intechstudio/grid/Preview/Electrical/FP-BU16-3D_blender_top.png

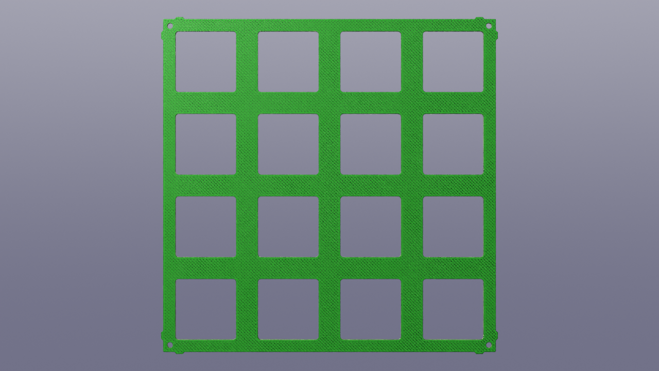
Preview/Electrical/FP-BU16-3D_blender_top.png
