intechstudio/grid/Preview/Electrical/FP-BU16-MIDIGRADE-3D_bottom.png

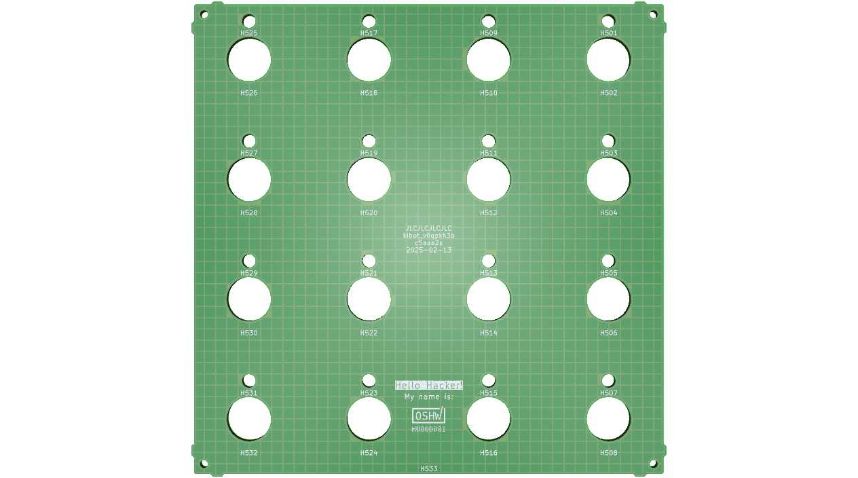
Preview/Electrical/FP-BU16-MIDIGRADE-3D_bottom.png
