intechstudio/grid/Preview/Electrical/FP-BU16-MIDIGRADE-3D_top.png

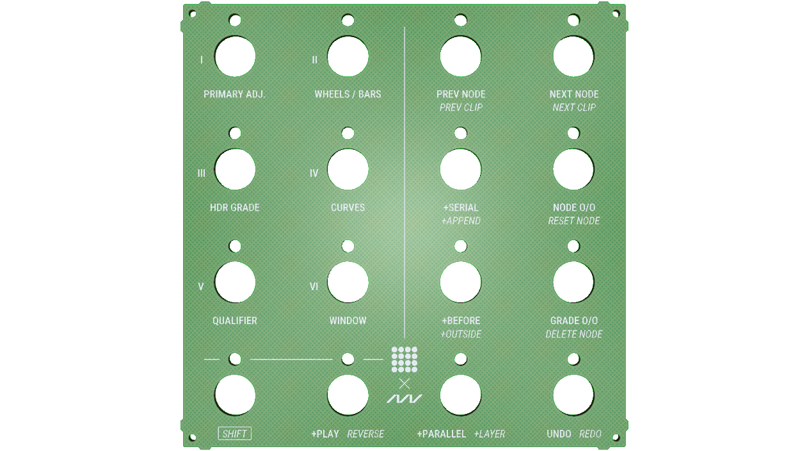
Preview/Electrical/FP-BU16-MIDIGRADE-3D_top.png
