intechstudio/grid/Preview/Electrical/FP-EN16-MIDIGRADE-3D_blender_top.png

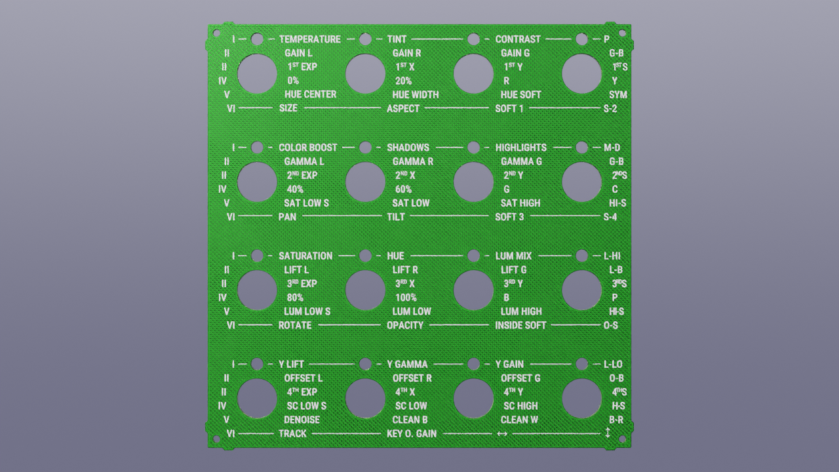
Preview/Electrical/FP-EN16-MIDIGRADE-3D_blender_top.png
