intechstudio/grid/Preview/Electrical/FP-TEK2-3D_bottom.png

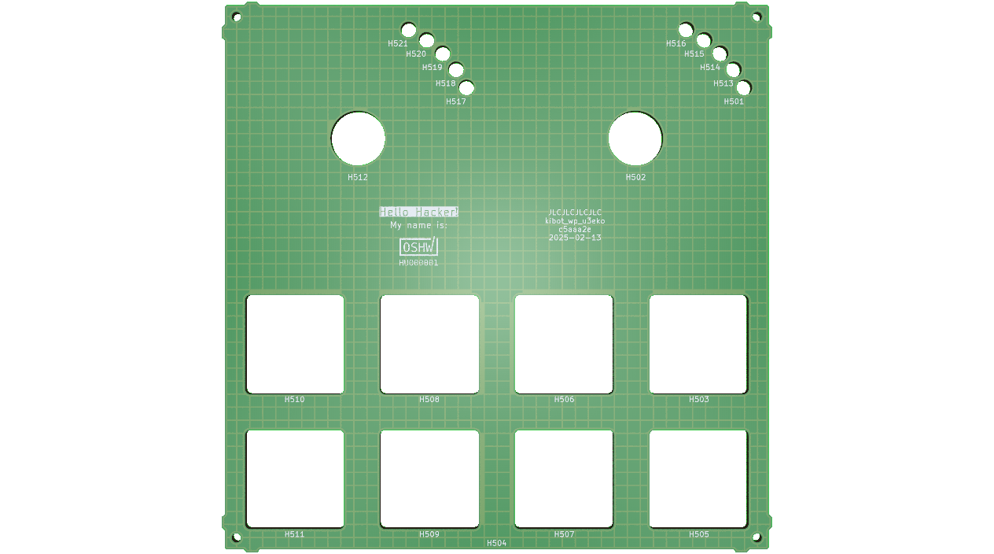
Preview/Electrical/FP-TEK2-3D_bottom.png
