intechstudio/grid/Preview/Electrical/FP-VSN1-3D_bottom.png

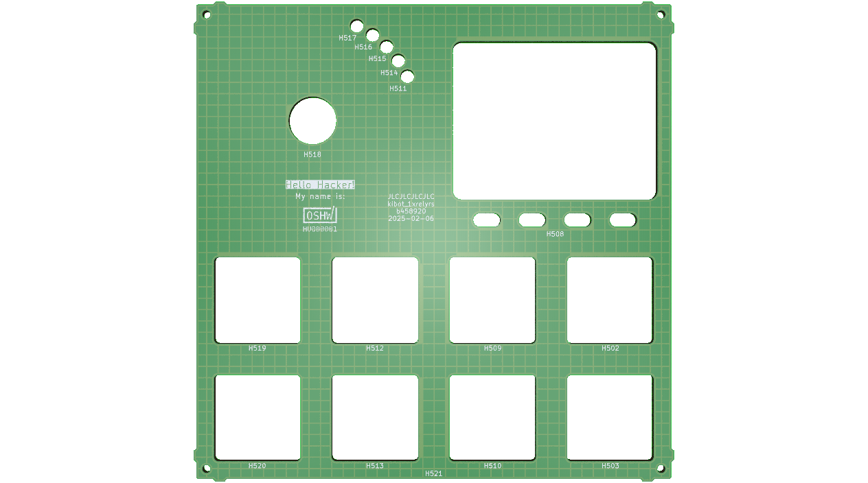
Preview/Electrical/FP-VSN1-3D_bottom.png
