intechstudio/grid/Preview/Electrical/FP-VSN1-3D_top.png

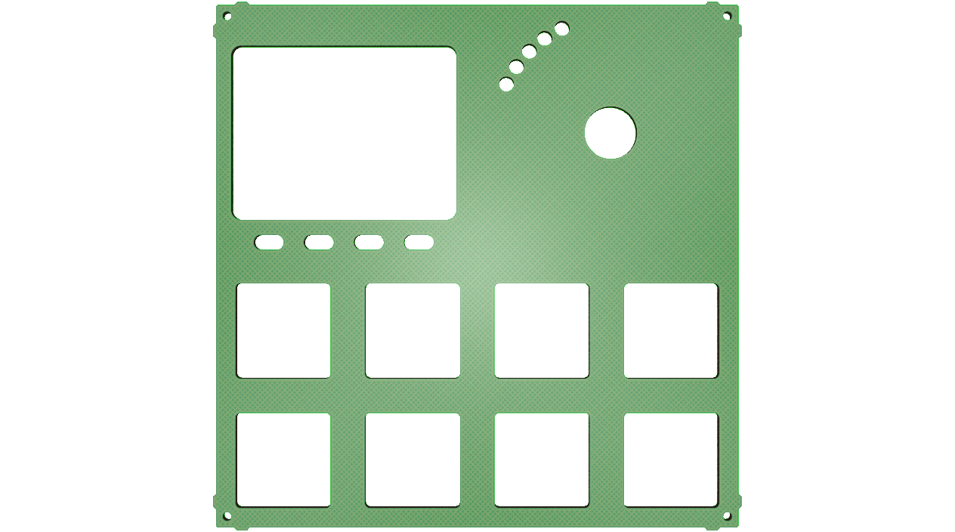
Preview/Electrical/FP-VSN1-3D_top.png
