intechstudio/grid/Preview/Electrical/FP-VSN1-R-3D_blender_top.png

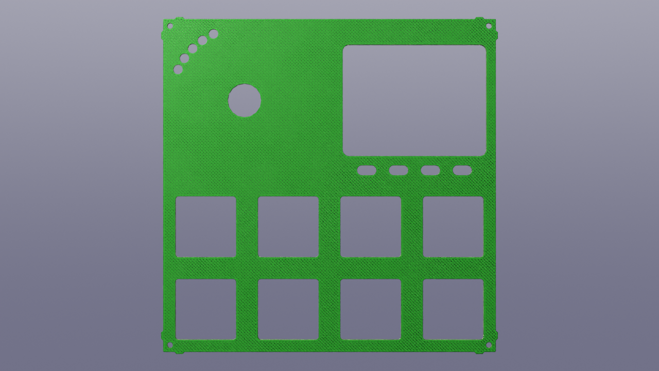
Preview/Electrical/FP-VSN1-R-3D_blender_top.png
