intechstudio/grid/Preview/Electrical/FP-VSN2-3D_bottom.png

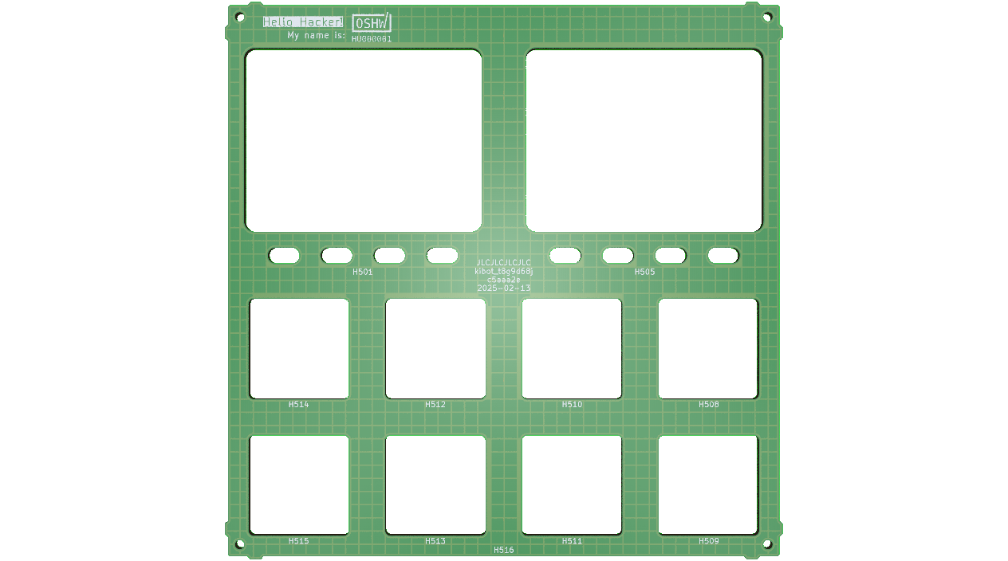
Preview/Electrical/FP-VSN2-3D_bottom.png
