intechstudio/grid/Preview/Electrical/PCBA-BU16-PLATE-3D_blender_top.png

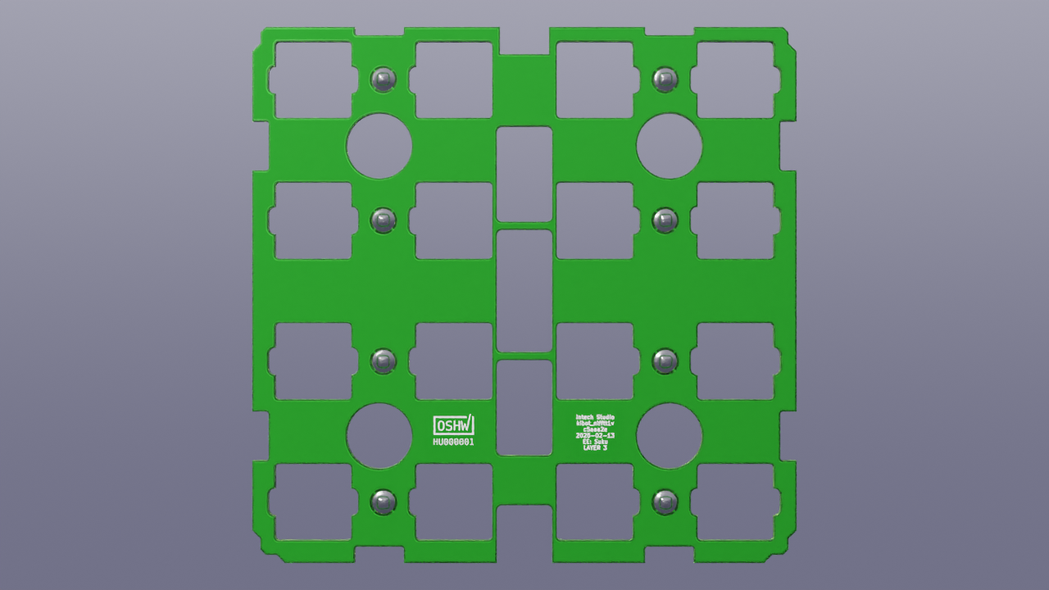
Preview/Electrical/PCBA-BU16-PLATE-3D_blender_top.png
