intechstudio/grid/Preview/Electrical/PCBA-BU16-PLATE-3D_bottom.png

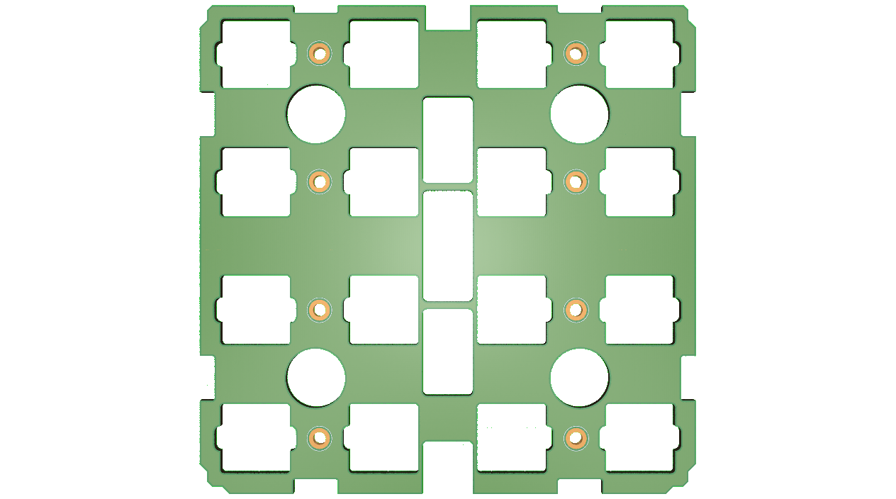
Preview/Electrical/PCBA-BU16-PLATE-3D_bottom.png
