intechstudio/grid/Preview/Electrical/PCBA-BU16-SPACER-3D_blender_top.png

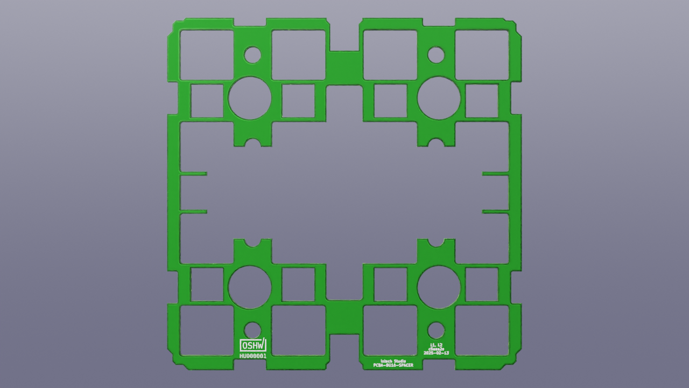
Preview/Electrical/PCBA-BU16-SPACER-3D_blender_top.png
