intechstudio/grid/Preview/Electrical/PCBA-EF44-3D_blender_top.png

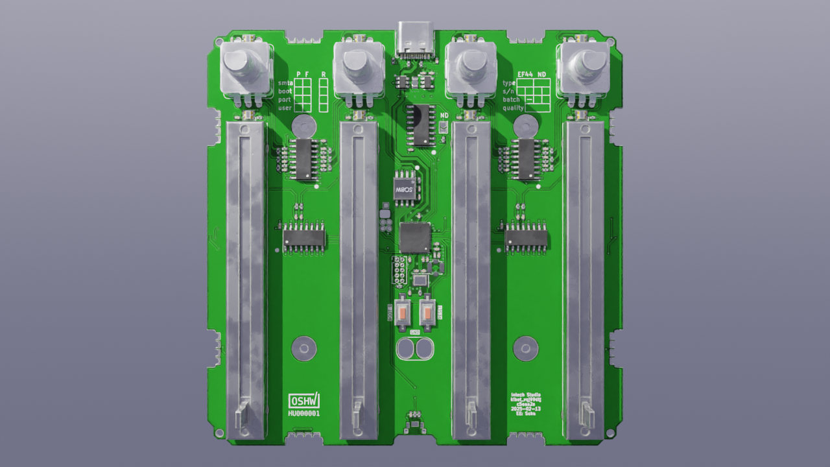
Preview/Electrical/PCBA-EF44-3D_blender_top.png
