intechstudio/grid/Preview/Electrical/PCBA-EF44-FRONTPANEL-3D_bottom.png

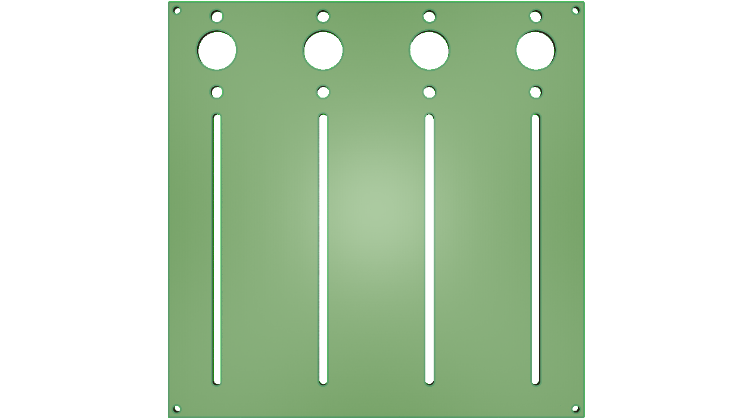
Preview/Electrical/PCBA-EF44-FRONTPANEL-3D_bottom.png
