intechstudio/grid/Preview/Electrical/PCBA-EN16-3D_blender_top.png

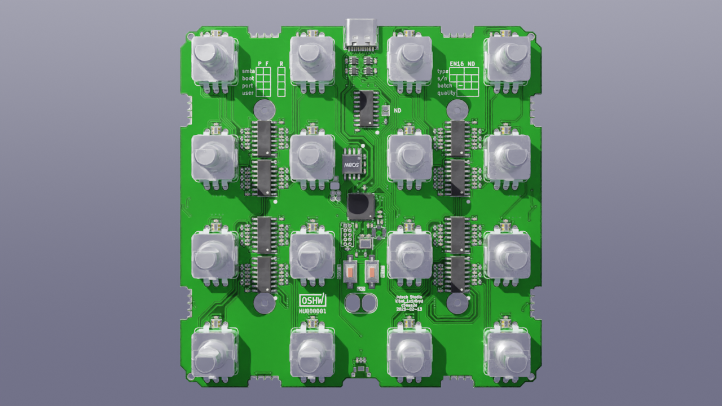
Preview/Electrical/PCBA-EN16-3D_blender_top.png
