intechstudio/grid/Preview/Electrical/PCBA-INTERFACE-3D_blender_top.png

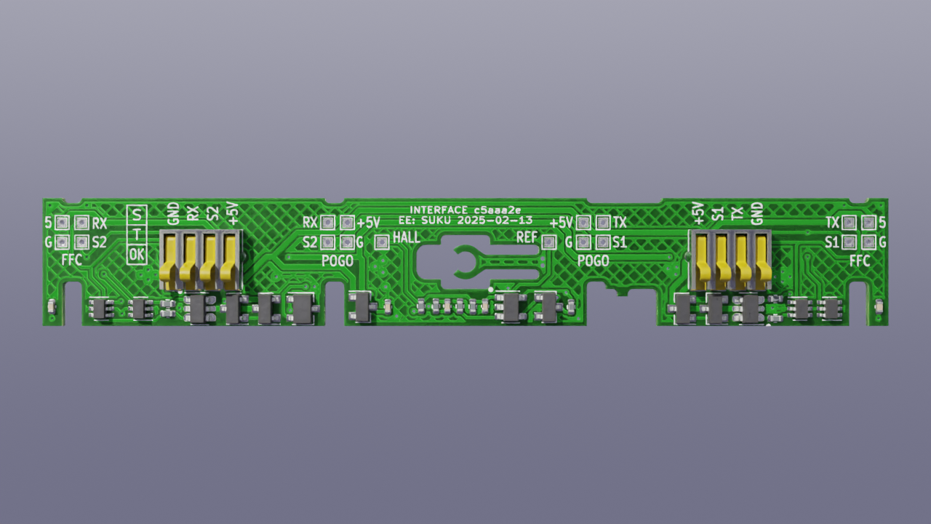
Preview/Electrical/PCBA-INTERFACE-3D_blender_top.png
