intechstudio/grid/Preview/Electrical/PCBA-PBF4-FRONTPANEL-3D_bottom.png

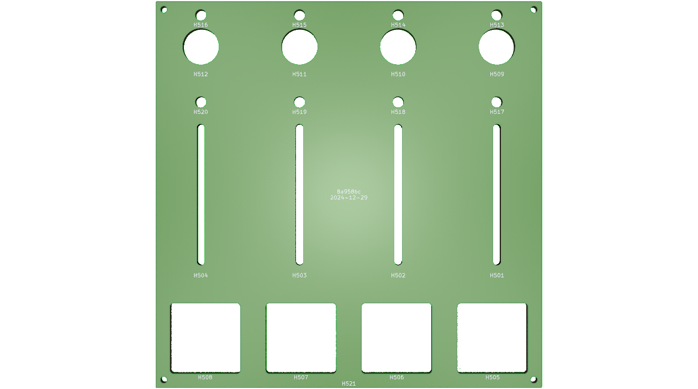
Preview/Electrical/PCBA-PBF4-FRONTPANEL-3D_bottom.png
