intechstudio/grid/Preview/Electrical/PCBA-PBF4-PLATE-3D_blender_top.png

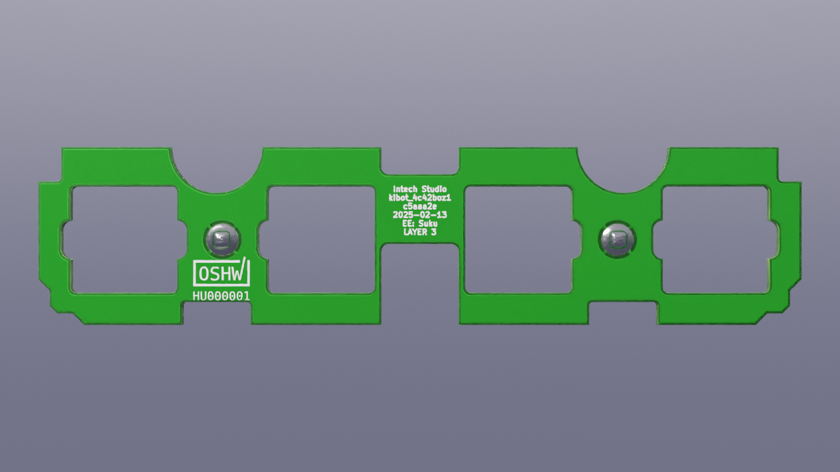
Preview/Electrical/PCBA-PBF4-PLATE-3D_blender_top.png
