intechstudio/grid/Preview/Electrical/PCBA-PBF4-PLATE-3D_bottom.png

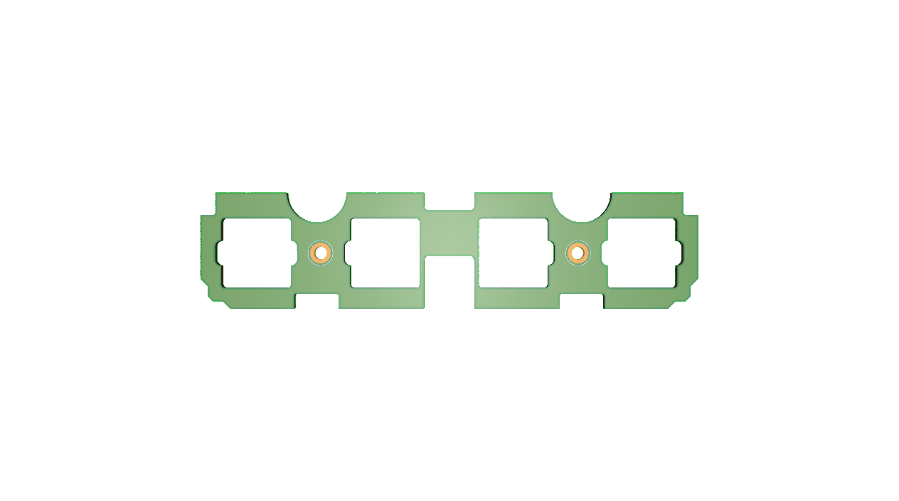
Preview/Electrical/PCBA-PBF4-PLATE-3D_bottom.png
