intechstudio/grid/Preview/Electrical/PCBA-PBF4-SPACER-3D_blender_top.png

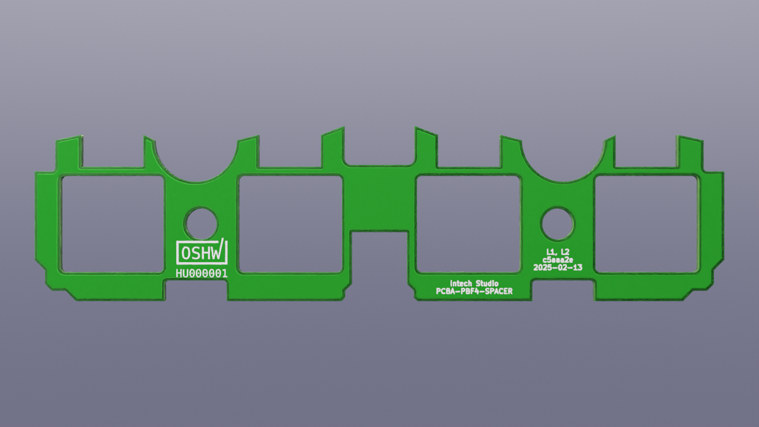
Preview/Electrical/PCBA-PBF4-SPACER-3D_blender_top.png
