intechstudio/grid/Preview/Electrical/PCBA-PBF4-SPACER-3D_bottom.png

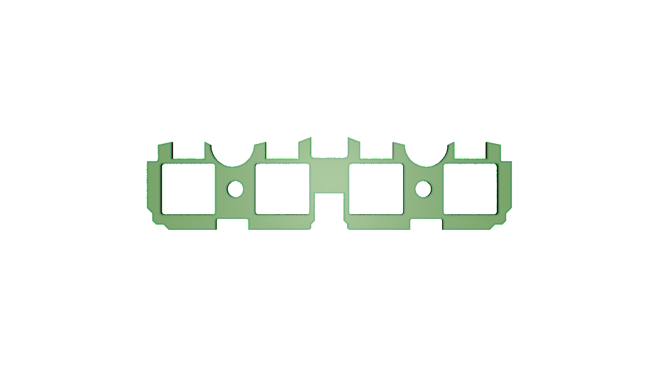
Preview/Electrical/PCBA-PBF4-SPACER-3D_bottom.png
