intechstudio/grid/Preview/Electrical/PCBA-PO16-3D_blender_top.png

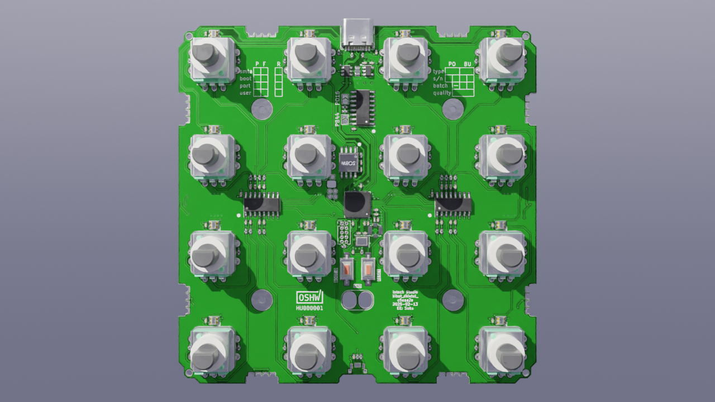
Preview/Electrical/PCBA-PO16-3D_blender_top.png
