intechstudio/grid/Preview/Electrical/PCBA-TEK2-3D_blender_top.png

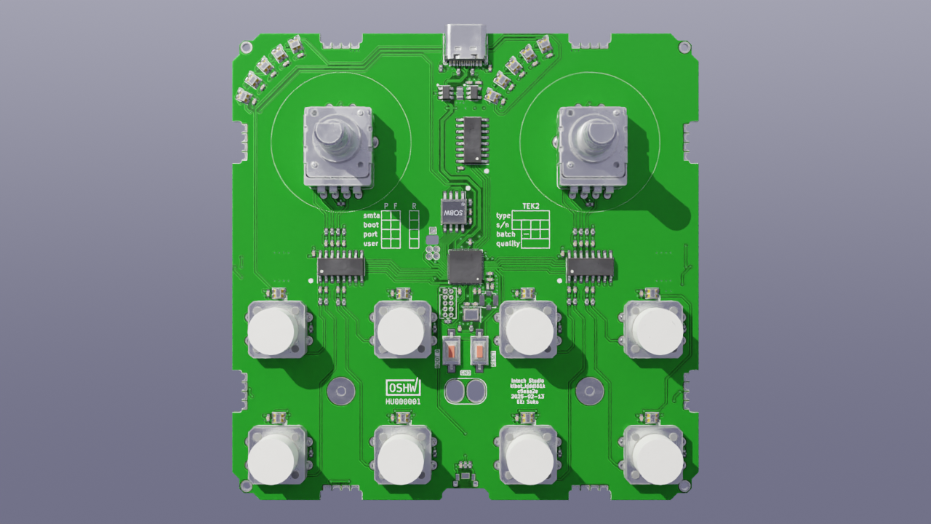
Preview/Electrical/PCBA-TEK2-3D_blender_top.png
