intechstudio/grid/Preview/Electrical/PCBA-VSN2-FRONTPANEL-3D_blender_top.png

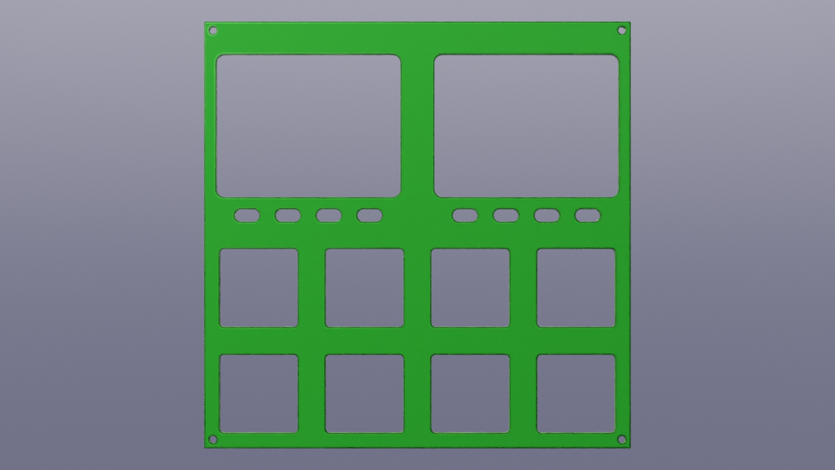
Preview/Electrical/PCBA-VSN2-FRONTPANEL-3D_blender_top.png
