intechstudio/grid/Preview/Electrical/PCBA-VSNX-3D_bottom.png

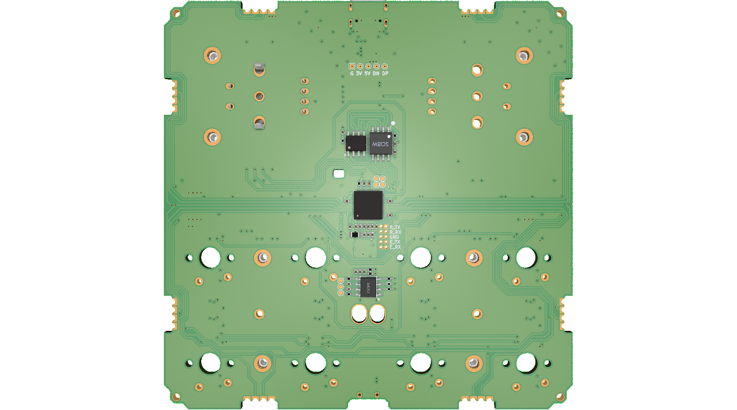
Preview/Electrical/PCBA-VSNX-3D_bottom.png
