intechstudio/grid/Preview/Electrical/PCBA-VSNX-BTNGROUP-3D_blender_top.png

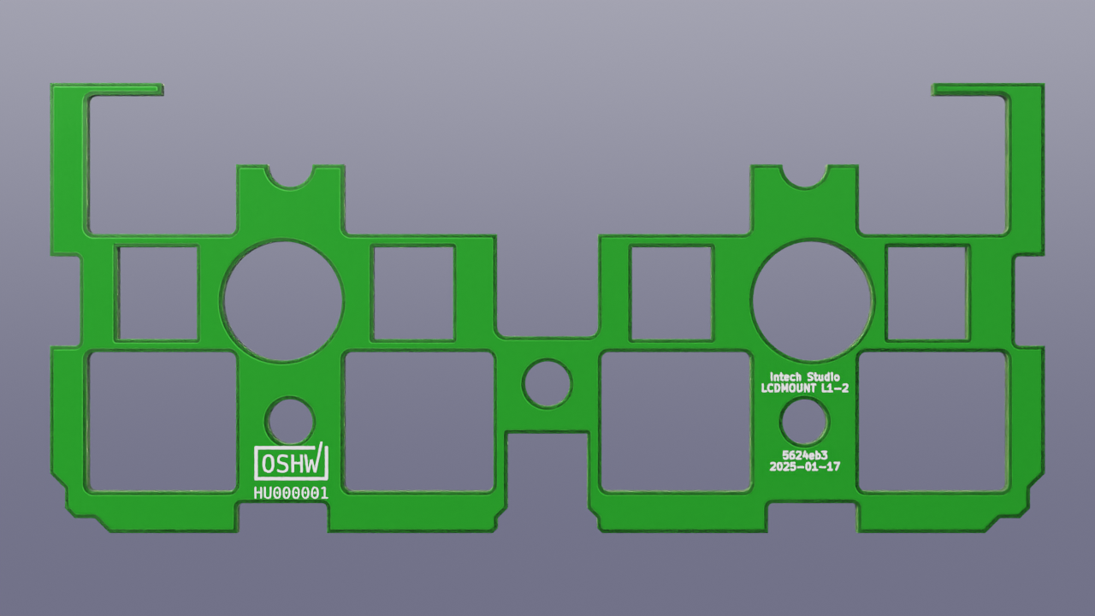
Preview/Electrical/PCBA-VSNX-BTNGROUP-3D_blender_top.png
