intechstudio/grid/Preview/Electrical/PCBA-VSNX-BTNGROUP-3D_bottom.png

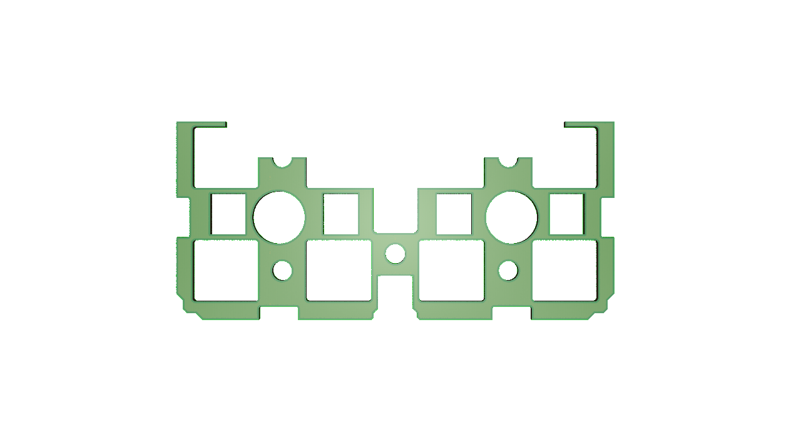
Preview/Electrical/PCBA-VSNX-BTNGROUP-3D_bottom.png
