intechstudio/grid/Preview/Electrical/PCBA-VSNX-LCDMOUNT-3D_blender_top.png

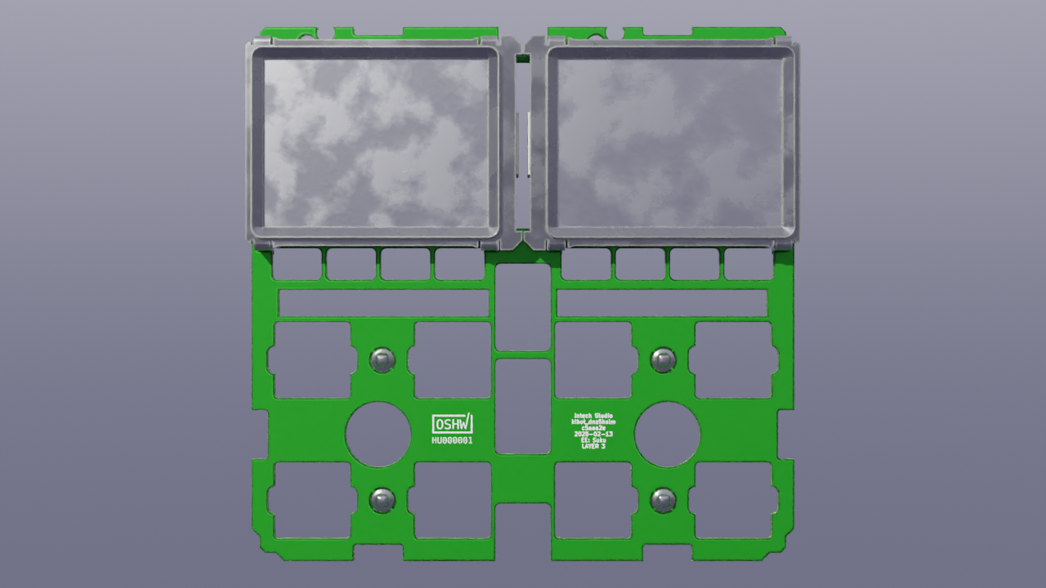
Preview/Electrical/PCBA-VSNX-LCDMOUNT-3D_blender_top.png
