intechstudio/grid/Preview/Electrical/PCBA-VSNX-LCDMOUNT-3D_bottom.png

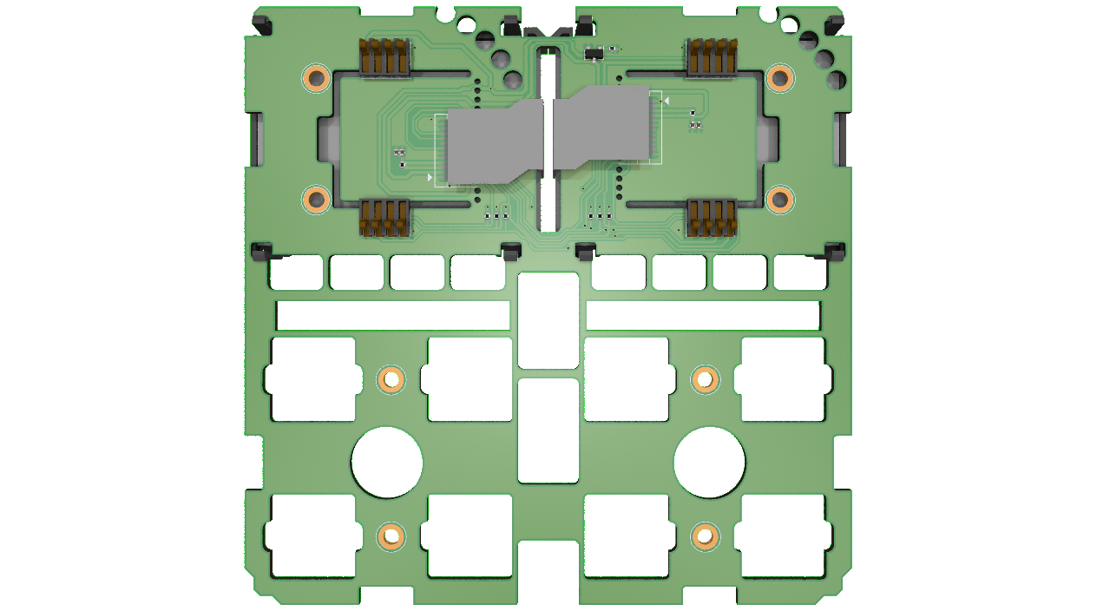
Preview/Electrical/PCBA-VSNX-LCDMOUNT-3D_bottom.png
