intechstudio/grid/Preview/Electrical/PCBA-VSNX-LCDMOUNT-3D_top.png

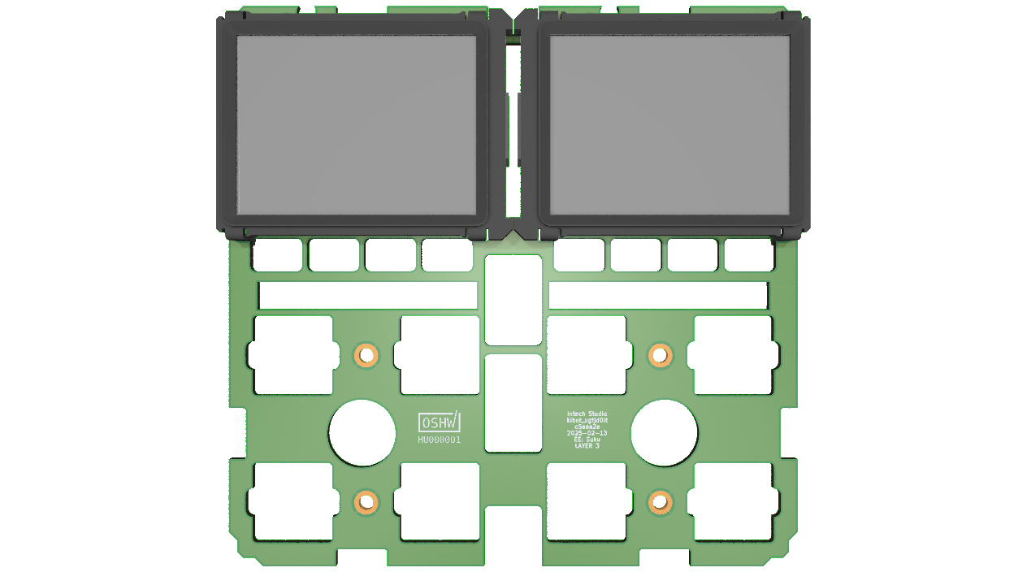
Preview/Electrical/PCBA-VSNX-LCDMOUNT-3D_top.png
