intechstudio/grid/Preview/Electrical/PCBA-VSNX-SPACER-3D_blender_top.png

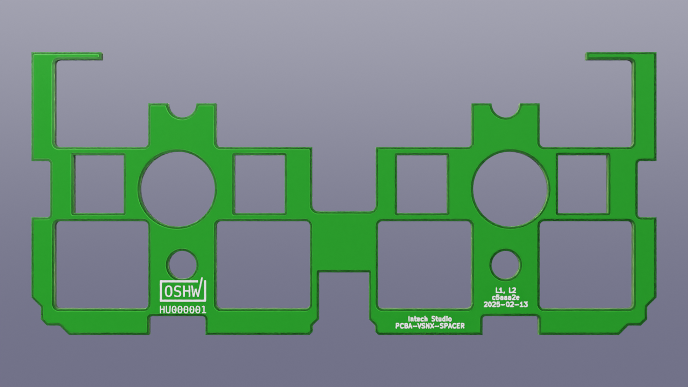
Preview/Electrical/PCBA-VSNX-SPACER-3D_blender_top.png
