intechstudio/grid/Preview/Electrical/PCBA-XX16-FRONTPANEL-3D_top.png

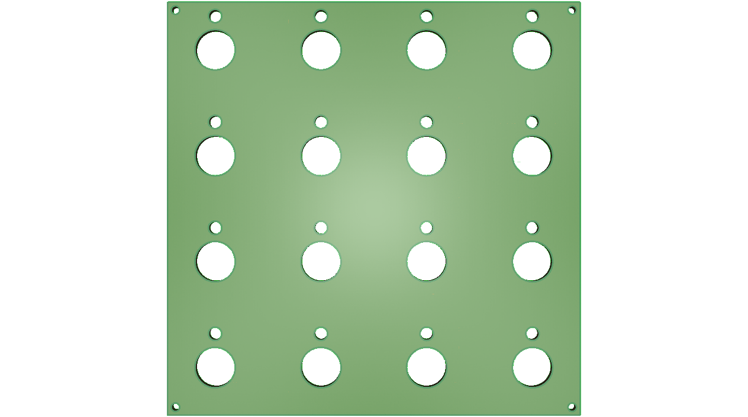
Preview/Electrical/PCBA-XX16-FRONTPANEL-3D_top.png
