intechstudio/grid/Preview/Mechanical/INSERT_TEK2.png

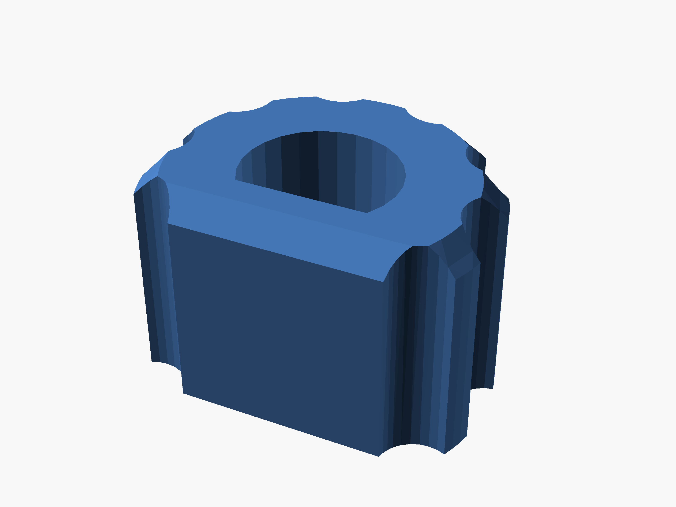
Preview/Mechanical/INSERT_TEK2.png
