intechstudio/grid/Preview/Mechanical/Part.png

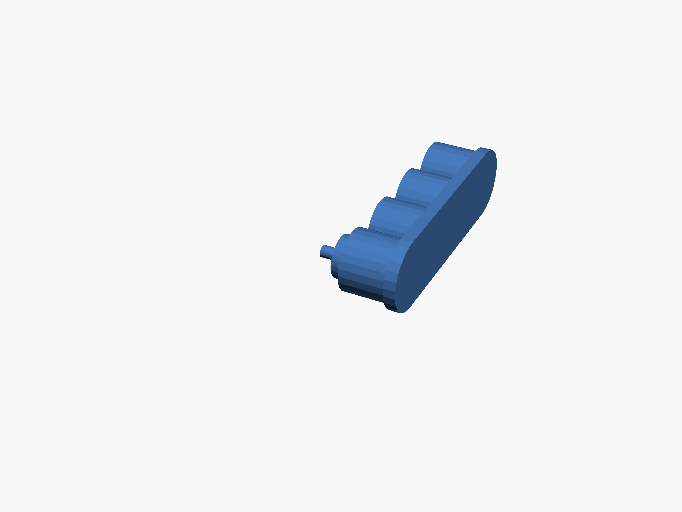
Preview/Mechanical/Part.png
