intechstudio/grid/Preview/Mechanical/Part_reverse.png

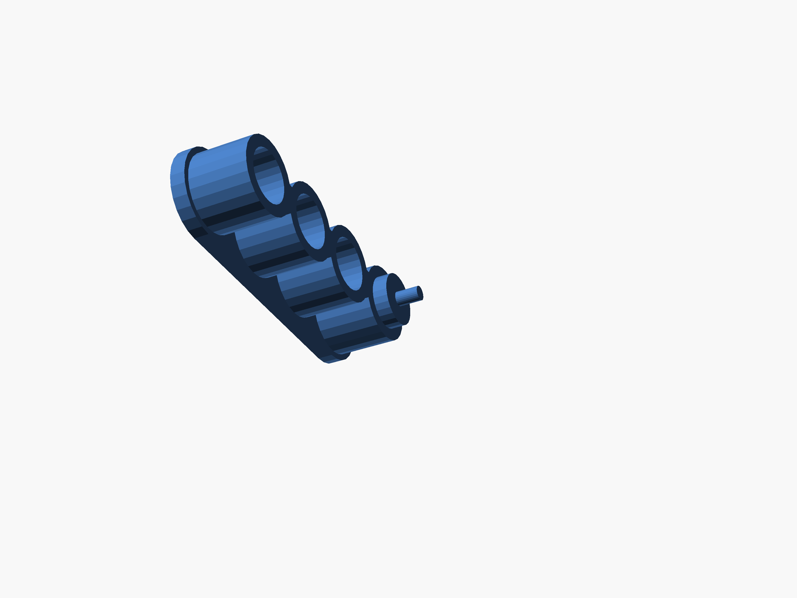
Preview/Mechanical/Part_reverse.png
