intechstudio/grid/Preview/Mechanical/PCBA-CONN-POGO.png

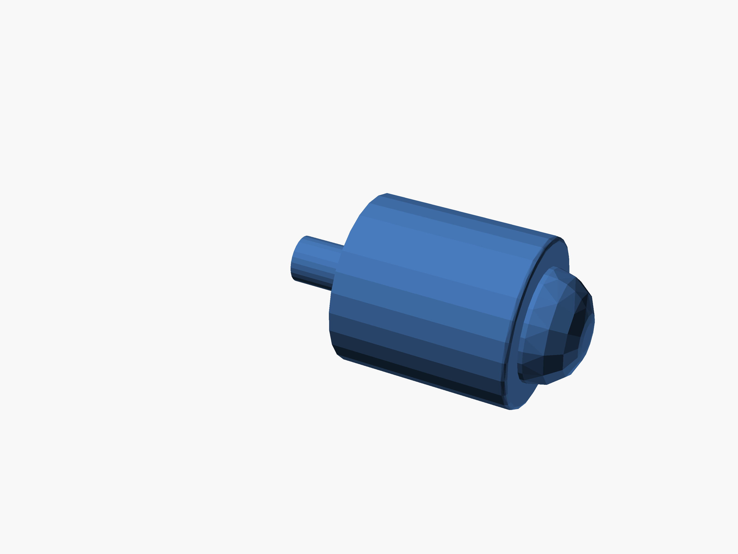
Preview/Mechanical/PCBA-CONN-POGO.png
