intechstudio/grid/Preview/Mechanical/PCBA-POT_reverse.png

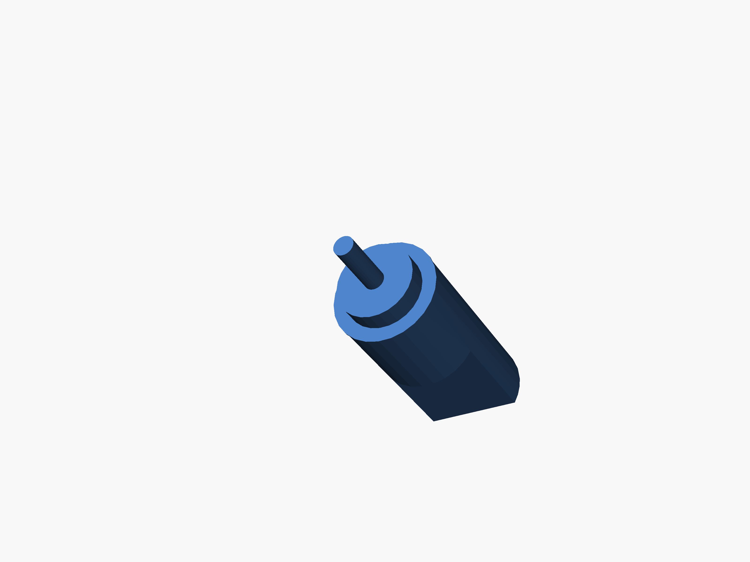
Preview/Mechanical/PCBA-POT_reverse.png
