intechstudio/grid/Preview/Mechanical/PLASTIC-MAGNET-CLIP.png

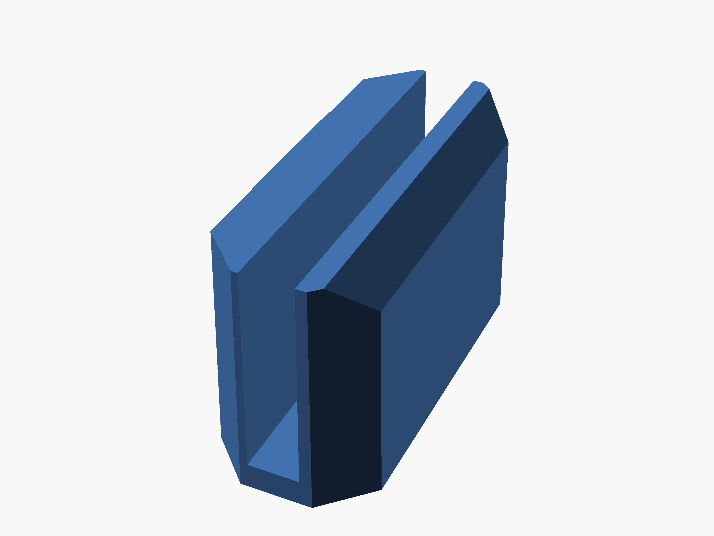
Preview/Mechanical/PLASTIC-MAGNET-CLIP.png
