intechstudio/grid/Preview/Mechanical/PLASTIC-MAGNET-COVER_reverse.png

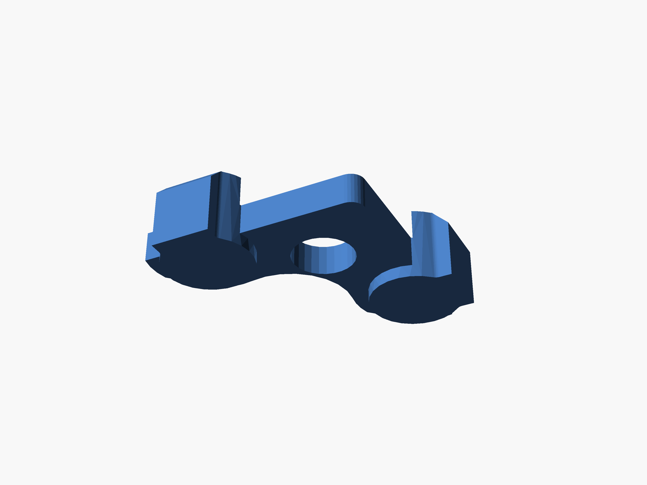
Preview/Mechanical/PLASTIC-MAGNET-COVER_reverse.png
