intechstudio/grid/Preview/Mechanical/PLASTIC-MAPMODE_reverse.png

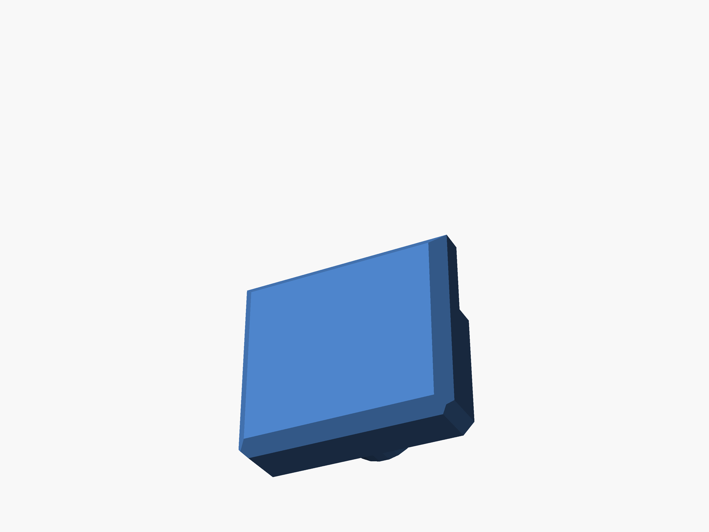
Preview/Mechanical/PLASTIC-MAPMODE_reverse.png
