intechstudio/grid/Preview/Mechanical/SPACER_reverse.png

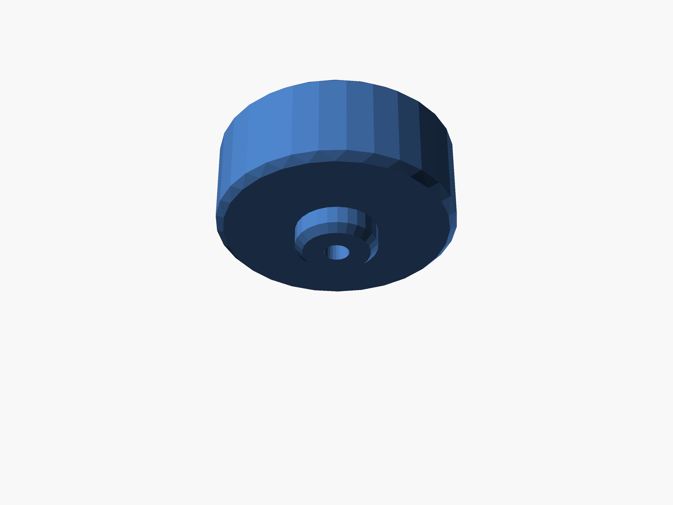
Preview/Mechanical/SPACER_reverse.png
