intechstudio/grid/Preview/Mechanical/¶}Ķ.png

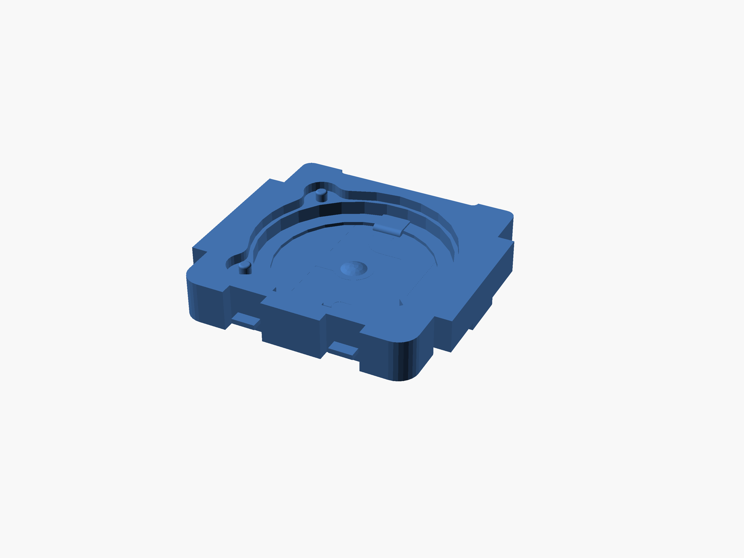
Preview/Mechanical/¶}Ķ.png
