intechstudio/grid/Preview/Mechanical/Body001.step

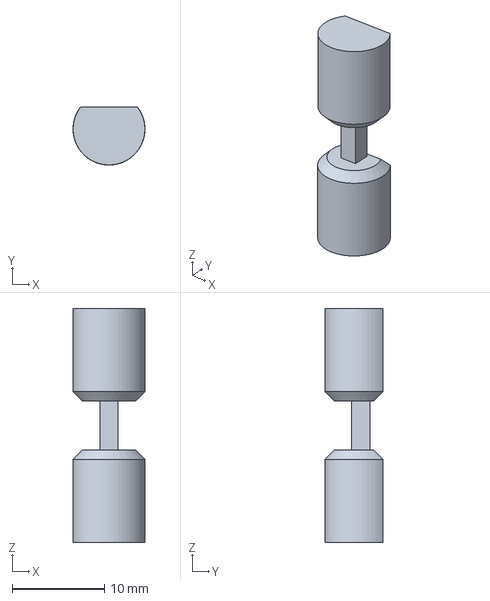
[picture p143: CAD file, 2025-02-10]
Preview/Mechanical/Body001.step
7.79 x 6.30 x 25.3 mm
