intechstudio/grid/Preview/Electrical/PCBA-INTERFACE-3D.step

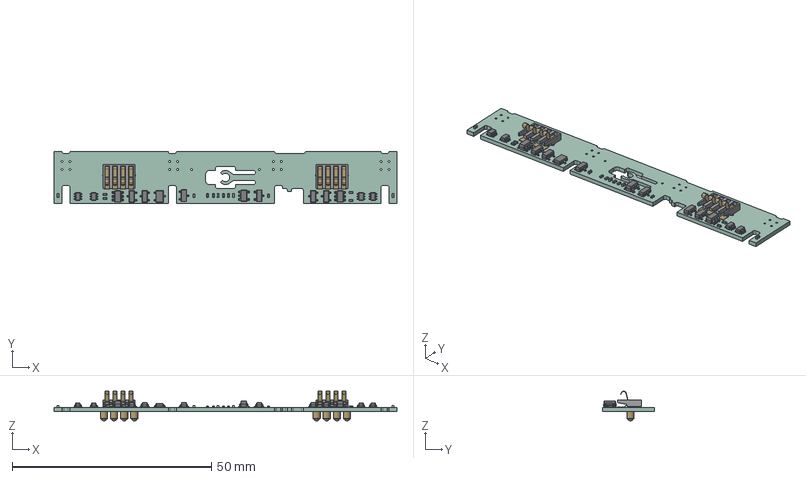
[picture p144: CAD file, 2025-02-13]
Preview/Electrical/PCBA-INTERFACE-3D.step
86.0 x 13.0 x 7.45 mm
C_0402_1005Metric x 5
R_0402_1005Metric x 9
SOT_23_6 x 2
SOT_363_SC_70_6 x 6
SOT_23 x 6
battery_spring x 2
SOT_23W
SOT_23_5
kibot_fe52ff96_PCB
