intechstudio/grid/Preview/Mechanical/Spring2.step

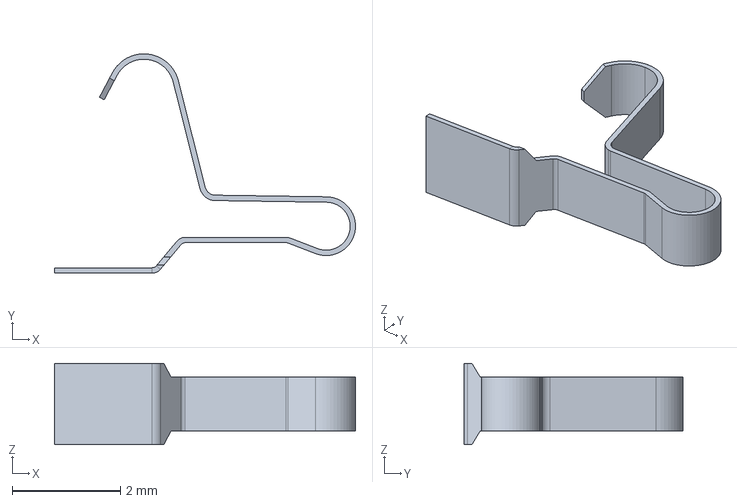
[picture p145: CAD file, 2025-02-10]
Preview/Mechanical/Spring2.step
5.56 x 4.05 x 1.50 mm
