intechstudio/grid/Preview/Electrical/PCBA-BU16-3D.step

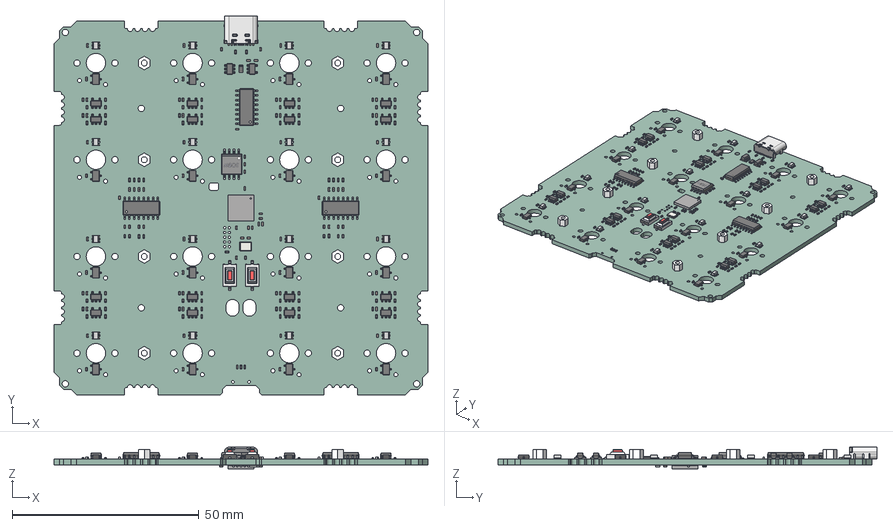
[picture p146: CAD file, 2025-02-13]
Preview/Electrical/PCBA-BU16-3D.step
100.0 x 101.4 x 5.81 mm
LEG003 x 16
LEG002 x 16
LEG x 16
LEG001 x 16
C_0402_1005Metric x 98
R_0402_1005Metric x 89
SOIC_16_39x99mm_P127mm x 3
User Library-SOIC8_Wide_5mmx5mm
ConPins
PcbPins
Mold
Frame
SOT_23_6
SOT_23W x 16
R_0805_2012Metric x 2
SOT_23_5 x 17
SW_SPST_CK_RS282G05A3 x 2
Crystal_SMD_Abracon_ABM8G-4Pin_3.2x2.5mm
QFN_56_1EP_7x7mm_P04mm_EP32x32mm x 2
L_0402_1005Metric
kibot_mzhbgm36_PCB
