intechstudio/grid/Preview/Mechanical/PCBA-FADER.step

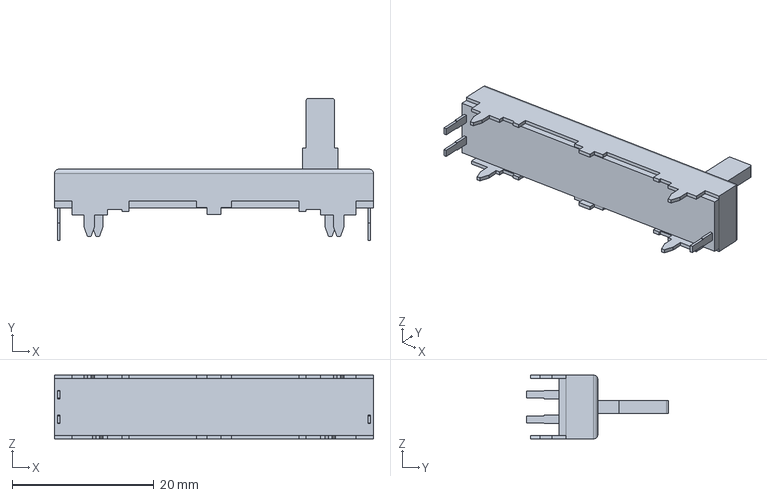
[picture p147: CAD file, 2025-02-10]
Preview/Mechanical/PCBA-FADER.step
45.0 x 20.1 x 9.00 mm
