intechstudio/grid/Preview/Mechanical/PLASTIC-SPACER_Printed.step

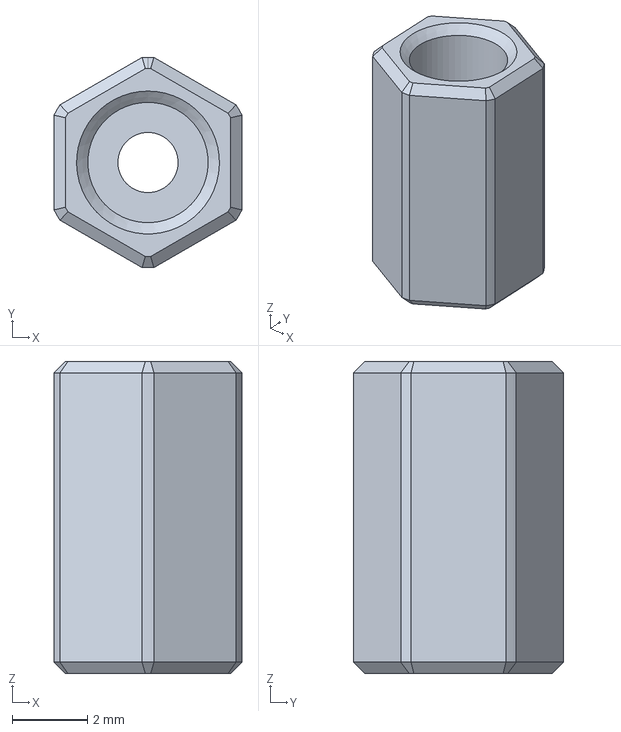
[picture p148: CAD file, 2025-02-10]
Preview/Mechanical/PLASTIC-SPACER_Printed.step
5.00 x 5.60 x 8.30 mm
