intechstudio/grid/Preview/Electrical/PCBA-VSNX-SPACER-3D.step

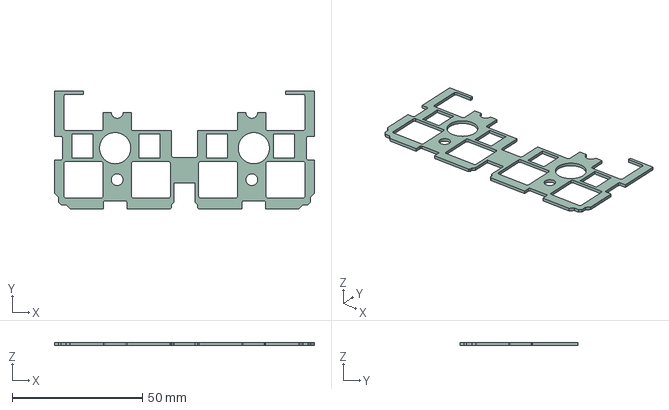
[picture p149: CAD file, 2025-02-13]
Preview/Electrical/PCBA-VSNX-SPACER-3D.step
100.0 x 45.2 x 1.20 mm
