intechstudio/grid/Preview/Mechanical/PCBA-CONN-BATTERY.step

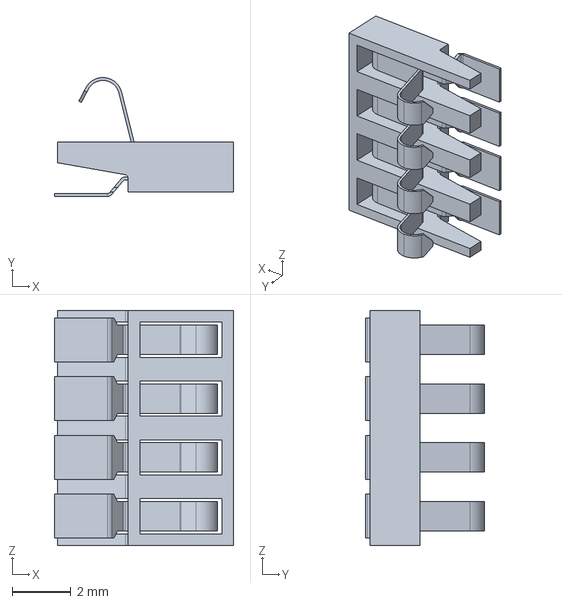
[picture p150: CAD file, 2025-02-10]
Preview/Mechanical/PCBA-CONN-BATTERY.step
6.10 x 4.05 x 8.00 mm
