intechstudio/grid/Preview/Electrical/FP-VSN1-R-3D.step

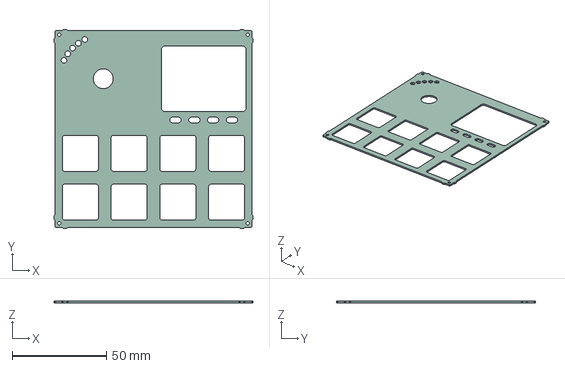
[picture p151: CAD file, 2025-02-13]
Preview/Electrical/FP-VSN1-R-3D.step
105.6 x 105.6 x 1.00 mm
