intechstudio/grid/Preview/Mechanical/feature_sticker.step

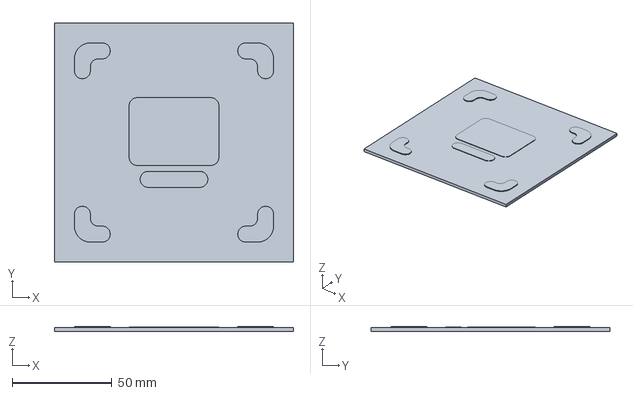
[picture p152: CAD file, 2025-02-10]
Preview/Mechanical/feature_sticker.step
120.0 x 120.0 x 2.50 mm
