intechstudio/grid/Preview/Mechanical/PLASTIC-KNOB-ENC.step

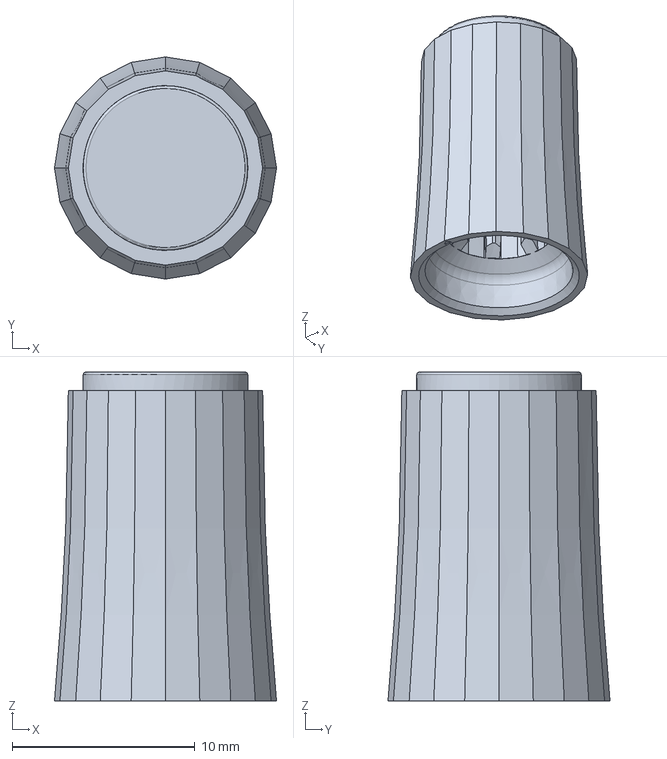
[picture p153: CAD file, 2025-02-10]
Preview/Mechanical/PLASTIC-KNOB-ENC.step
12.1 x 12.1 x 18.0 mm
