intechstudio/grid/Preview/Electrical/FP-PBF4-3D.step

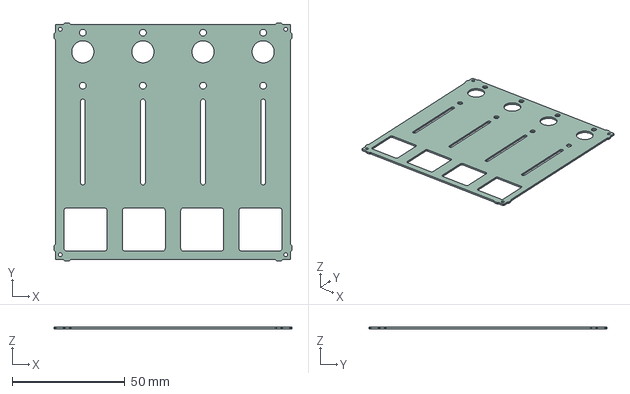
[picture p154: CAD file, 2025-02-13]
Preview/Electrical/FP-PBF4-3D.step
105.6 x 105.6 x 1.00 mm
