intechstudio/grid/Preview/Electrical/PCBA-PBF4-SPACER-3D.step

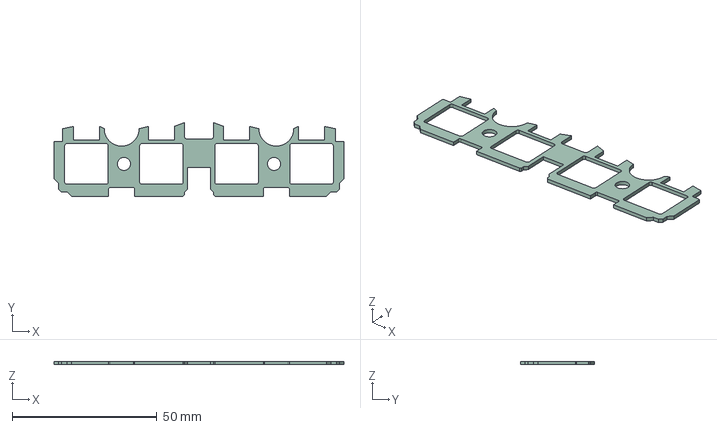
[picture p155: CAD file, 2025-02-13]
Preview/Electrical/PCBA-PBF4-SPACER-3D.step
100.0 x 25.4 x 1.20 mm
