intechstudio/grid/Preview/Mechanical/MAGNET-D3x13.step

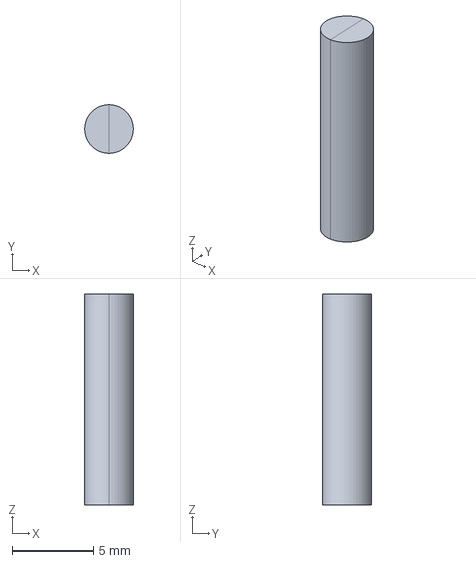
[picture p156: CAD file, 2025-02-10]
Preview/Mechanical/MAGNET-D3x13.step
3.00 x 3.00 x 13.0 mm
