intechstudio/grid/Preview/Mechanical/PLASTIC-TEK2-KNOB-INTERFACE.step

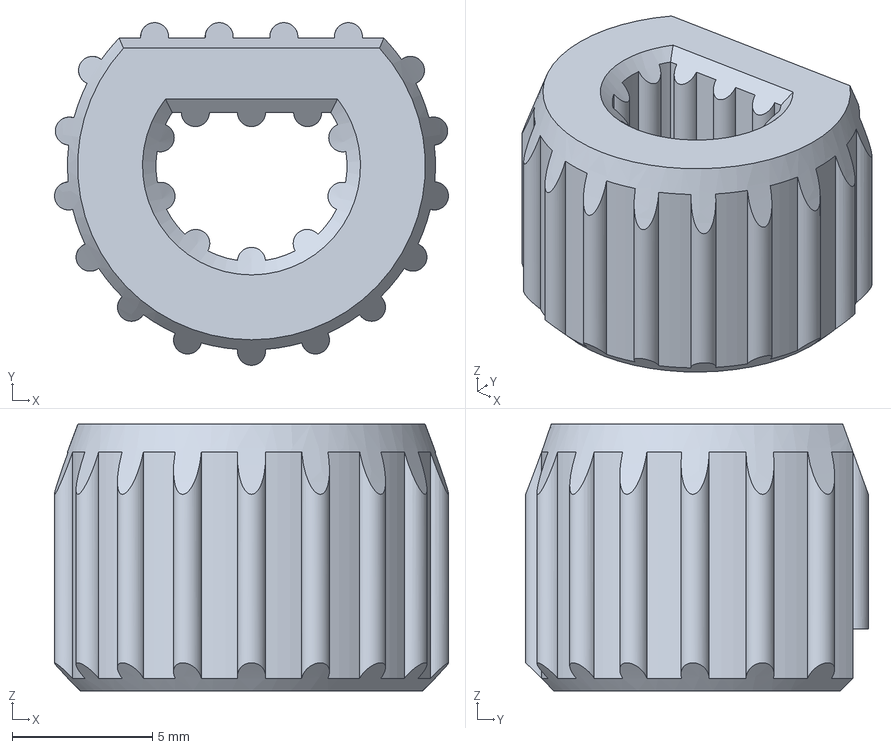
[picture p157: CAD file, 2025-02-10]
Preview/Mechanical/PLASTIC-TEK2-KNOB-INTERFACE.step
14.0 x 12.2 x 9.50 mm
