intechstudio/grid/Preview/Electrical/PCBA-BU16-SPACER-3D.step

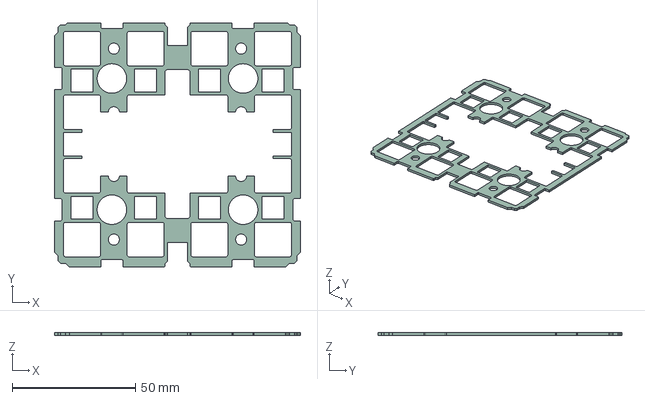
[picture p158: CAD file, 2025-02-13]
Preview/Electrical/PCBA-BU16-SPACER-3D.step
100.0 x 99.2 x 1.20 mm
