intechstudio/grid/Preview/Electrical/PCBA-PBF4-PLATE-3D.step

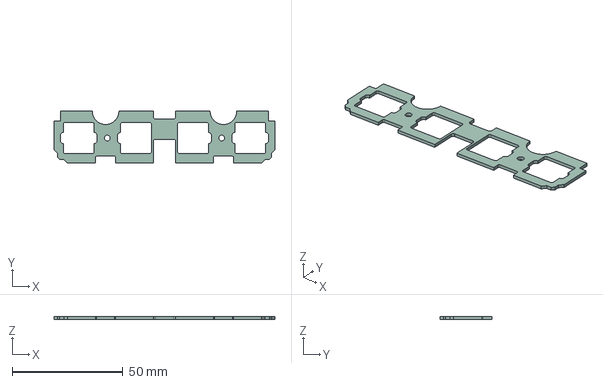
[picture p159: CAD file, 2025-02-13]
Preview/Electrical/PCBA-PBF4-PLATE-3D.step
100.0 x 23.3 x 1.20 mm
