intechstudio/grid/Preview/Mechanical/¶}Ķ.step

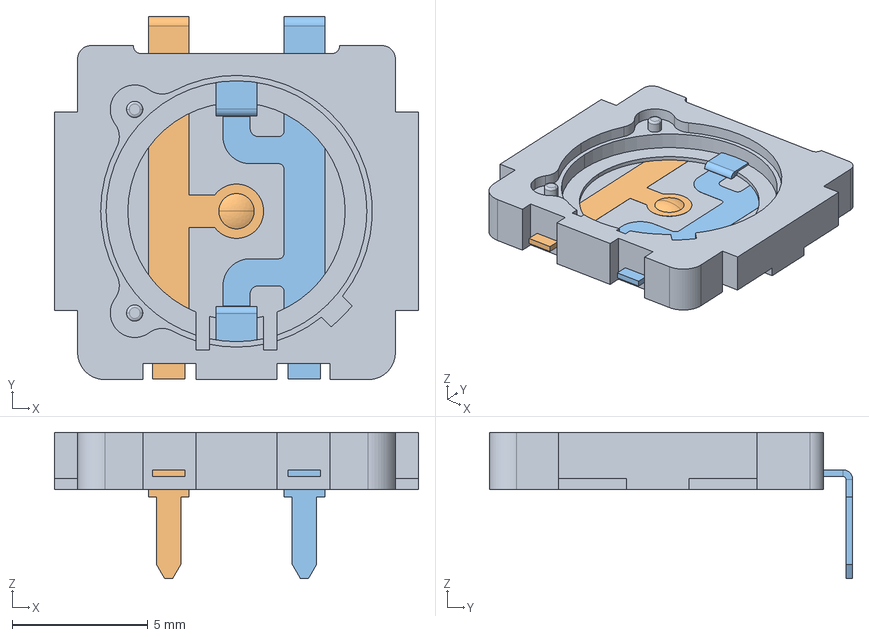
[picture p160: CAD file, 2025-02-10]
Preview/Mechanical/¶}Ķ.step
13.4 x 13.4 x 5.38 mm
