intechstudio/grid/Preview/Electrical/PCBA-EF44-3D.step

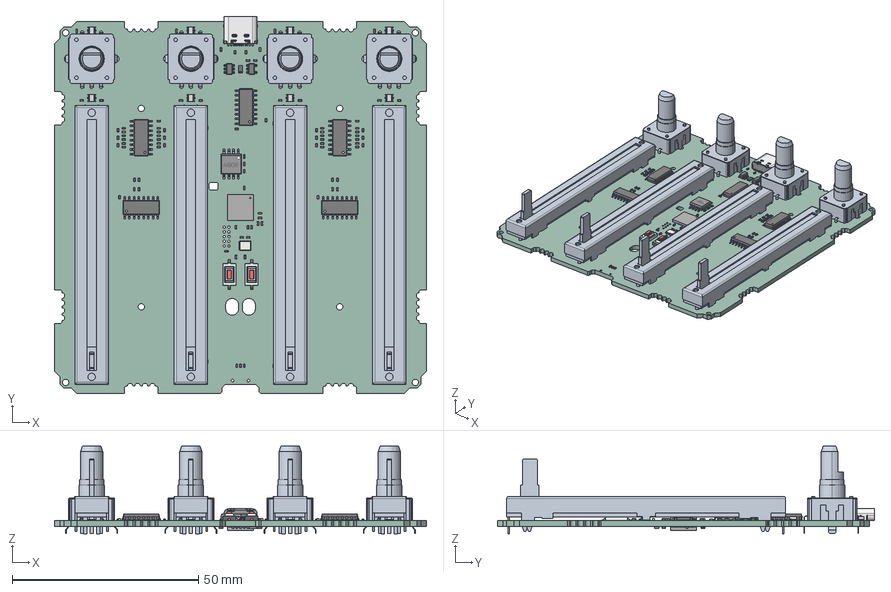
[picture p161: CAD file, 2025-02-11]
Preview/Electrical/PCBA-EF44-3D.step
100.0 x 101.4 x 23.6 mm
LEG003 x 8
LEG002 x 8
LEG x 8
LEG001 x 8
C_0402_1005Metric x 60
R_0402_1005Metric x 42
SOIC_16_39x99mm_P127mm x 5
ConPins
PcbPins
Mold
Frame
SOT_23_6
EN12-HS22AF20_ASM x 4
R_0805_2012Metric x 2
SW_SPST_CK_RS282G05A3 x 2
PS60-10MC1_ASM x 4
L_0402_1005Metric
User Library-SOIC8_Wide_5mmx5mm
Crystal_SMD_Abracon_ABM8G-4Pin_3.2x2.5mm
SOT_23_5
QFN_56_1EP_7x7mm_P04mm_EP32x32mm x 2
kibot_elxfesyo_PCB
