intechstudio/grid/Preview/Mechanical/PLASTIC-SPACER.step

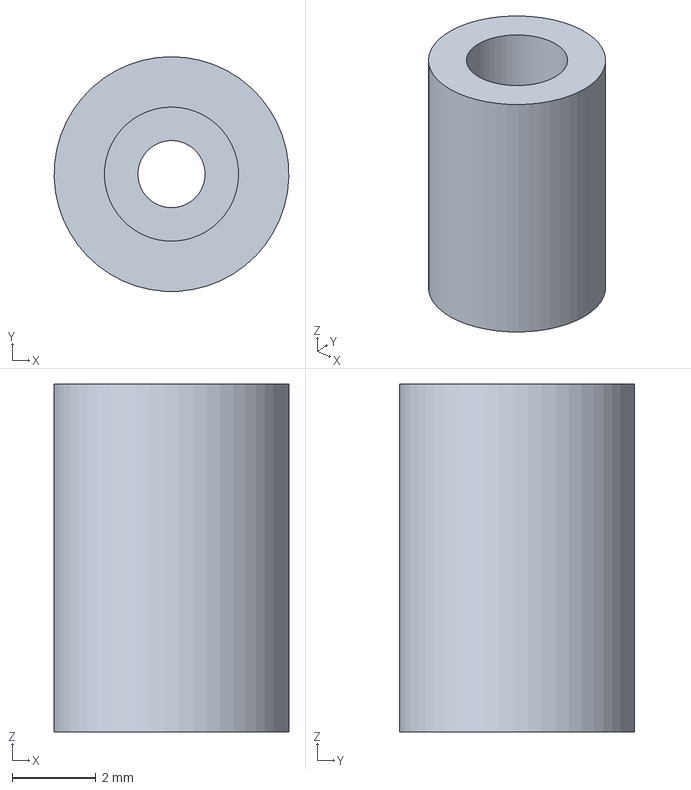
[picture p162: CAD file, 2025-02-10]
Preview/Mechanical/PLASTIC-SPACER.step
5.60 x 5.59 x 8.30 mm
