intechstudio/grid/Preview/Electrical/PCBA-EN16-3D.step

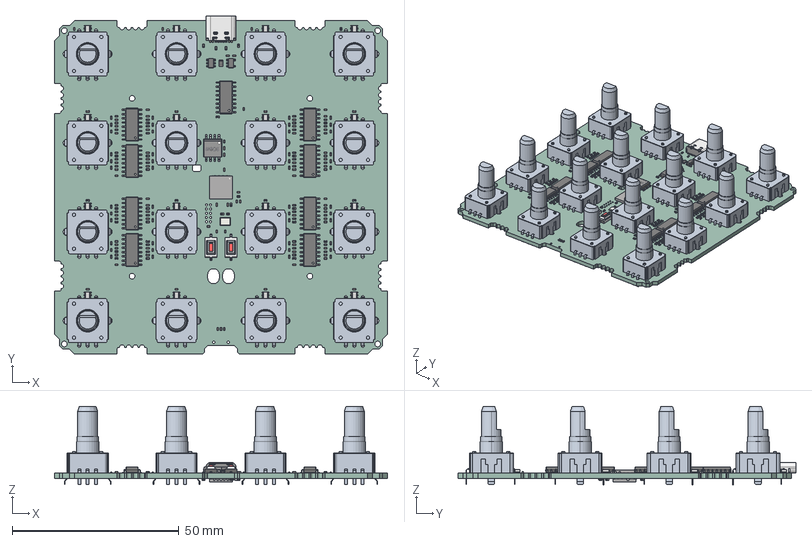
[picture p163: CAD file, 2025-02-11]
Preview/Electrical/PCBA-EN16-3D.step
100.0 x 101.4 x 23.5 mm
LEG003 x 16
LEG002 x 16
LEG x 16
LEG001 x 16
C_0402_1005Metric x 104
R_0402_1005Metric x 106
SOIC_16_39x99mm_P127mm x 9
ConPins
PcbPins
Mold
Frame
SOT_23_6
EN12-HS22AF20_ASM x 16
R_0805_2012Metric x 2
SW_SPST_CK_RS282G05A3 x 2
L_0402_1005Metric
SOT_23_5
User Library-SOIC8_Wide_5mmx5mm
Crystal_SMD_Abracon_ABM8G-4Pin_3.2x2.5mm
QFN_56_1EP_7x7mm_P04mm_EP32x32mm x 2
kibot_cd4q7zzx_PCB
