intechstudio/grid/Preview/Mechanical/Part.step

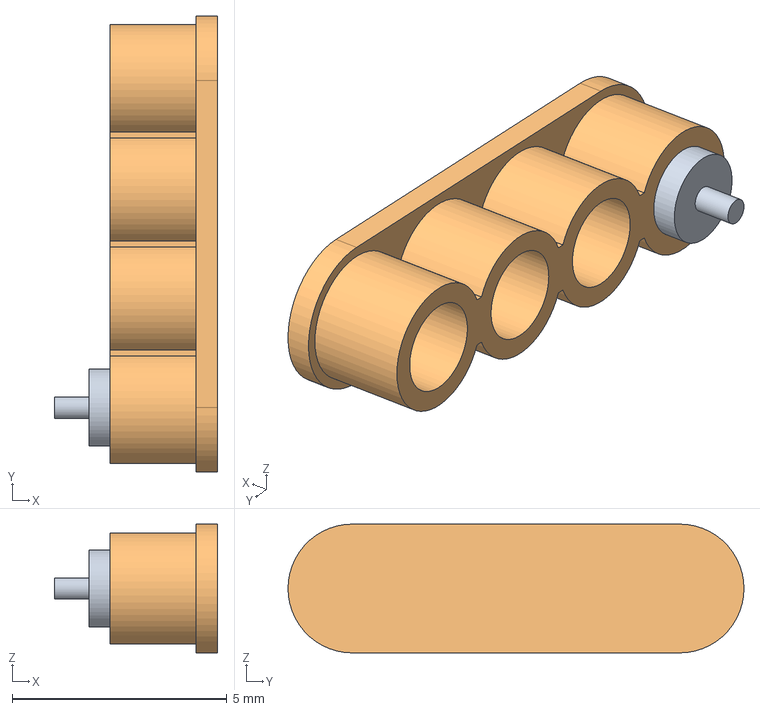
[picture p164: CAD file, 2025-02-10]
Preview/Mechanical/Part.step
3.80 x 10.6 x 3.00 mm
