intechstudio/grid/Preview/Mechanical/PLASTIC-BUSHING-POT_Injection molded.step

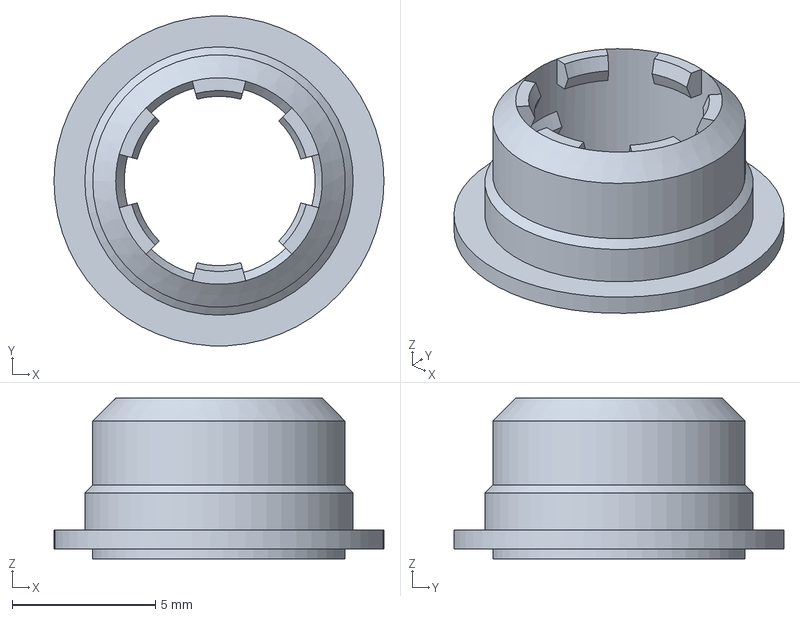
[picture p165: CAD file, 2025-02-10]
Preview/Mechanical/PLASTIC-BUSHING-POT_Injection molded.step
11.5 x 11.5 x 5.60 mm
