intechstudio/grid/Preview/Mechanical/PLASTIC-MAGNET-COVER.step

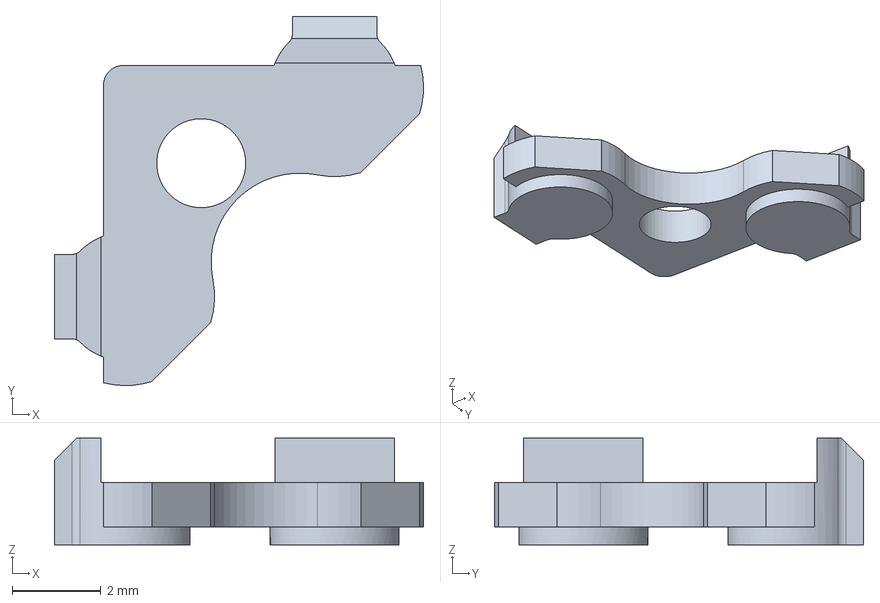
[picture p166: CAD file, 2025-02-10]
Preview/Mechanical/PLASTIC-MAGNET-COVER.step
8.30 x 8.30 x 2.40 mm
