intechstudio/grid/Preview/Electrical/PCBA-VSN1-FRONTPANEL-3D.step

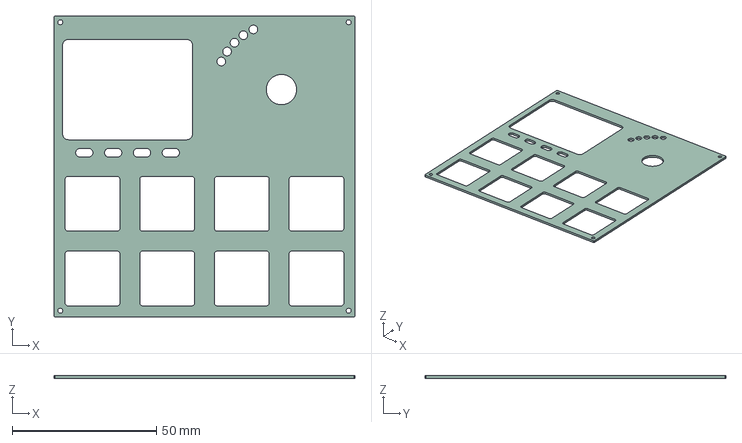
[picture p168: CAD file, 2024-12-29]
Preview/Electrical/PCBA-VSN1-FRONTPANEL-3D.step
104.3 x 104.3 x 1.00 mm
