intechstudio/grid/Preview/Electrical/PCBA-PBF4-FRONTPANEL-3D.step

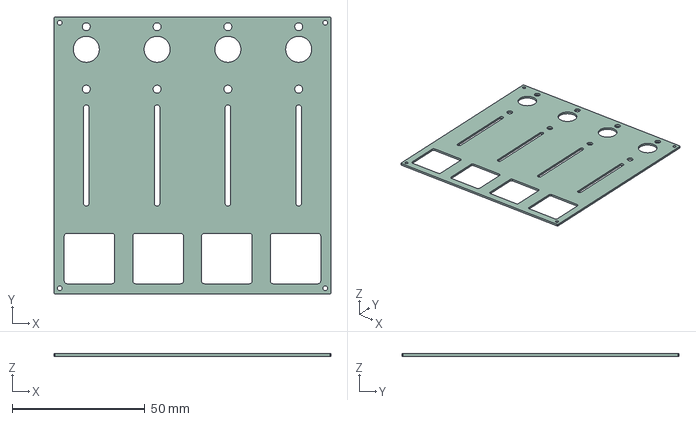
[picture p169: CAD file, 2024-12-29]
Preview/Electrical/PCBA-PBF4-FRONTPANEL-3D.step
104.3 x 104.3 x 1.00 mm
