intechstudio/grid/Preview/Mechanical/feature_subtract_cavity.step

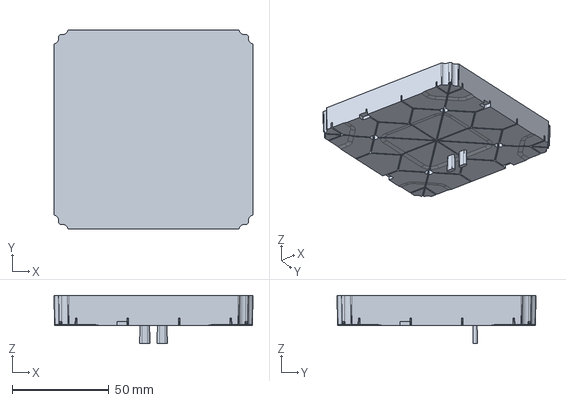
[picture p170: CAD file, 2025-02-10]
Preview/Mechanical/feature_subtract_cavity.step
102.8 x 102.8 x 25.0 mm
