intechstudio/grid/Preview/Electrical/PCBA-BU16-FRONTPANEL-3D.step

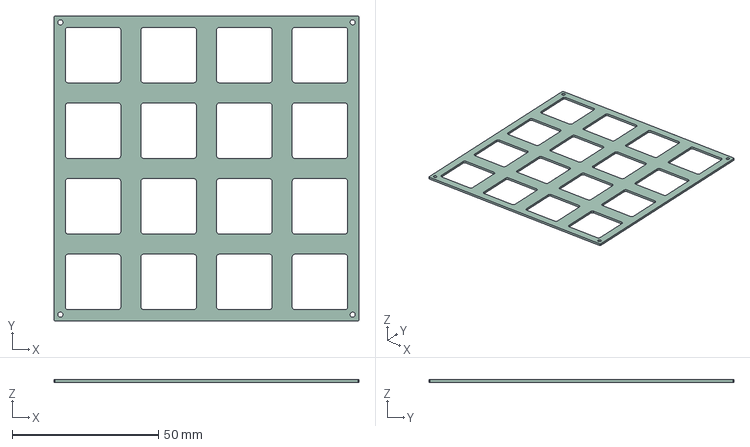
[picture p171: CAD file, 2024-12-29]
Preview/Electrical/PCBA-BU16-FRONTPANEL-3D.step
104.3 x 104.3 x 1.00 mm
