intechstudio/grid/Preview/Mechanical/MAGNET-SQ3.step

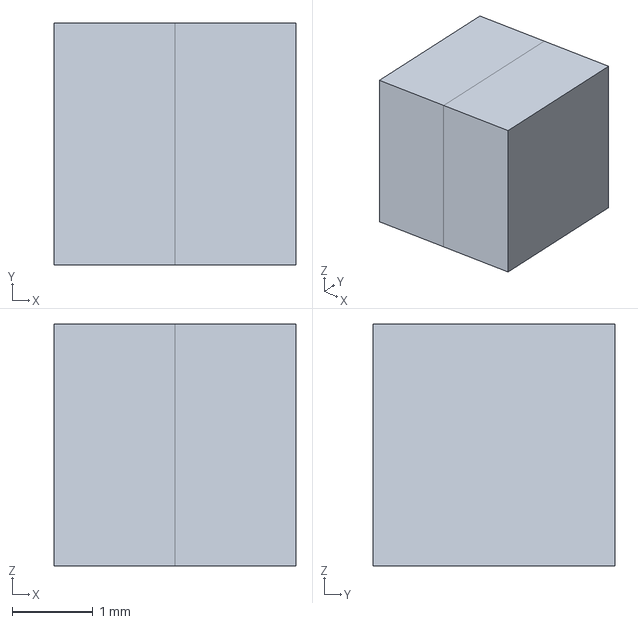
[picture p173: CAD file, 2025-02-10]
Preview/Mechanical/MAGNET-SQ3.step
3.00 x 3.00 x 3.00 mm
