intechstudio/grid/Preview/Electrical/PCBA-VSN2-FRONTPANEL-3D.step

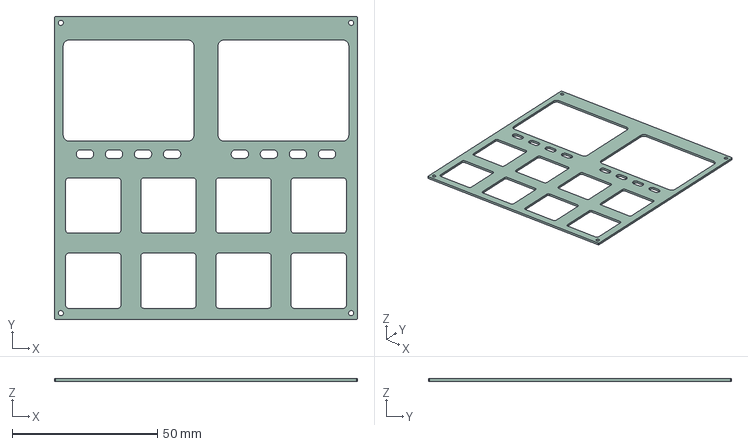
[picture p174: CAD file, 2024-12-29]
Preview/Electrical/PCBA-VSN2-FRONTPANEL-3D.step
104.3 x 104.3 x 1.00 mm
