intechstudio/grid/Preview/Mechanical/PLASTIC-LIGHTPIPE-ISOLATOR.step

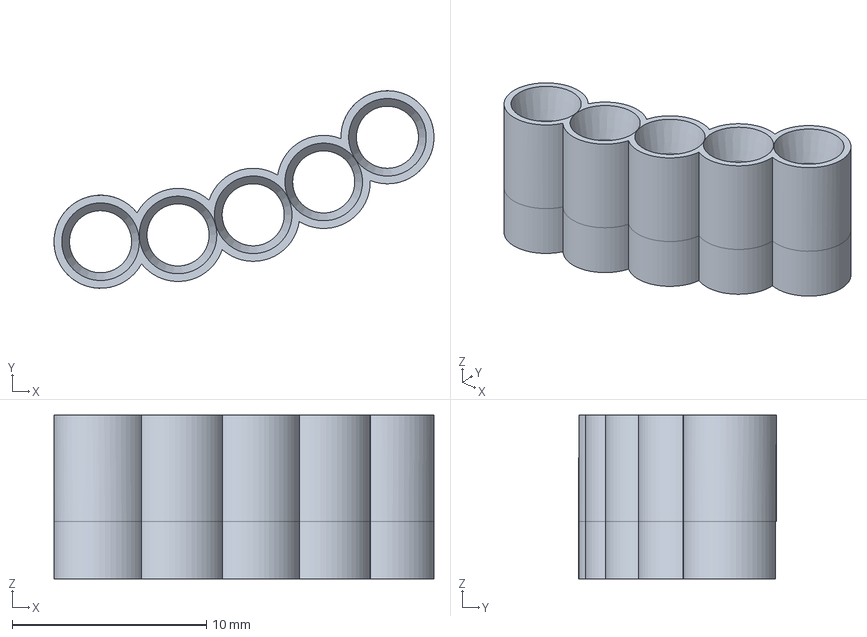
[picture p175: CAD file, 2025-02-10]
Preview/Mechanical/PLASTIC-LIGHTPIPE-ISOLATOR.step
19.6 x 10.2 x 8.45 mm
