intechstudio/grid/Preview/Mechanical/INSERT-M1.6x2.5x4.step

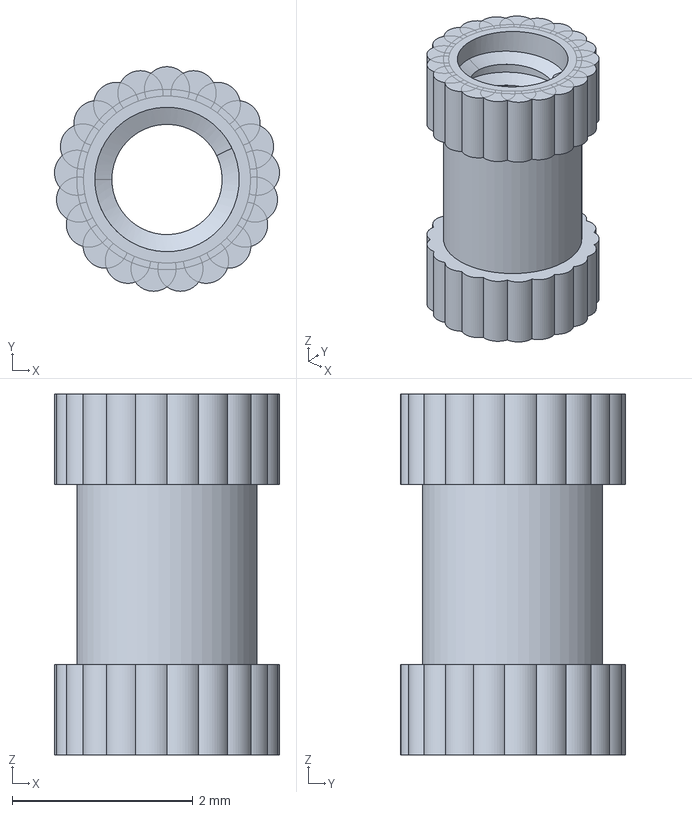
[picture p176: CAD file, 2025-02-10]
Preview/Mechanical/INSERT-M1.6x2.5x4.step
2.49 x 2.49 x 4.00 mm
