intechstudio/grid/Preview/Electrical/PCBA-TEK1-BTNGROUP-3D.step

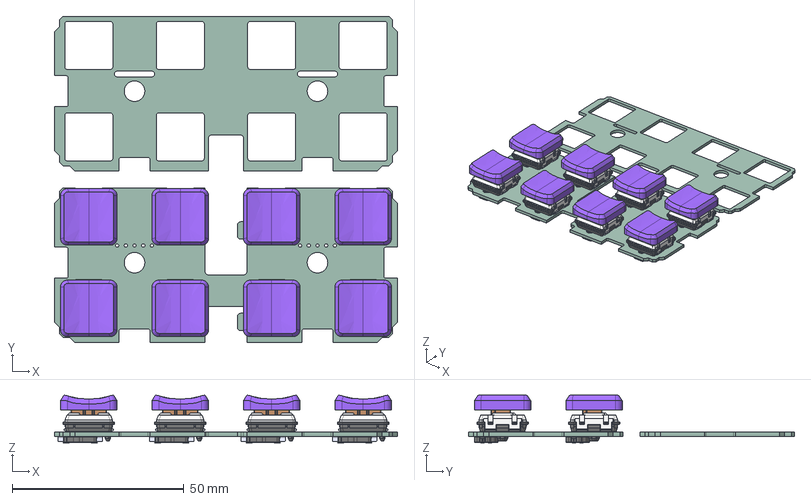
[picture p178: CAD file, 2024-07-29]
Preview/Electrical/PCBA-TEK1-BTNGROUP-3D.step
100.0 x 95.2 x 13.9 mm
Document009 x 8
PG1350 x 8
kibot_rvdpdqki_PCB_1
kibot_rvdpdqki_PCB_2
