intechstudio/grid/Preview/Mechanical/INSERT-FADER.step

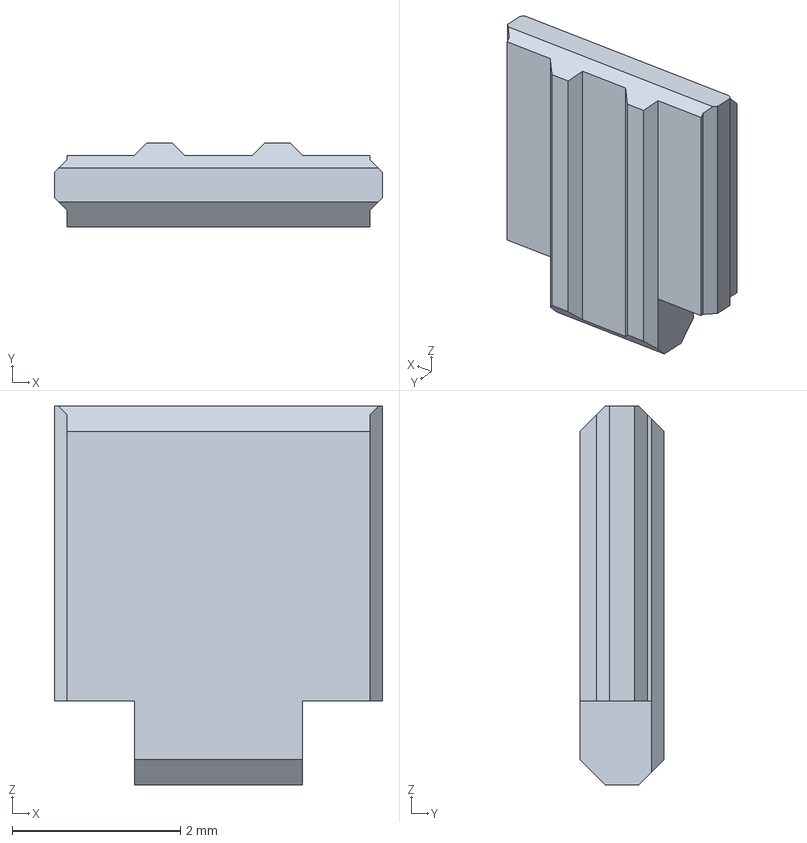
[picture p179: CAD file, 2025-02-10]
Preview/Mechanical/INSERT-FADER.step
3.90 x 1.00 x 4.50 mm
