intechstudio/grid/Preview/Mechanical/PCBA-ENDLESSPOT.step

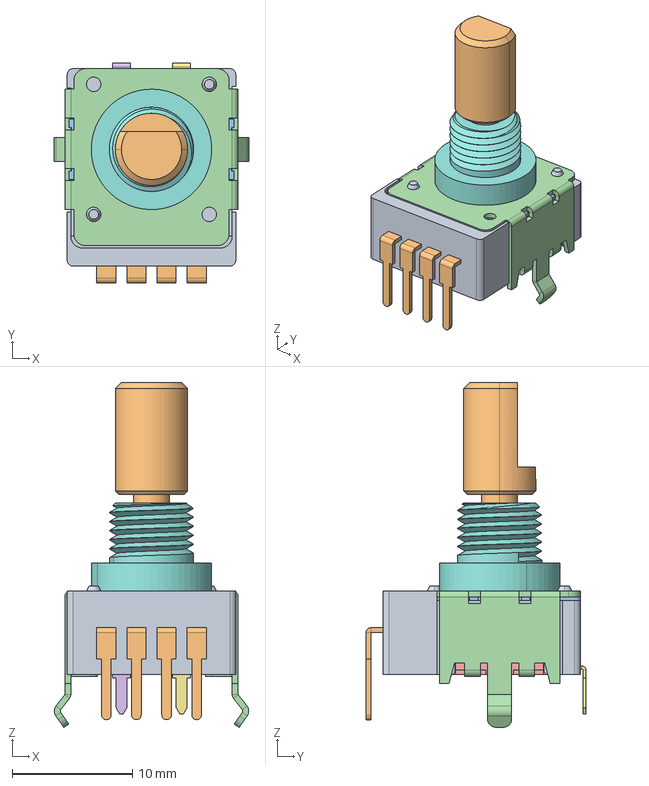
[picture p180: CAD file, 2025-02-10]
Preview/Mechanical/PCBA-ENDLESSPOT.step
16.1 x 18.3 x 28.6 mm
