intechstudio/grid/Preview/Mechanical/Base.step

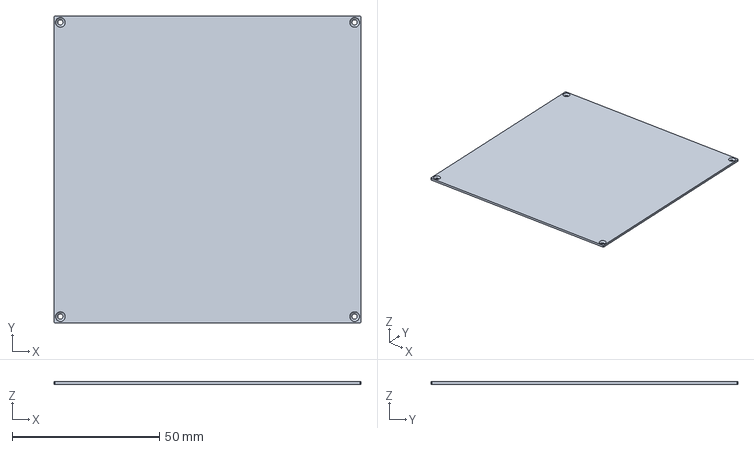
[picture p181: CAD file, 2025-02-10]
Preview/Mechanical/Base.step
104.3 x 104.3 x 1.00 mm
