intechstudio/grid/Preview/Mechanical/PLASTIC-LOW-PROFILE-KEYCAP.step

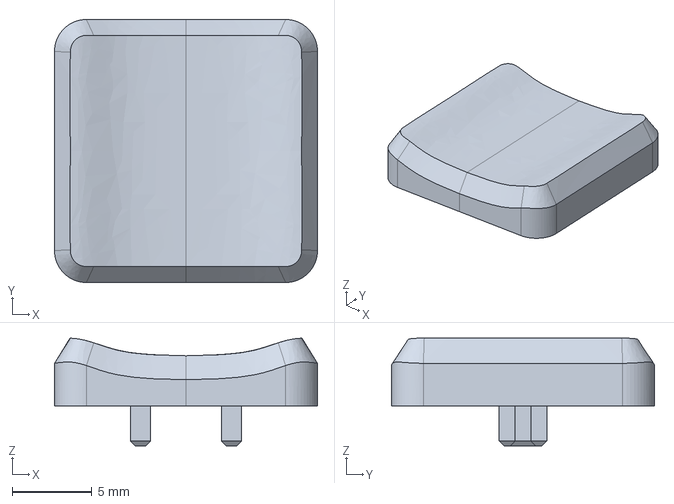
[picture p182: CAD file, 2025-02-10]
Preview/Mechanical/PLASTIC-LOW-PROFILE-KEYCAP.step
16.5 x 16.5 x 6.76 mm
