intechstudio/grid/Preview/Mechanical/feature_usb_hole.step

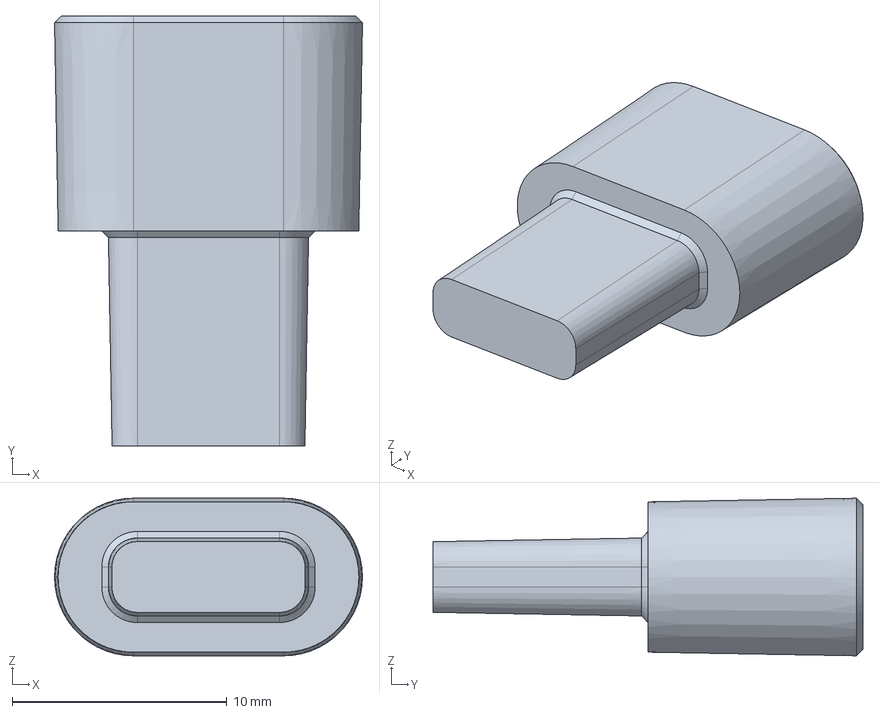
[picture p183: CAD file, 2025-02-10]
Preview/Mechanical/feature_usb_hole.step
14.3 x 20.0 x 7.34 mm
