intechstudio/grid/Preview/Mechanical/SMT_CAP_V2.step

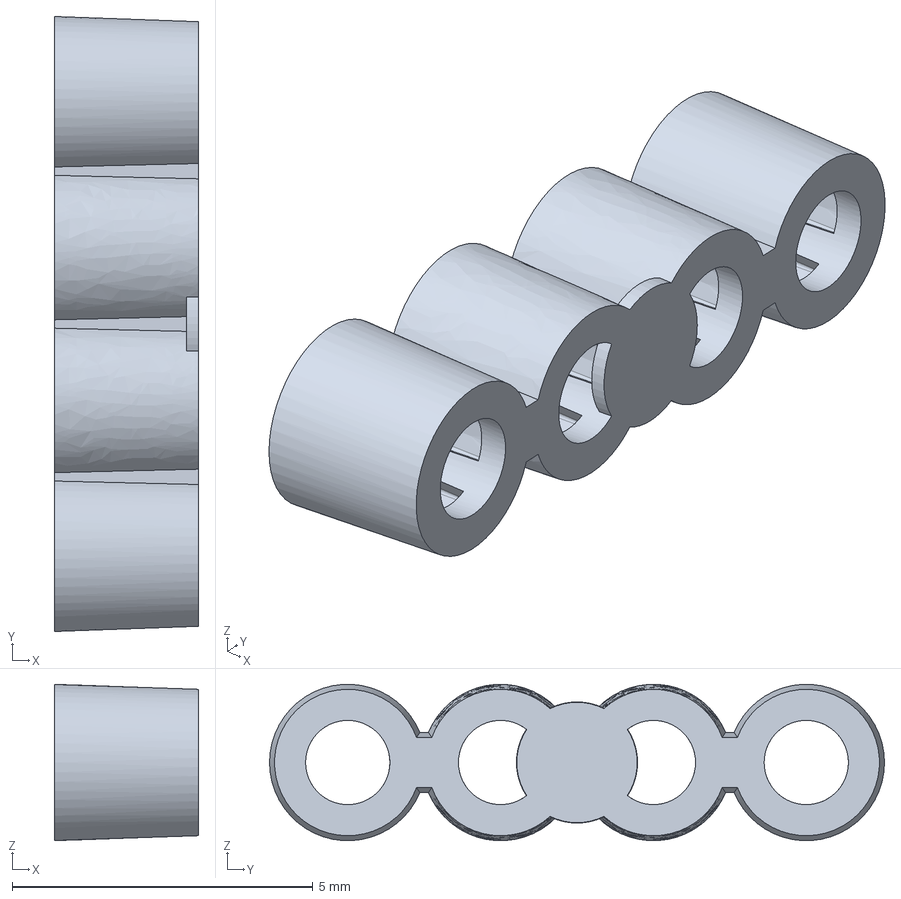
[picture p184: CAD file, 2025-02-10]
Preview/Mechanical/SMT_CAP_V2.step
2.40 x 10.2 x 2.60 mm
