intechstudio/grid/Preview/Mechanical/PLASTIC-VSN1-BUTTON.step

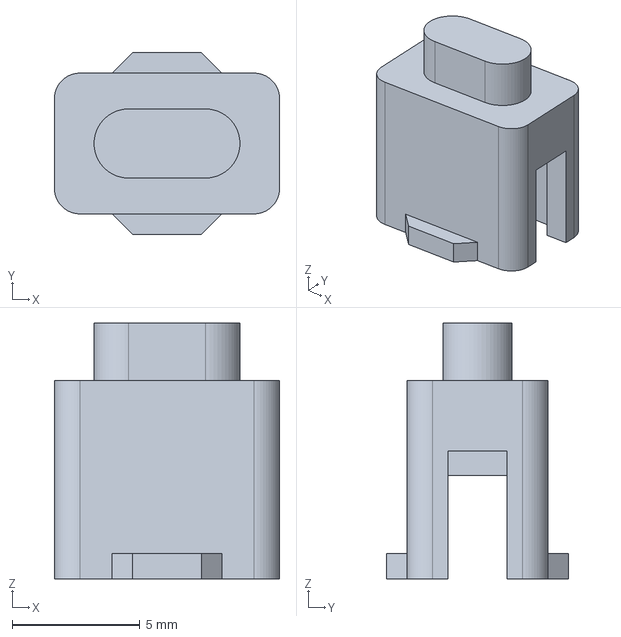
[picture p185: CAD file, 2025-02-10]
Preview/Mechanical/PLASTIC-VSN1-BUTTON.step
8.80 x 7.10 x 10.0 mm
