intechstudio/grid/Preview/Mechanical/feature_pogo_hole_injection.step

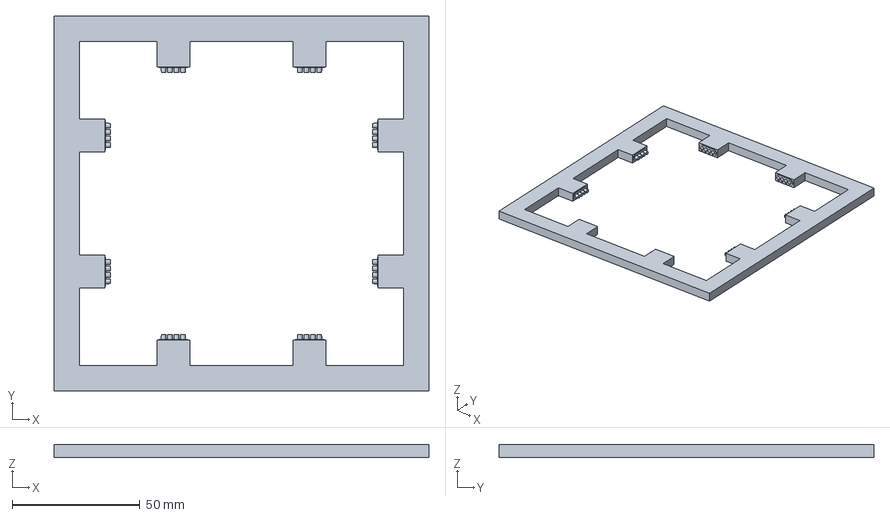
[picture p186: CAD file, 2025-02-10]
Preview/Mechanical/feature_pogo_hole_injection.step
146.8 x 146.8 x 5.00 mm
