intechstudio/grid/Preview/Mechanical/Body002.step

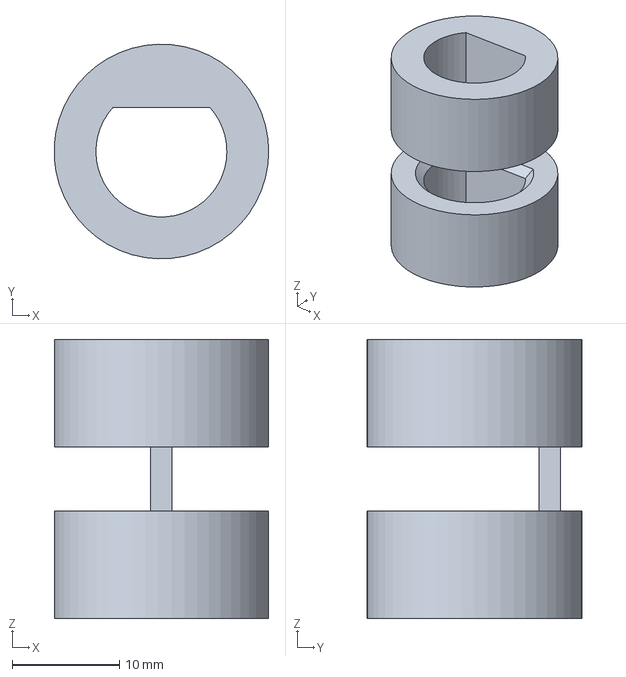
[picture p187: CAD file, 2025-02-10]
Preview/Mechanical/Body002.step
20.0 x 20.0 x 26.0 mm
