intechstudio/grid/Preview/Mechanical/PLASTIC-CAP-BUTTON.step

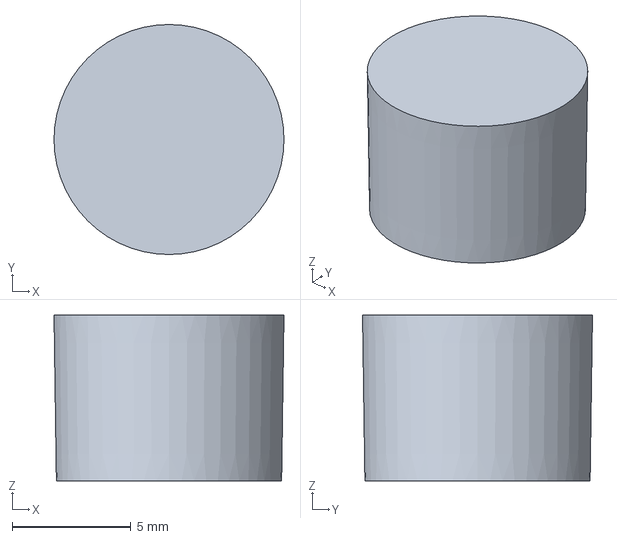
[picture p188: CAD file, 2025-02-10]
Preview/Mechanical/PLASTIC-CAP-BUTTON.step
9.70 x 9.70 x 7.00 mm
