intechstudio/grid/Preview/Mechanical/PCBA-VSN1-DISPLAY.step

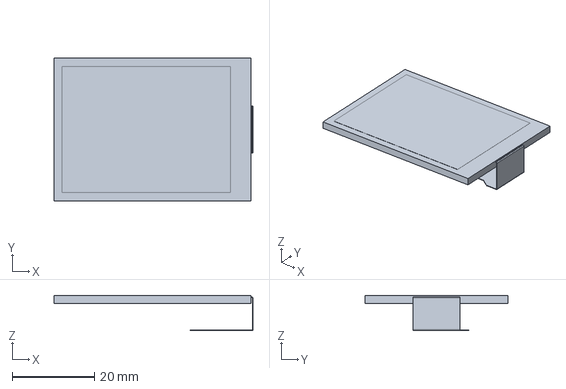
[picture p189: CAD file, 2025-02-10]
Preview/Mechanical/PCBA-VSN1-DISPLAY.step
48.3 x 34.6 x 8.55 mm
