intechstudio/grid/Preview/Mechanical/PLASTIC-CAP-FADER.step

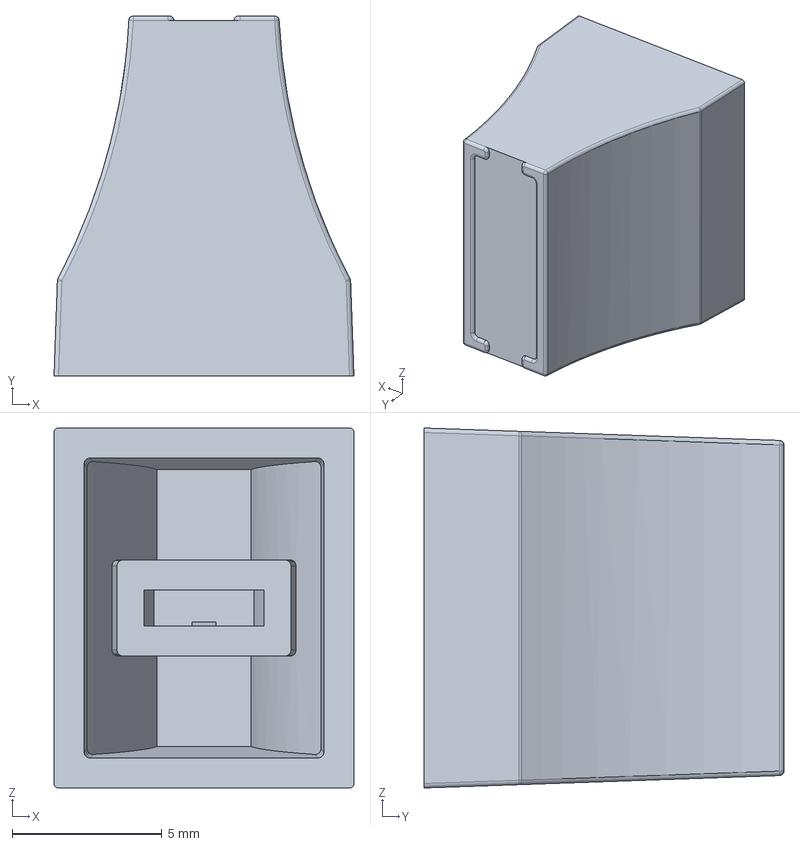
[picture p190: CAD file, 2025-02-10]
Preview/Mechanical/PLASTIC-CAP-FADER.step
10.0 x 12.0 x 12.0 mm
