intechstudio/grid/Preview/Mechanical/FRONTPANEL-SHEET-VSN0.step

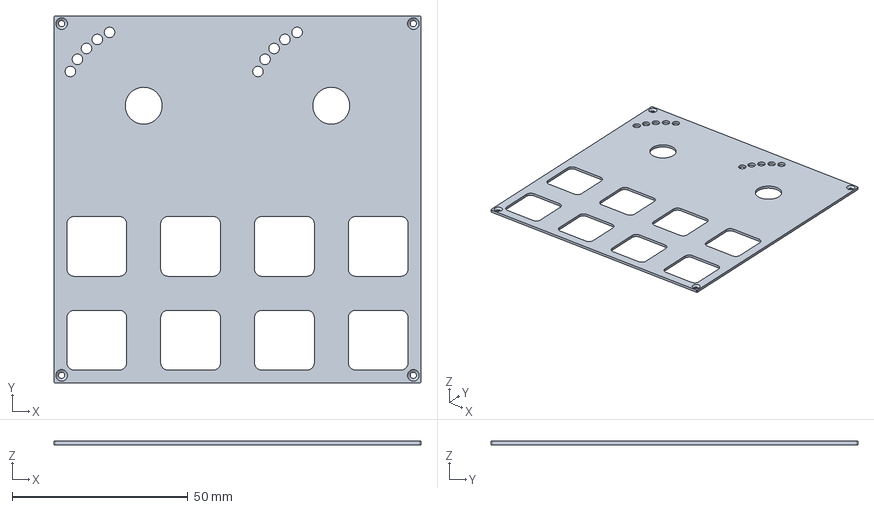
[picture p191: CAD file, 2025-02-10]
Preview/Mechanical/FRONTPANEL-SHEET-VSN0.step
104.3 x 104.3 x 1.00 mm
