intechstudio/grid/Preview/Mechanical/SPACER.step

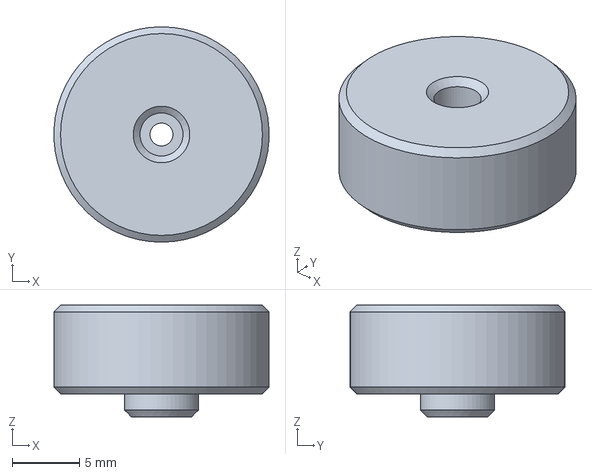
[picture p192: CAD file, 2025-02-10]
Preview/Mechanical/SPACER.step
16.0 x 16.0 x 8.30 mm
