intechstudio/grid/Preview/Mechanical/PCBA-CONN-POGO.step

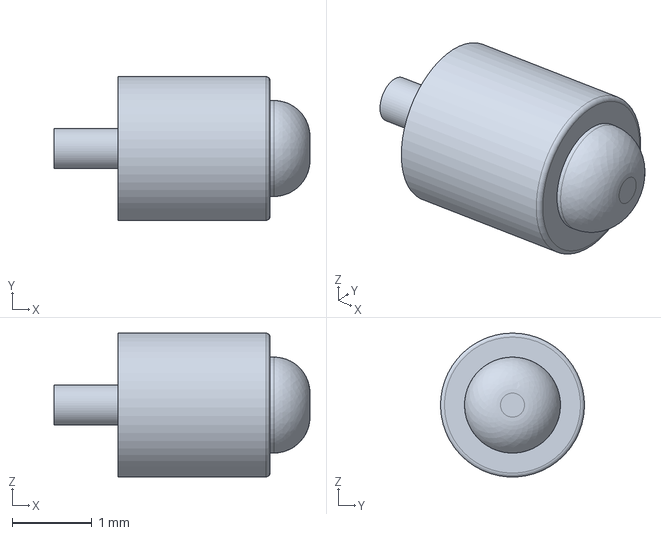
[picture p193: CAD file, 2025-02-10]
Preview/Mechanical/PCBA-CONN-POGO.step
3.20 x 1.80 x 1.80 mm
