intechstudio/grid/Preview/Mechanical/feature_alignment_bevel_B.step

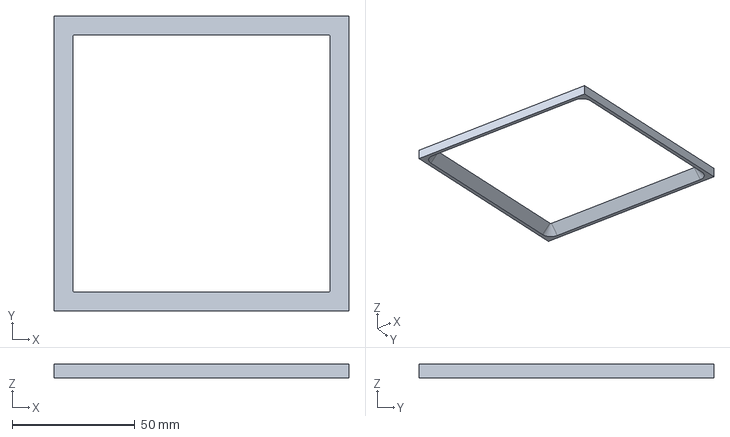
[picture p194: CAD file, 2025-02-10]
Preview/Mechanical/feature_alignment_bevel_B.step
120.0 x 120.0 x 5.50 mm
