intechstudio/grid/Preview/Mechanical/feature_map_hole.step

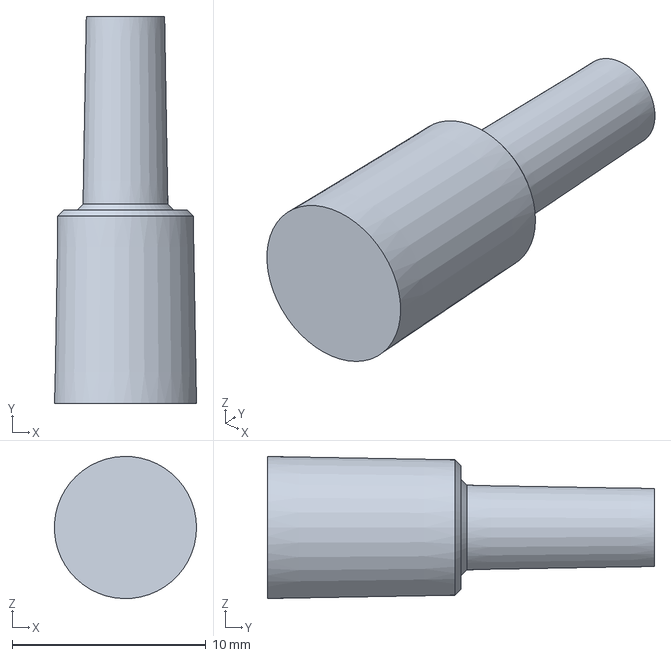
[picture p195: CAD file, 2025-02-10]
Preview/Mechanical/feature_map_hole.step
7.34 x 20.0 x 7.35 mm
