intechstudio/grid/Preview/Mechanical/PLASTIC-VSN1-DISPLAY-INTERFACE.step

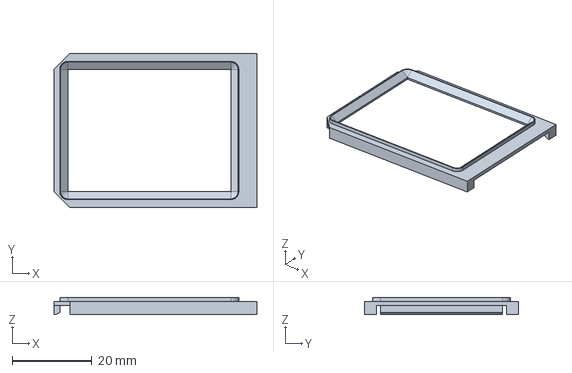
[picture p196: CAD file, 2025-02-10]
Preview/Mechanical/PLASTIC-VSN1-DISPLAY-INTERFACE.step
50.8 x 38.6 x 4.30 mm
