intechstudio/grid/Preview/Mechanical/feature_alignment_lip_B.step

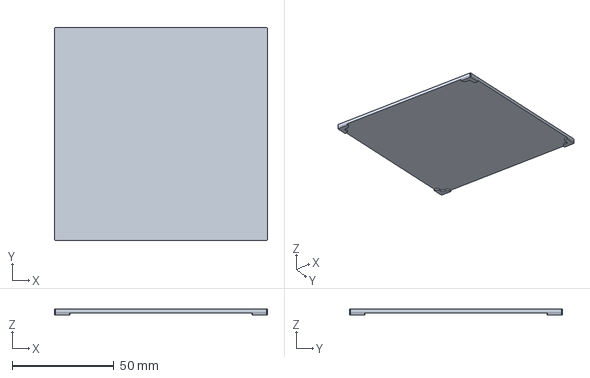
[picture p197: CAD file, 2025-02-10]
Preview/Mechanical/feature_alignment_lip_B.step
104.6 x 104.6 x 3.00 mm
