intechstudio/grid/Preview/Mechanical/PCBA-ENC.step

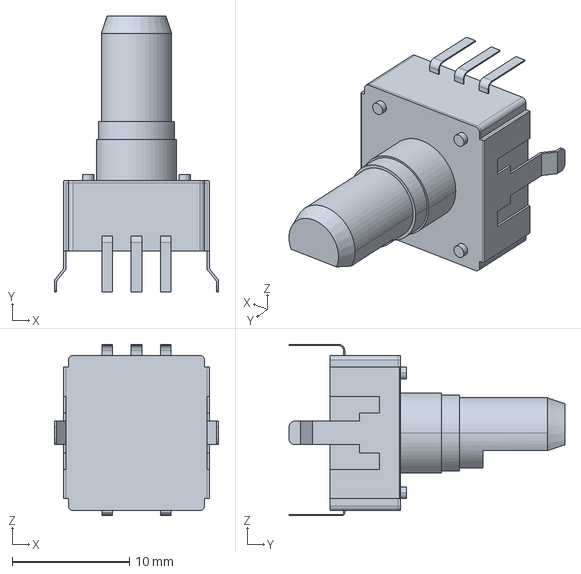
[picture p198: CAD file, 2025-02-10]
Preview/Mechanical/PCBA-ENC.step
14.0 x 23.5 x 14.6 mm
