intechstudio/grid/Preview/Mechanical/KNOB-TEK2.step

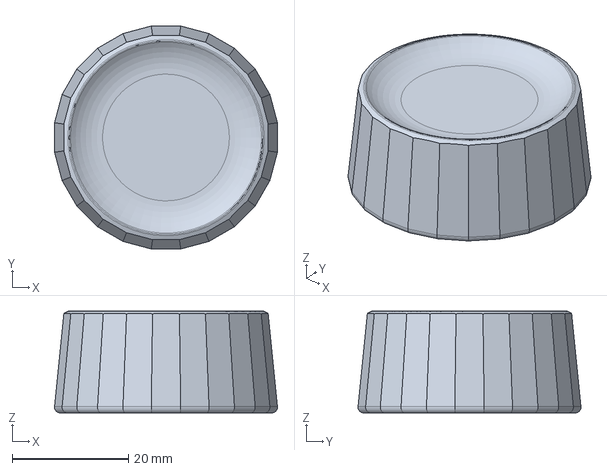
[picture p199: CAD file, 2025-02-10]
Preview/Mechanical/KNOB-TEK2.step
38.3 x 38.3 x 17.5 mm
