intechstudio/grid/Preview/Mechanical/PLASTIC-LIGHTPIPE.step

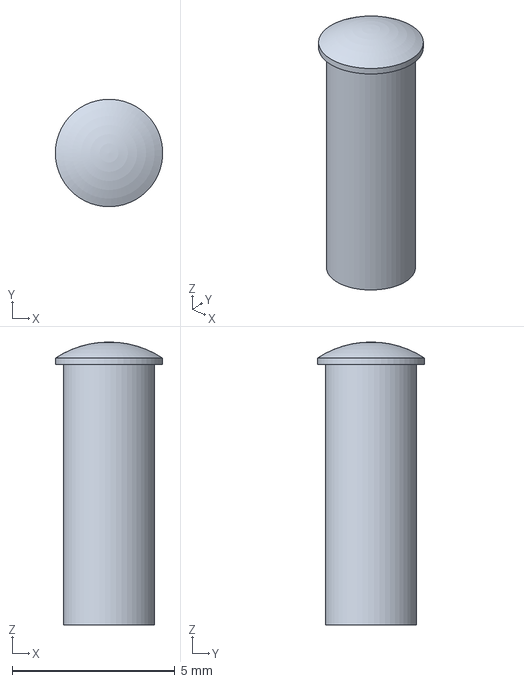
[picture p200: CAD file, 2025-02-10]
Preview/Mechanical/PLASTIC-LIGHTPIPE.step
3.30 x 3.30 x 8.69 mm
