intechstudio/grid/Preview/Mechanical/INSERT-M1.6x2.5x3.step

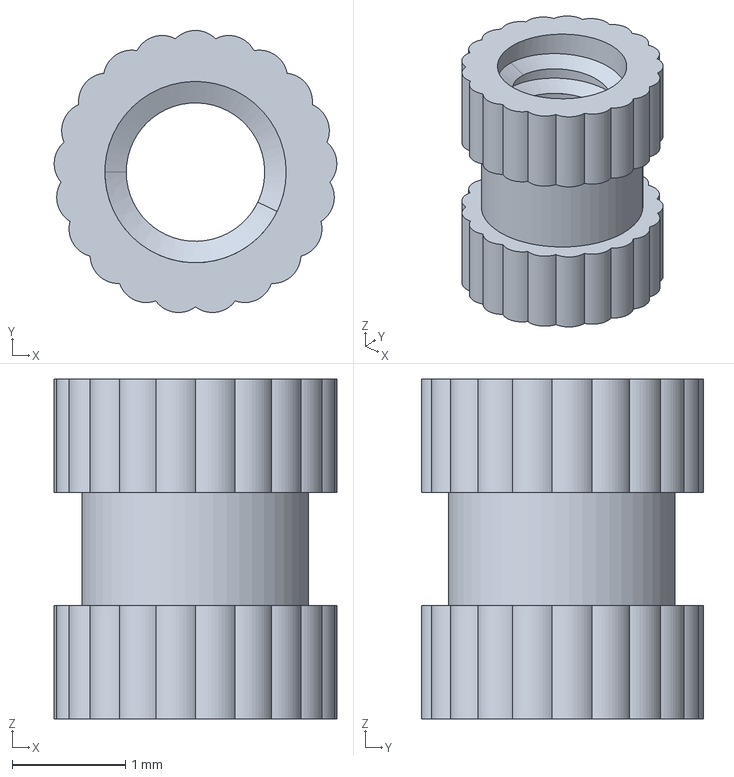
[picture p201: CAD file, 2025-02-10]
Preview/Mechanical/INSERT-M1.6x2.5x3.step
2.49 x 2.49 x 3.00 mm
