intechstudio/grid/Preview/Mechanical/PCBA-LONGFADER.step

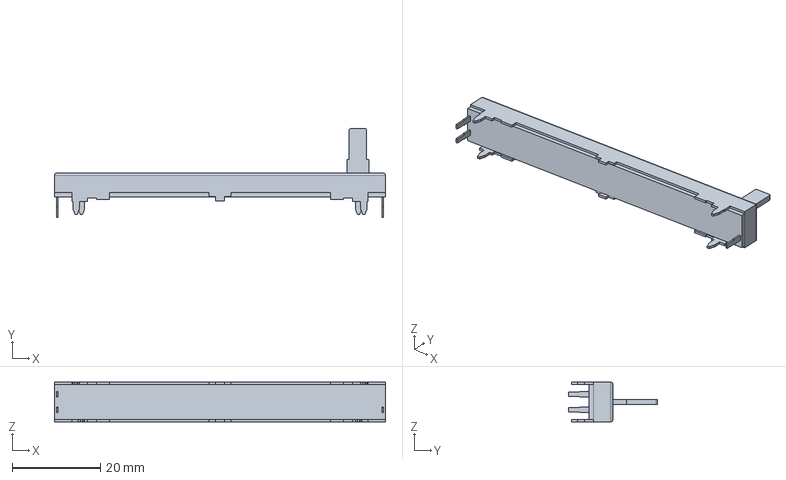
[picture p202: CAD file, 2025-02-10]
Preview/Mechanical/PCBA-LONGFADER.step
75.0 x 20.1 x 9.00 mm
