intechstudio/grid/Preview/Mechanical/PLASTIC-BUSHING-POT-TEK2.step

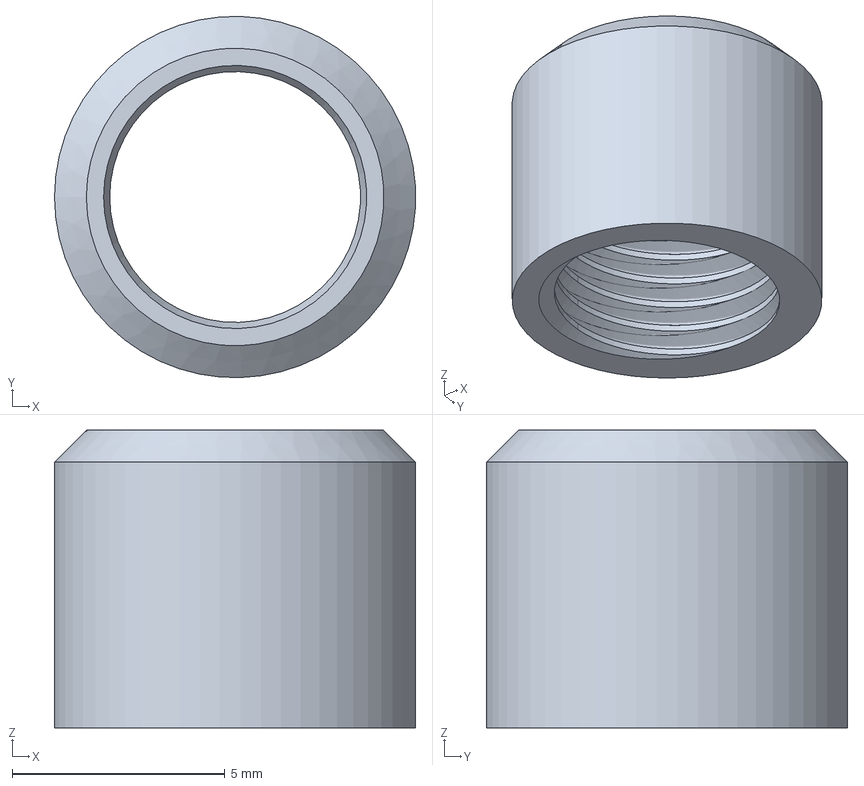
[picture p203: CAD file, 2025-02-10]
Preview/Mechanical/PLASTIC-BUSHING-POT-TEK2.step
8.49 x 8.50 x 7.00 mm
