intechstudio/grid/Preview/Mechanical/feature_drill_pattern_inject.step

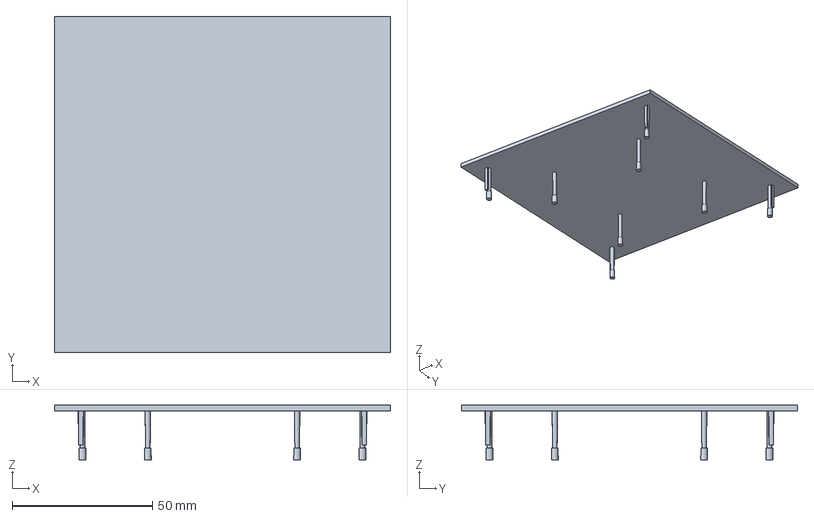
[picture p204: CAD file, 2025-02-10]
Preview/Mechanical/feature_drill_pattern_inject.step
120.0 x 120.0 x 19.5 mm
