intechstudio/grid/Preview/Mechanical/feature_edge_compensation_nominal_drafted.step

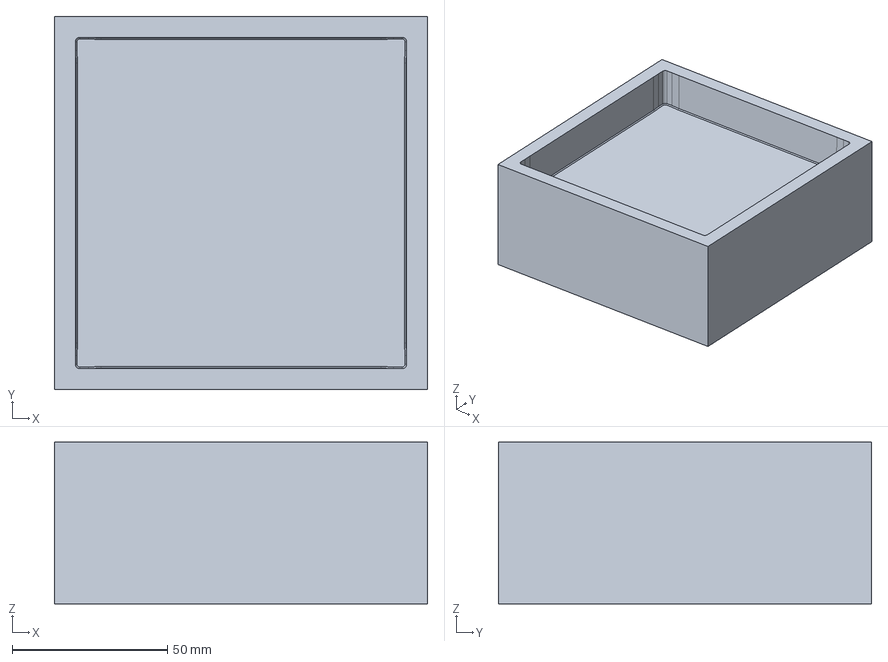
[picture p205: CAD file, 2025-02-10]
Preview/Mechanical/feature_edge_compensation_nominal_drafted.step
120.0 x 120.0 x 52.0 mm
