intechstudio/grid/Preview/Mechanical/feature_magent_hole_injection.step

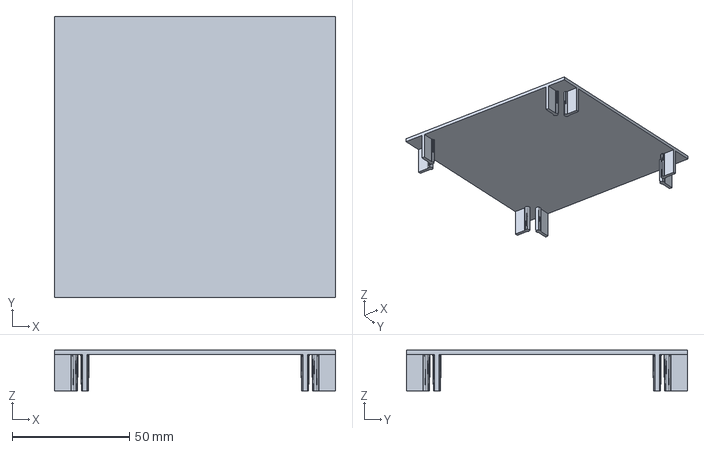
[picture p206: CAD file, 2025-02-10]
Preview/Mechanical/feature_magent_hole_injection.step
120.0 x 120.0 x 17.5 mm
