intechstudio/grid/Preview/Mechanical/PCBA-CONN-POGO_Cap.step

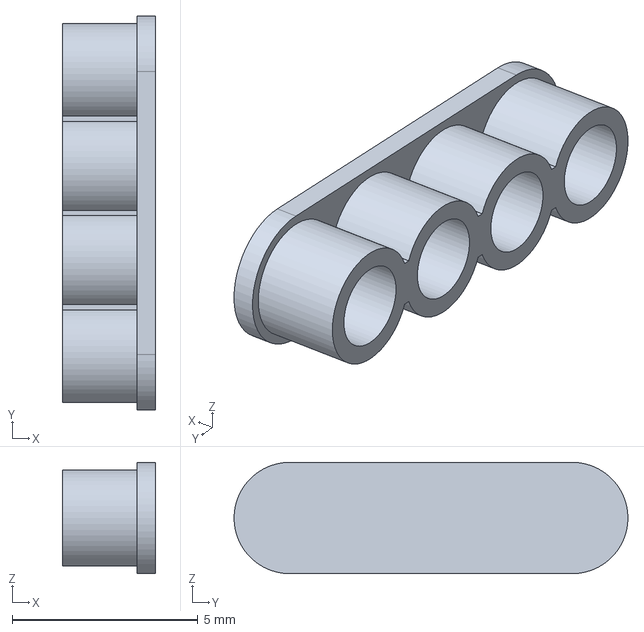
[picture p207: CAD file, 2025-02-10]
Preview/Mechanical/PCBA-CONN-POGO_Cap.step
2.50 x 10.6 x 3.00 mm
