intechstudio/grid/Preview/Mechanical/PCBA-POT.step

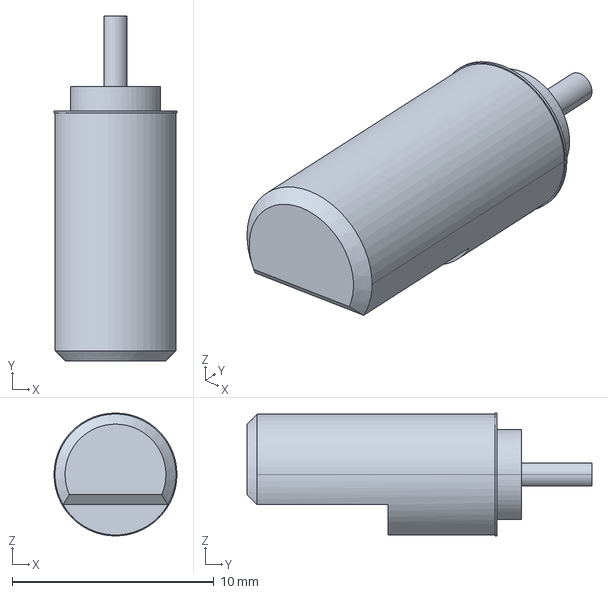
[picture p208: CAD file, 2025-02-10]
Preview/Mechanical/PCBA-POT.step
6.10 x 17.1 x 6.10 mm
