intechstudio/grid/Preview/Mechanical/Body.step

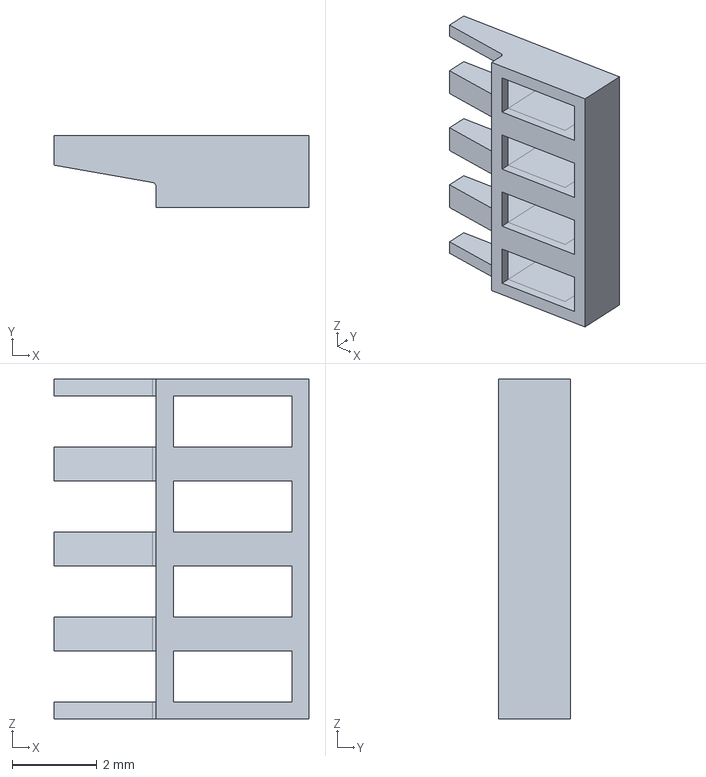
[picture p209: CAD file, 2024-07-18]
Preview/Mechanical/Body.step
6.00 x 1.70 x 8.00 mm
