intechstudio/grid/Preview/Mechanical/PLASTIC-TEK1-DISPLAY-INTERFACE.step

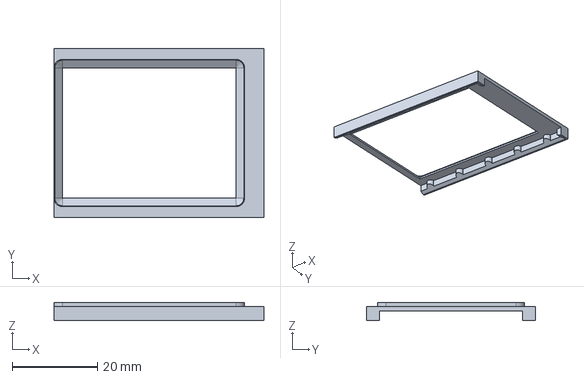
[picture p210: CAD file, 2024-07-09]
Preview/Mechanical/PLASTIC-TEK1-DISPLAY-INTERFACE.step
49.3 x 39.6 x 4.30 mm
