intechstudio/grid/Preview/Mechanical/PLASTIC-TEK1-BUTTON.step

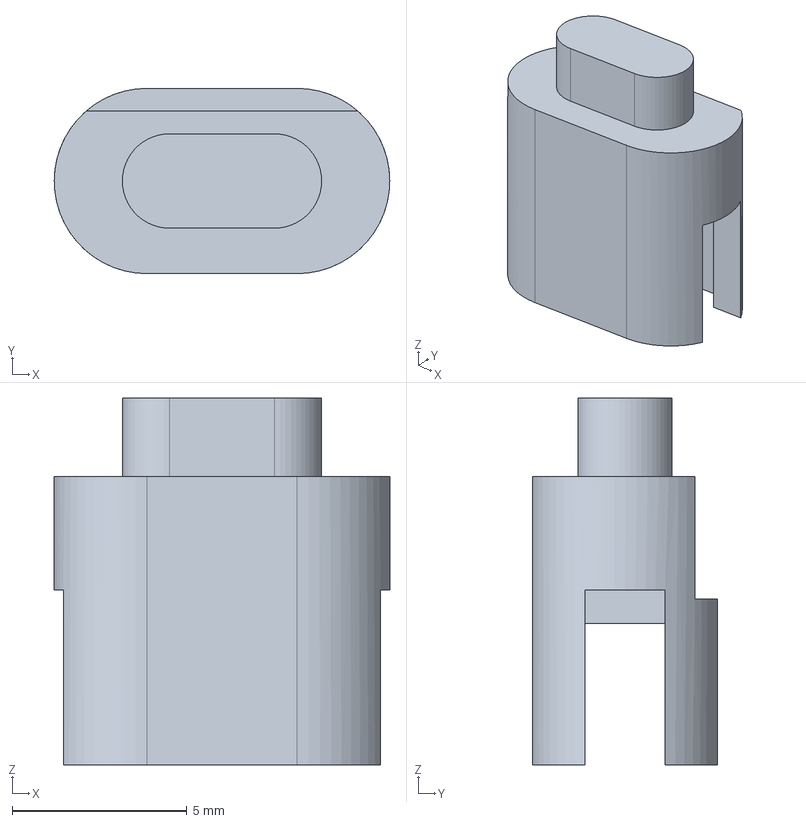
[picture p211: CAD file, 2024-07-09]
Preview/Mechanical/PLASTIC-TEK1-BUTTON.step
9.60 x 5.30 x 10.5 mm
