intechstudio/grid/Preview/Mechanical/INSERT_TEK2.step

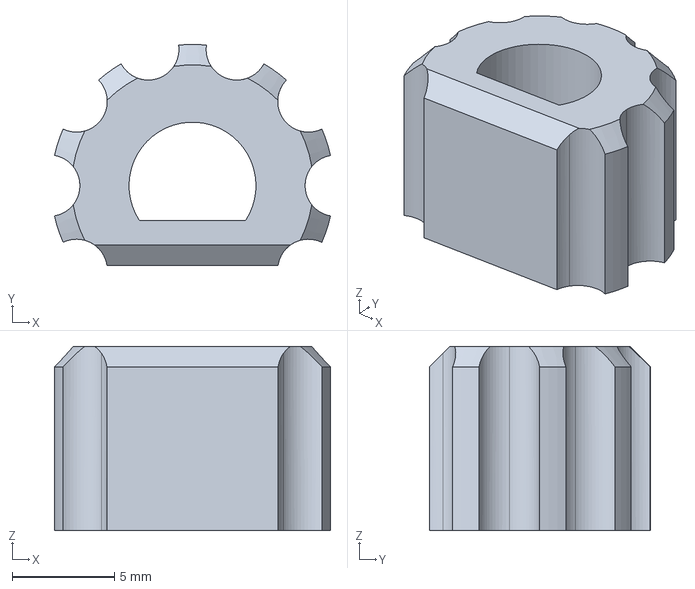
[picture p212: CAD file, 2024-01-31]
Preview/Mechanical/INSERT_TEK2.step
13.5 x 10.8 x 9.00 mm
