intechstudio/grid/Preview/Mechanical/PLASTIC-MAGNET-CLIP.step

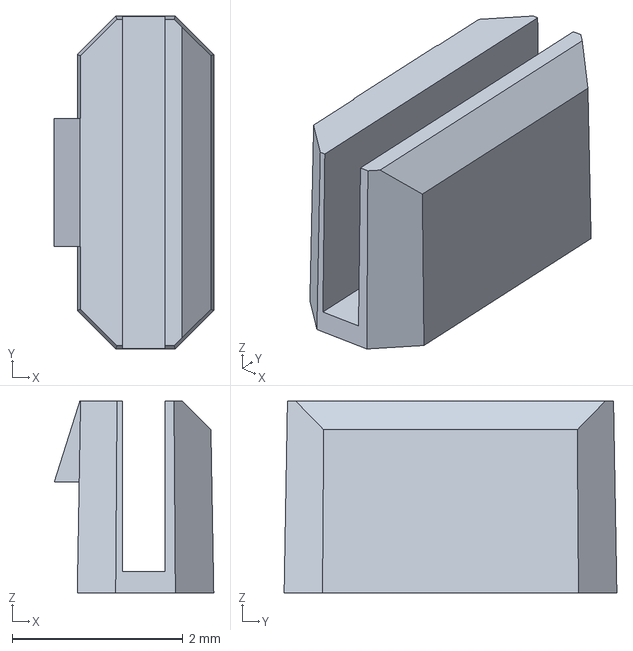
[picture p213: CAD file, 2024-01-02]
Preview/Mechanical/PLASTIC-MAGNET-CLIP.step
1.87 x 3.90 x 2.25 mm
