intechstudio/grid/Preview/Mechanical/LIGHTPIPE.step

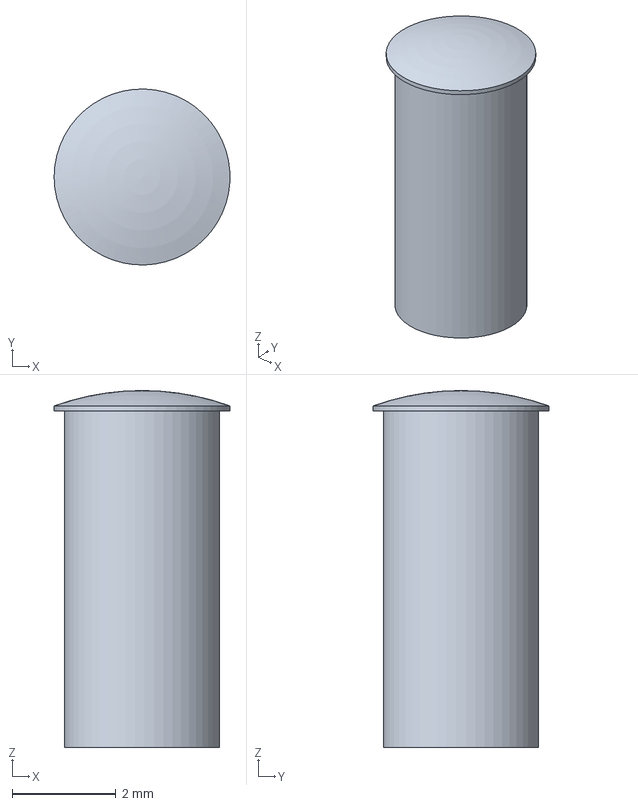
[picture p214: CAD file, 2023-12-19]
Preview/Mechanical/LIGHTPIPE.step
3.40 x 3.40 x 6.90 mm
