intechstudio/grid/Preview/Electrical/PCBA-EN16_Schematic.pdf

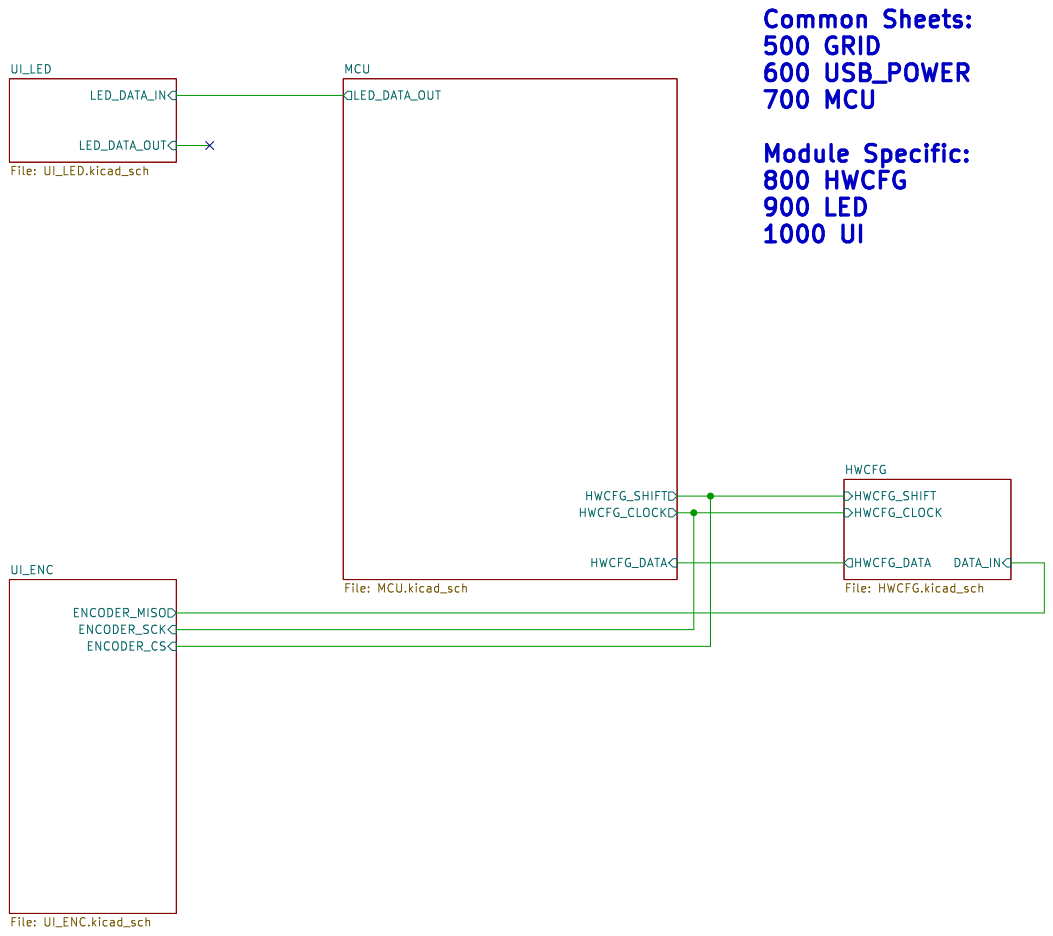
[picture p253: page 1]

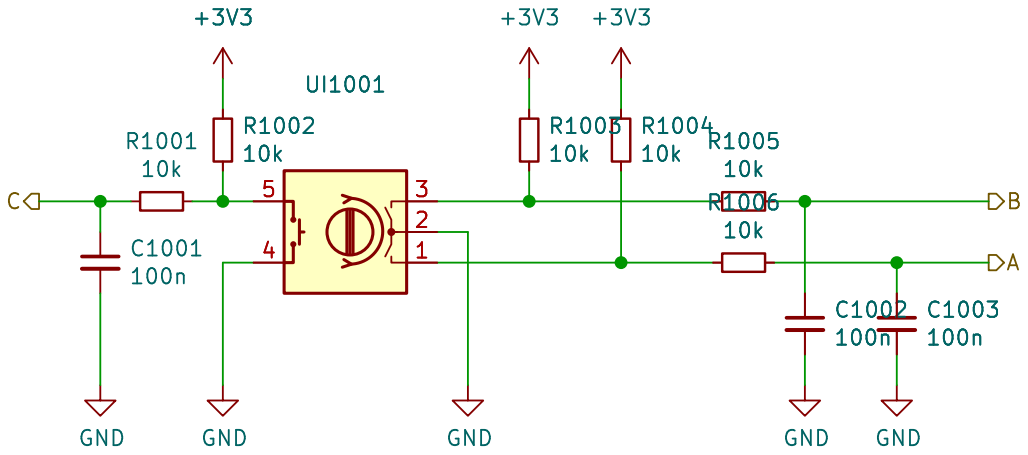
[picture p254: page 2]

Id: 2/23 Title: File: UI_ENC_FILTER.kicad_sch Sheet: /UI_ENC/ENCODER_8/

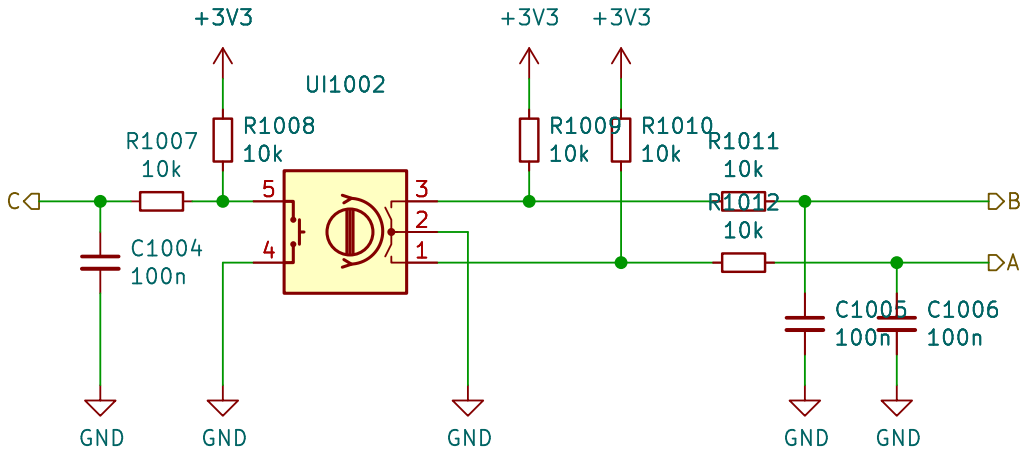
[picture p255: page 3]

Id: 3/23 Title: File: UI_ENC_FILTER.kicad_sch Sheet: /UI_ENC/ENCODER_11/

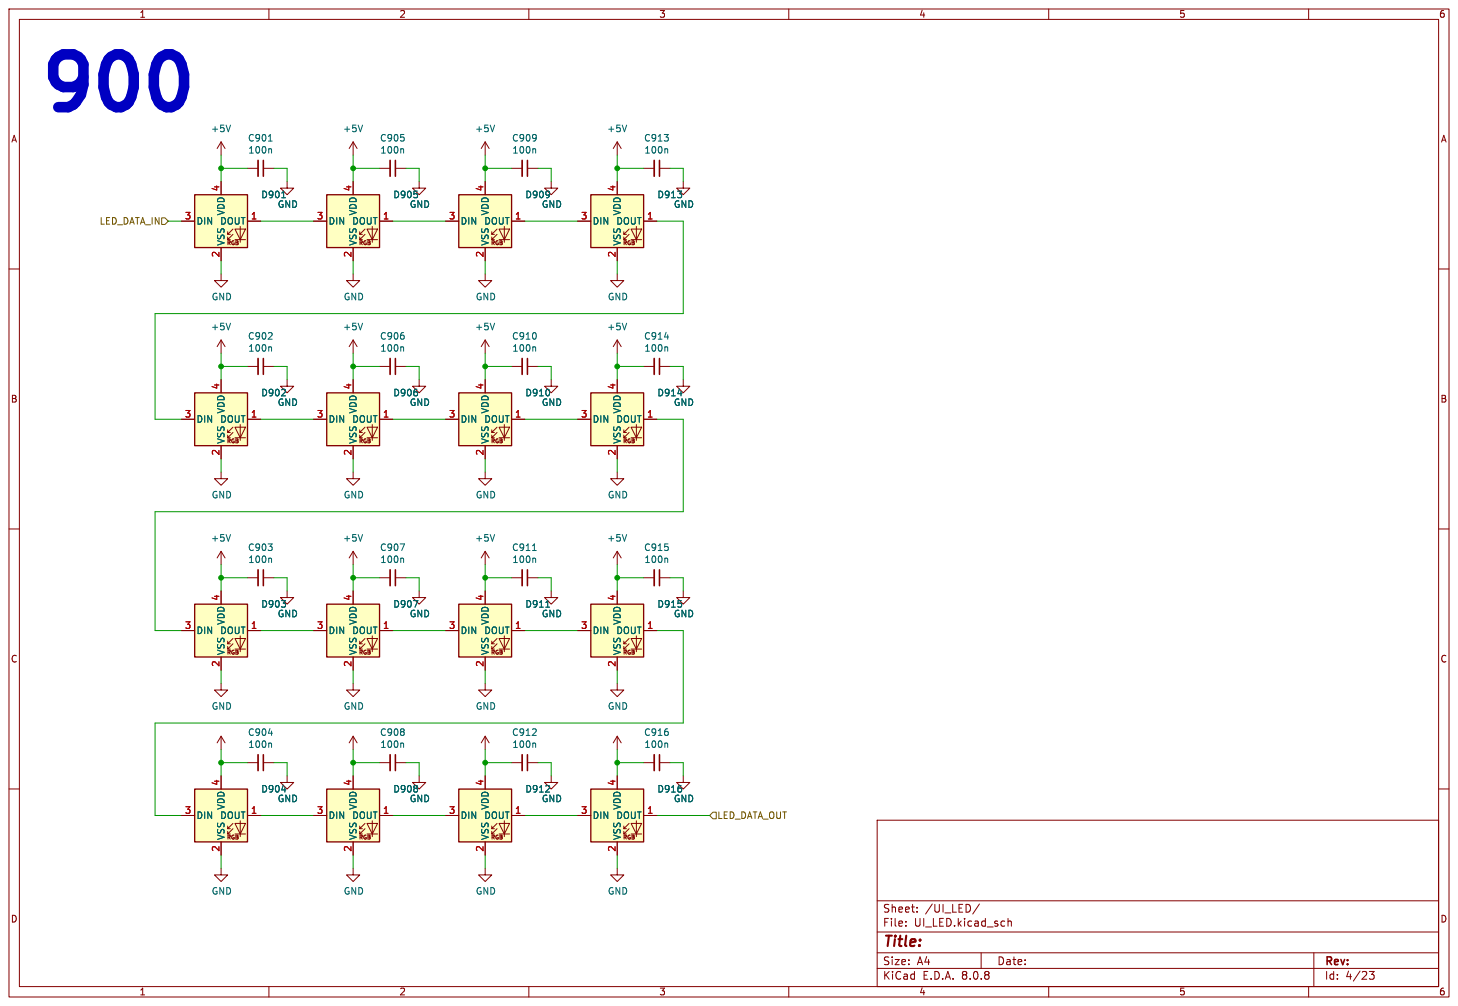
[picture p256: page 4]

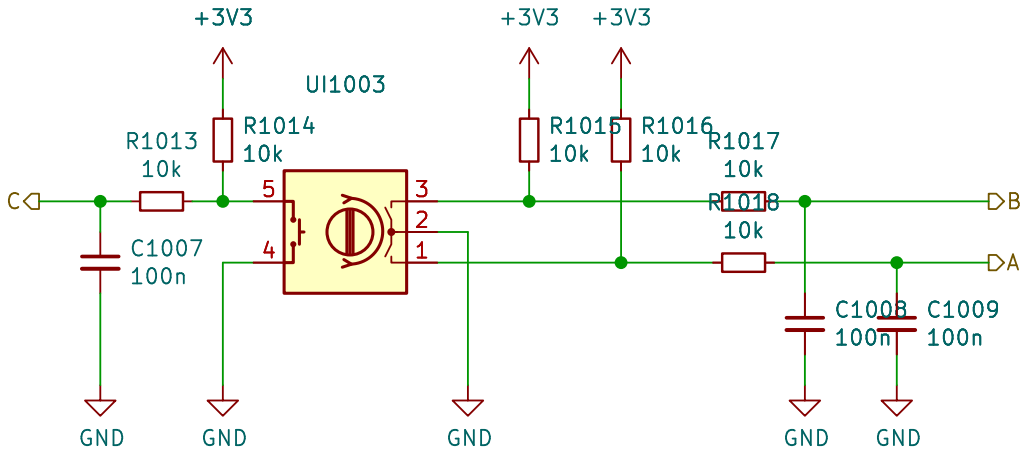
[picture p257: page 5]

Id: 5/23 Title: File: UI_ENC_FILTER.kicad_sch Sheet: /UI_ENC/ENCODER_5/

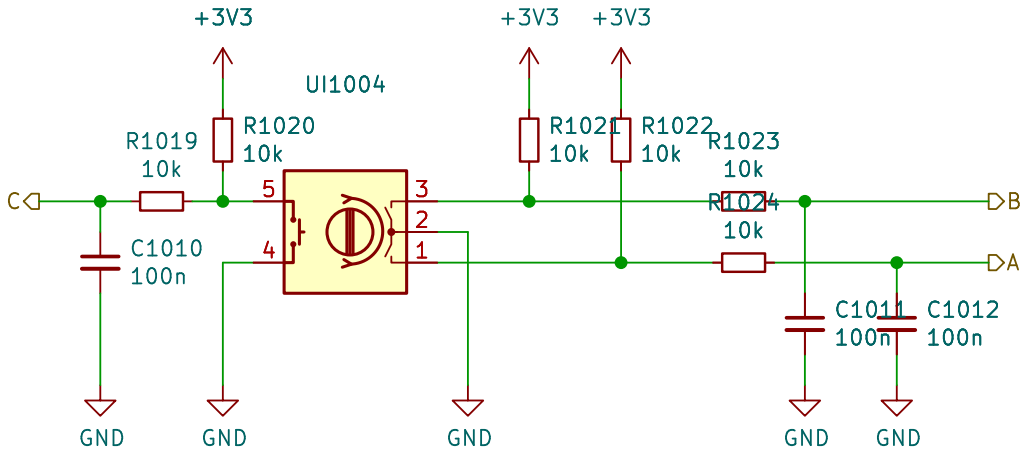
[picture p258: page 6]

Id: 6/23 Title: File: UI_ENC_FILTER.kicad_sch Sheet: /UI_ENC/ENCODER_12/

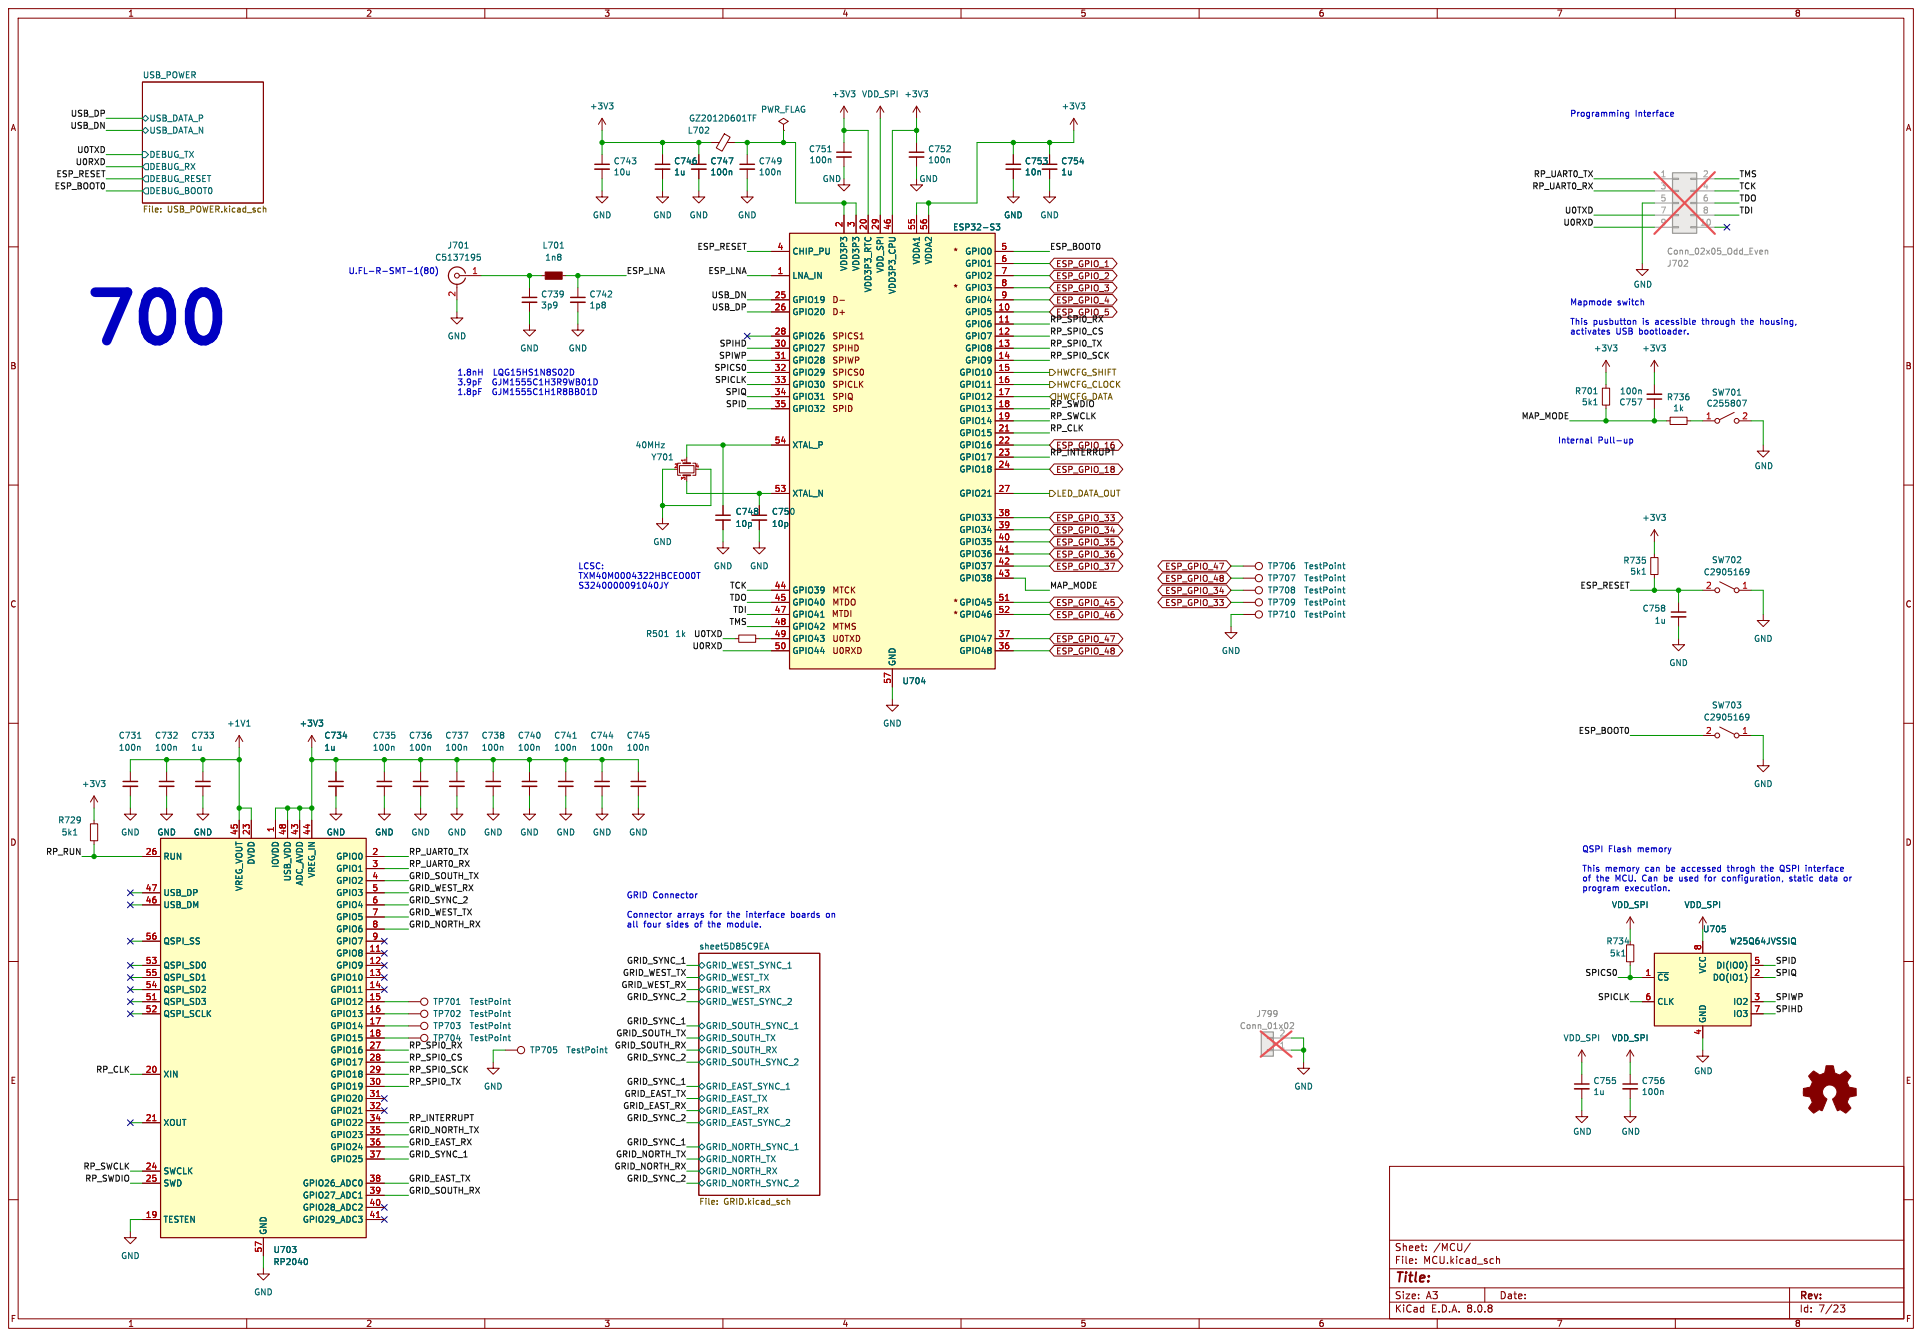
[picture p259: page 7]

100n GND GND
* D+D- MTCK MTDI MTDO MTMS

TP710 TestPoint TP708 TestPoint TP707 TestPoint TP706 TestPoint TP709 TestPoint GND

1 GPIO8 11 GPIO9 12 GPIO10 13 GPIO11 14 GPIO12 15 GPIO13 16 GPIO14 17 GPIO15 18 TESTEN 19 GPIO0 2 XIN 20 XOUT 21 DVDD 23 SWCLK 24 SWD 25 RUN 26 GPIO16 27 GPIO17 28 GPIO18 29 GPIO1 3 GPIO19 30 GPIO20 31 GPIO21 32 GPIO22 34 GPIO23 35 GPIO24 36 GPIO25 37 GPIO26_ADC0 38 GPIO27_ADC1 39 GPIO2 4 GPIO28_ADC2 40 GPIO29_ADC3 41 ADC_AVDD 43 VREG_IN 44 VREG_VOUT 45 USB_DM 46 USB_DP 47 USB_VDD 48 GPIO3 5 QSPI_SD3 51 QSPI_SCLK 52 QSPI_SD0 53 QSPI_SD2 54 QSPI_SD1 55 QSPI_SS 56 GND 57 GPIO4 6 GPIO5 7 GPIO6 8 GPIO7 9 U703 RP2040

1 GPIO8 11 GPIO9 12 GPIO10 13 GPIO11 14 GPIO12 15 GPIO13 16 GPIO14 17 GPIO15 18 TESTEN 19 GPIO0 2 XIN 20 XOUT 21 DVDD 23 SWCLK 24 SWD 25 RUN 26 GPIO16 27 GPIO17 28 GPIO18 29 GPIO1 3 GPIO19 30 GPIO20 31 GPIO21 32 GPIO22 34 GPIO23 35 GPIO24 36 GPIO25 37 GPIO26_ADC0 38 GPIO27_ADC1 39 GPIO2 4 GPIO28_ADC2 40 GPIO29_ADC3 41 ADC_AVDD 43 VREG_IN 44 VREG_VOUT 45 USB_DM 46 USB_DP 47 USB_VDD 48 GPIO3 5 QSPI_SD3 51 QSPI_SCLK 52 QSPI_SD0 53 QSPI_SD2 54 QSPI_SD1 55 QSPI_SS 56 GND 57 GPIO4 6 GPIO5 7 GPIO6 8 GPIO7 9 GND GND GND GND

QSPI Flash memory This memory can be accessed throgh the QSPI interface

all four sides of the module.

TP705 TestPoint TP701 TestPoint TP703 TestPoint TP704 TestPoint TP702 TestPoint

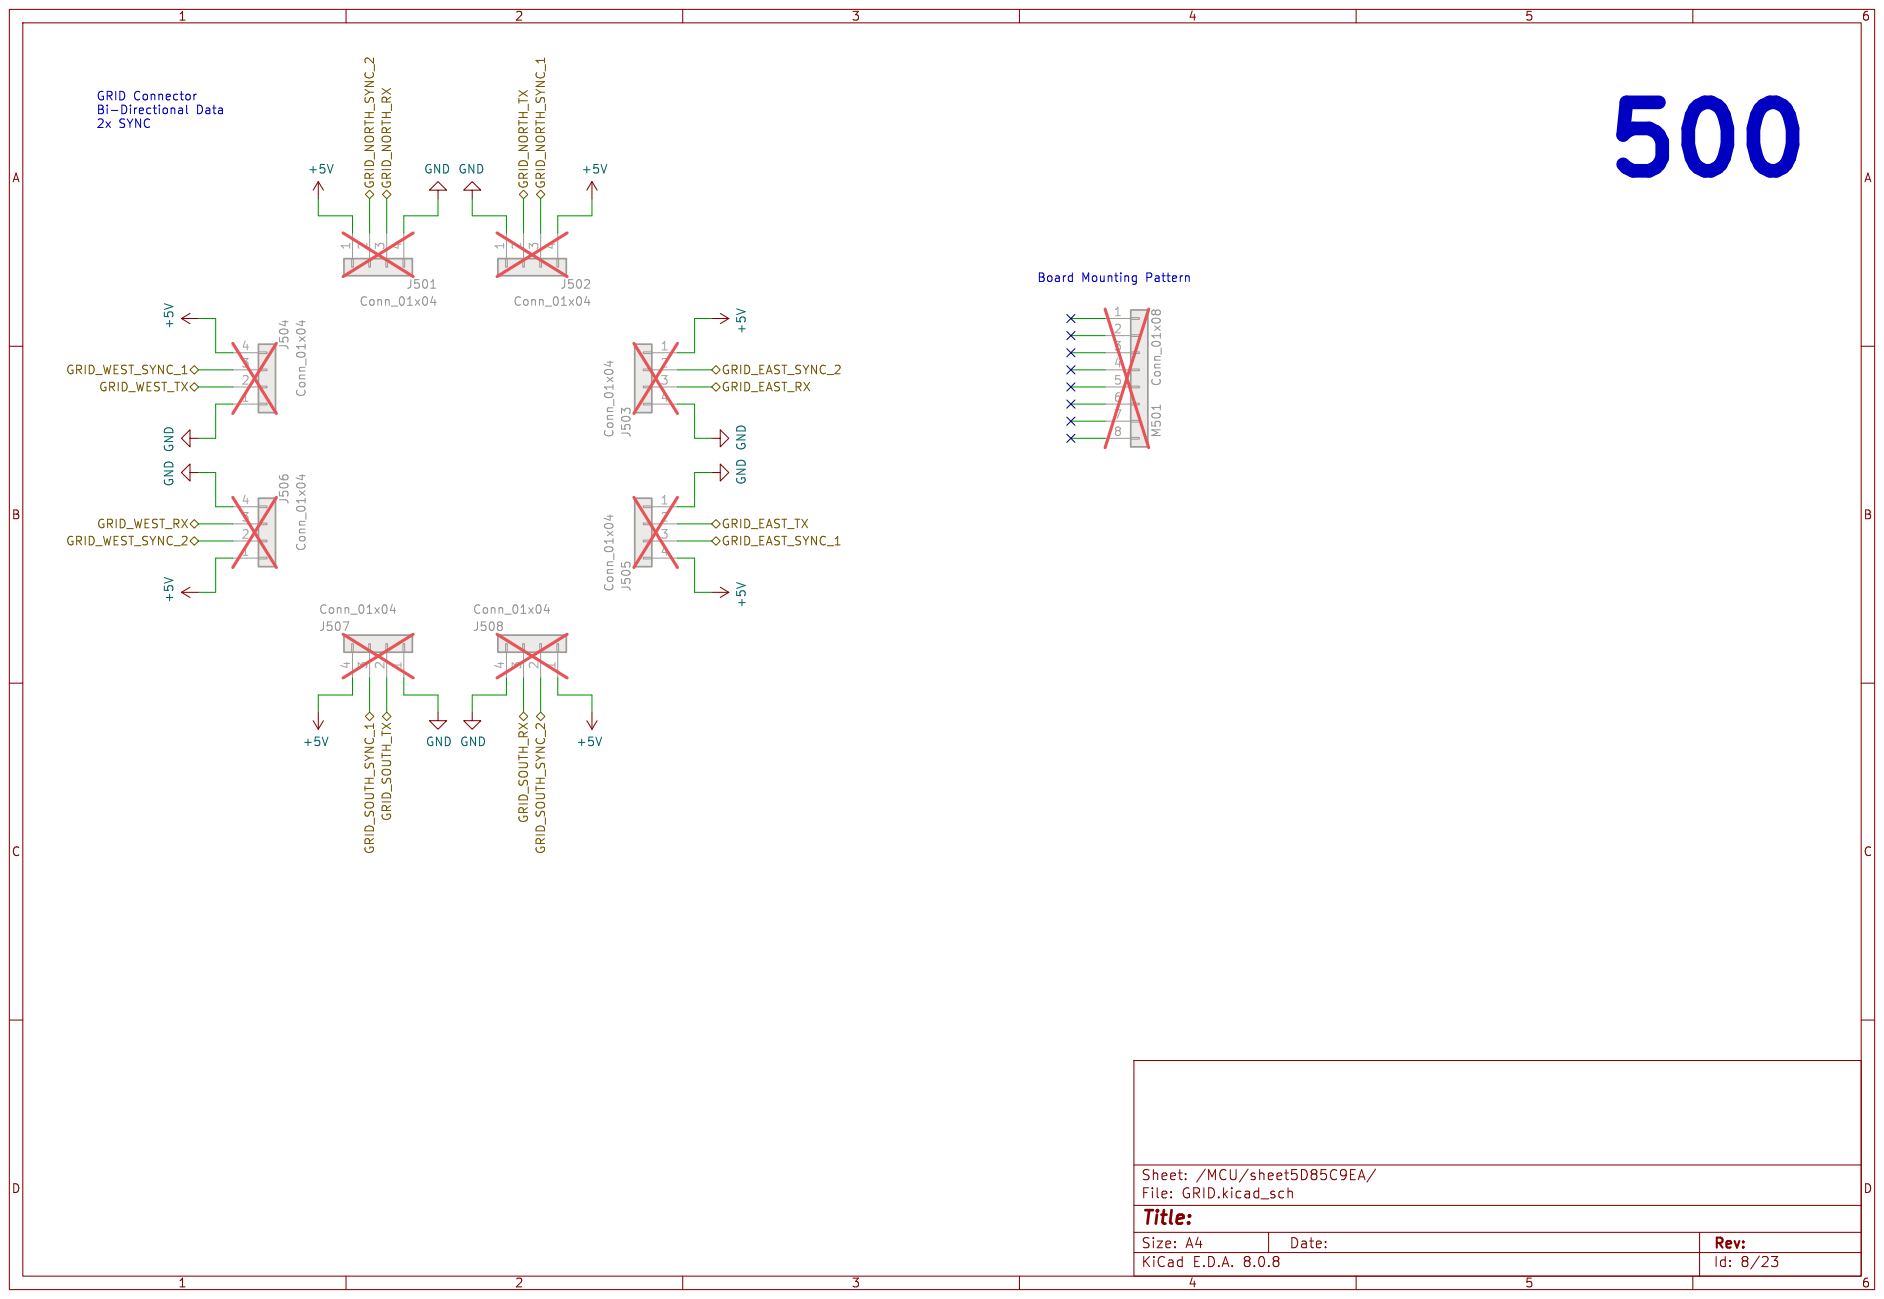
[picture p260: page 8]

4 J501 Conn_01x04 GRID_WEST_TX GRID_EAST_SYNC_1 GRID_EAST_SYNC_2 GRID_EAST_RX GRID_EAST_TX GRID_SOUTH_SYNC_1 GRID_SOUTH_SYNC_2 GRID_SOUTH_TX GRID_SOUTH_RX GRID_WEST_SYNC_1 GRID_WEST_RX GRID_WEST_SYNC_2 GRID_NORTH_SYNC_2 GRID_NORTH_RX GRID_NORTH_TX GRID_NORTH_SYNC_1 Board Mounting Pattern GRID Connector Bi-Directional Data

Id: 8/23 Title: File: GRID.kicad_sch Sheet: /MCU/sheet5D85C9EA/

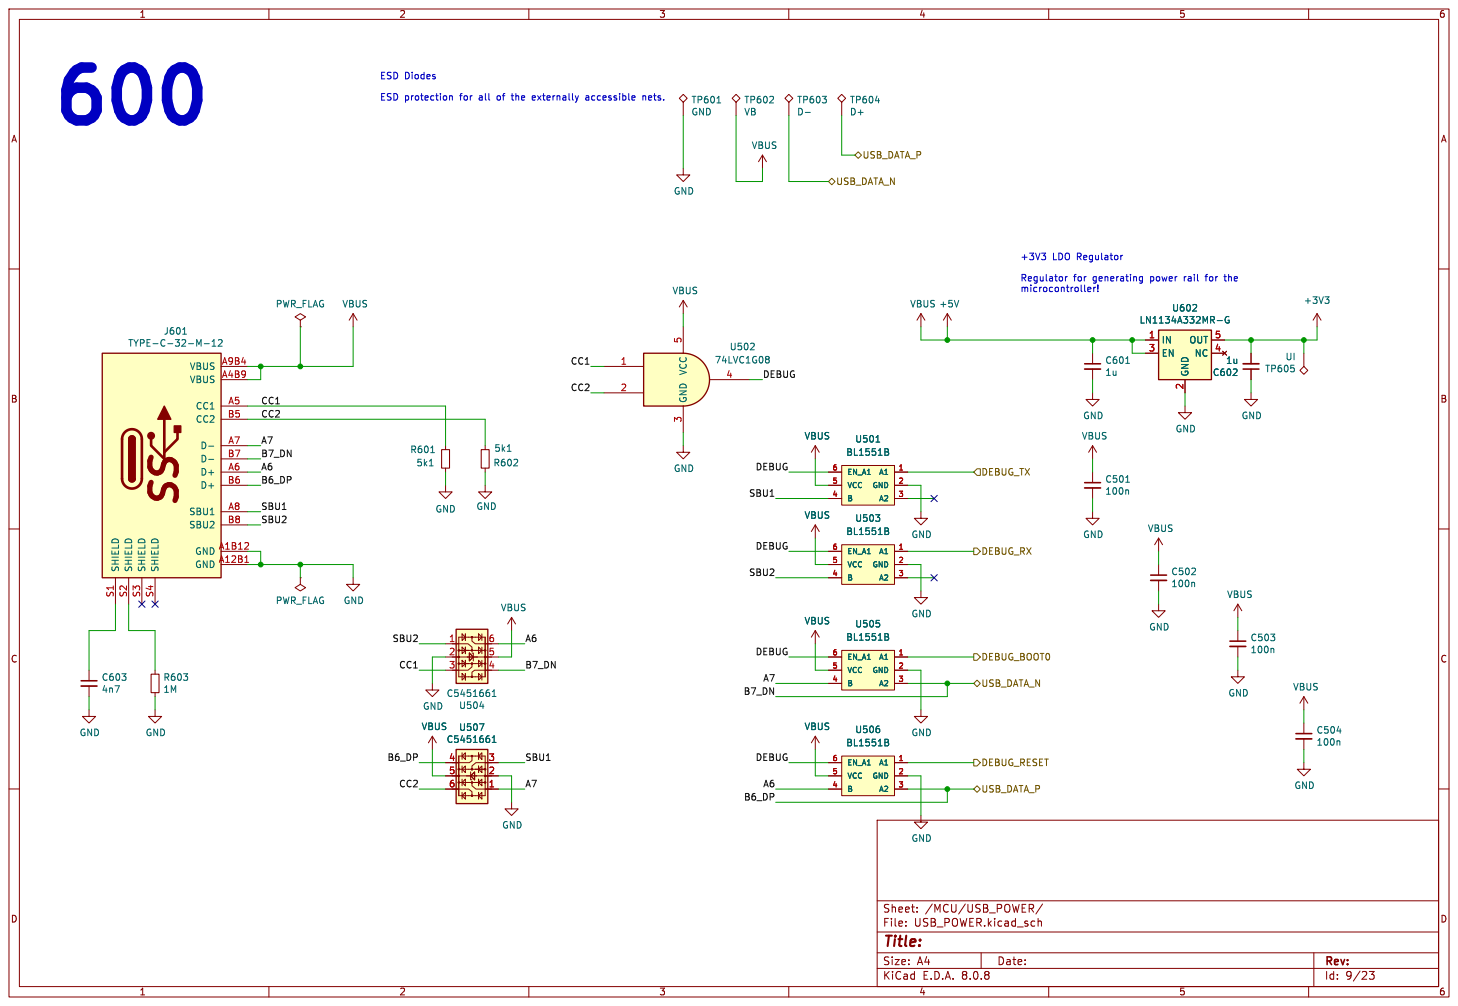
[picture p261: page 9]

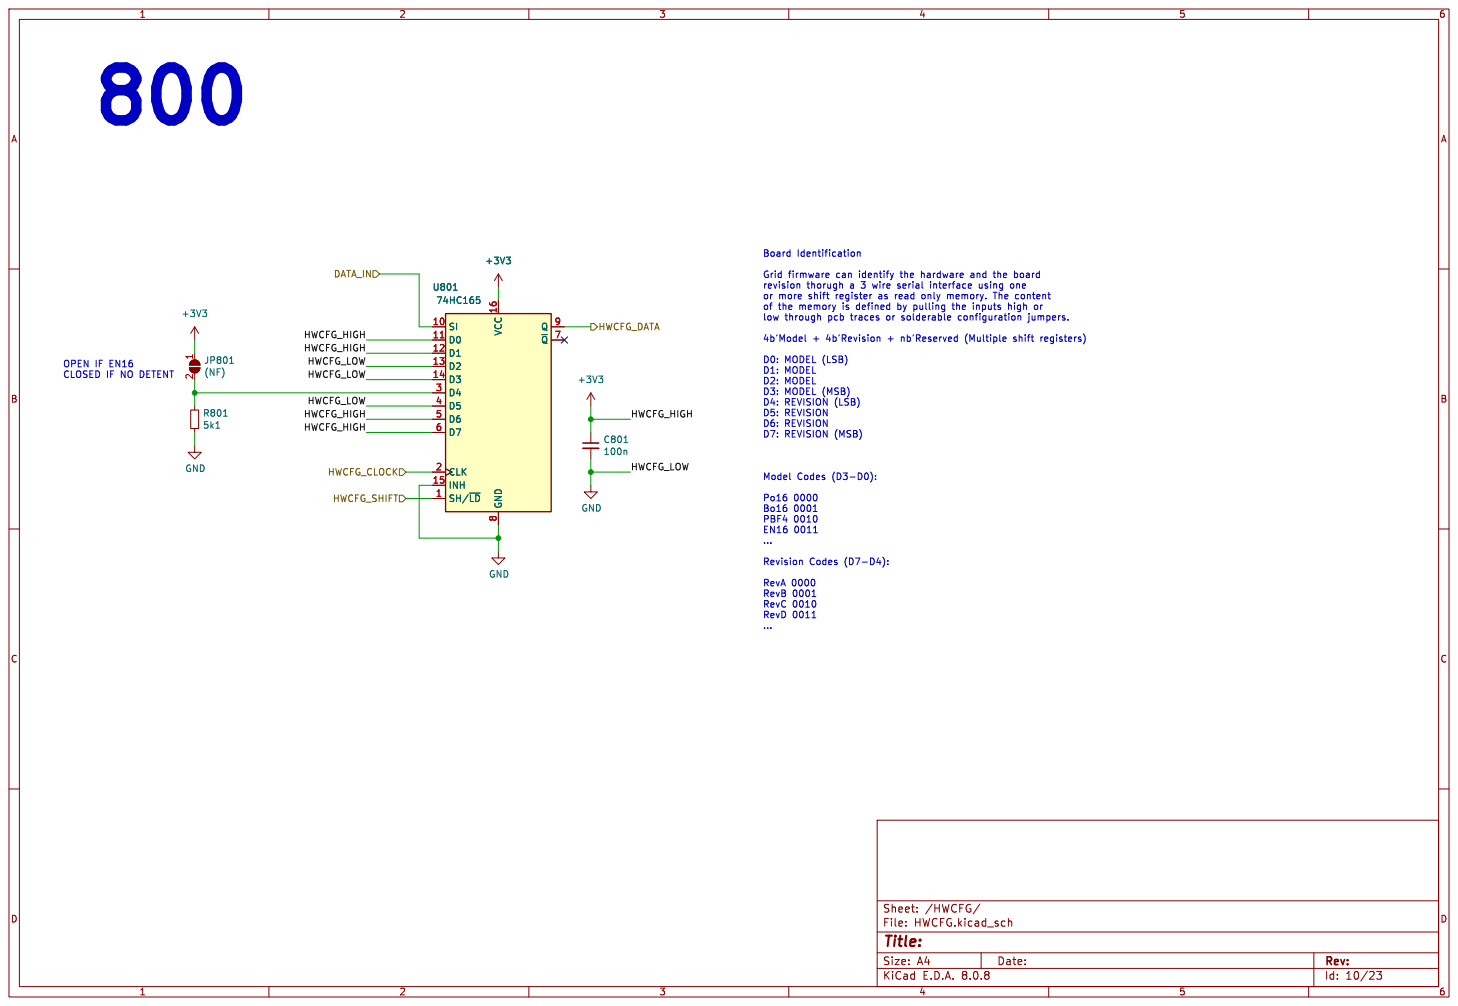
[picture p262: page 10]

... OPEN IF EN16 CLOSED IF NO DETENT 800

D6: REVISION
D7: REVISION (MSB) Model Codes (D3-D0): Po16 0000 Bo16 0001 PBF4 0010 EN16 0011

Id: 10/23 Title: File: HWCFG.kicad_sch Sheet: /HWCFG/ GND

... Revision Codes (D7-D4): RevA 0000 RevB 0001 RevC 0010 RevD 0011


Id: 11/23 Title: File: UI_ENC_FILTER.kicad_sch Sheet: /UI_ENC/ENCODER_0/

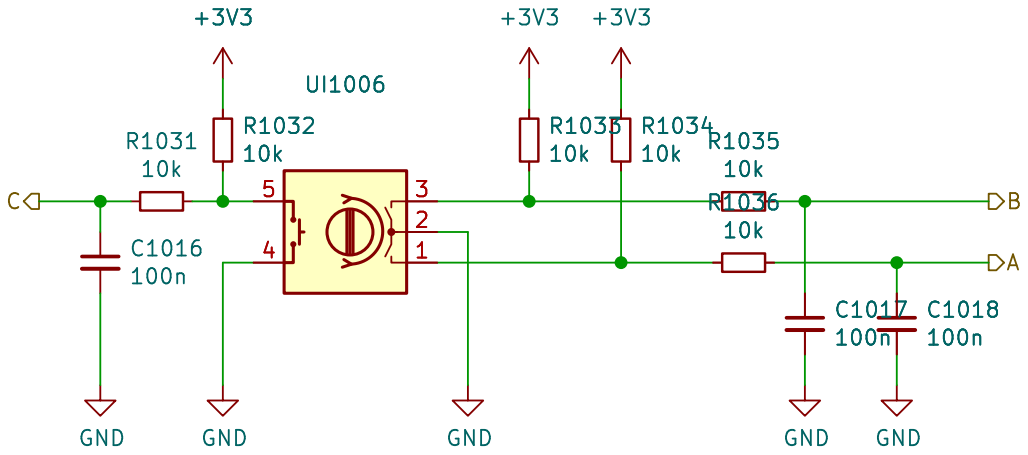
[picture p263: page 12]

Id: 12/23 Title: File: UI_ENC_FILTER.kicad_sch Sheet: /UI_ENC/ENCODER_6/

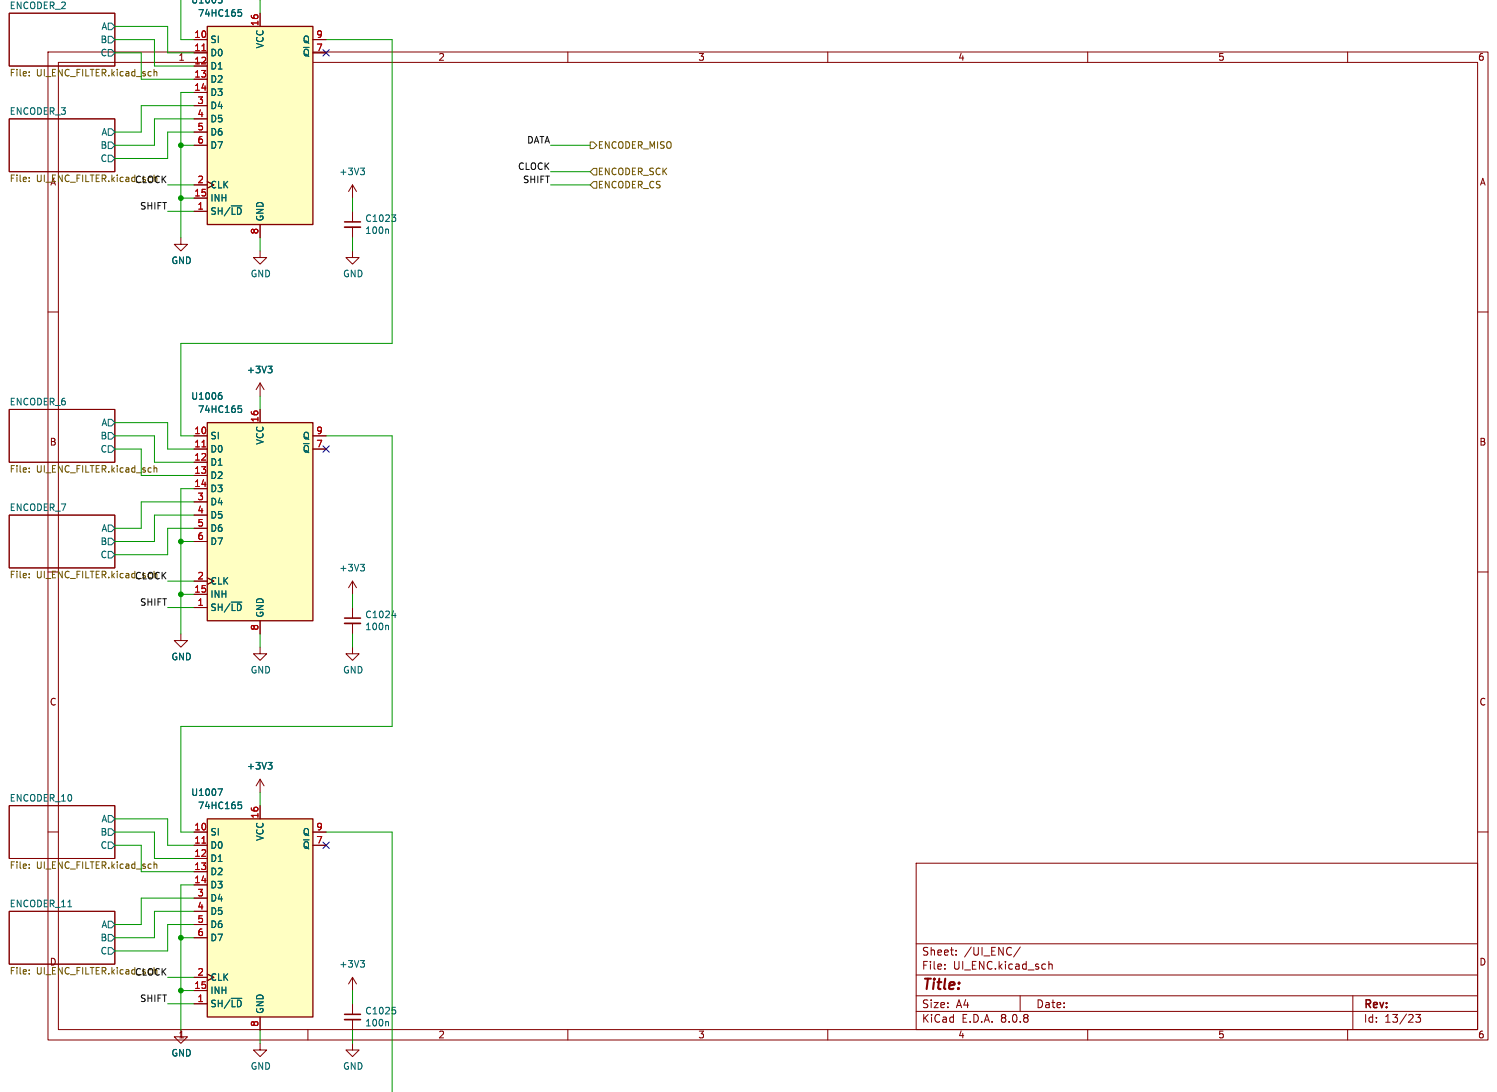
[picture p264: page 13]

Id: 13/23 Title: File: UI_ENC.kicad_sch Sheet: /UI_ENC/ CAB


Id: 14/23 Title: File: UI_ENC_FILTER.kicad_sch Sheet: /UI_ENC/ENCODER_3/


Id: 15/23 Title: File: UI_ENC_FILTER.kicad_sch Sheet: /UI_ENC/ENCODER_1/

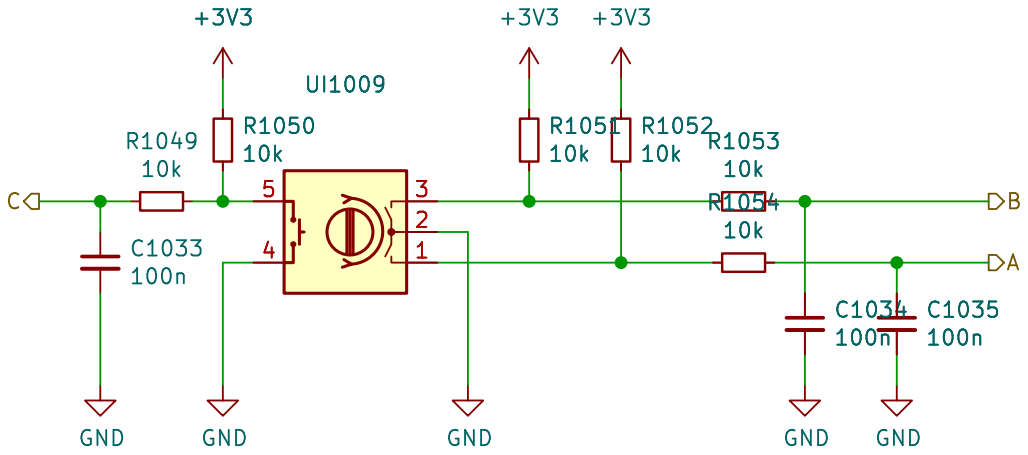
[picture p265: page 16]

Id: 16/23 Title: File: UI_ENC_FILTER.kicad_sch Sheet: /UI_ENC/ENCODER_7/

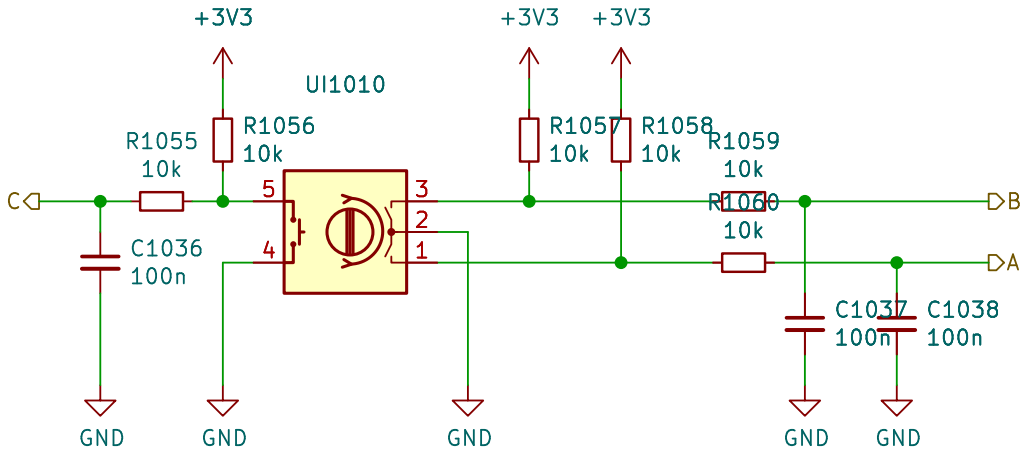
[picture p266: page 17]

Id: 17/23 Title: File: UI_ENC_FILTER.kicad_sch Sheet: /UI_ENC/ENCODER_14/

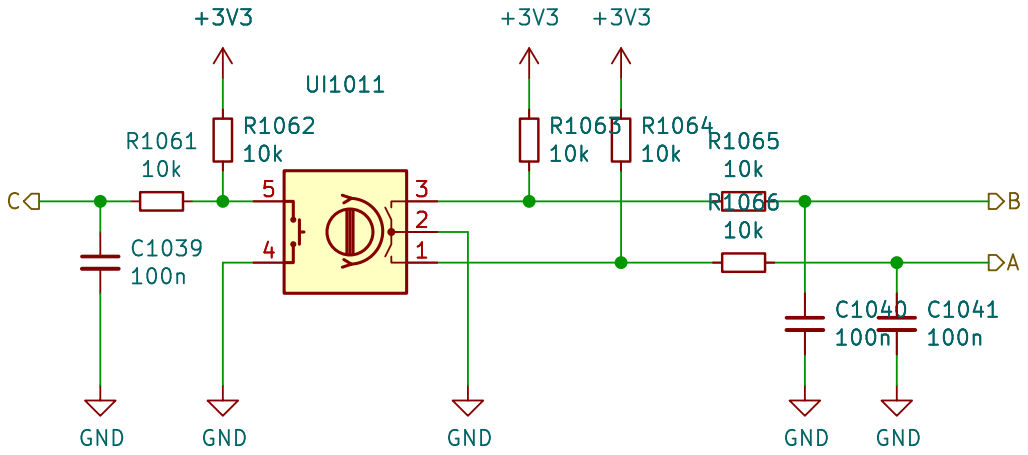
[picture p267: page 18]

Id: 18/23 Title: File: UI_ENC_FILTER.kicad_sch Sheet: /UI_ENC/ENCODER_13/

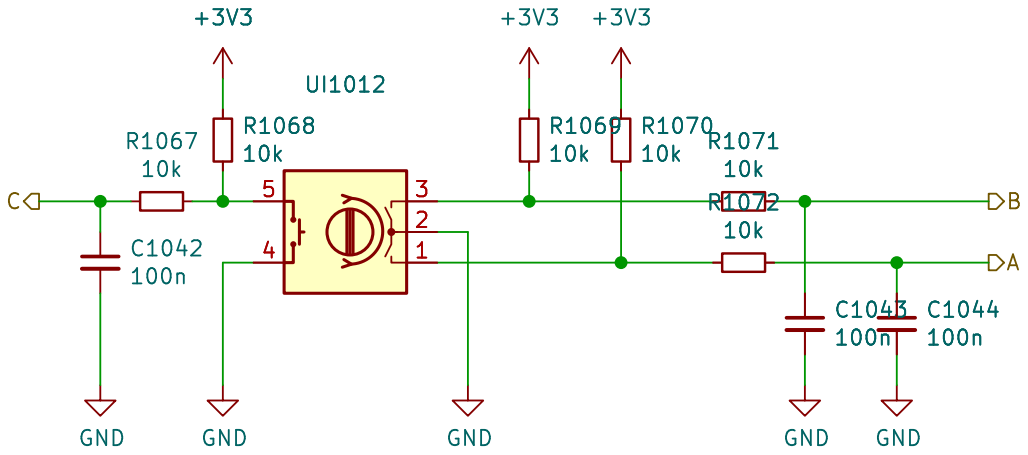
[picture p268: page 19]

Id: 19/23 Title: File: UI_ENC_FILTER.kicad_sch Sheet: /UI_ENC/ENCODER_10/

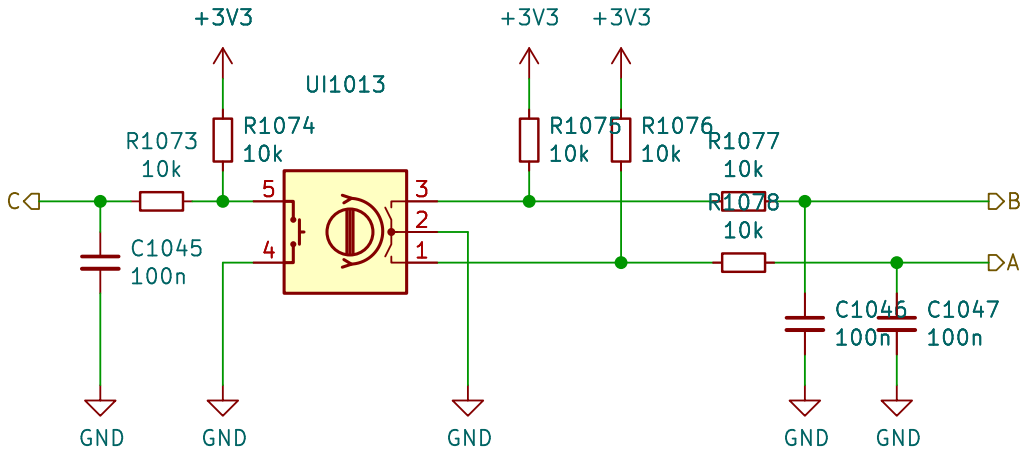
[picture p269: page 20]

Id: 20/23 Title: File: UI_ENC_FILTER.kicad_sch Sheet: /UI_ENC/ENCODER_15/


Id: 21/23 Title: File: UI_ENC_FILTER.kicad_sch Sheet: /UI_ENC/ENCODER_2/

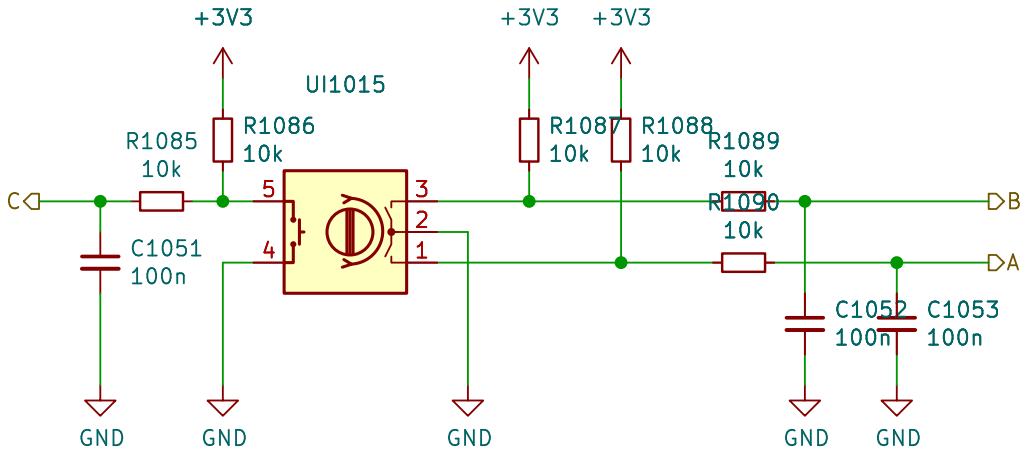
[picture p270: page 22]

Id: 22/23 Title: File: UI_ENC_FILTER.kicad_sch Sheet: /UI_ENC/ENCODER_4/

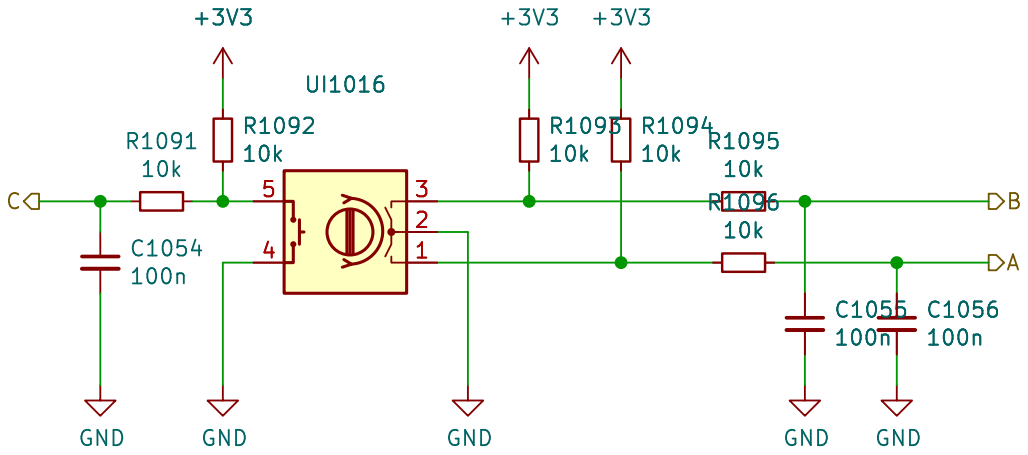
[picture p271: page 23]

Id: 23/23 Title: File: UI_ENC_FILTER.kicad_sch Sheet: /UI_ENC/ENCODER_9/
