intechstudio/grid/Preview/Electrical/PCBA-PBF4_Schematic.pdf

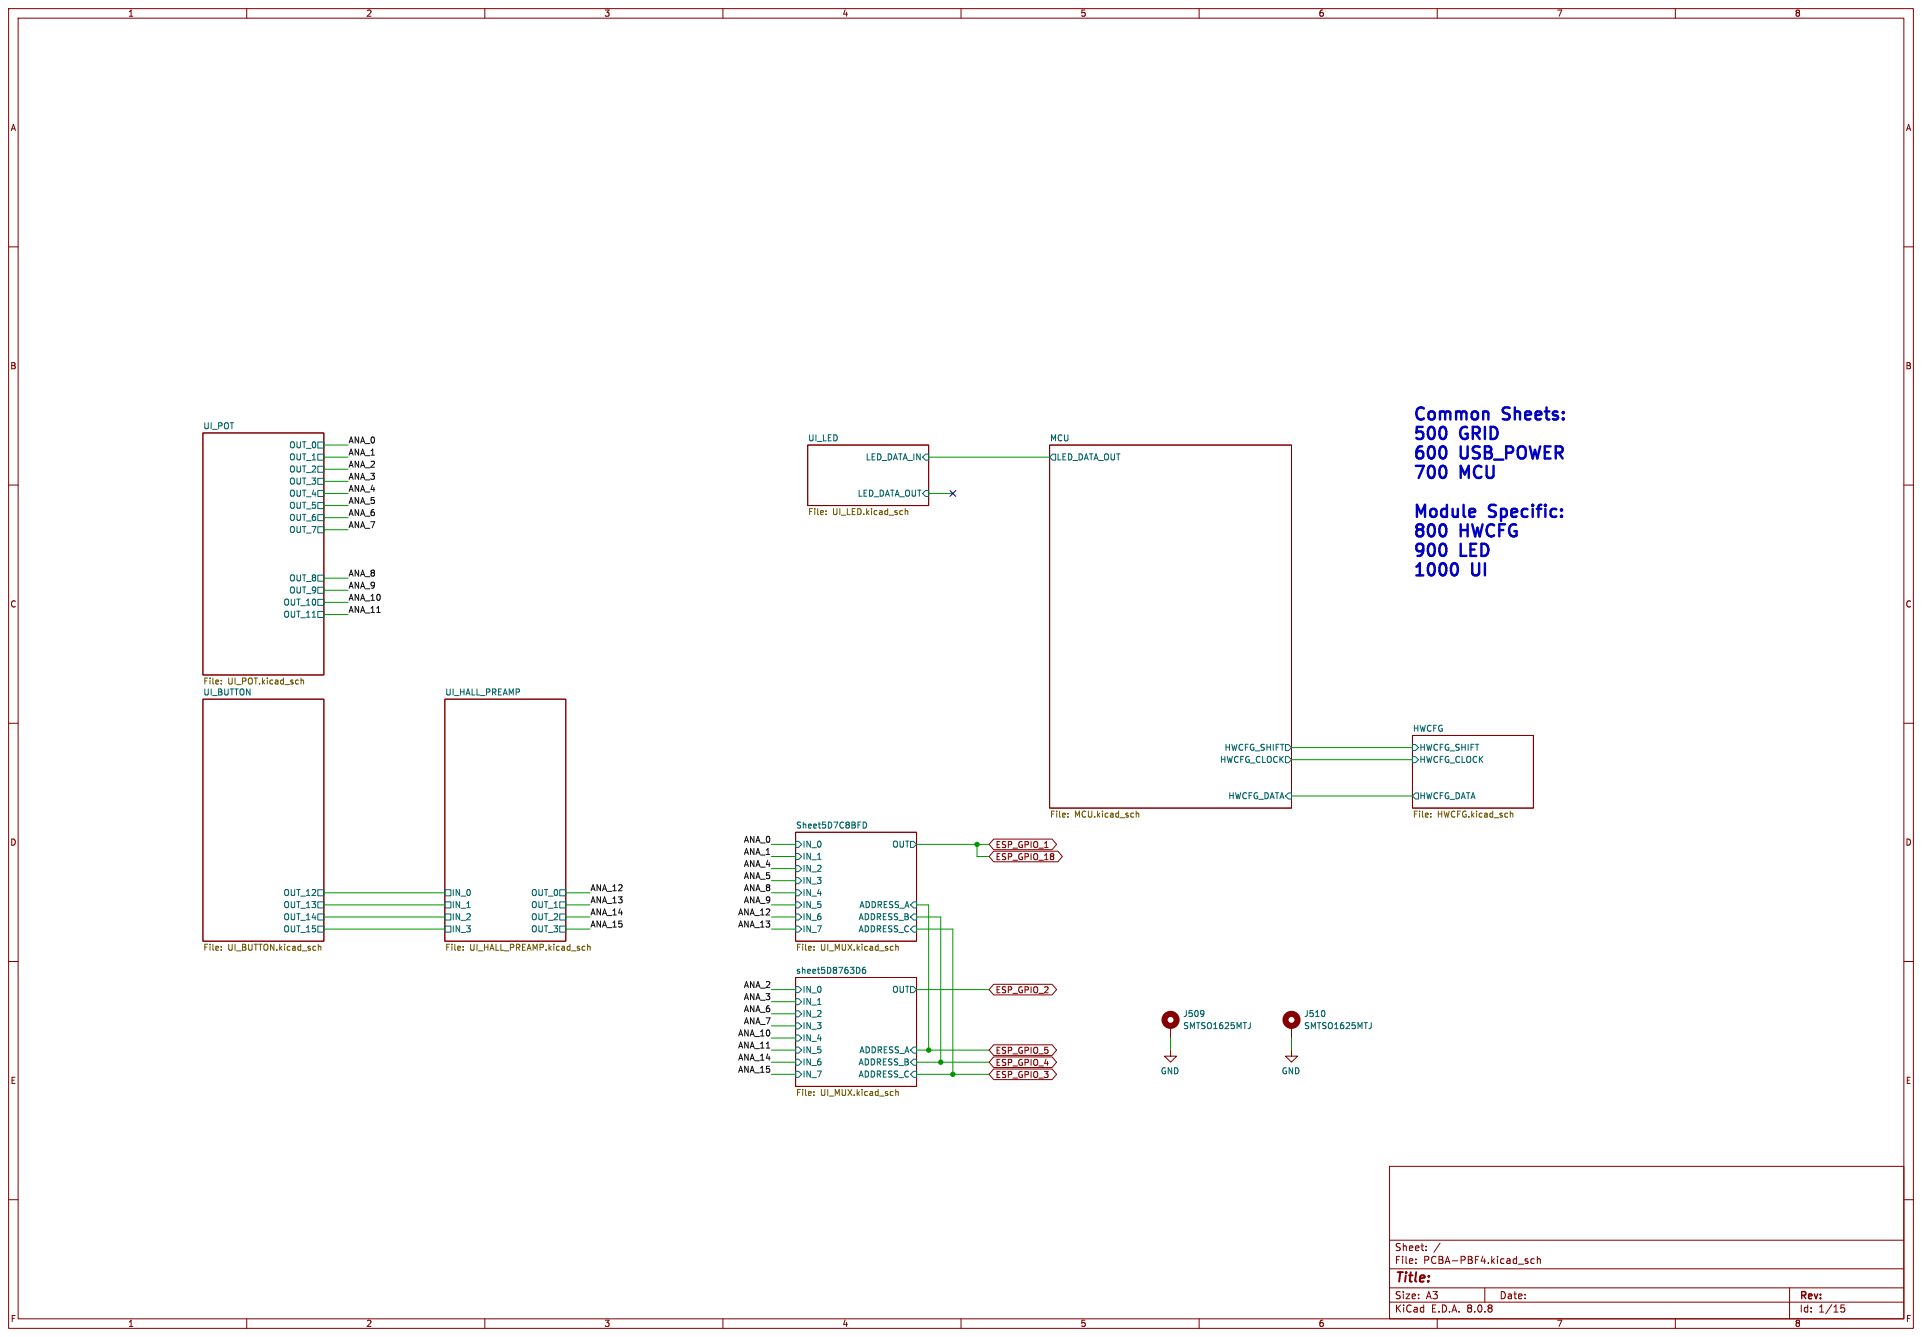
[picture p272: page 1]

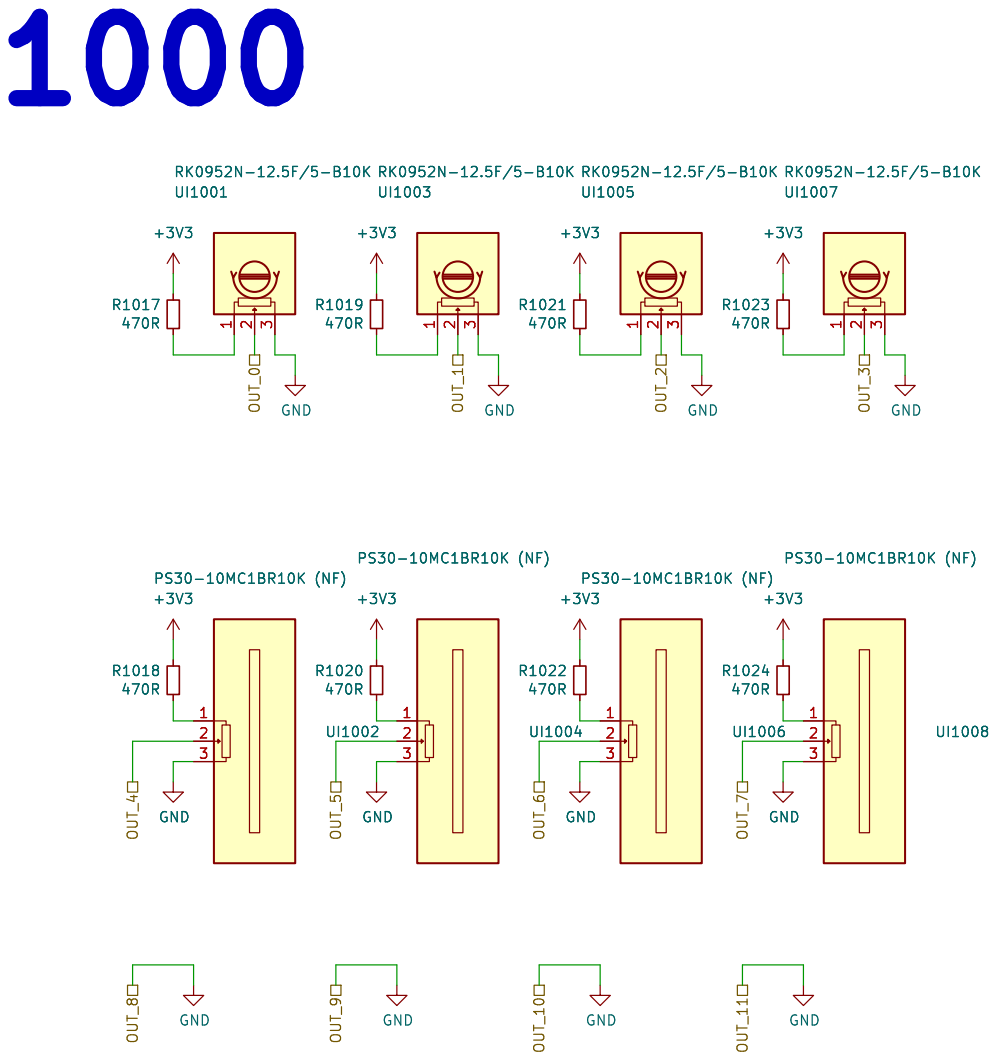
[picture p273: page 2]

Id: 2/15 Title: File: UI_POT.kicad_sch Sheet: /UI_POT/

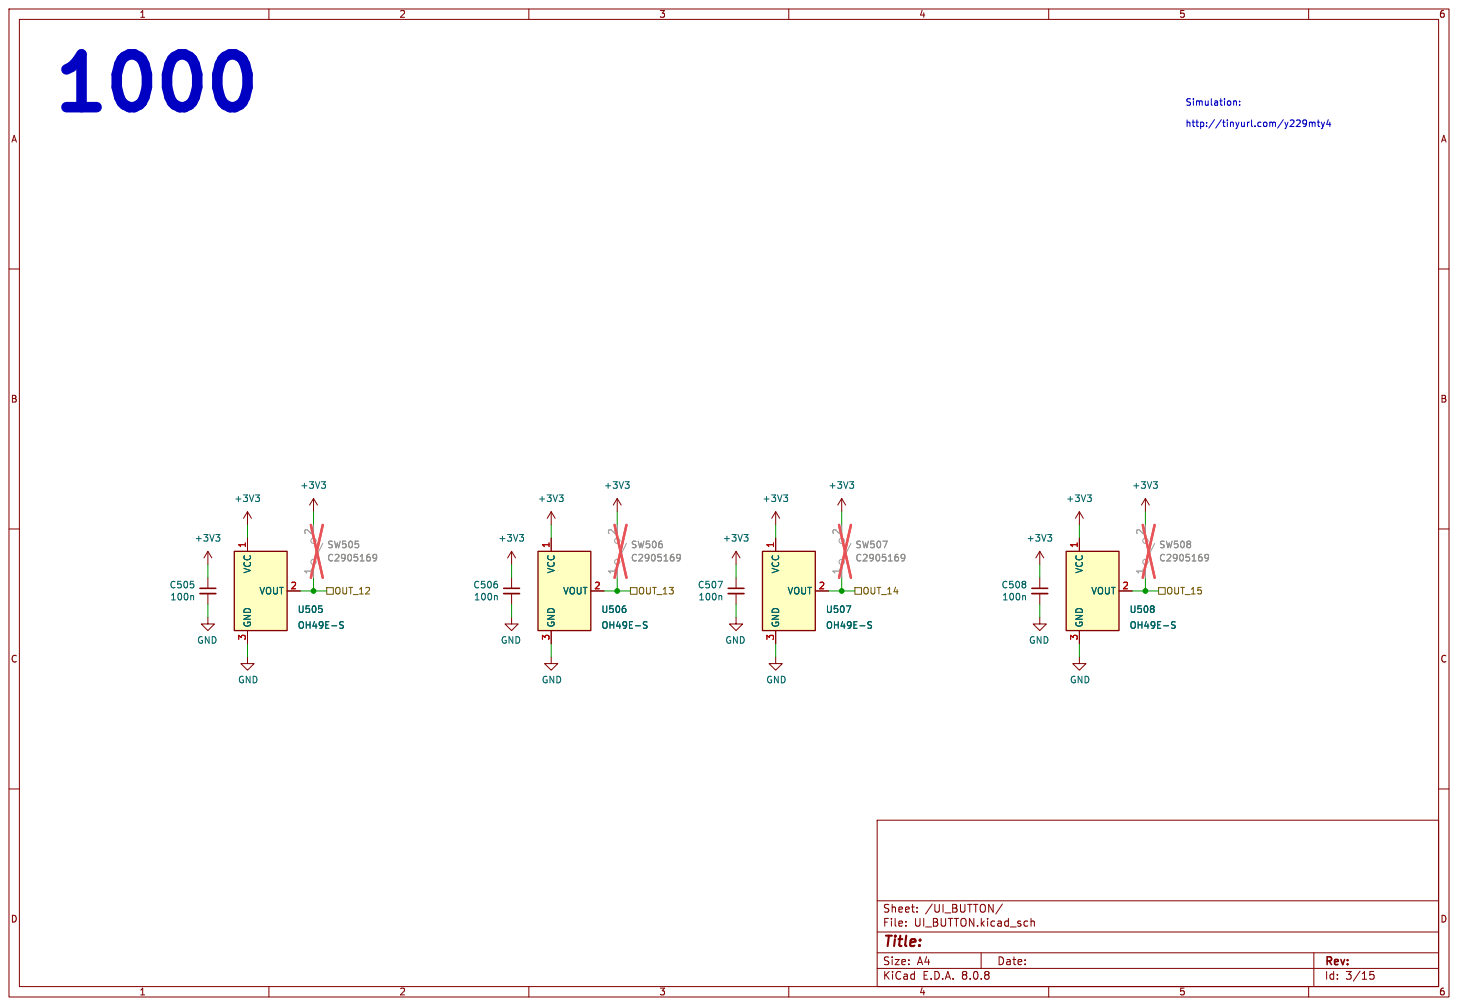
[picture p274: page 3]

Id: 3/15 Title: File: UI_BUTTON.kicad_sch Sheet: /UI_BUTTON/ C506

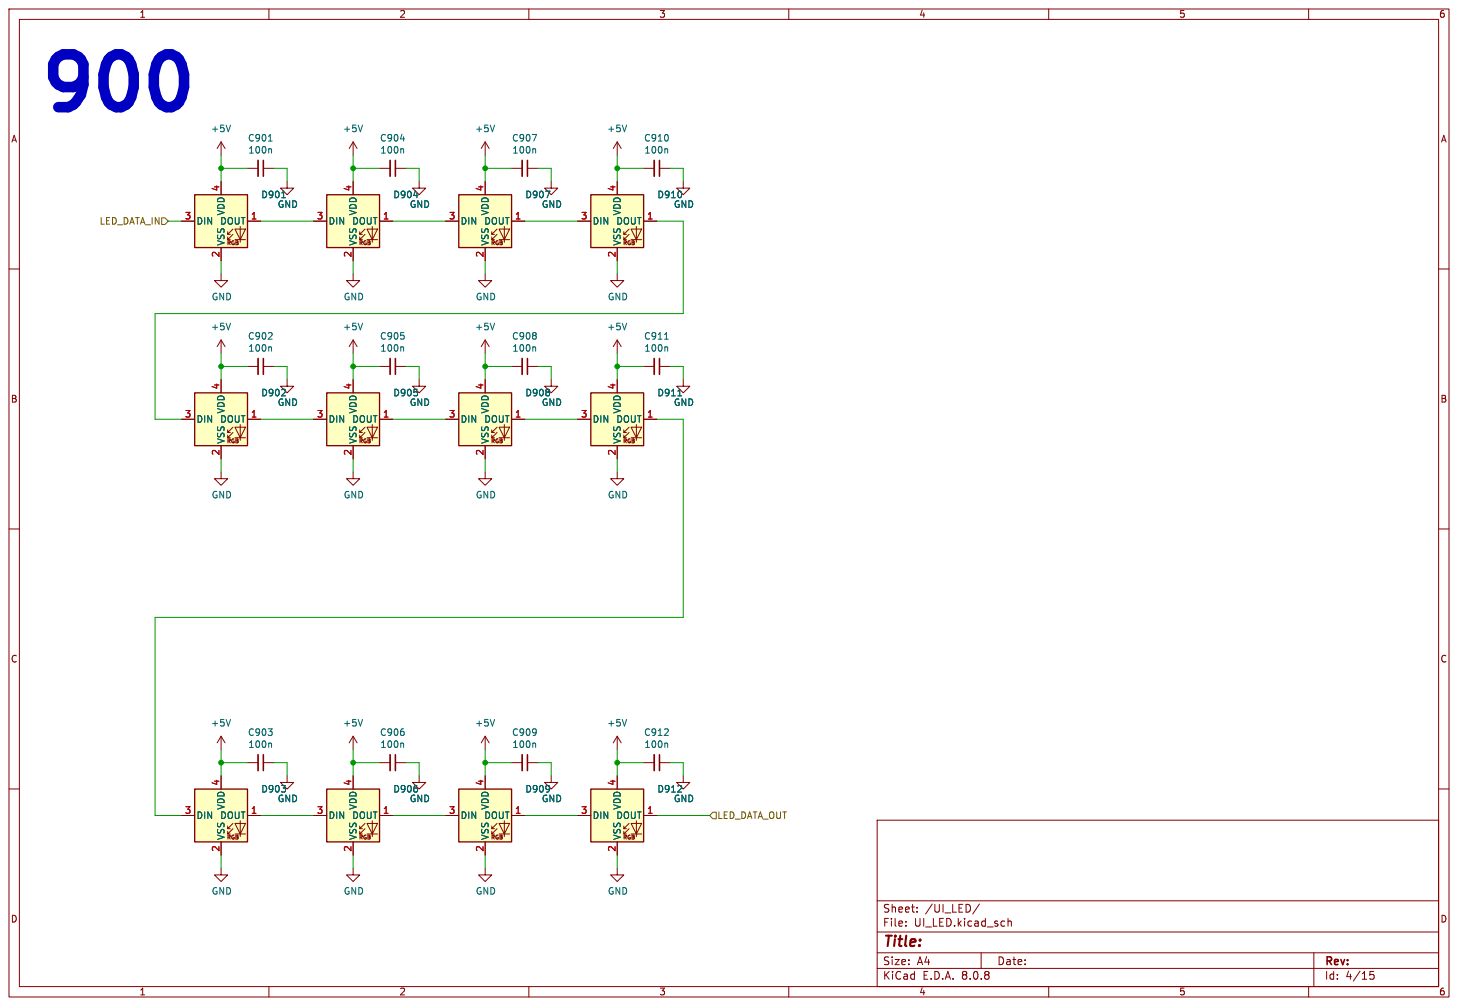
[picture p275: page 4]

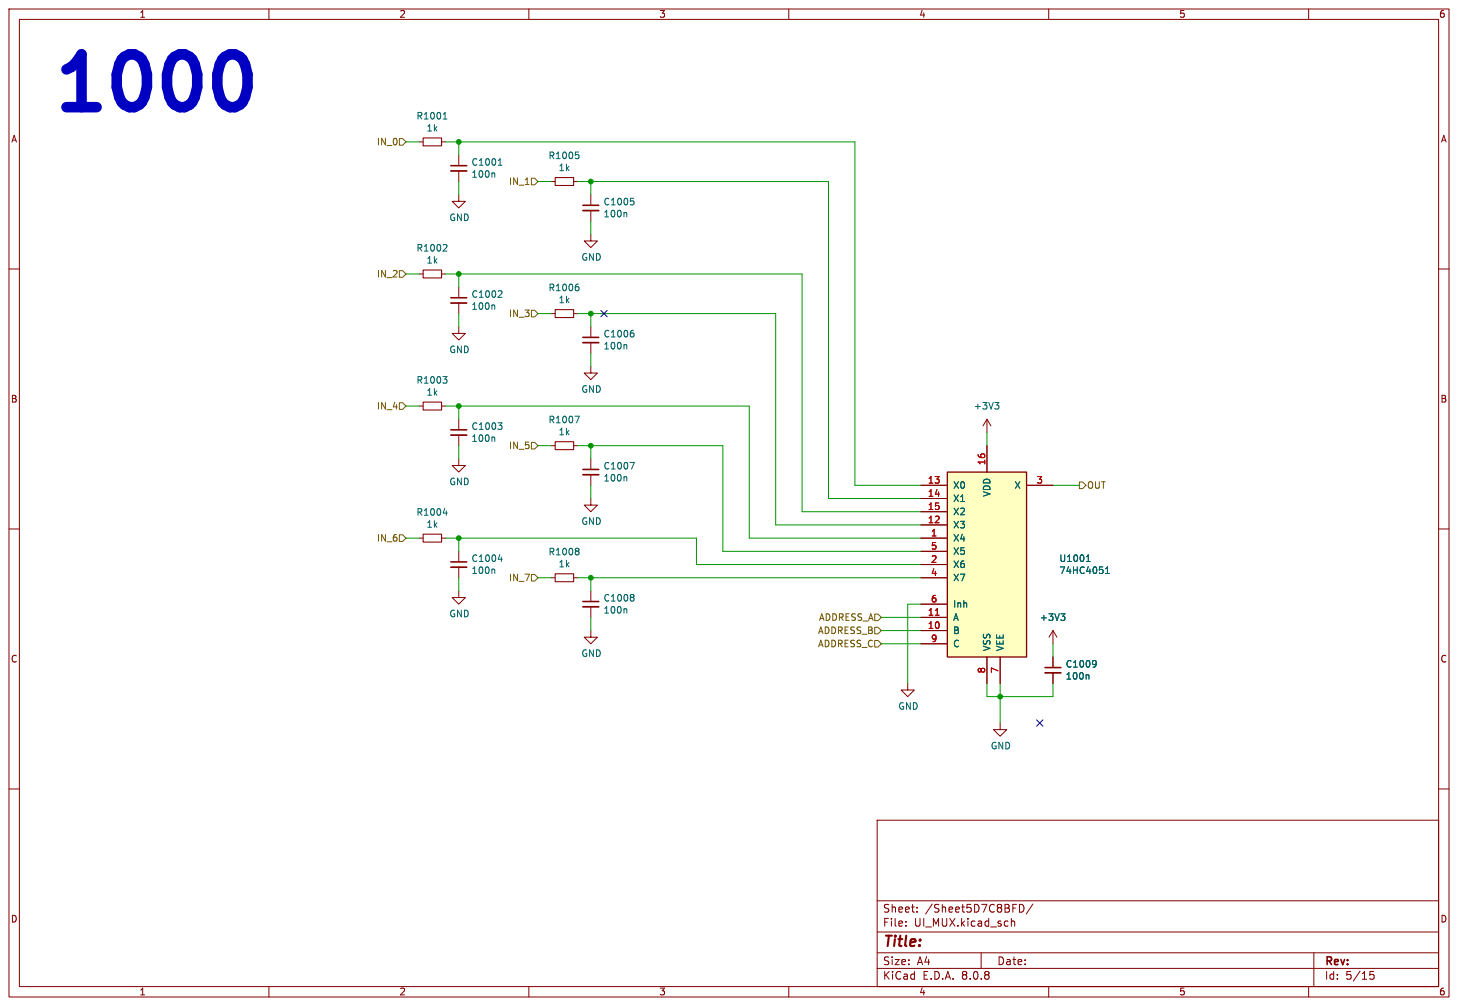
[picture p276: page 5]

Id: 5/15 Title: File: UI_MUX.kicad_sch Sheet: /Sheet5D7C8BFD/ R1004

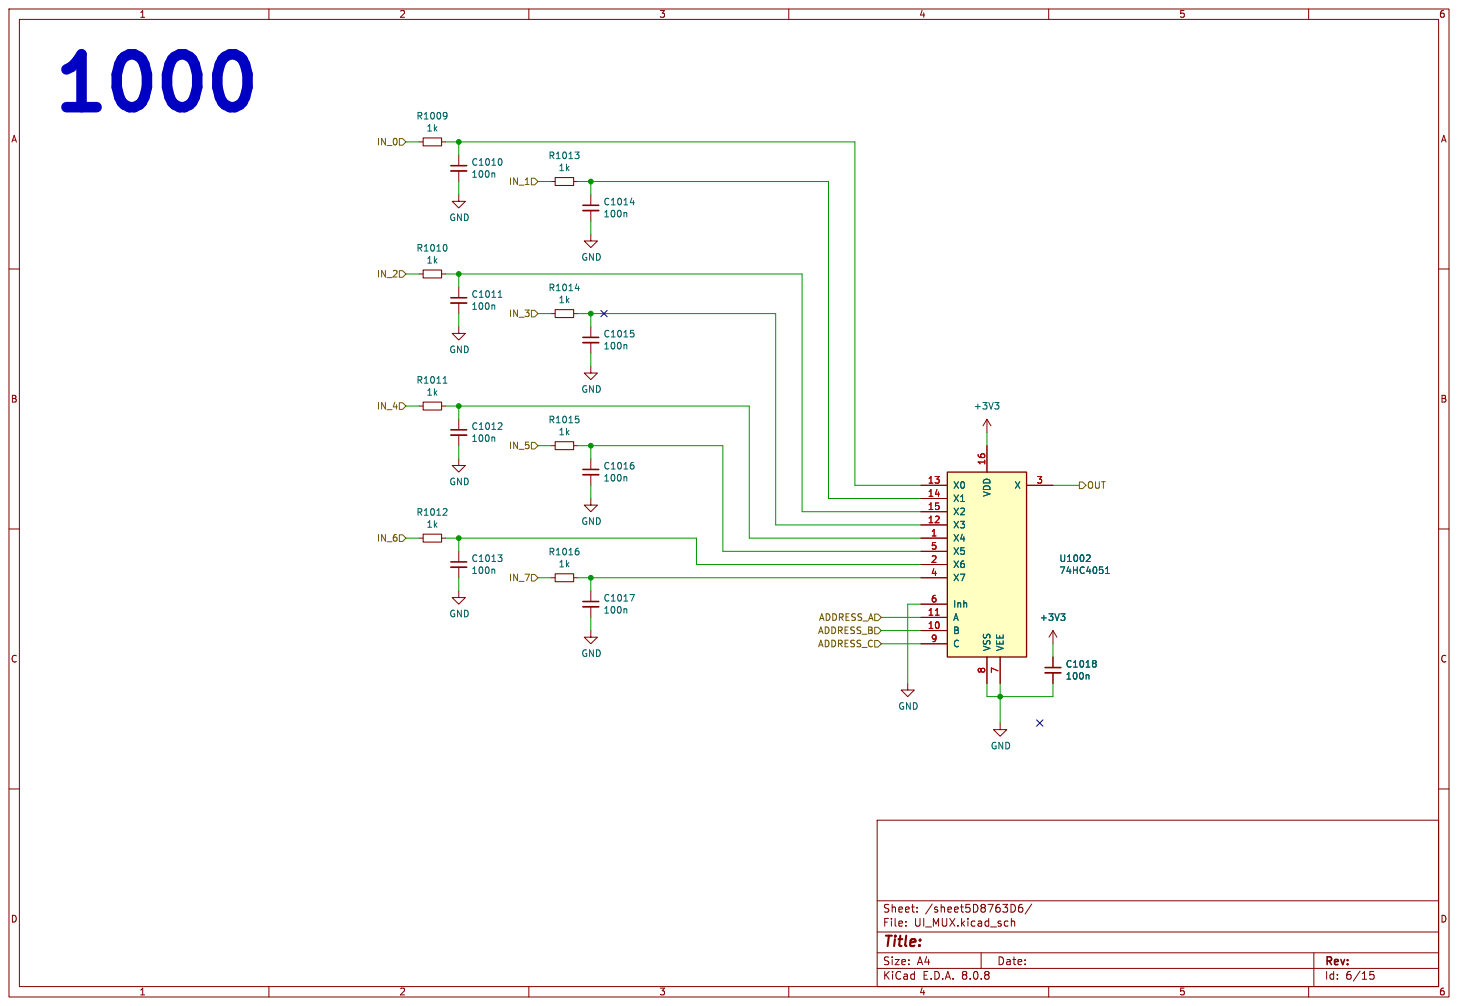
[picture p277: page 6]

Id: 6/15 Title: File: UI_MUX.kicad_sch Sheet: /sheet5D8763D6/ GND

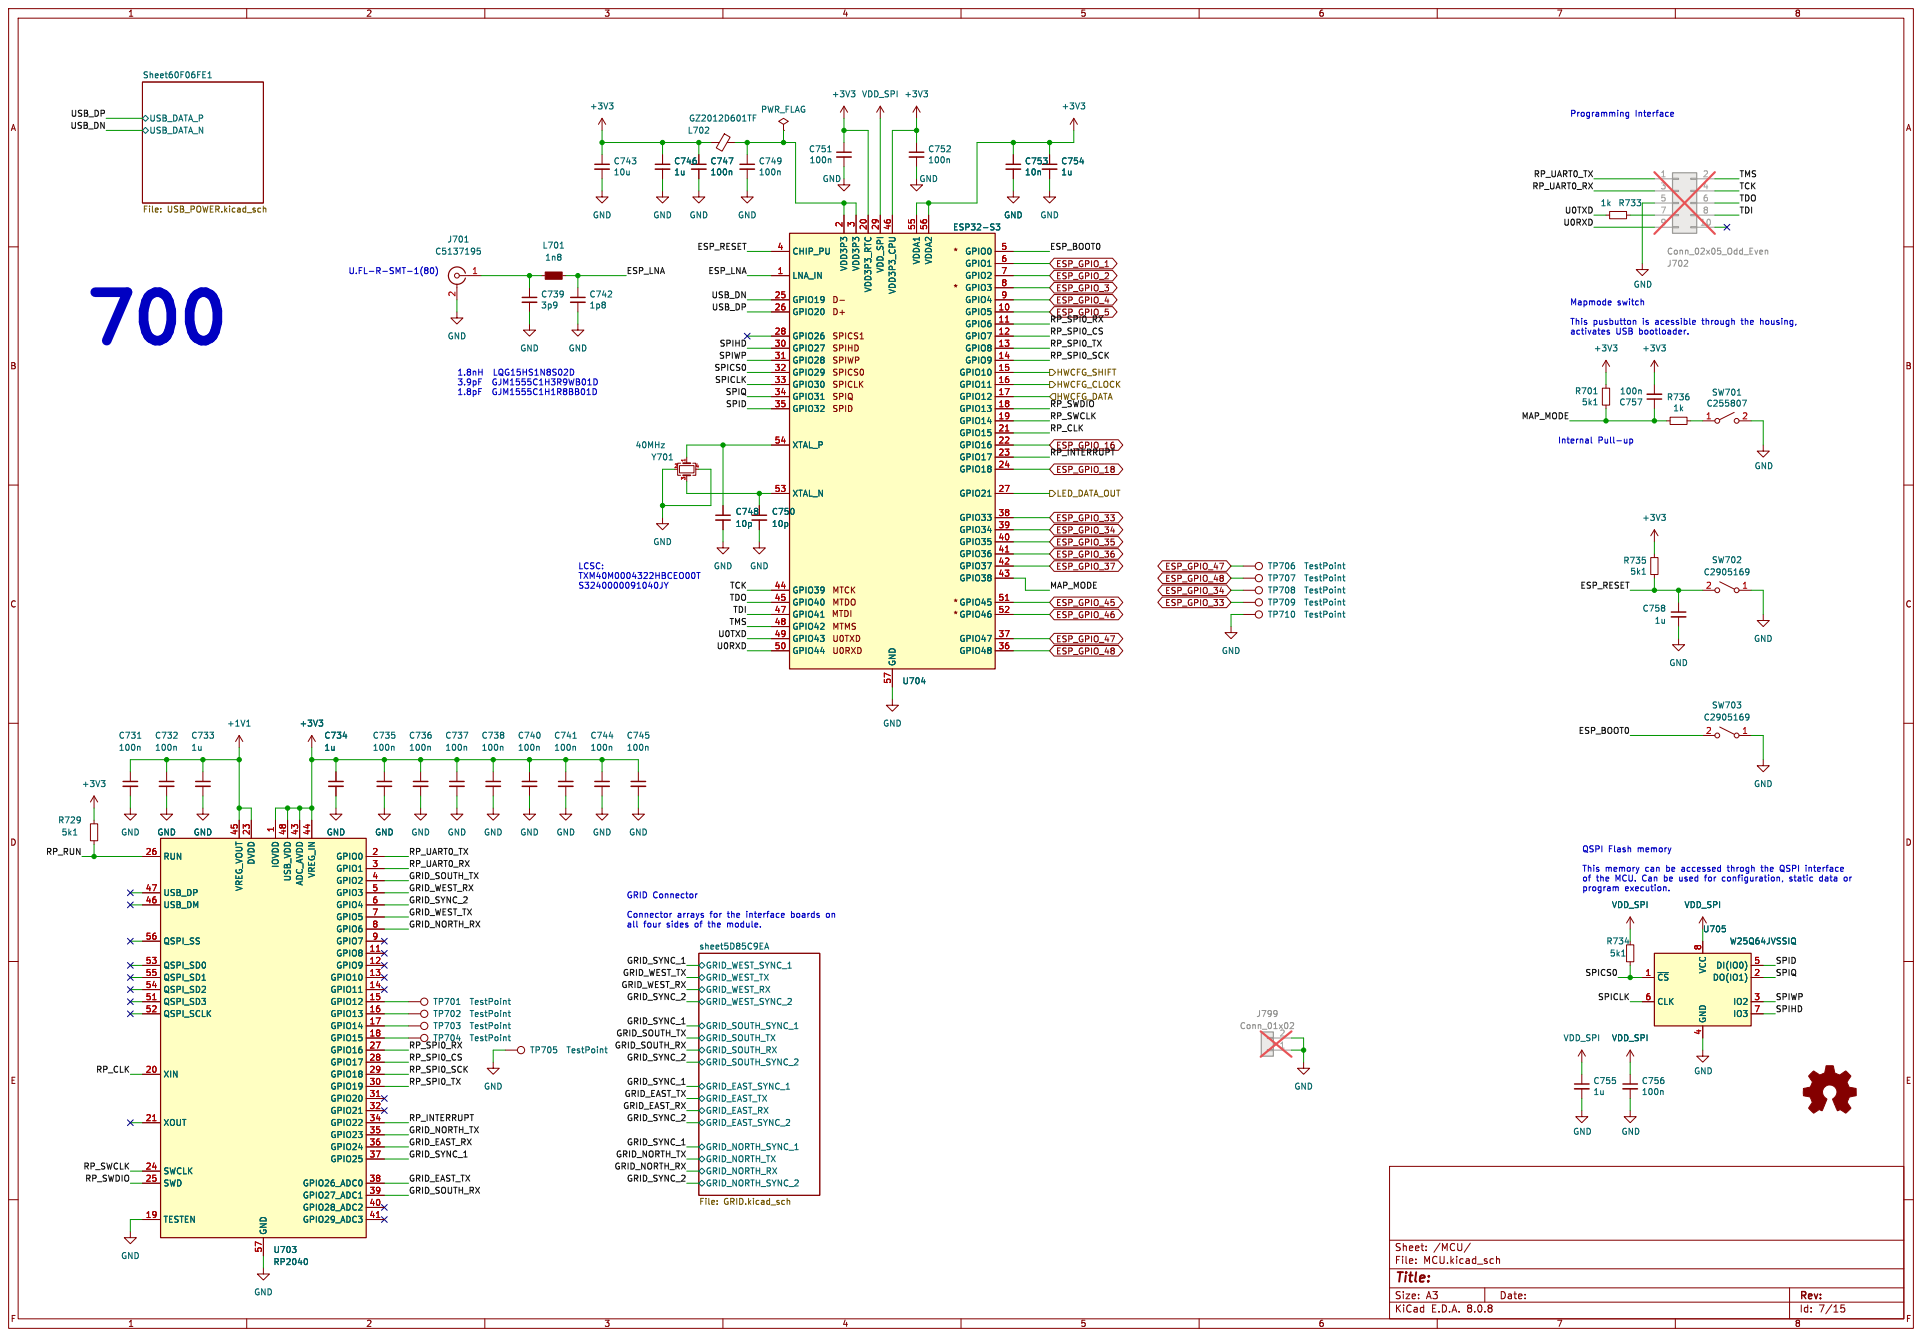
[picture p278: page 7]

1 GPIO8 11 GPIO9 12 GPIO10 13 GPIO11 14 GPIO12 15 GPIO13 16 GPIO14 17 GPIO15 18 TESTEN 19 GPIO0 2 XIN 20 XOUT 21 DVDD 23 SWCLK 24 SWD 25 RUN 26 GPIO16 27 GPIO17 28 GPIO18 29 GPIO1 3 GPIO19 30 GPIO20 31 GPIO21 32 GPIO22 34 GPIO23 35 GPIO24 36 GPIO25 37 GPIO26_ADC0 38 GPIO27_ADC1 39 GPIO2 4 GPIO28_ADC2 40 GPIO29_ADC3 41 ADC_AVDD 43 VREG_IN 44 VREG_VOUT 45 USB_DM 46 USB_DP 47 USB_VDD 48 GPIO3 5 QSPI_SD3 51 QSPI_SCLK 52 QSPI_SD0 53 QSPI_SD2 54 QSPI_SD1 55 QSPI_SS 56 GND 57 GPIO4 6 GPIO5 7 GPIO6 8 GPIO7 9 U703 RP2040 GND GND

1 GPIO8 11 GPIO9 12 GPIO10 13 GPIO11 14 GPIO12 15 GPIO13 16 GPIO14 17 GPIO15 18 TESTEN 19 GPIO0 2 XIN 20 XOUT 21 DVDD 23 SWCLK 24 SWD 25 RUN 26 GPIO16 27 GPIO17 28 GPIO18 29 GPIO1 3 GPIO19 30 GPIO20 31 GPIO21 32 GPIO22 34 GPIO23 35 GPIO24 36 GPIO25 37 GPIO26_ADC0 38 GPIO27_ADC1 39 GPIO2 4 GPIO28_ADC2 40 GPIO29_ADC3 41 ADC_AVDD 43 VREG_IN 44 VREG_VOUT 45 USB_DM 46 USB_DP 47 USB_VDD 48 GPIO3 5 QSPI_SD3 51 QSPI_SCLK 52 QSPI_SD0 53 QSPI_SD2 54 QSPI_SD1 55 QSPI_SS 56 GND 57 GPIO4 6 GPIO5 7 GPIO6 8 GPIO7 9 GND GND

all four sides of the module.
GRID_WEST_SYNC_1 GRID_WEST_TX GRID_WEST_RX GRID_WEST_SYNC_2 GRID_EAST_SYNC_1 GRID_EAST_TX GRID_EAST_RX GRID_EAST_SYNC_2 GRID_NORTH_SYNC_1 GRID_NORTH_TX GRID_NORTH_RX GRID_NORTH_SYNC_2 GRID_SOUTH_SYNC_1 GRID_SOUTH_TX GRID_SOUTH_RX GRID_SOUTH_SYNC_2

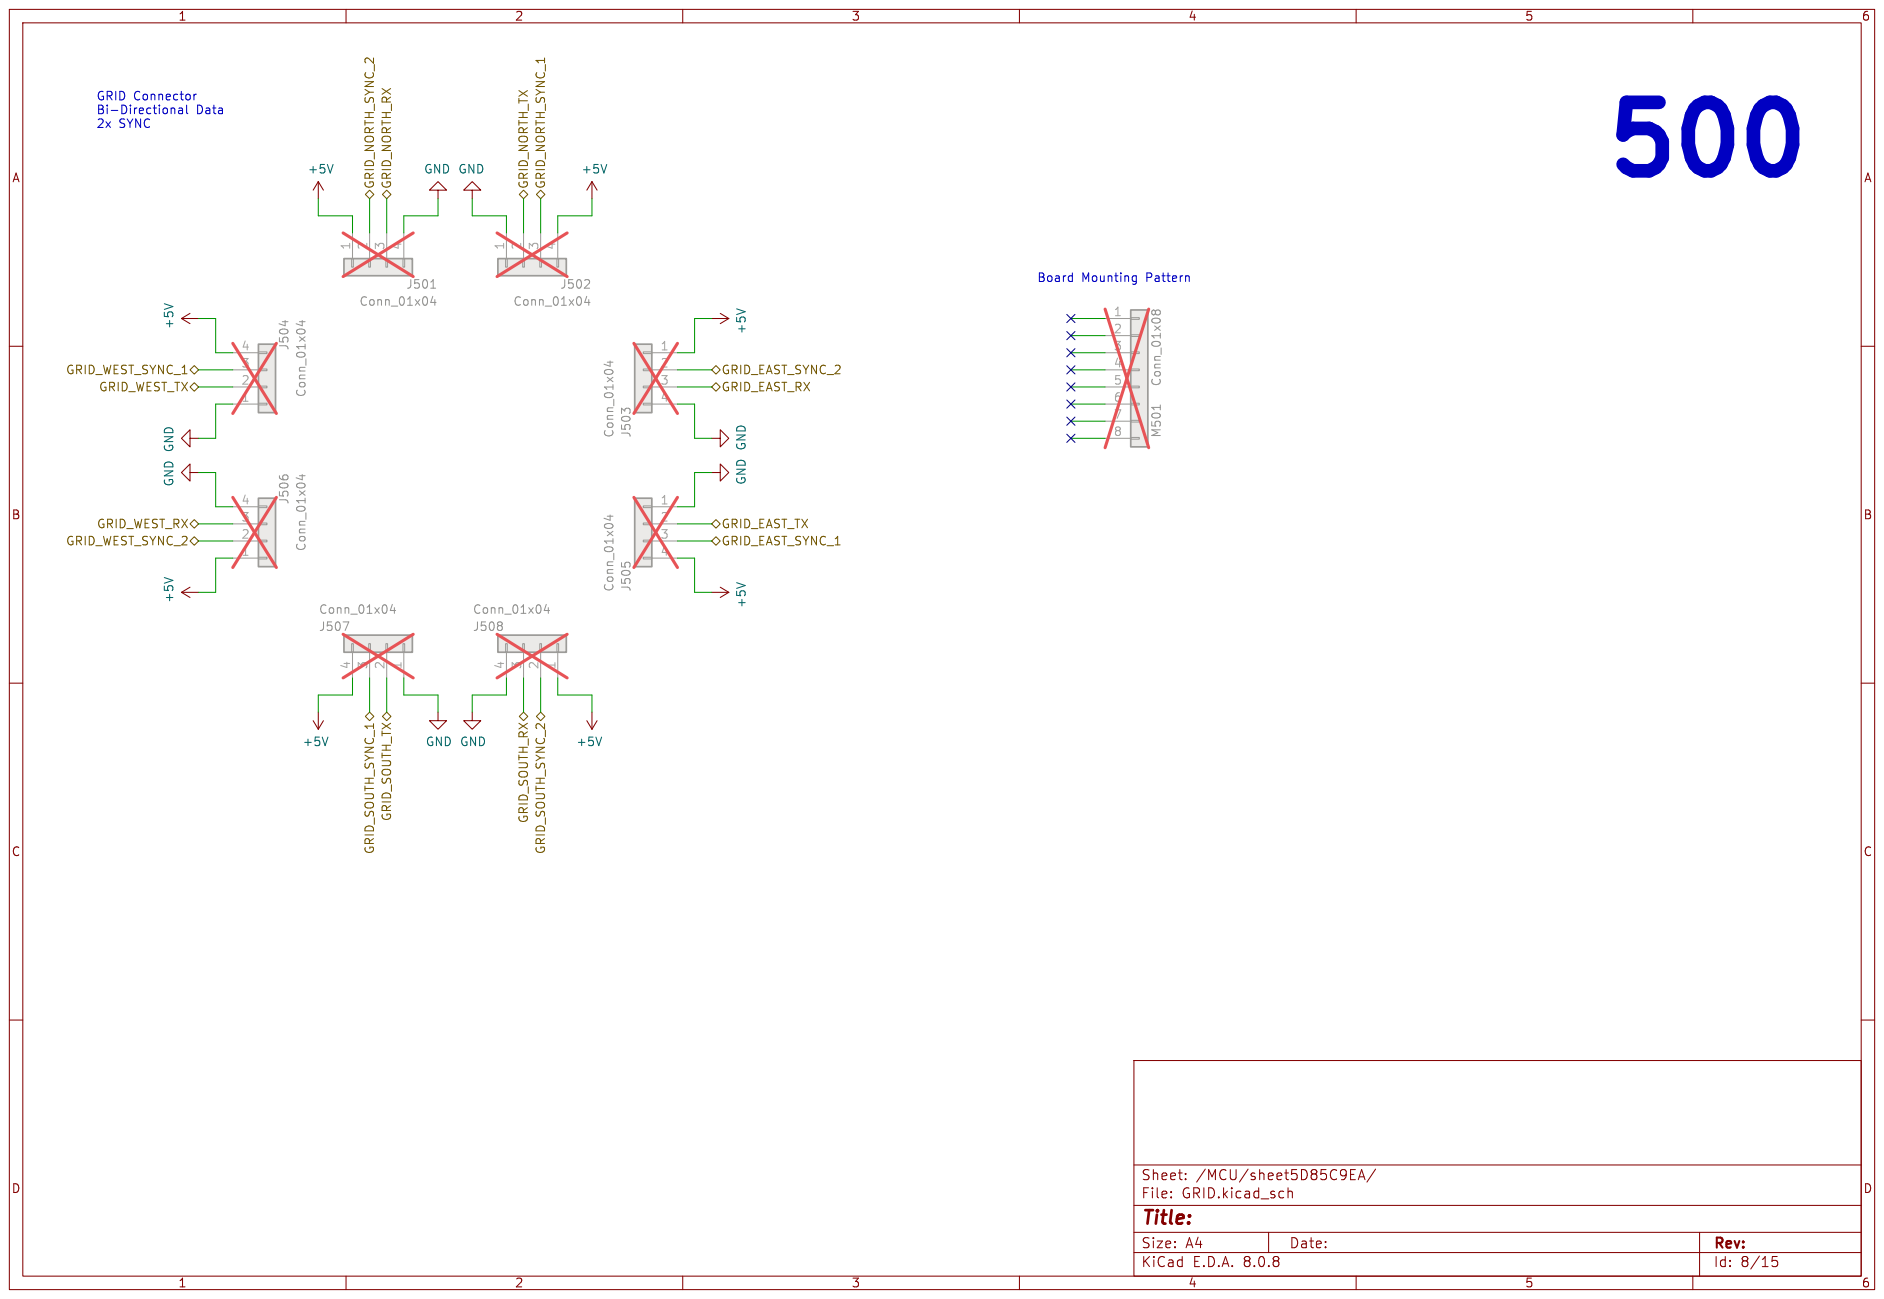
[picture p279: page 8]

4 J501 Conn_01x04 GRID_WEST_TX GRID_EAST_SYNC_1 GRID_EAST_SYNC_2 GRID_EAST_RX GRID_EAST_TX GRID_SOUTH_SYNC_1 GRID_SOUTH_SYNC_2 GRID_SOUTH_TX GRID_SOUTH_RX GRID_WEST_SYNC_1 GRID_WEST_RX GRID_WEST_SYNC_2 GRID_NORTH_SYNC_2 GRID_NORTH_RX GRID_NORTH_TX GRID_NORTH_SYNC_1 Board Mounting Pattern GRID Connector Bi-Directional Data

Id: 8/15 Title: File: GRID.kicad_sch Sheet: /MCU/sheet5D85C9EA/

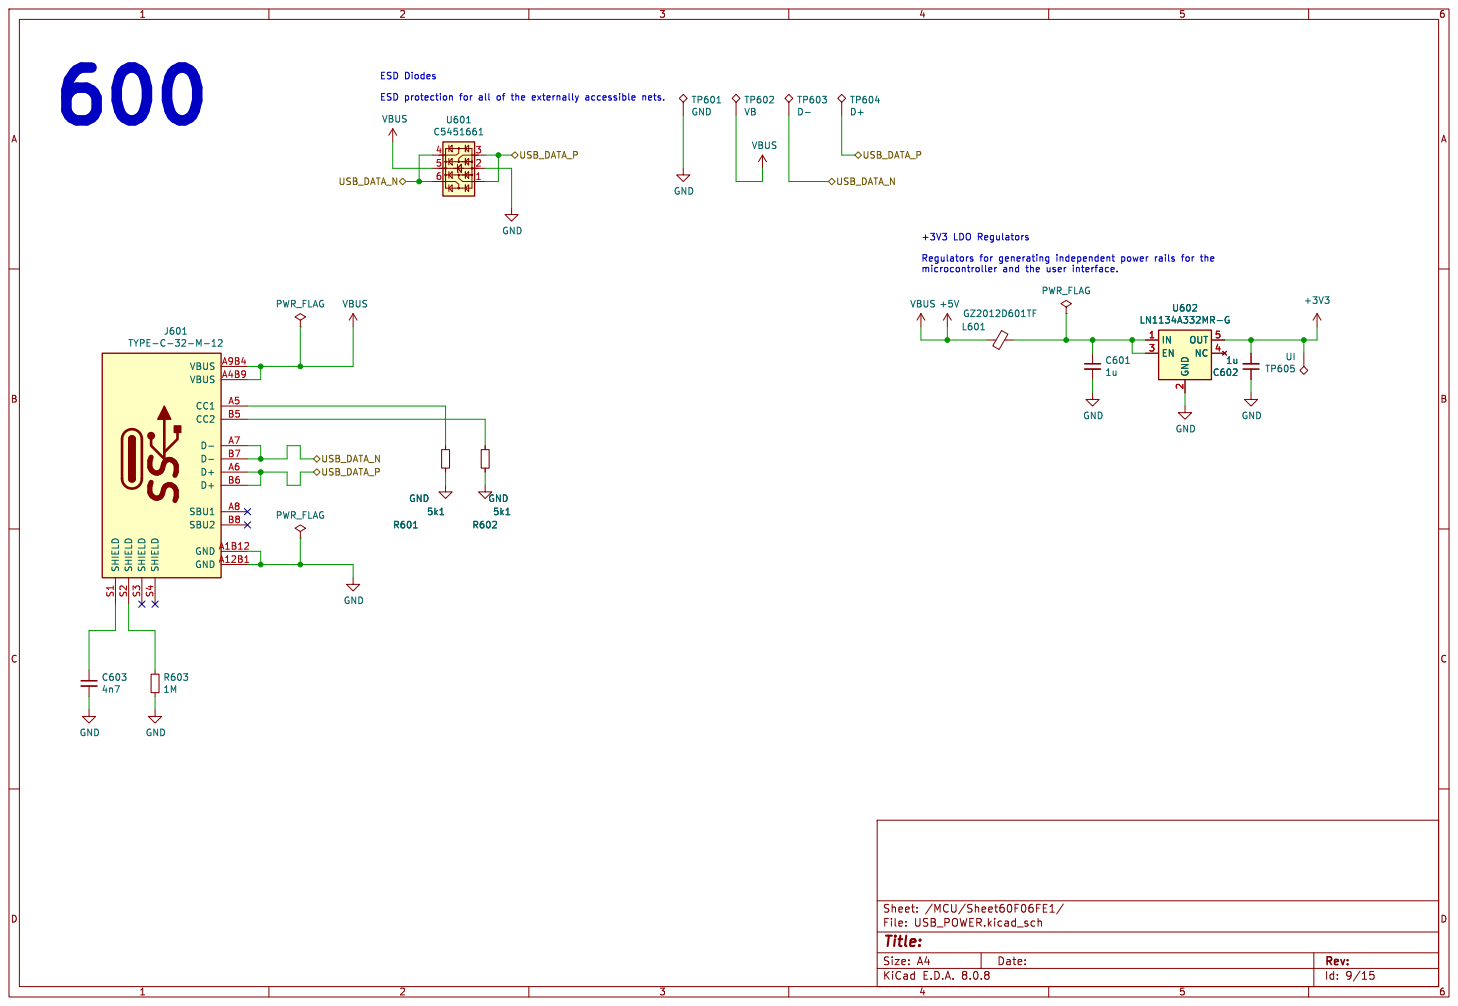
[picture p280: page 9]

Id: 9/15 Title: File: USB_POWER.kicad_sch Sheet: /MCU/Sheet60F06FE1/

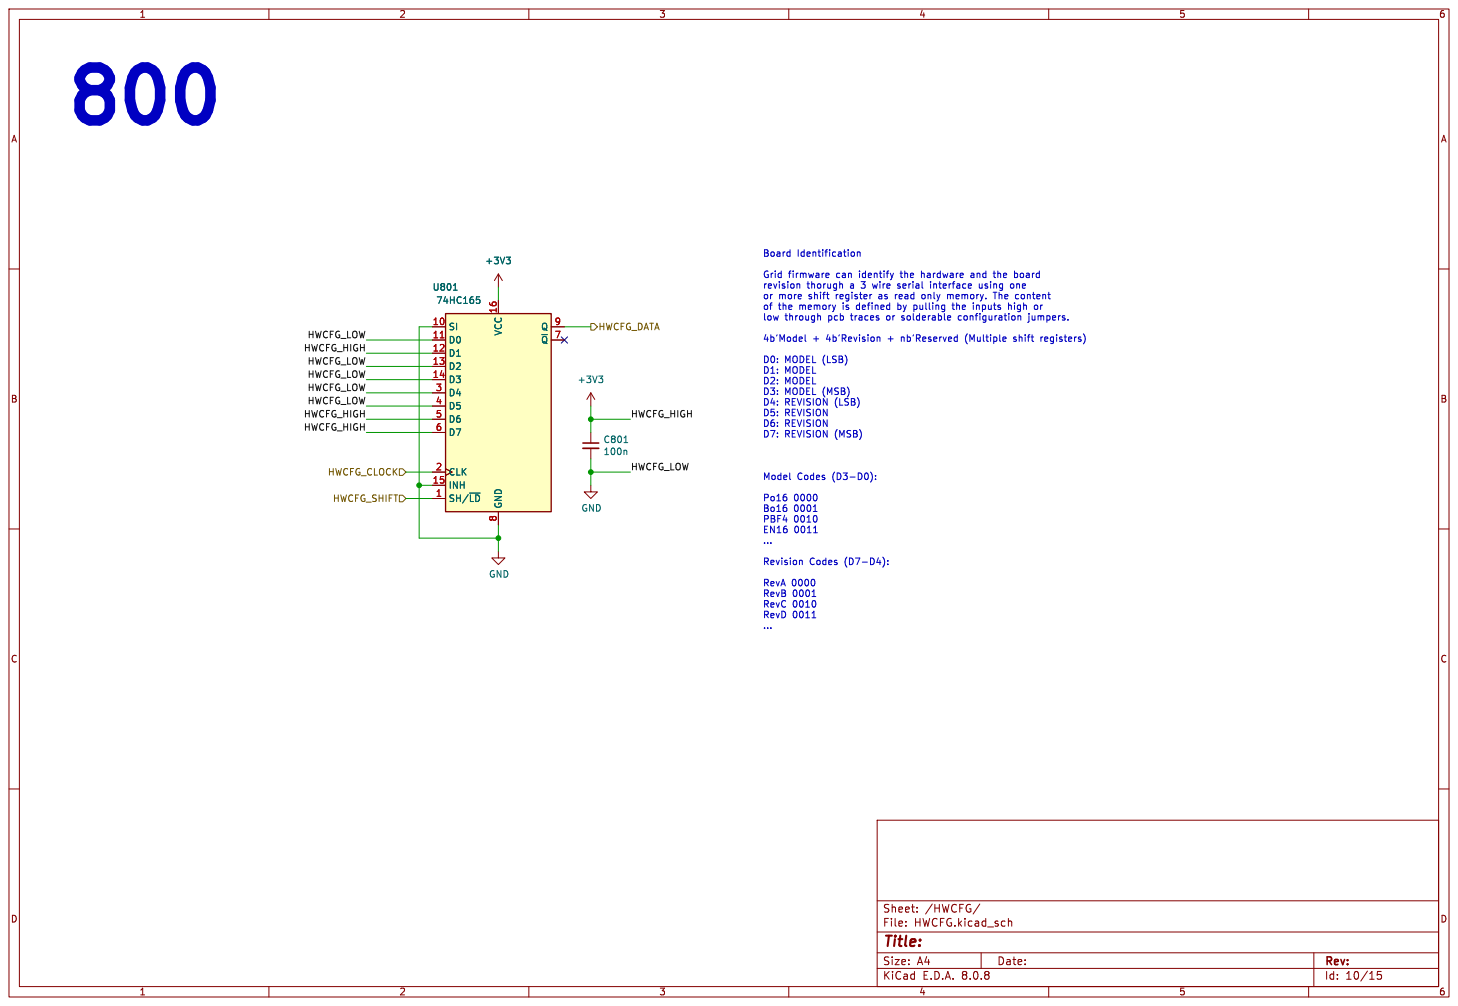
[picture p281: page 10]

D6: REVISION
D7: REVISION (MSB) Model Codes (D3-D0): Po16 0000 Bo16 0001 PBF4 0010 EN16 0011

... Revision Codes (D7-D4): RevA 0000 RevB 0001 RevC 0010 RevD 0011

Id: 10/15 Title: File: HWCFG.kicad_sch Sheet: /HWCFG/

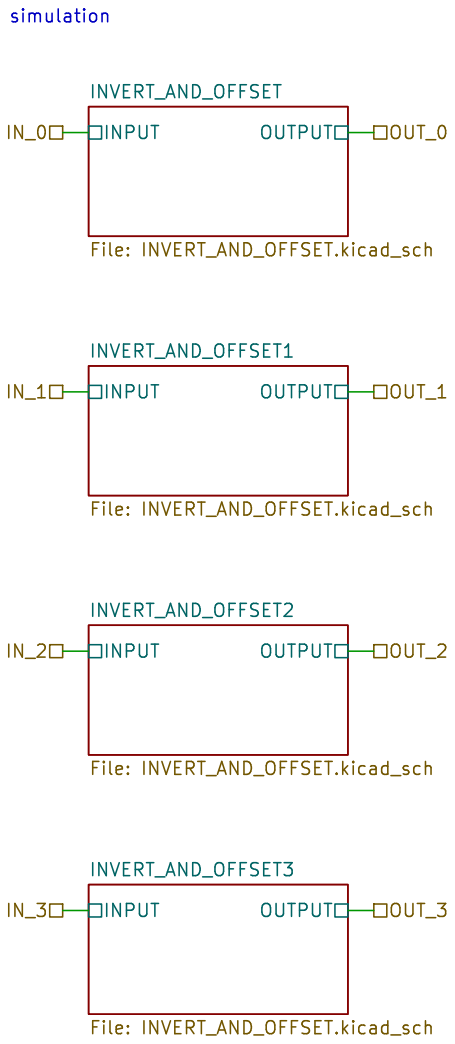
[picture p282: page 11]

Id: 11/15 Title: File: UI_HALL_PREAMP.kicad_sch Sheet: /UI_HALL_PREAMP/

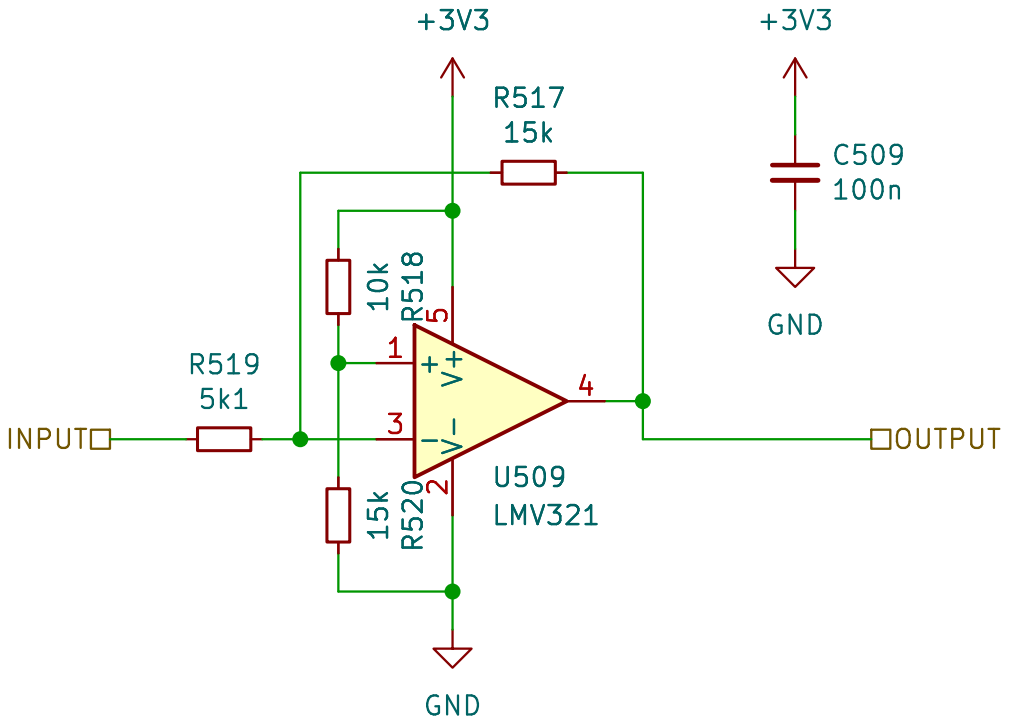
[picture p283: page 12]

Id: 16/15 Title: File: INVERT_AND_OFFSET.kicad_sch Sheet: /UI_HALL_PREAMP/INVERT_AND_OFFSET/

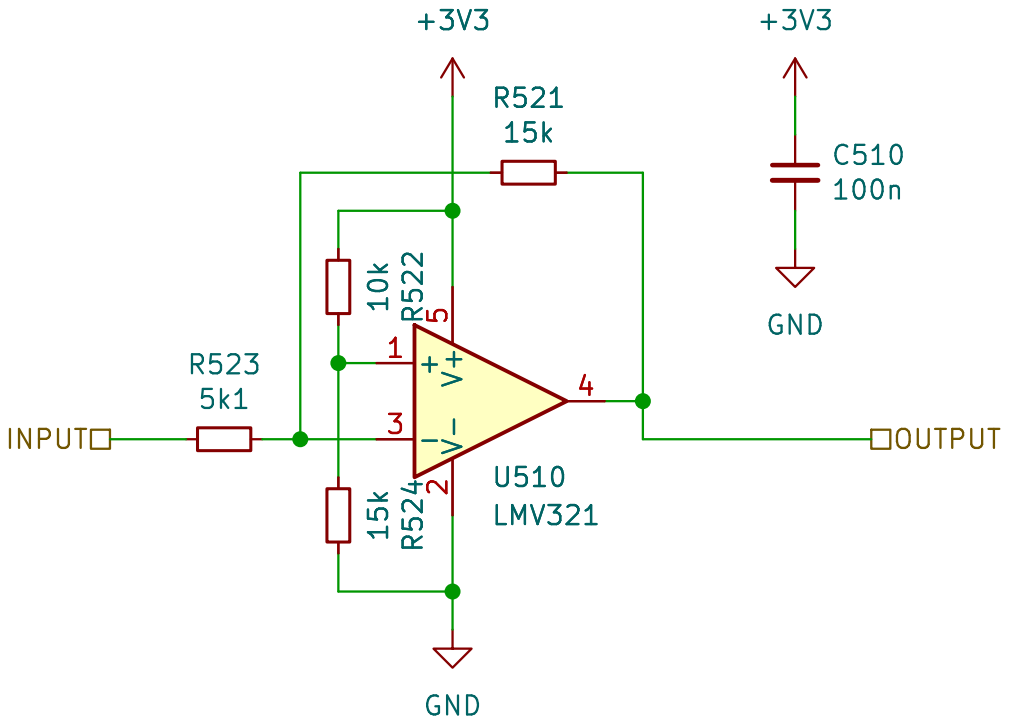
[picture p284: page 13]

Id: 17/15 Title: File: INVERT_AND_OFFSET.kicad_sch Sheet: /UI_HALL_PREAMP/INVERT_AND_OFFSET1/

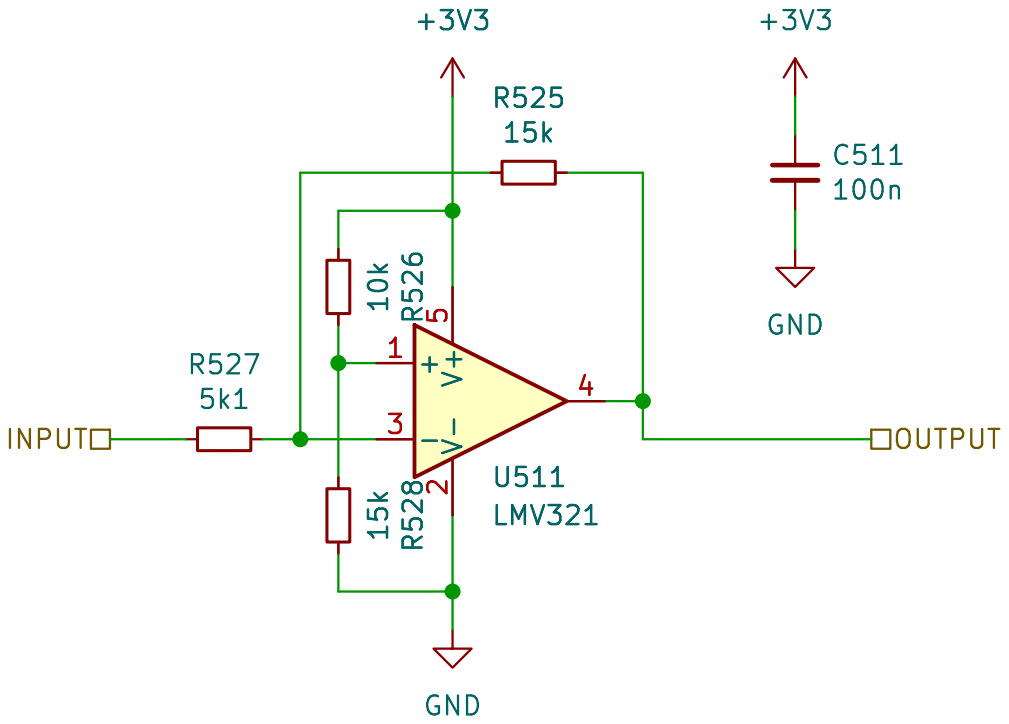
[picture p285: page 14]

Id: 18/15 Title: File: INVERT_AND_OFFSET.kicad_sch Sheet: /UI_HALL_PREAMP/INVERT_AND_OFFSET2/

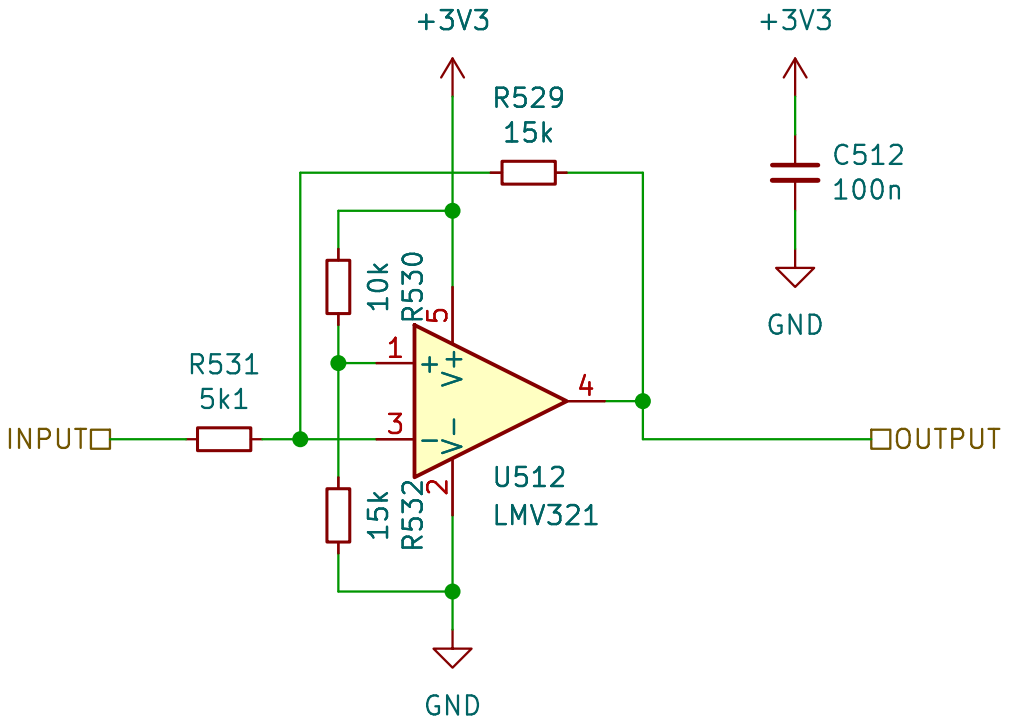
[picture p286: page 15]

Id: 19/15 Title: File: INVERT_AND_OFFSET.kicad_sch Sheet: /UI_HALL_PREAMP/INVERT_AND_OFFSET3/
