intechstudio/grid/Preview/Electrical/PCBA-VSNX_Schematic.pdf

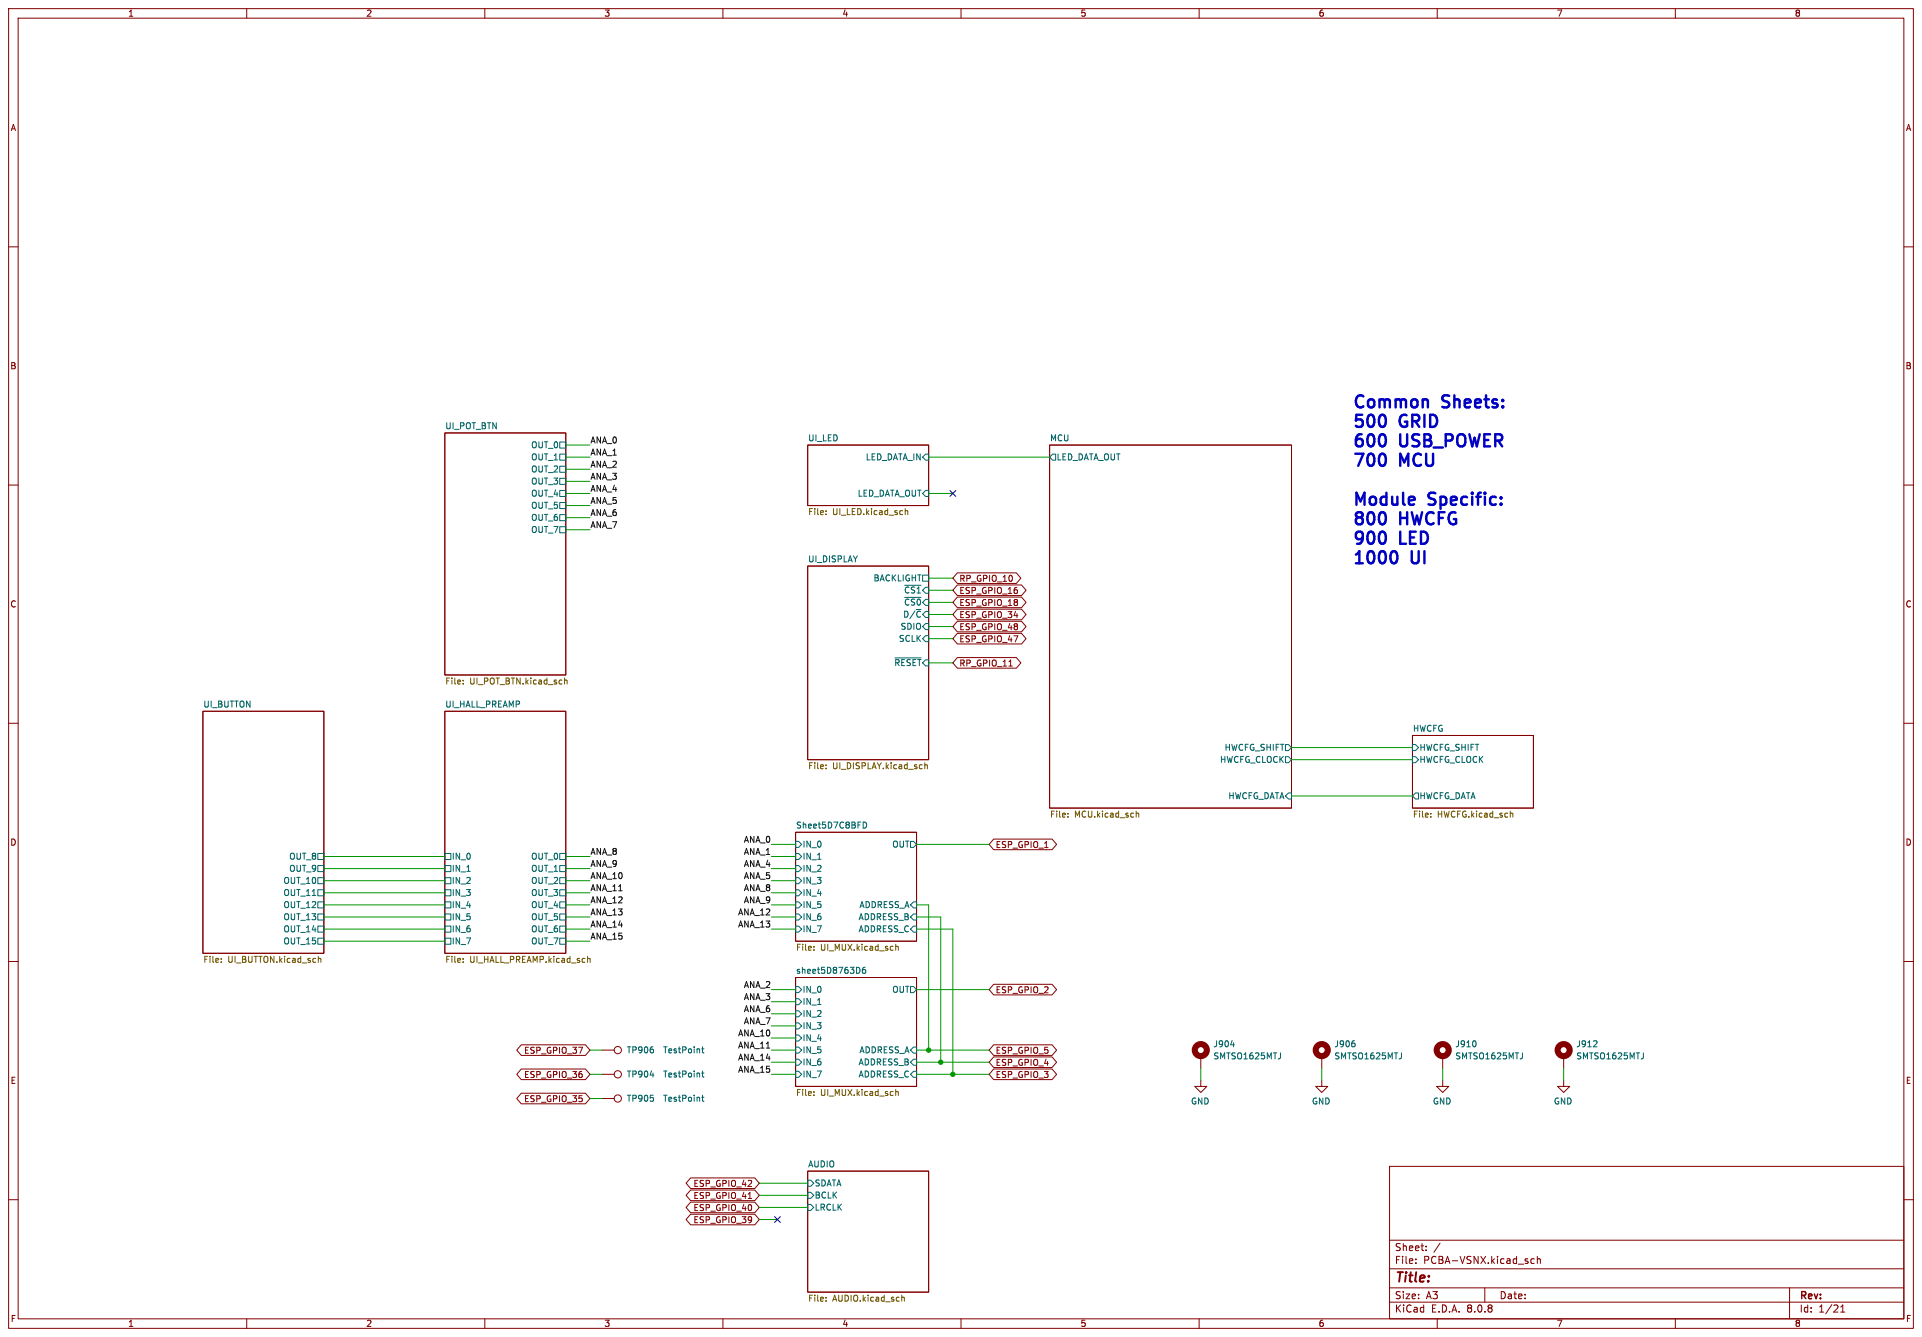
[picture p303: page 1]

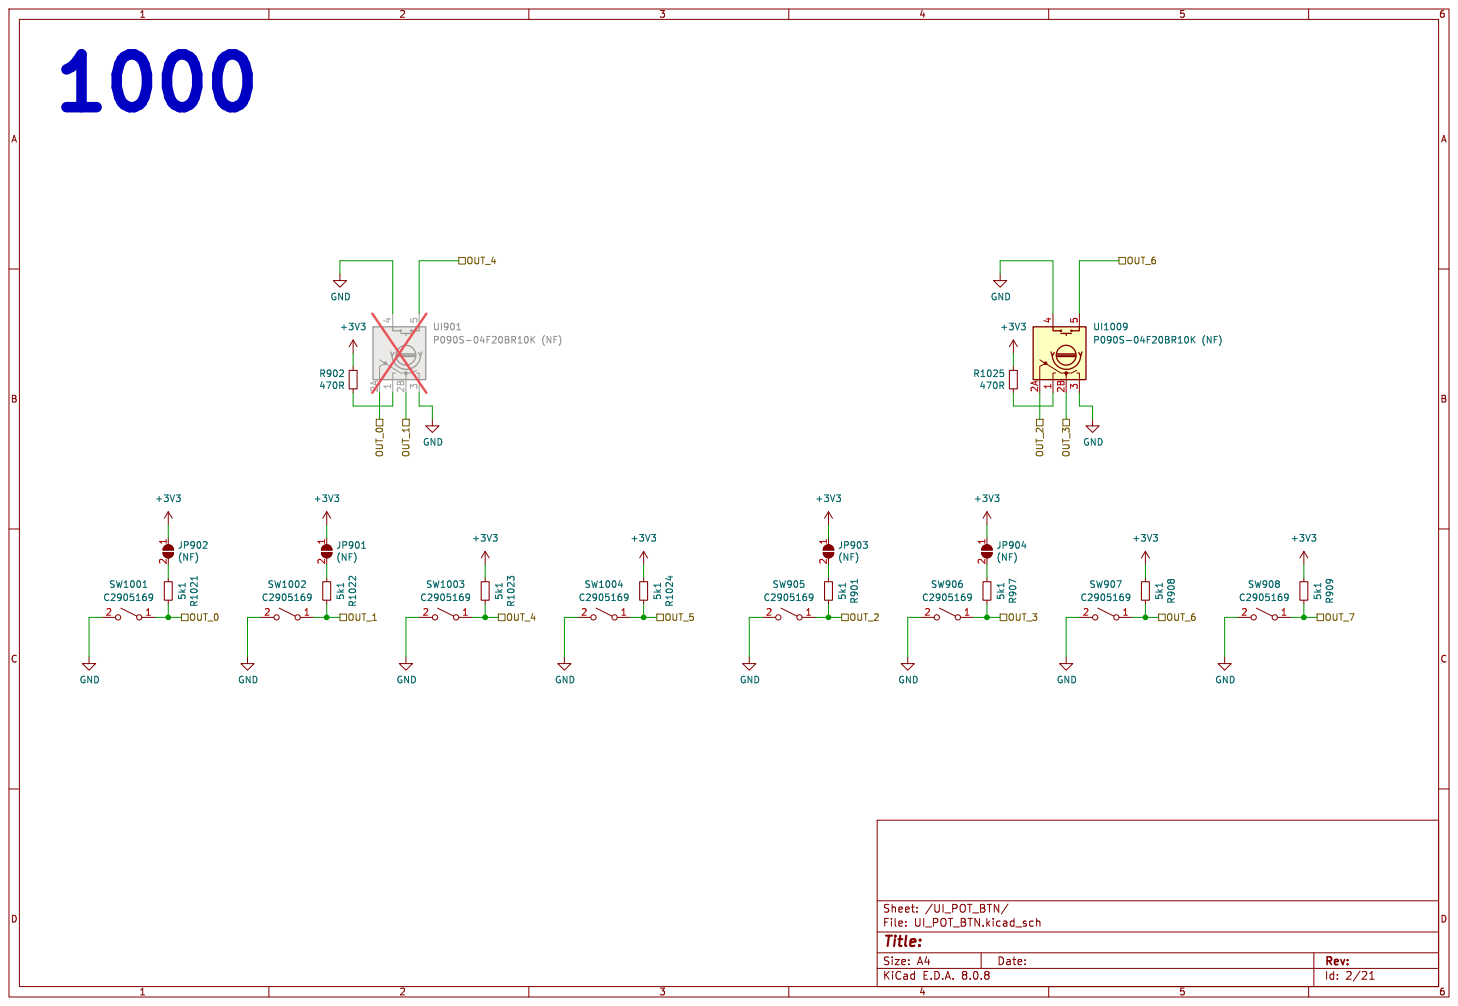
[picture p304: page 2]

Id: 2/21 Title: File: UI_POT_BTN.kicad_sch Sheet: /UI_POT_BTN/ GND

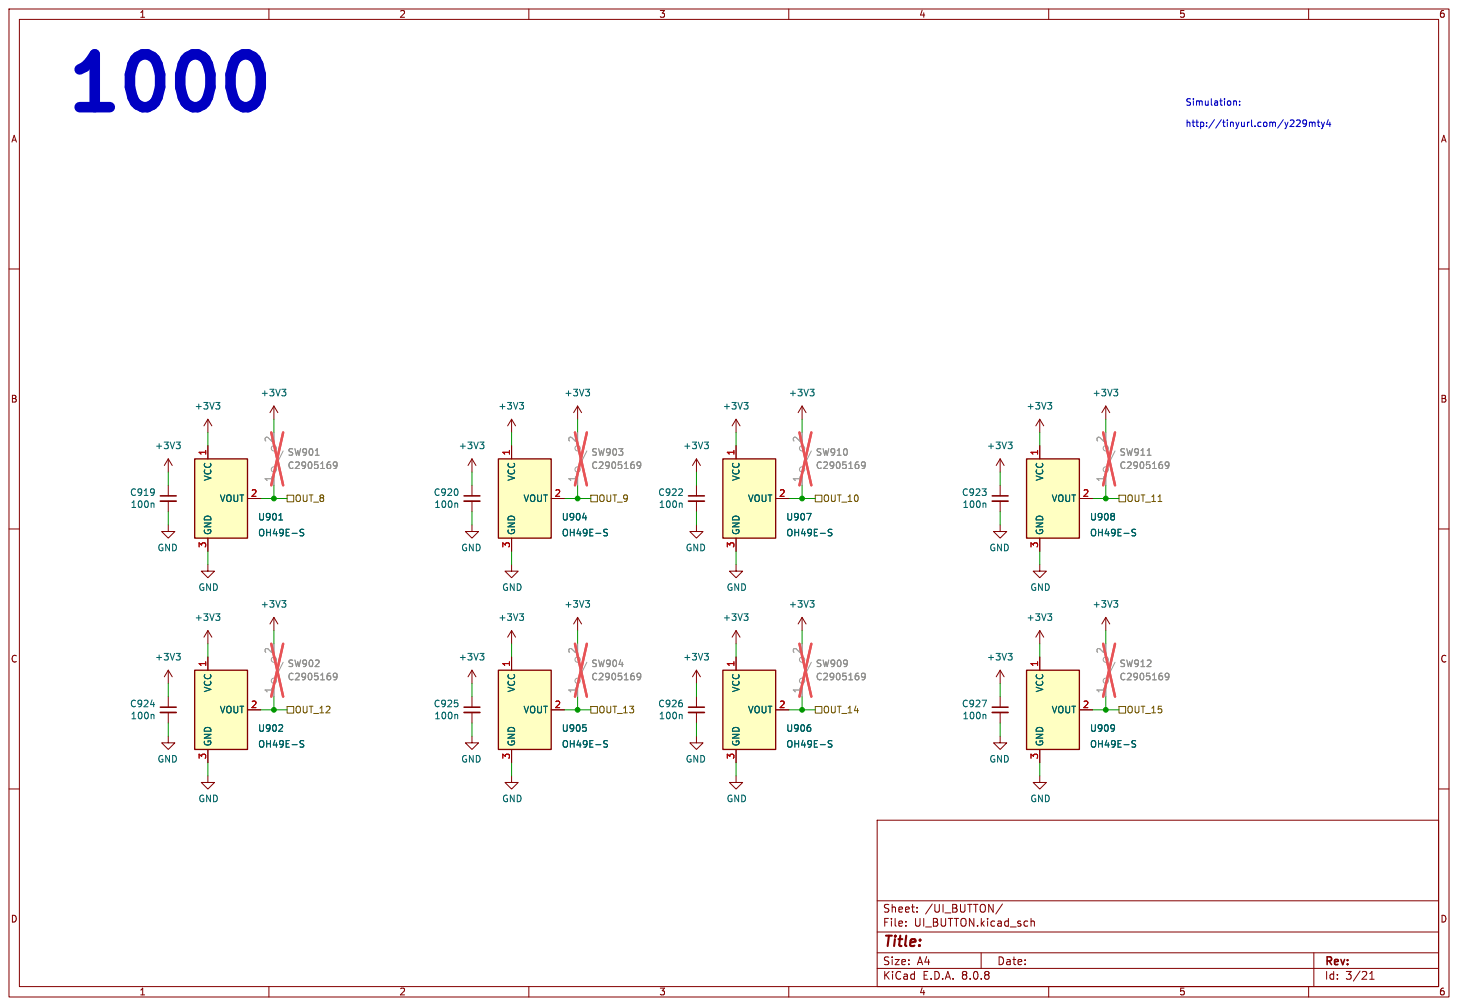
[picture p305: page 3]

http://tinyurl.com/y229mty4 U906 OH49E-S VCC

Id: 3/21 Title: File: UI_BUTTON.kicad_sch Sheet: /UI_BUTTON/

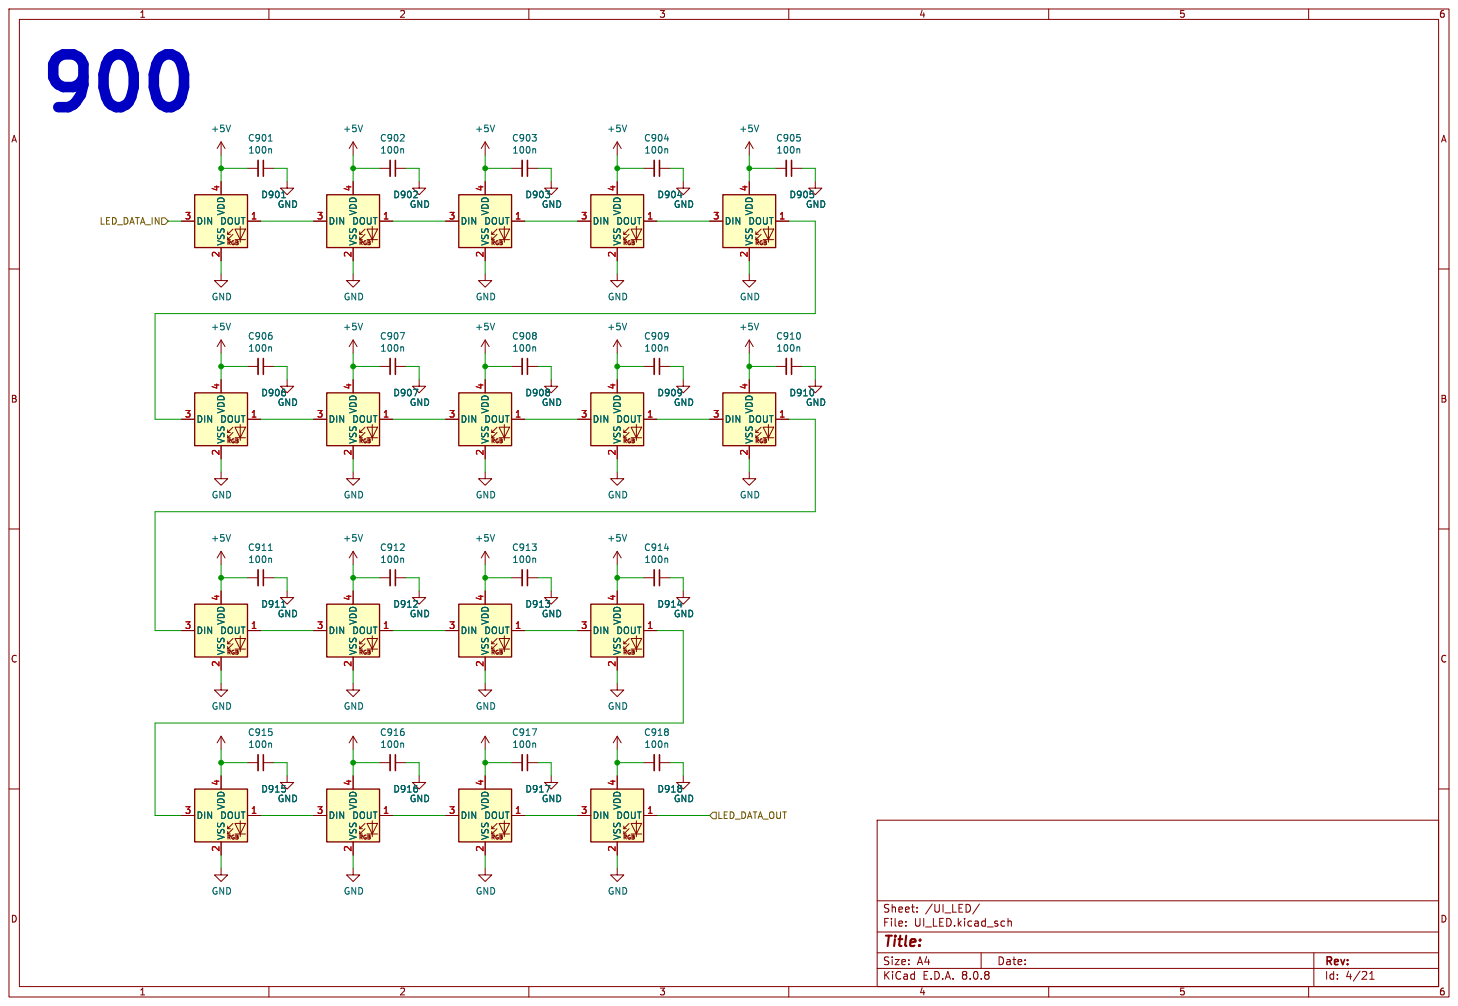
[picture p306: page 4]

Id: 4/21 Title: File: UI_LED.kicad_sch Sheet: /UI_LED/

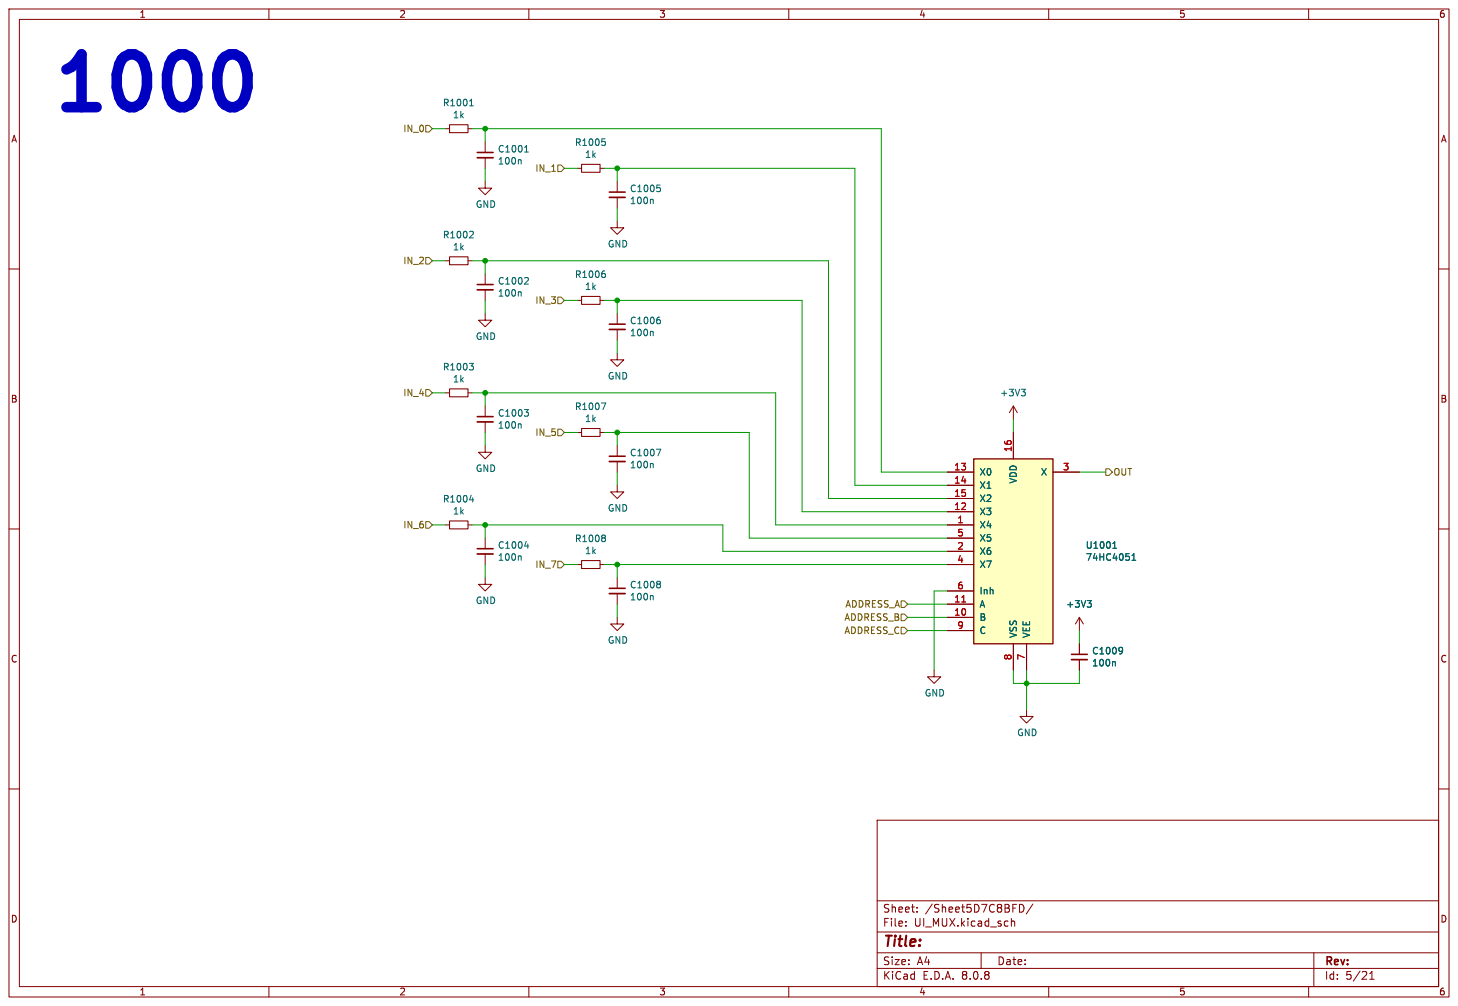
[picture p307: page 5]

Id: 5/21 Title: File: UI_MUX.kicad_sch Sheet: /Sheet5D7C8BFD/ R1004

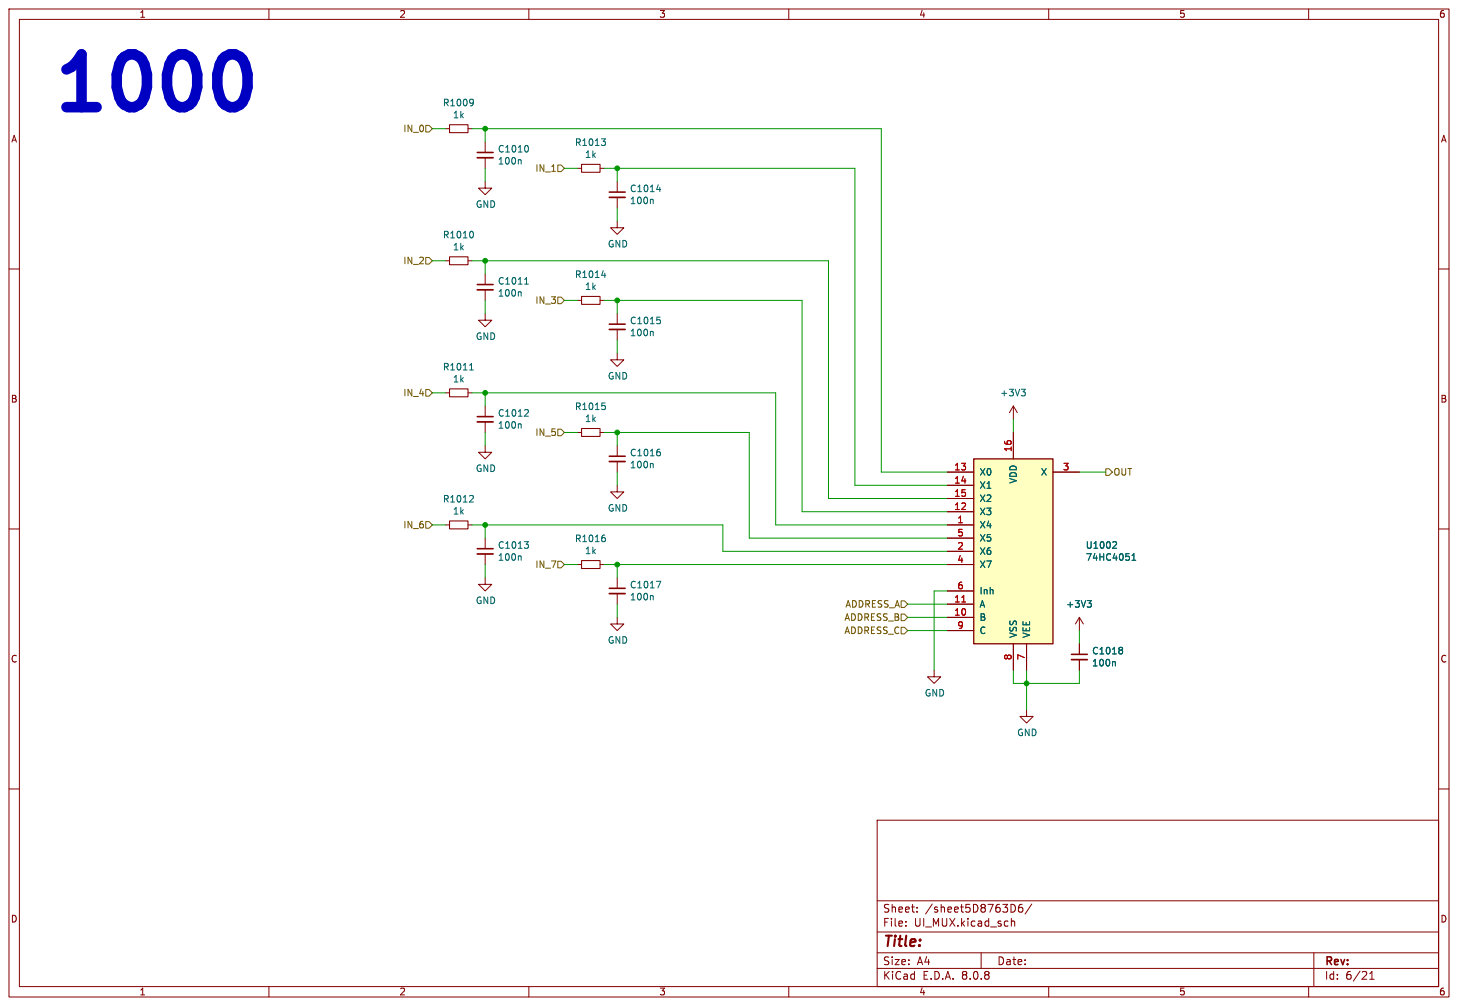
[picture p308: page 6]

Id: 6/21 Title: File: UI_MUX.kicad_sch Sheet: /sheet5D8763D6/ R1012

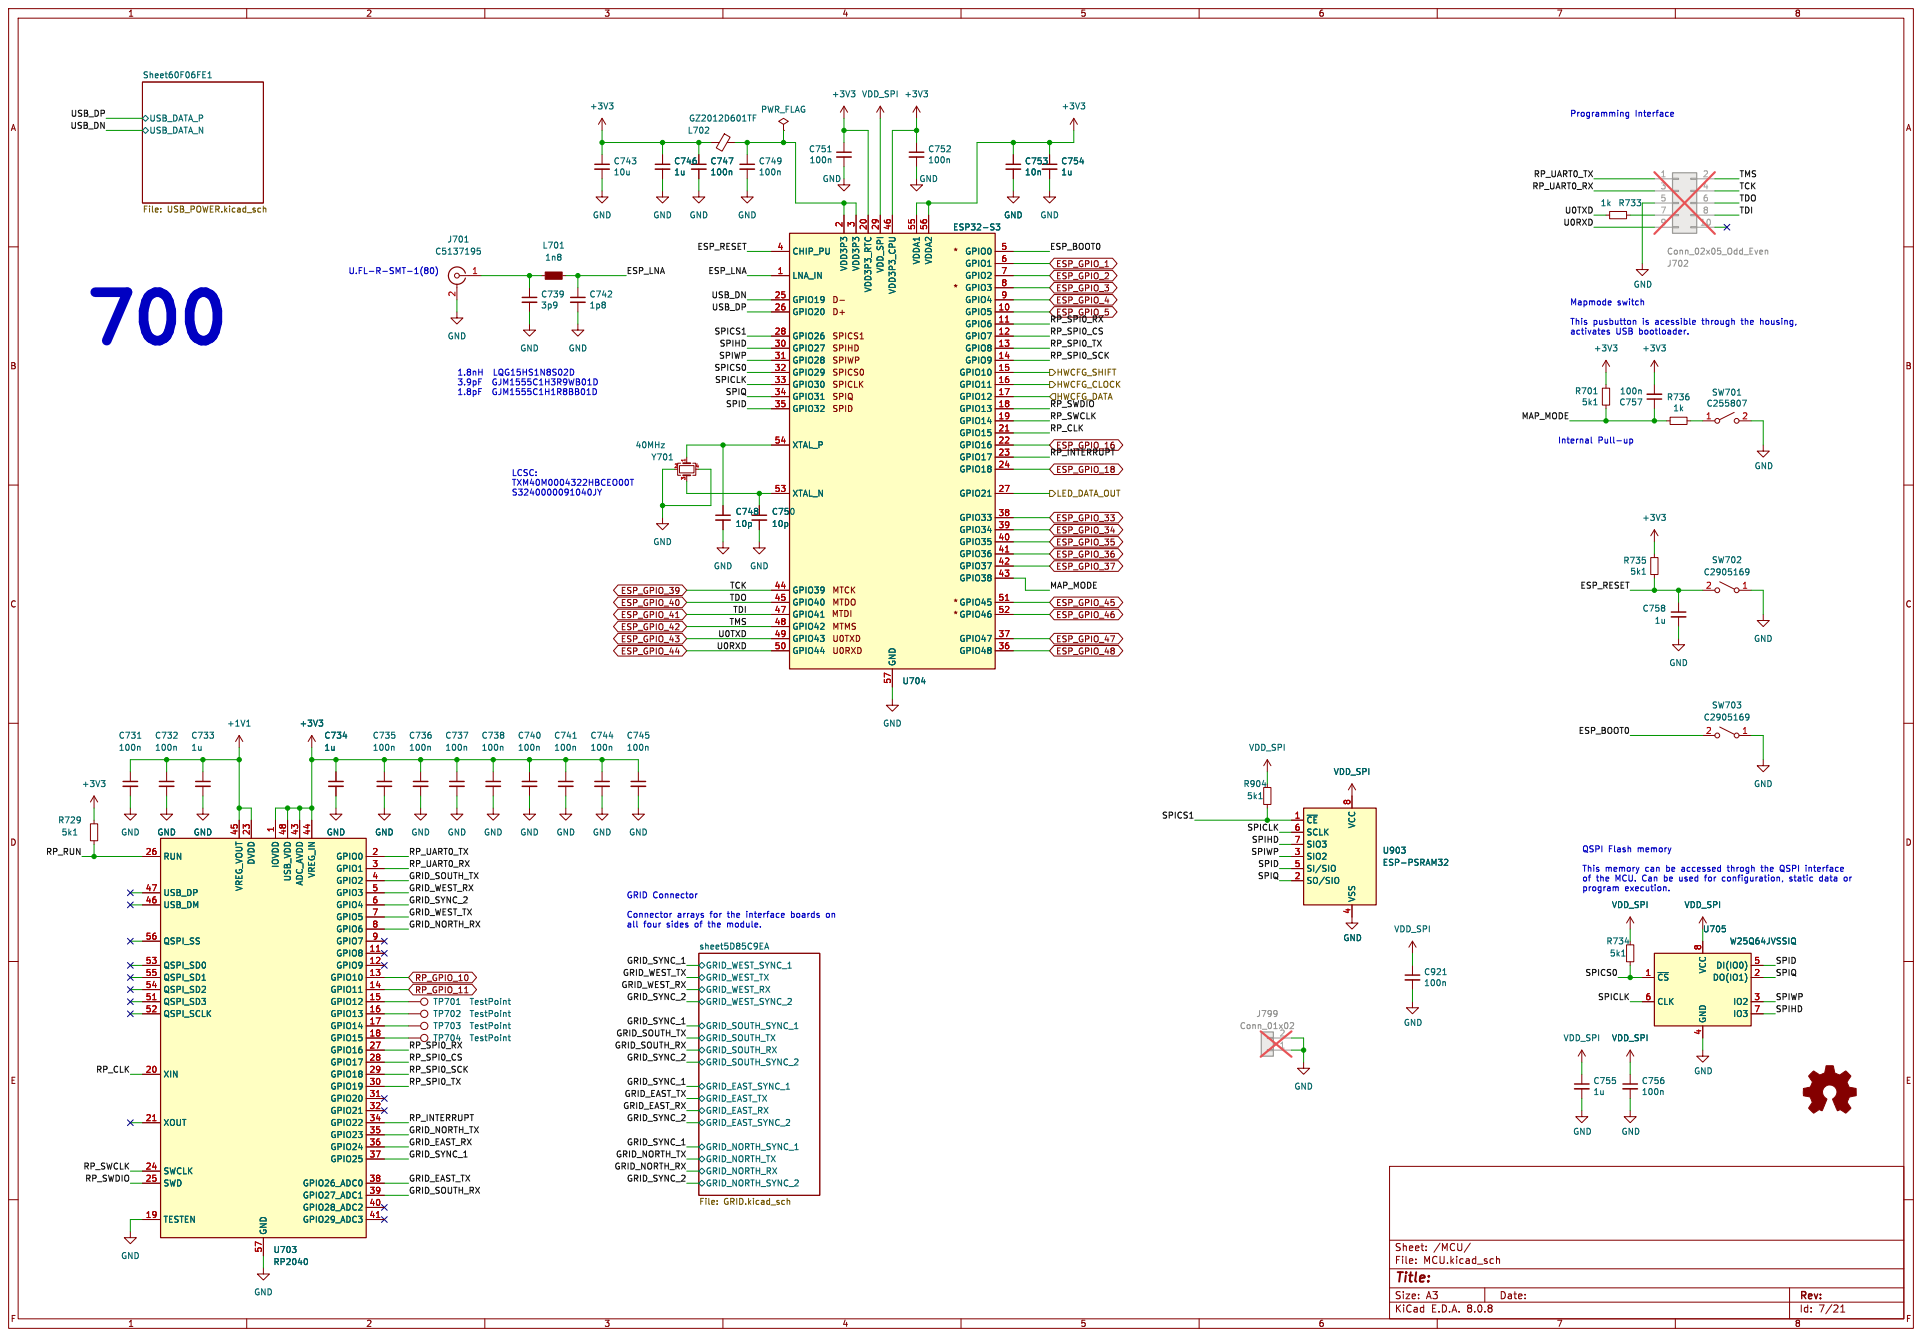
[picture p309: page 7]

* D+D- MTCK MTDI MTDO MTMS

1 GPIO8 11 GPIO9 12 GPIO10 13 GPIO11 14 GPIO12 15 GPIO13 16 GPIO14 17 GPIO15 18 TESTEN 19 GPIO0 2 XIN 20 XOUT 21 DVDD 23 SWCLK 24 SWD 25 RUN 26 GPIO16 27 GPIO17 28 GPIO18 29 GPIO1 3 GPIO19 30 GPIO20 31 GPIO21 32 GPIO22 34 GPIO23 35 GPIO24 36 GPIO25 37 GPIO26_ADC0 38 GPIO27_ADC1 39 GPIO2 4 GPIO28_ADC2 40 GPIO29_ADC3 41 ADC_AVDD 43 VREG_IN 44 VREG_VOUT 45 USB_DM 46 USB_DP 47 USB_VDD 48 GPIO3 5 QSPI_SD3 51 QSPI_SCLK 52 QSPI_SD0 53 QSPI_SD2 54 QSPI_SD1 55 QSPI_SS 56 GND 57 GPIO4 6 GPIO5 7 GPIO6 8 GPIO7 9 U903 ESP-PSRAM32 ~{CE} 1 SO/SIO 2 SIO2 3 VSS

4 SI/SIO 5 SCLK 6 SIO3 7 VCC

1 GPIO8 11 GPIO9 12 GPIO10 13 GPIO11 14 GPIO12 15 GPIO13 16 GPIO14 17 GPIO15 18 TESTEN 19 GPIO0 2 XIN 20 XOUT 21 DVDD 23 SWCLK 24 SWD 25 RUN 26 GPIO16 27 GPIO17 28 GPIO18 29 GPIO1 3 GPIO19 30 GPIO20 31 GPIO21 32 GPIO22 34 GPIO23 35 GPIO24 36 GPIO25 37 GPIO26_ADC0 38 GPIO27_ADC1 39 GPIO2 4 GPIO28_ADC2 40 GPIO29_ADC3 41 ADC_AVDD 43 VREG_IN 44 VREG_VOUT 45 USB_DM 46 USB_DP 47 USB_VDD 48 GPIO3 5 QSPI_SD3 51 QSPI_SCLK 52 QSPI_SD0 53 QSPI_SD2 54 QSPI_SD1 55 QSPI_SS 56 GND 57 GPIO4 6 GPIO5 7 GPIO6 8 GPIO7 9 U703 RP2040

all four sides of the module.

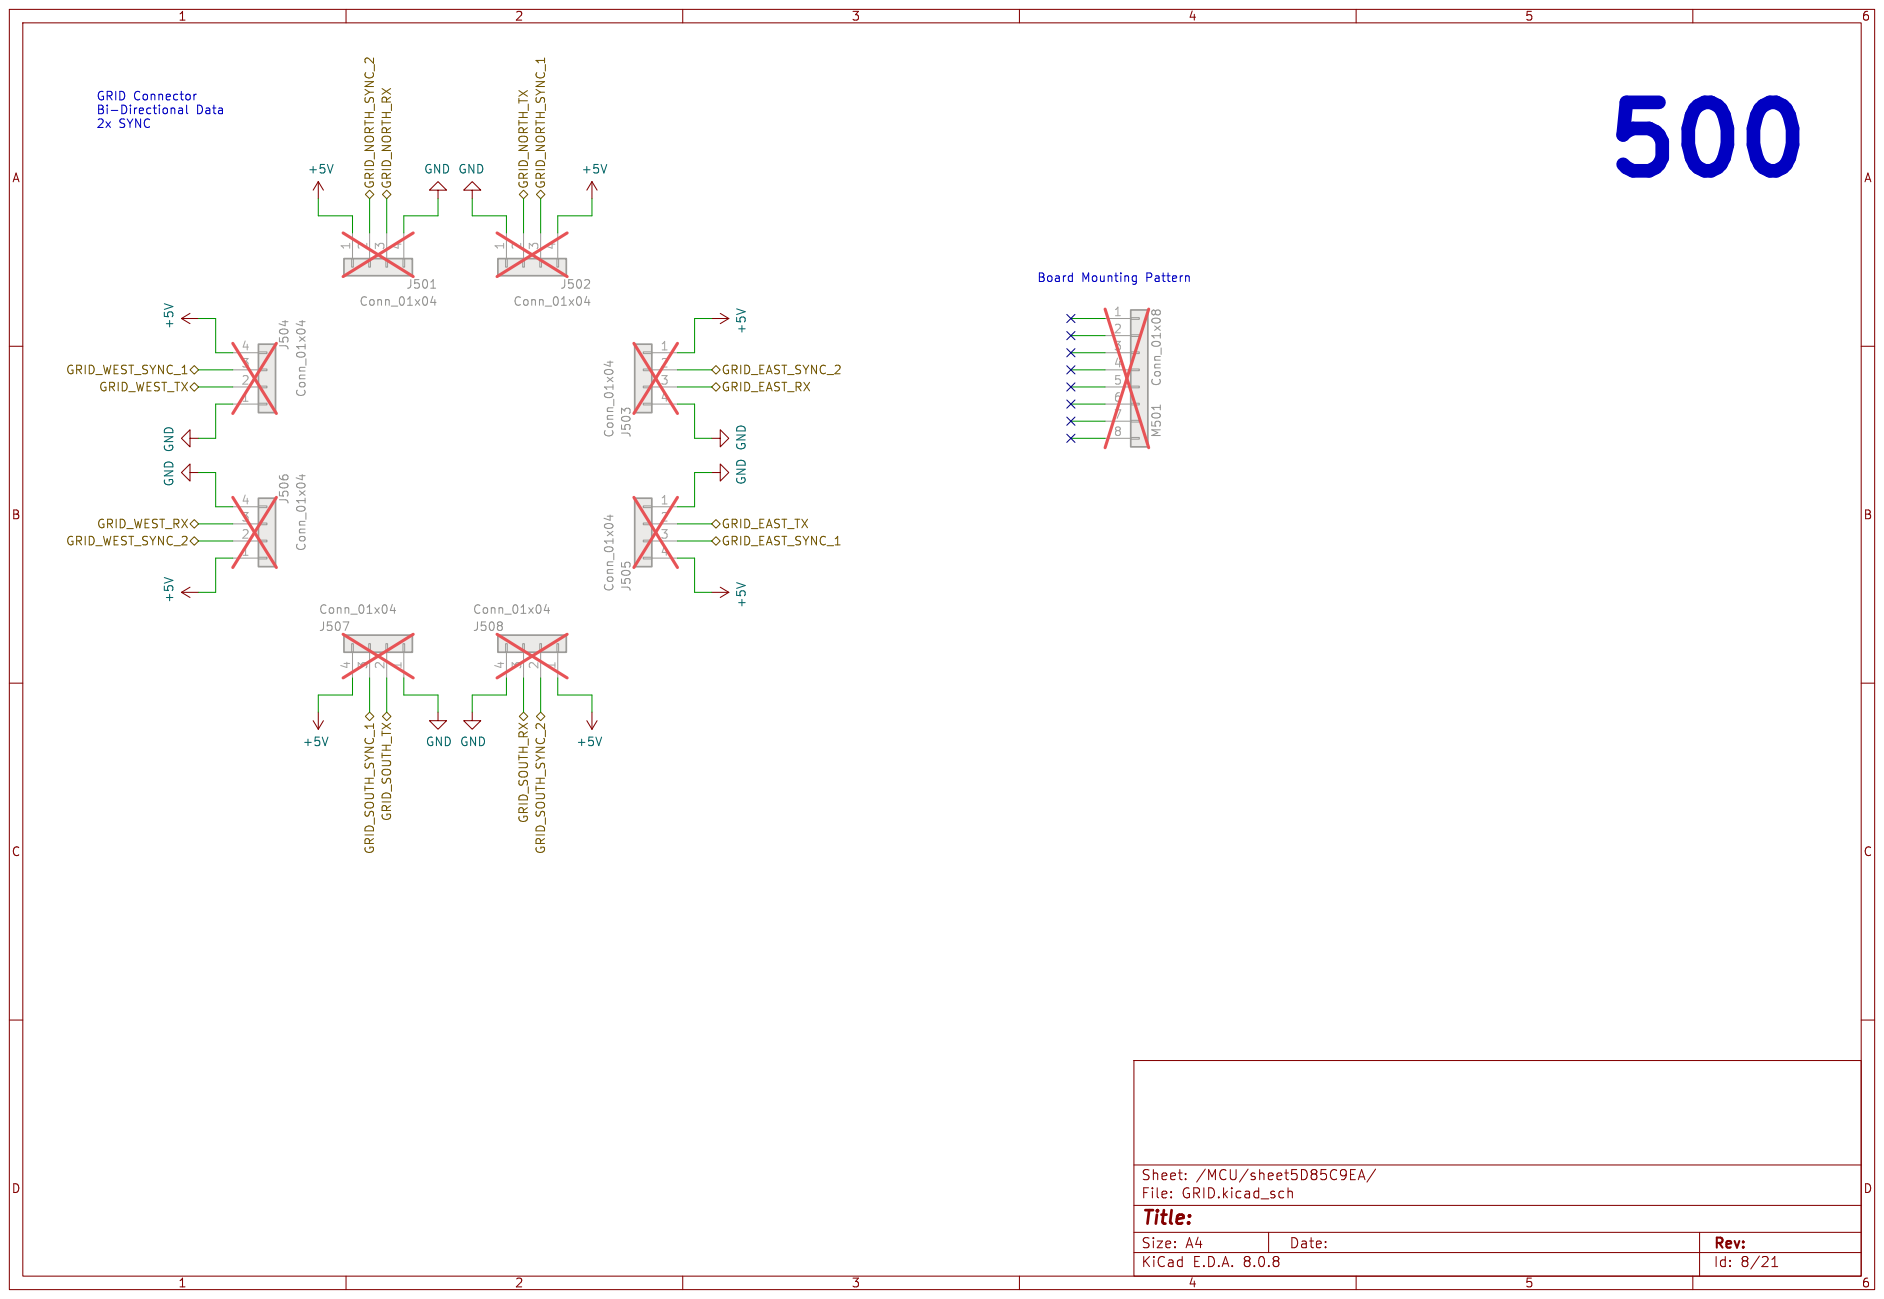
[picture p310: page 8]

4 J501 Conn_01x04 GRID_WEST_TX GRID_EAST_SYNC_1 GRID_EAST_SYNC_2 GRID_EAST_RX GRID_EAST_TX GRID_SOUTH_SYNC_1 GRID_SOUTH_SYNC_2 GRID_SOUTH_TX GRID_SOUTH_RX GRID_WEST_SYNC_1 GRID_WEST_RX GRID_WEST_SYNC_2 GRID_NORTH_SYNC_2 GRID_NORTH_RX GRID_NORTH_TX GRID_NORTH_SYNC_1 Board Mounting Pattern GRID Connector Bi-Directional Data

Id: 8/21 Title: File: GRID.kicad_sch Sheet: /MCU/sheet5D85C9EA/

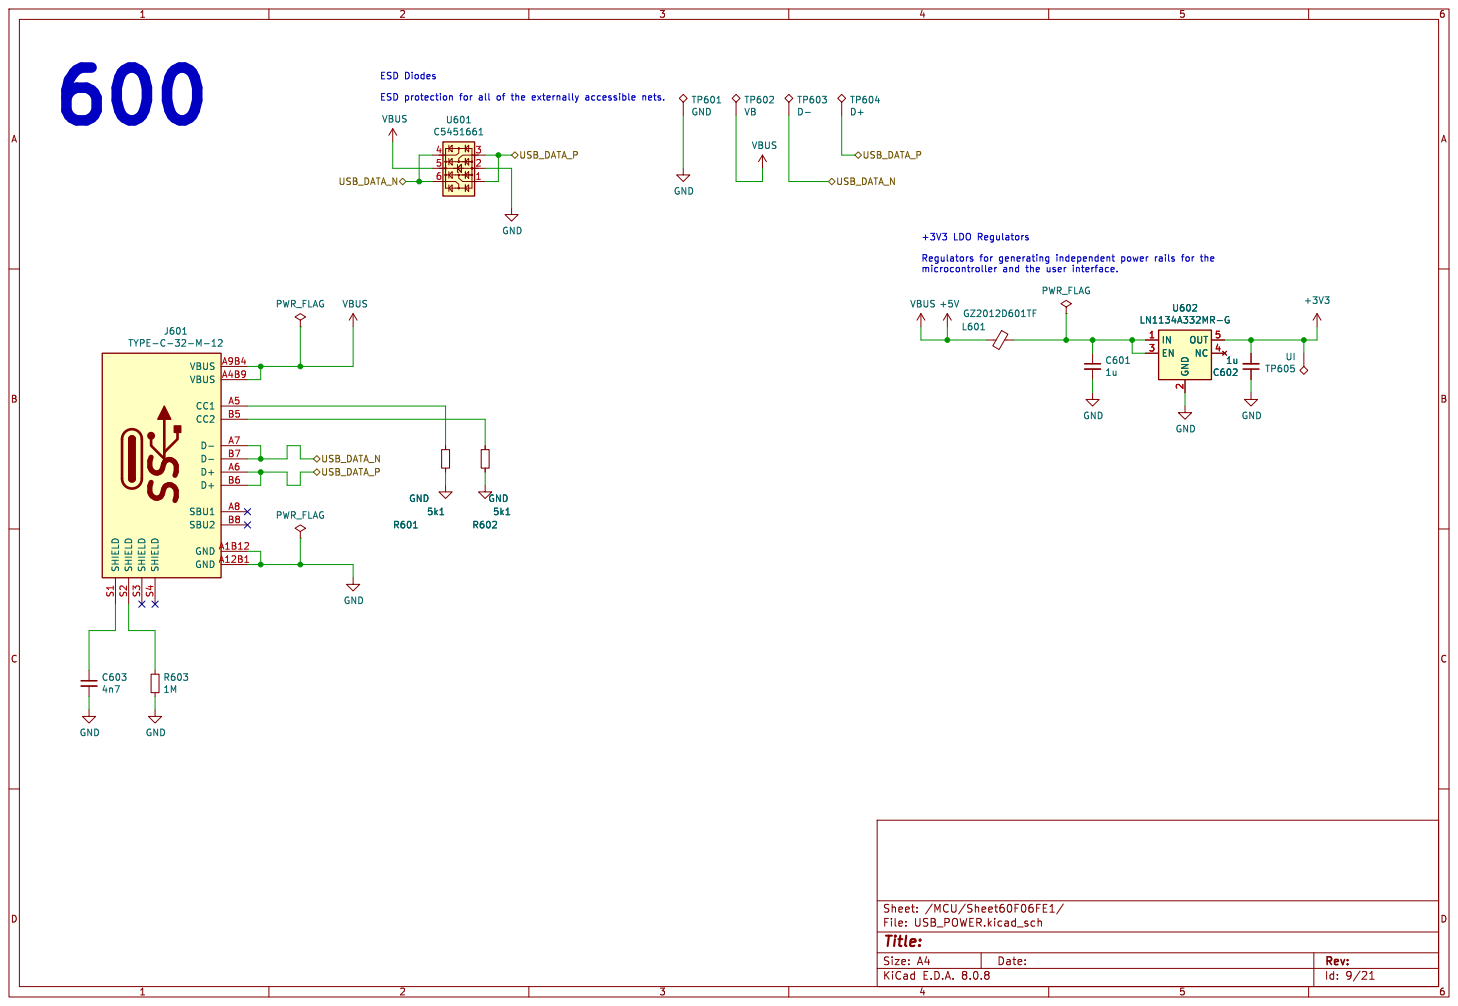
[picture p311: page 9]

Id: 9/21 Title: File: USB_POWER.kicad_sch Sheet: /MCU/Sheet60F06FE1/

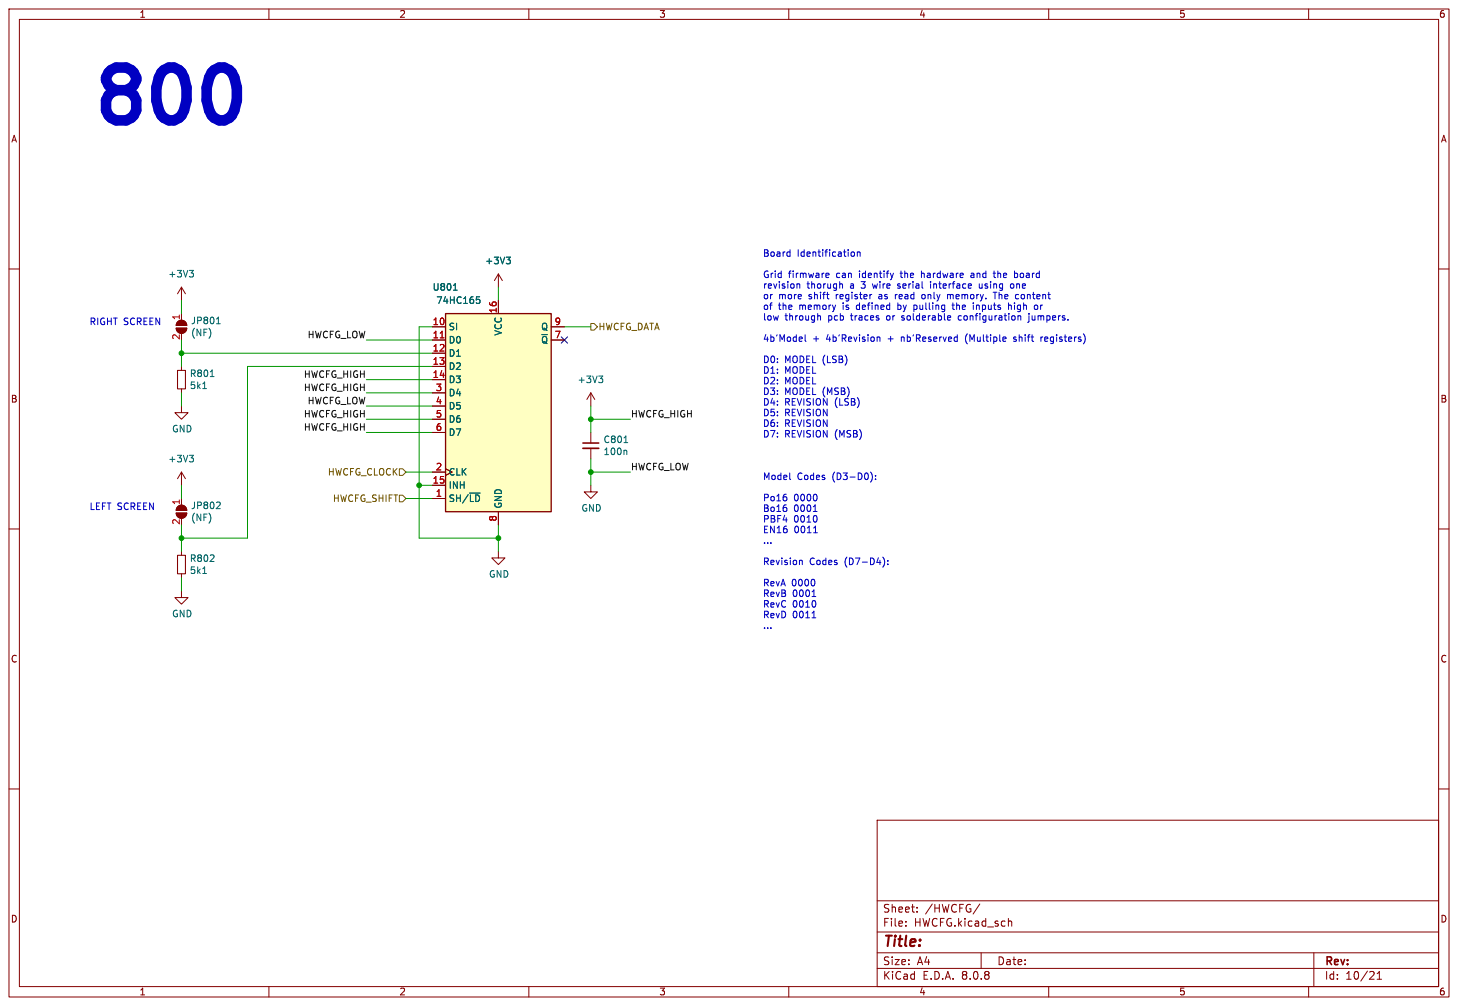
[picture p312: page 10]

D6: REVISION
D7: REVISION (MSB) Model Codes (D3-D0): Po16 0000 Bo16 0001 PBF4 0010 EN16 0011

... Revision Codes (D7-D4): RevA 0000 RevB 0001 RevC 0010 RevD 0011

Id: 10/21 Title: File: HWCFG.kicad_sch Sheet: /HWCFG/

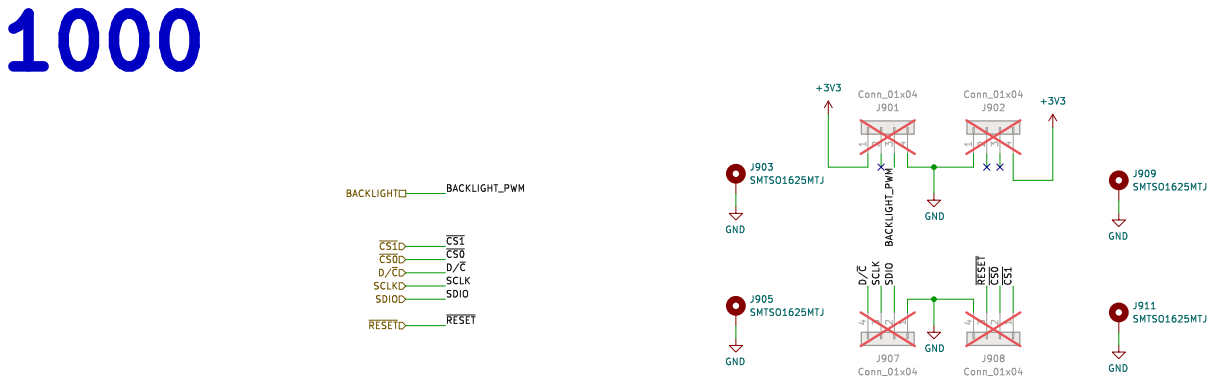
[picture p313: page 11]

Id: 11/21 Title: File: UI_DISPLAY.kicad_sch Sheet: /UI_DISPLAY/


Id: 12/21 Title: File: UI_HALL_PREAMP.kicad_sch Sheet: /UI_HALL_PREAMP/

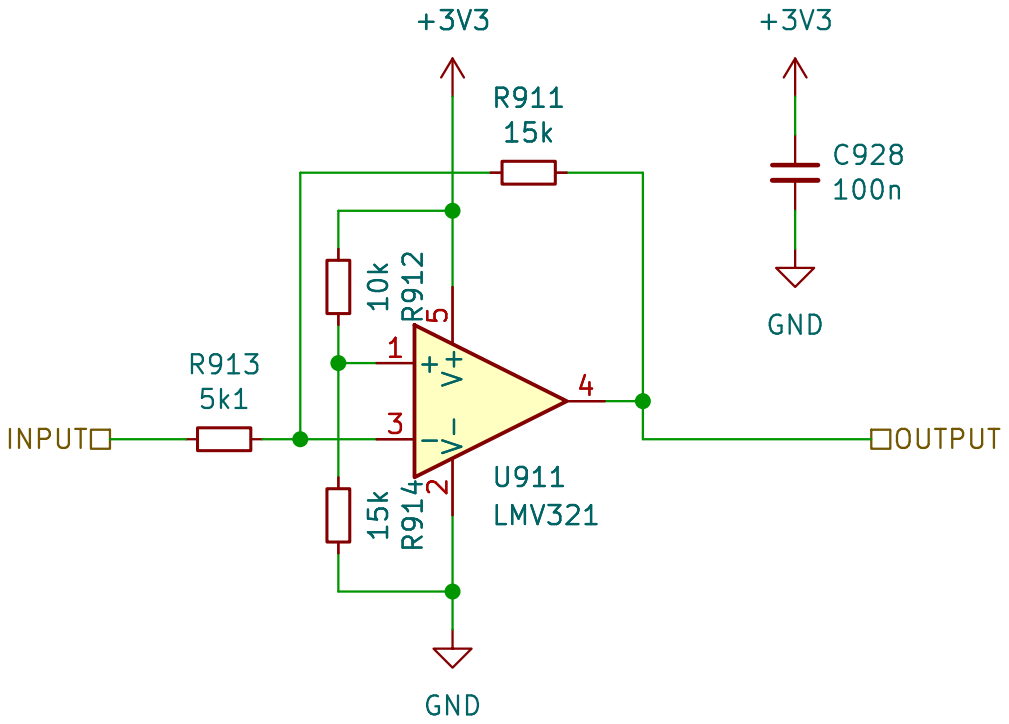
[picture p314: page 13]

Id: 13/21 Title: File: INVERT_AND_OFFSET.kicad_sch Sheet: /UI_HALL_PREAMP/INVERT_AND_OFFSET/

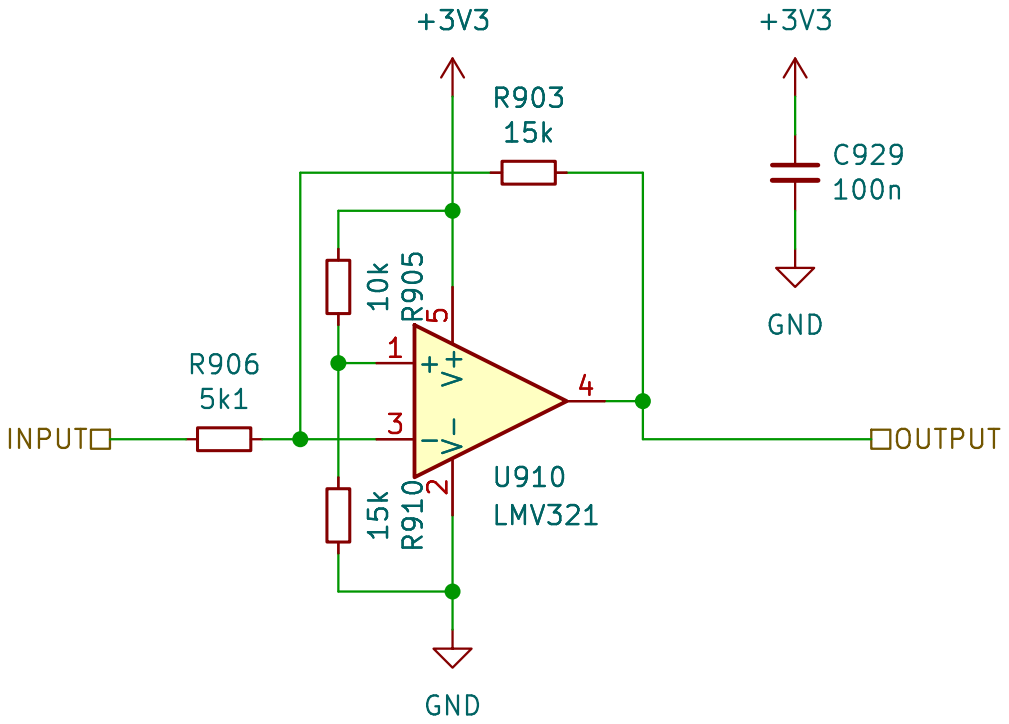
[picture p315: page 14]

Id: 14/21 Title: File: INVERT_AND_OFFSET.kicad_sch Sheet: /UI_HALL_PREAMP/INVERT_AND_OFFSET1/

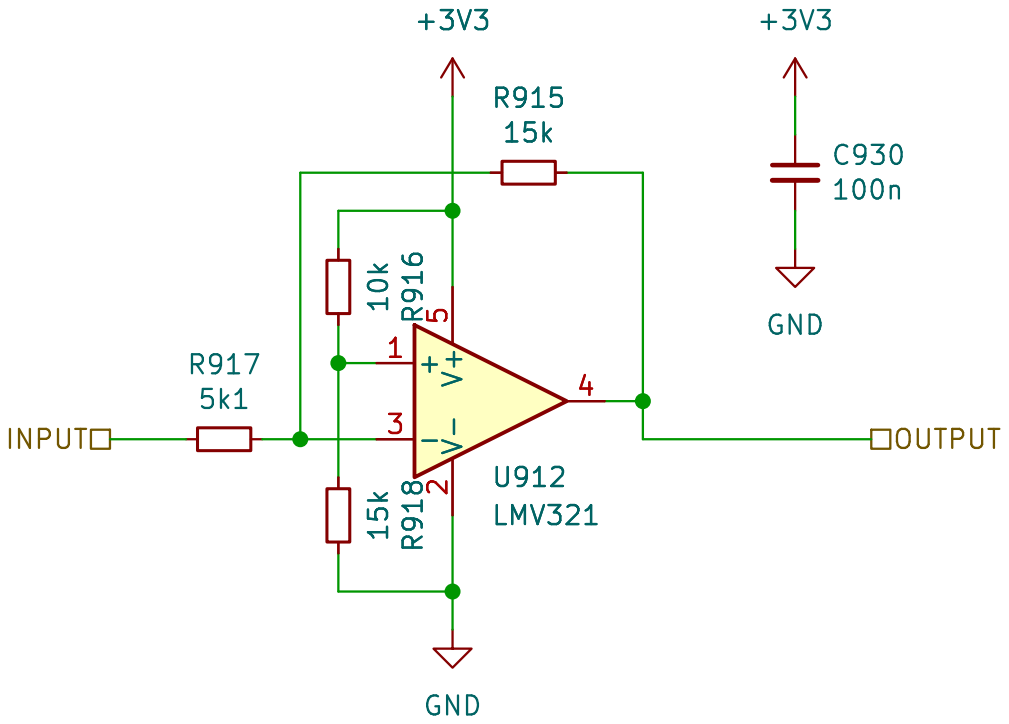
[picture p316: page 15]

Id: 15/21 Title: File: INVERT_AND_OFFSET.kicad_sch Sheet: /UI_HALL_PREAMP/INVERT_AND_OFFSET2/

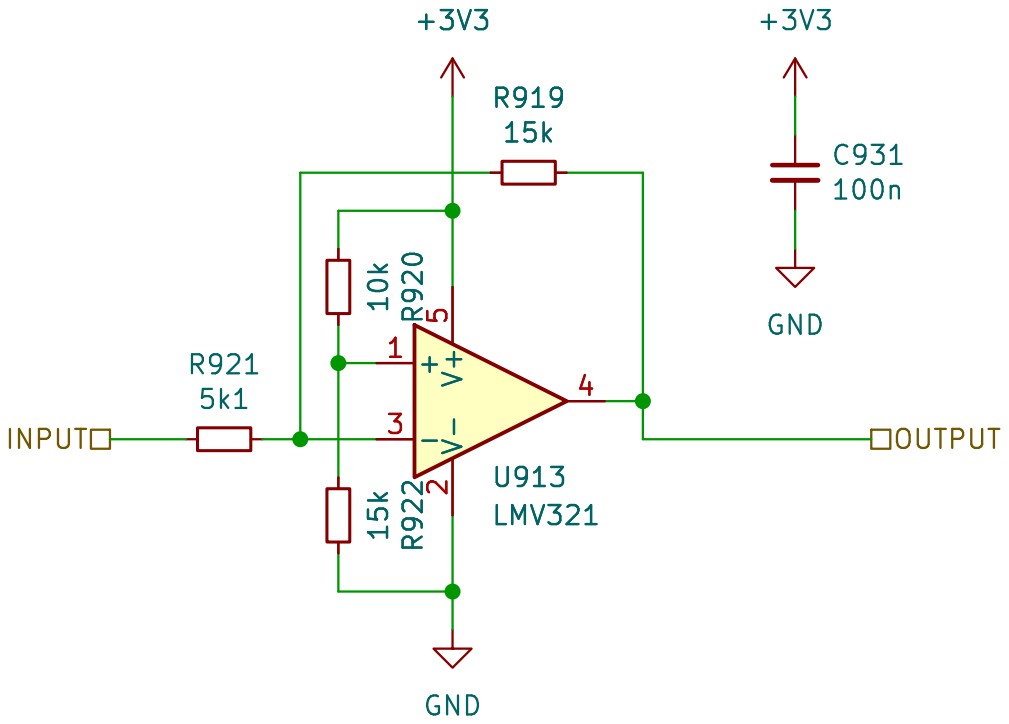
[picture p317: page 16]

Id: 16/21 Title: File: INVERT_AND_OFFSET.kicad_sch Sheet: /UI_HALL_PREAMP/INVERT_AND_OFFSET3/

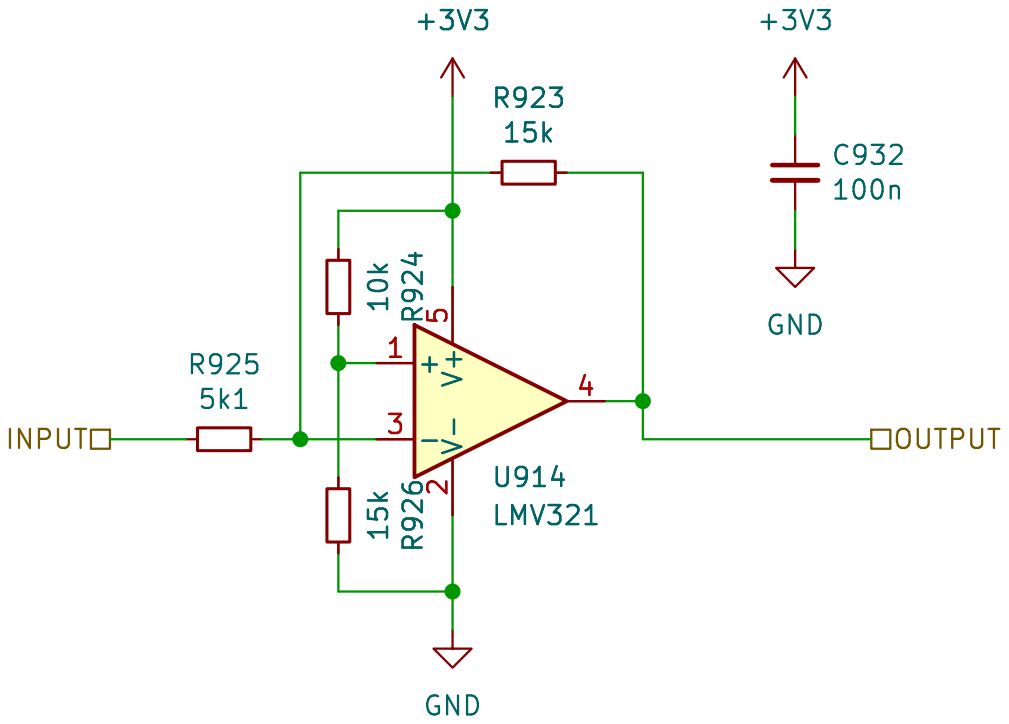
[picture p318: page 17]

Id: 17/21 Title: File: INVERT_AND_OFFSET.kicad_sch Sheet: /UI_HALL_PREAMP/INVERT_AND_OFFSET4/

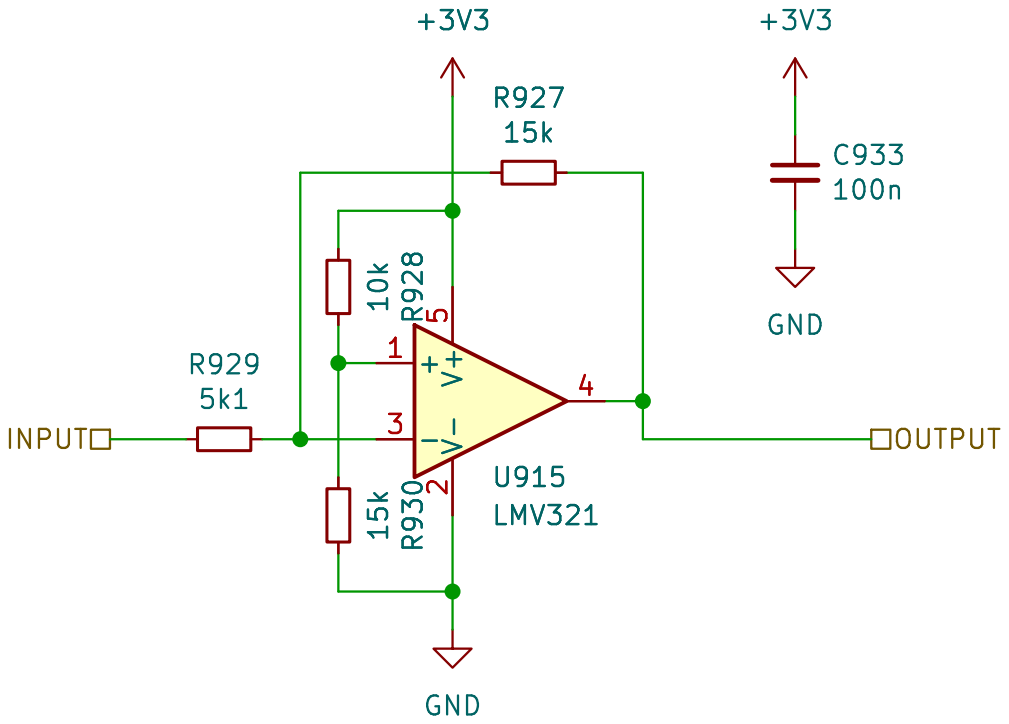
[picture p319: page 18]

Id: 18/21 Title: File: INVERT_AND_OFFSET.kicad_sch Sheet: /UI_HALL_PREAMP/INVERT_AND_OFFSET5/

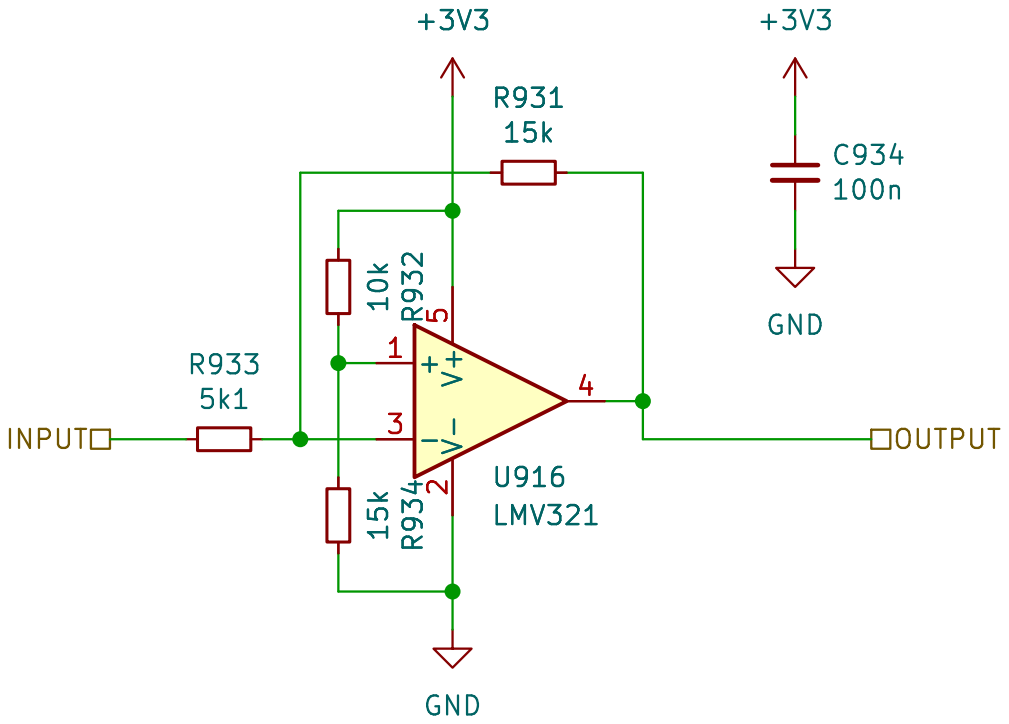
[picture p320: page 19]

Id: 19/21 Title: File: INVERT_AND_OFFSET.kicad_sch Sheet: /UI_HALL_PREAMP/INVERT_AND_OFFSET6/

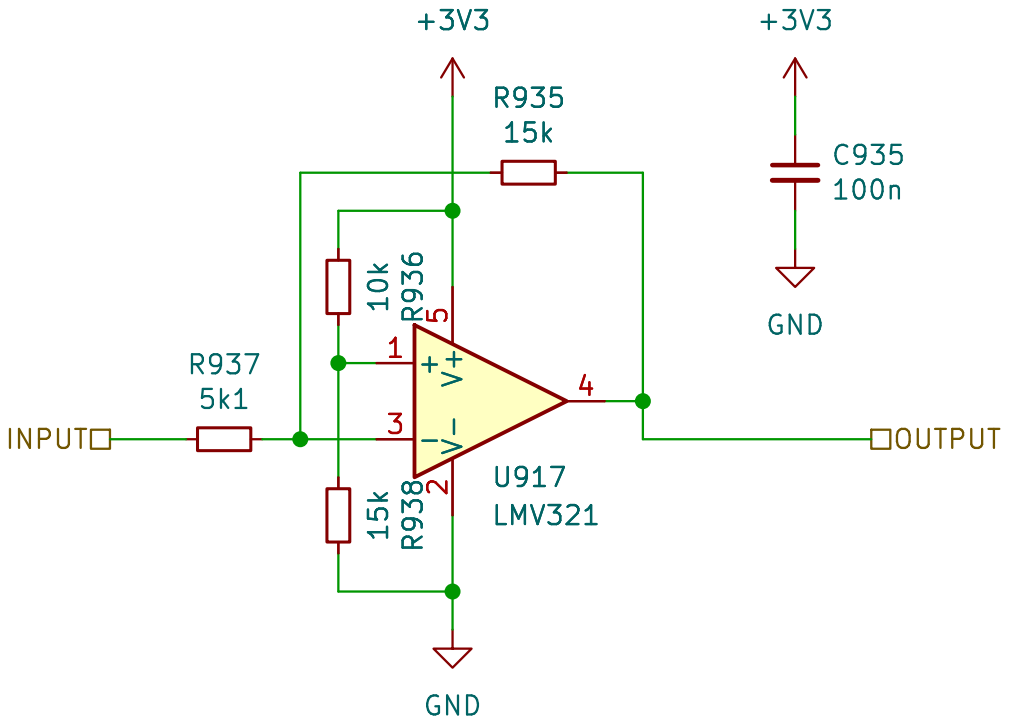
[picture p321: page 20]

Id: 20/21 Title: File: INVERT_AND_OFFSET.kicad_sch Sheet: /UI_HALL_PREAMP/INVERT_AND_OFFSET7/

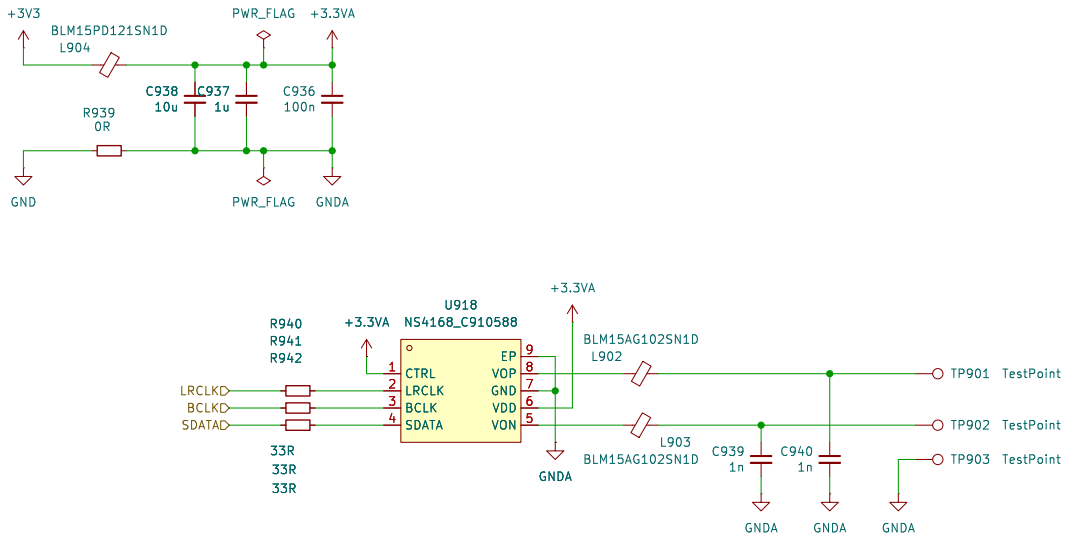
[picture p322: page 21]

Id: 21/21 Title: File: AUDIO.kicad_sch Sheet: /AUDIO/
