intechstudio/grid/Preview/Mechanical/MAGNET-D3x13_Drawing.pdf

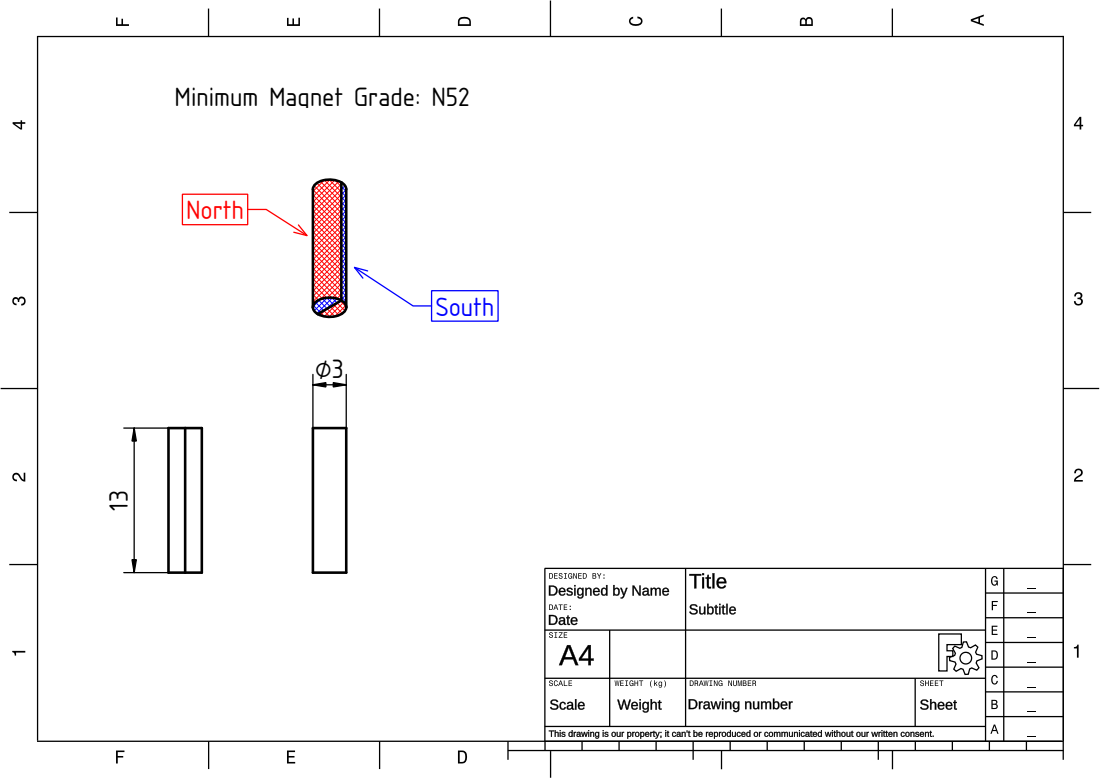
[picture p323: page 1]
North; South

Minimum Magnet Grade: N52
