intechstudio/grid/Preview/Mechanical/MAGNET-SQ3_Drawing.pdf

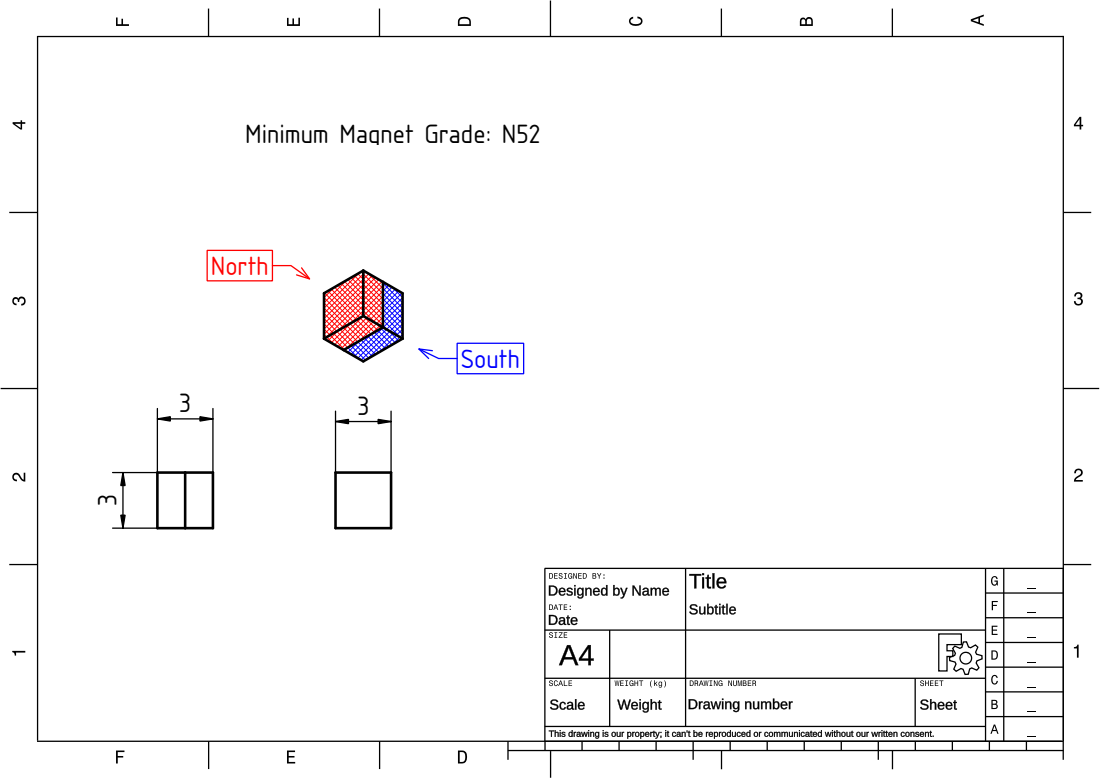
[picture p324: page 1]
North; South

Minimum Magnet Grade: N52
