intechstudio/grid/Preview/Mechanical/PCBA-CONN-POGO_Drawing.pdf

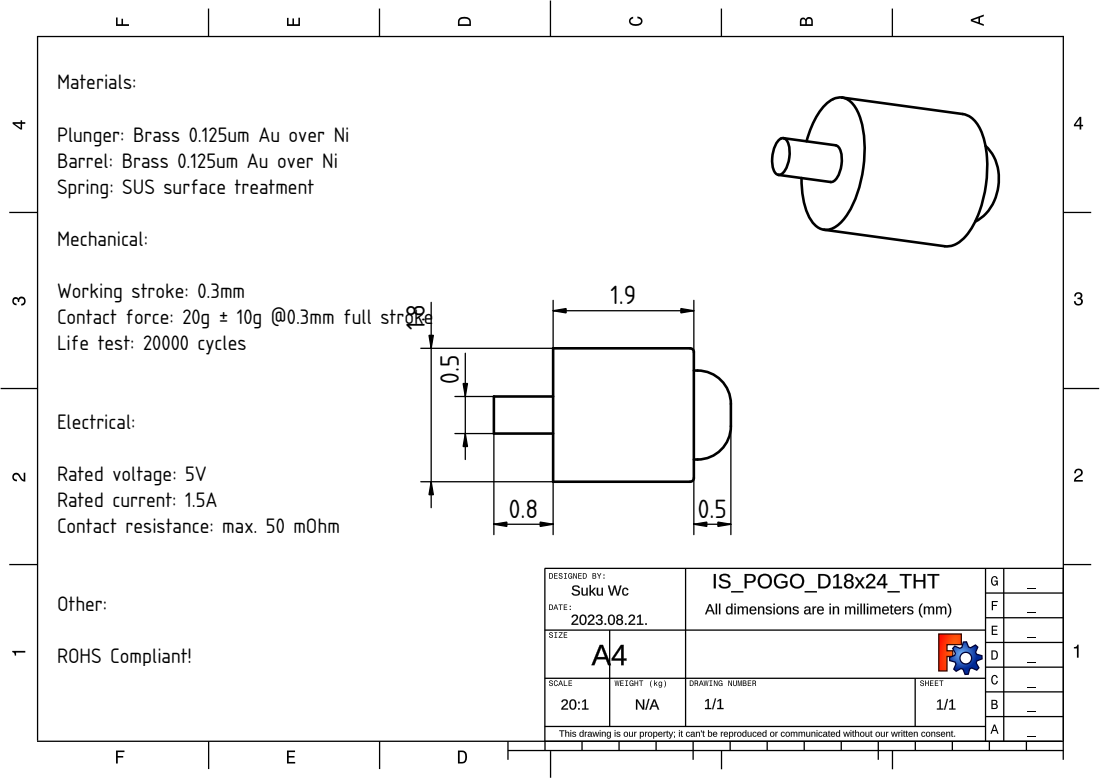
[picture p325: page 1]
Other:; ROHS Compliant!

Materials:
Plunger: Brass 0.125um Au over Ni
Barrel: Brass 0.125um Au over Ni
Spring: SUS surface treatment
Mechanical:
Working stroke: 0.3mm
Contact force: 20g ± 10g @0.3mm full stroke
Life test: 20000 cycles

Electrical:
Rated voltage: 5V
Rated current: 1.5A
Contact resistance: max. 50 mOhm
