intechstudio/grid/Preview/Mechanical/PLASTIC-KNOB-POT_Drawing.pdf

AA

⌀

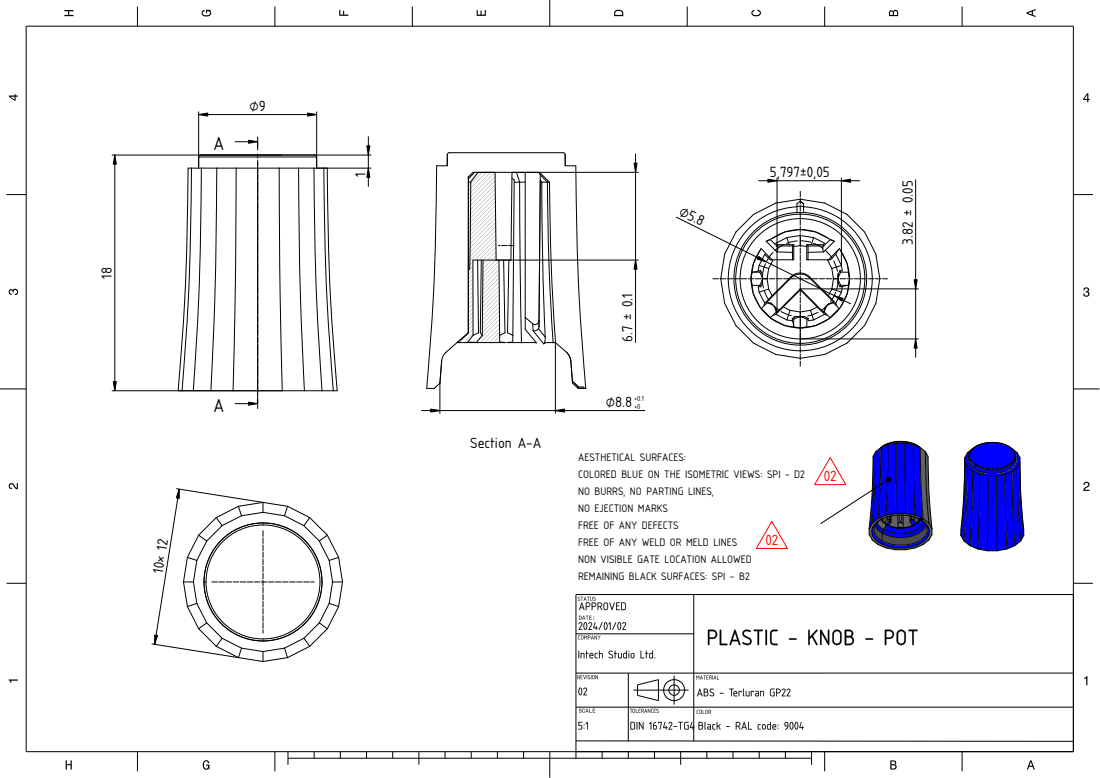
[picture p326: page 1]
TIC; RIC; VIE; TIN; LIN; VISIB; TIO; AININ; ectio

S: COLORED BLUE ON THE IS

S, NO EJECTION MARKS FREE OF ANY DEFECTS FREE OF ANY WELD OR MELD
