intechstudio/grid/Preview/Mechanical/PLASTIC-KNOB-POT_Painting drawing.pdf

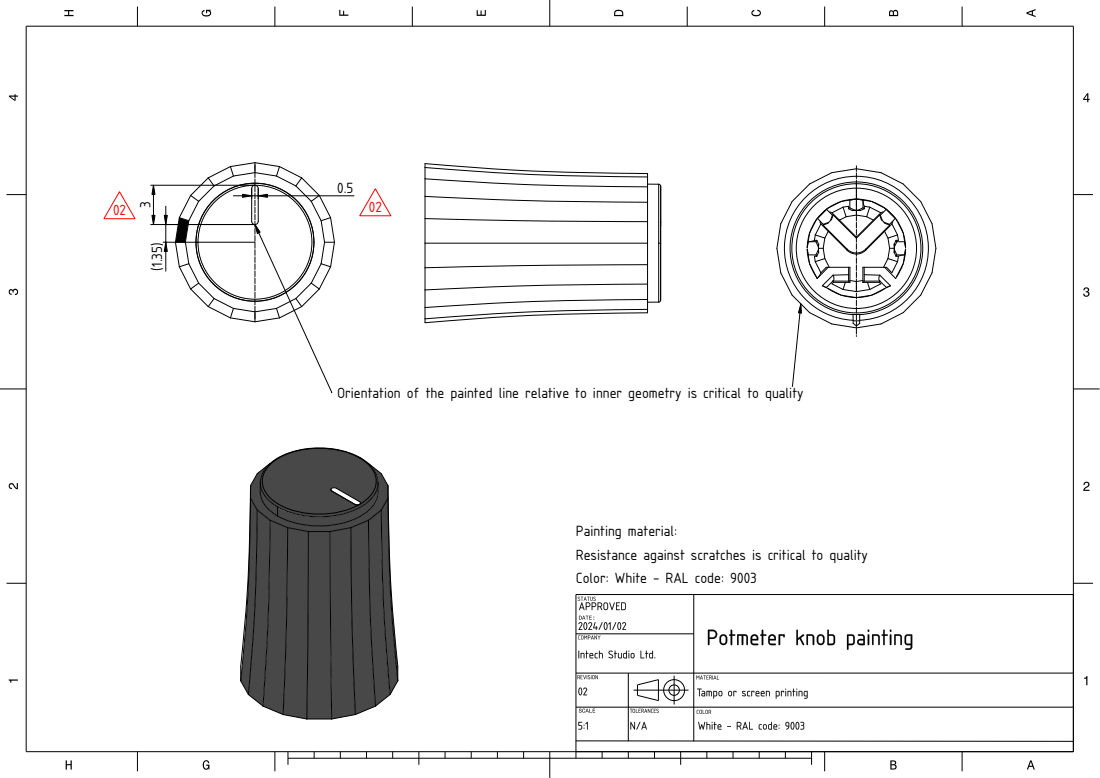
[picture p327: page 1]

Orientation of the painted line relative to inner geometry is critical to quality

Painting material:
Resistance against scratches is critical to quality
Color: White - RAL code: 9003
