intechstudio/grid/Preview/Mechanical/reference_PLASTIC-CANVAS.pdf

A

A

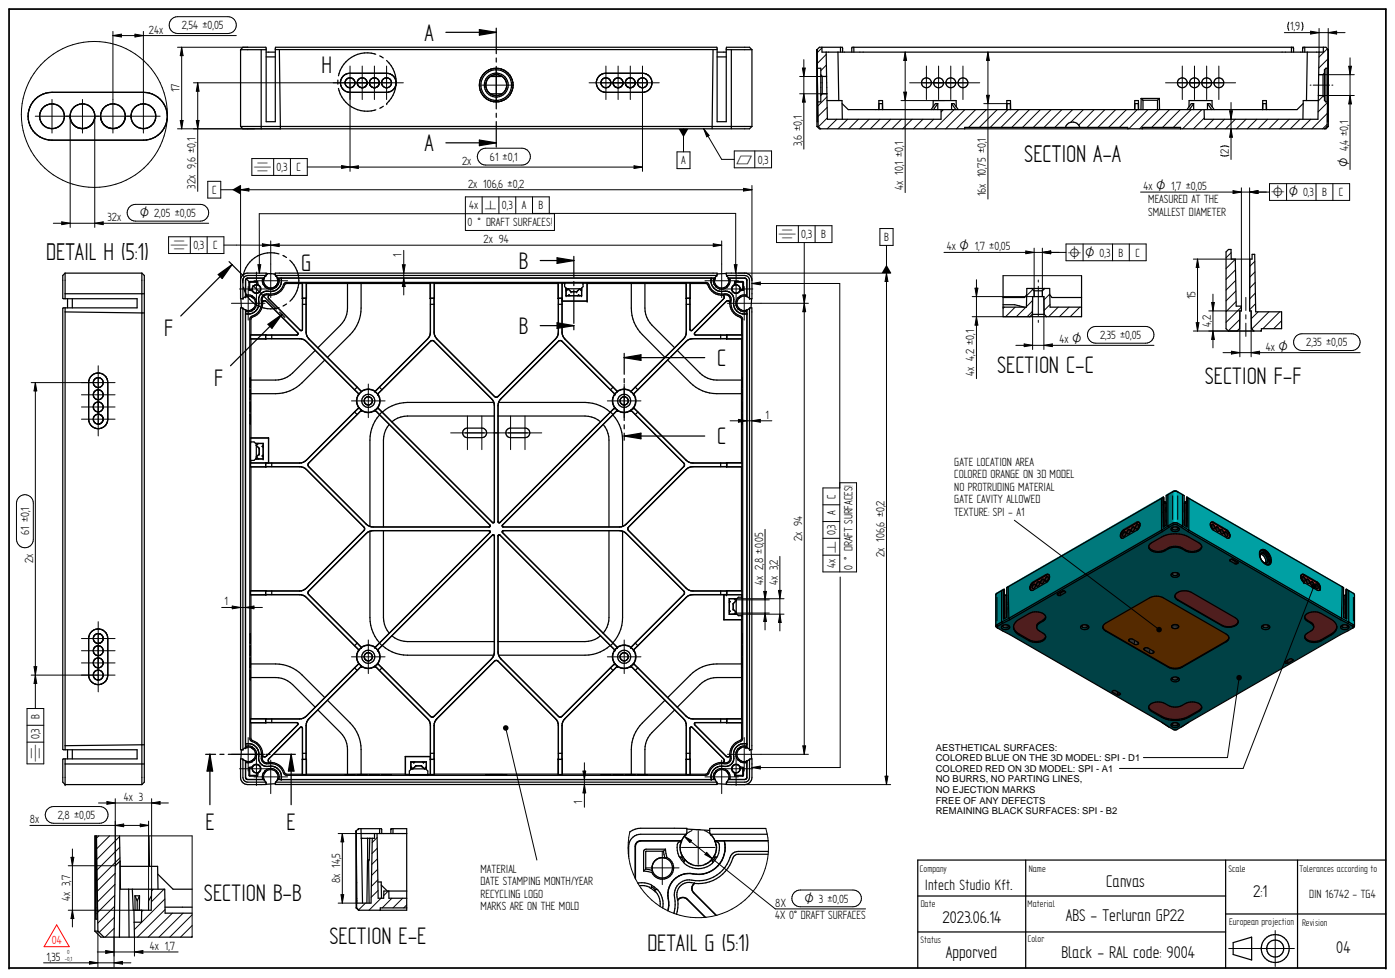
[picture p328: page 1]
SECTION A-A; SECTION C-C; SECTION F-F; SECTION E-E; SECTION B-B; DETAIL G (5:1); O 3 ±0,05 8X 4X 0v DRAFT SURFACES; DETAIL H (5:1); v DRAFT SURFACES!; 4x n 0,3 A B 0 v DRAFT SURFACES!

MEASURED AT THE
SMALLEST DIAMETER

GATE LOCATION AREA
COLORED ORANGE ON 3D MODEL
NO PROTRUDING MATERIAL
GATE CAVITY ALLOWED
TEXTURE: SPI - A1

AESTHETICAL SURFACES:
COLORED BLUE ON THE 3D MODEL: SPI - D1
COLORED RED ON 3D MODEL: SPI - A1
NO BURRS, NO PARTING LINES,
NO EJECTION MARKS
FREE OF ANY DEFECTS
REMAINING BLACK SURFACES: SPI - B2

MATERIAL
DATE STAMPING MONTH/YEAR
RECYCLING LOGO
MARKS ARE ON THE MOLD

Company Intech Studio Kft. | Name Canvas | Scale 2:1 | Tolerances according to DIN 16742 - TG4

Date 2023.06.14 | Material ABS - Terluran GP22

European projection | Revision 04

Status Apporved | Color Black - RAL code: 9004
