intechstudio/grid/Preview/Mechanical/SPACER_Drawing.pdf

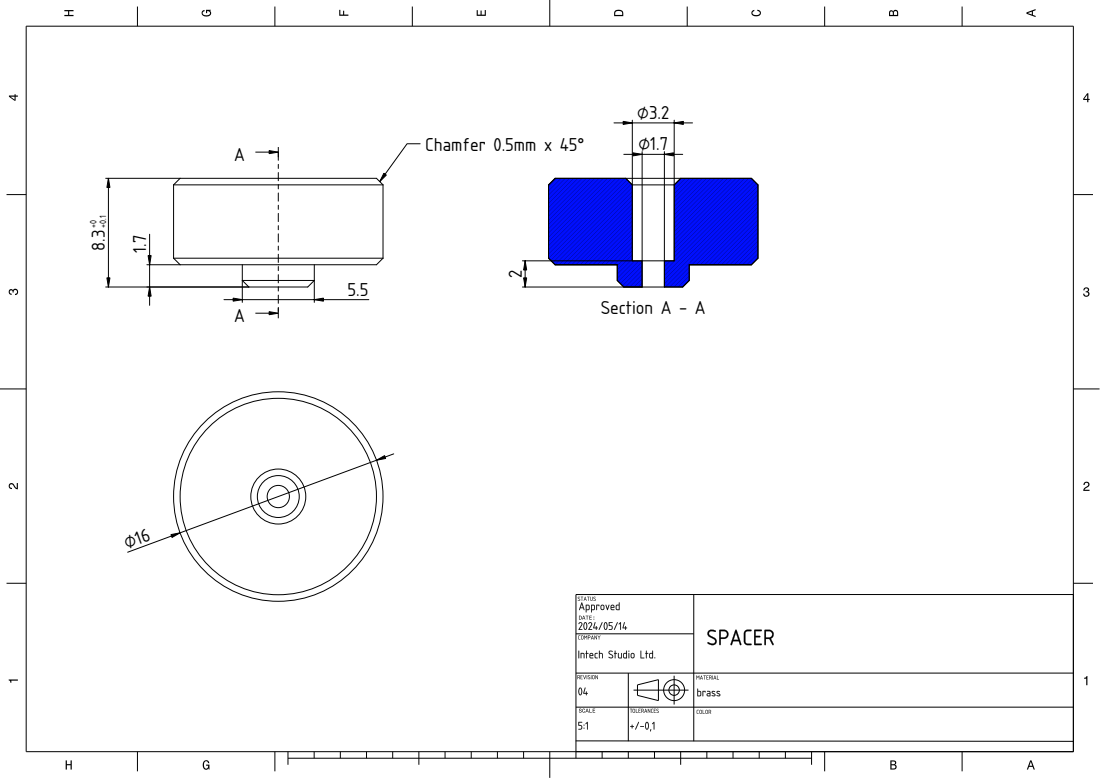
[picture p329: page 1]
Section A - A; Chamfer 0.5mm x 45°
