intechstudio/grid/Preview/Mechanical/STEEL-SPACER_Drawing.pdf

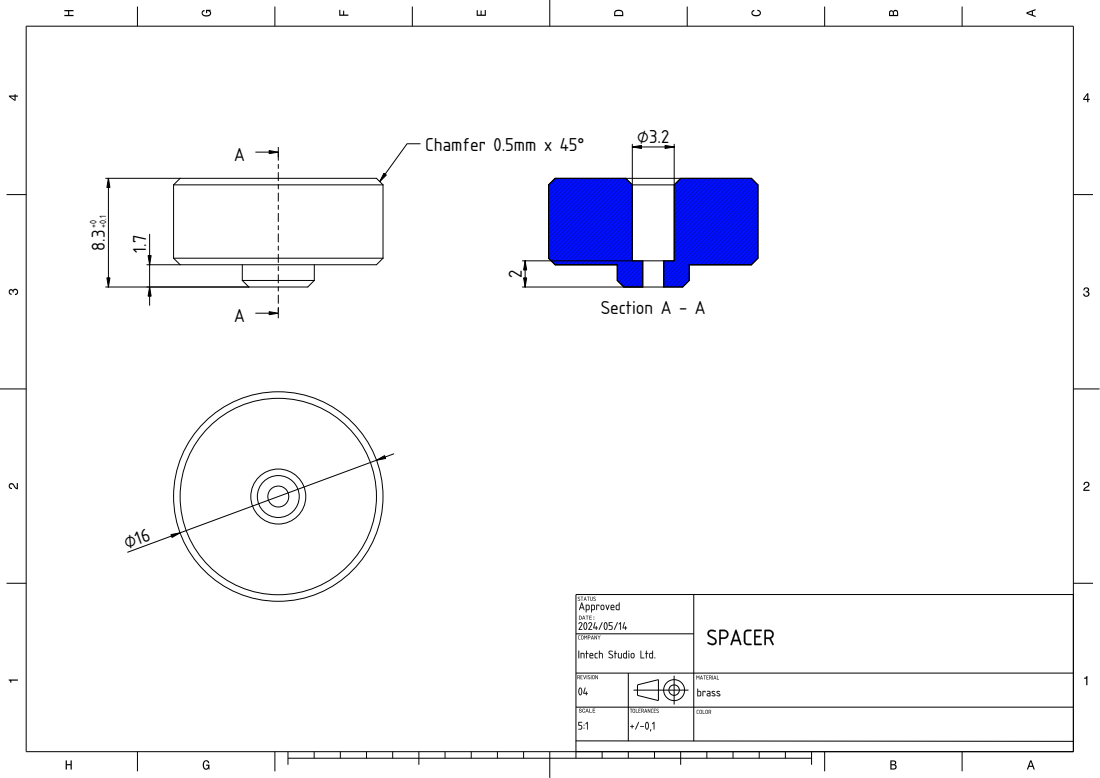
[picture p330: page 1]
Section A - A; Chamfer 0.5mm x 45°
