intechstudio/grid/Preview/Electrical/PCBA-TEK1_Schematic.pdf

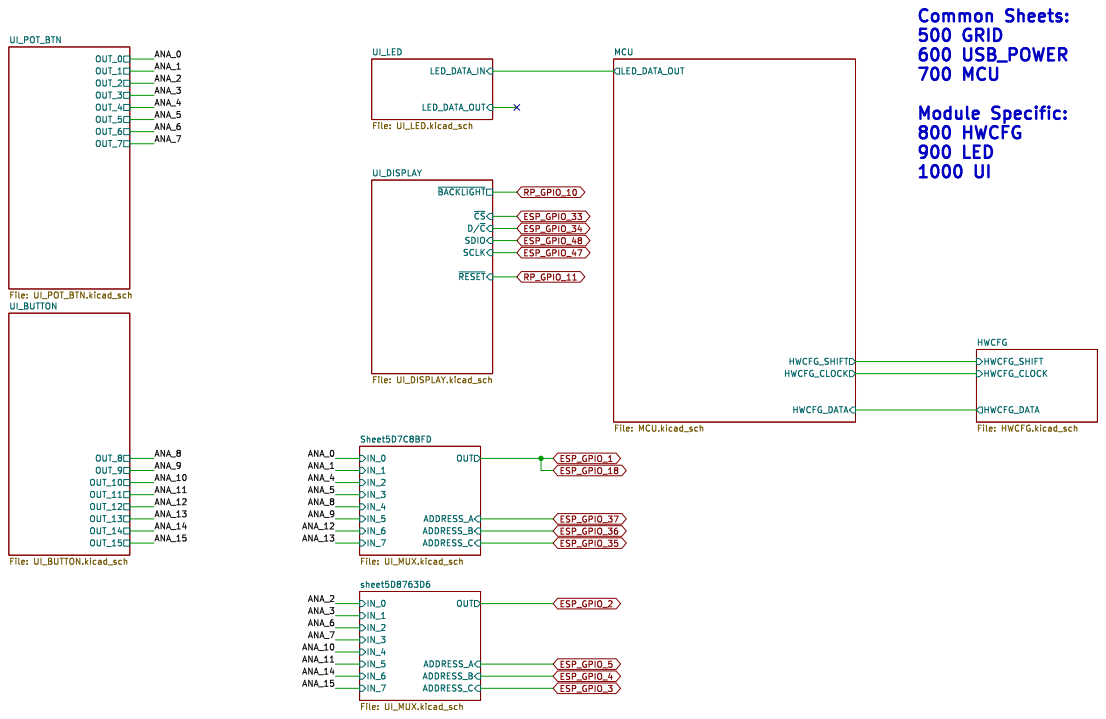
[picture p331: page 1]

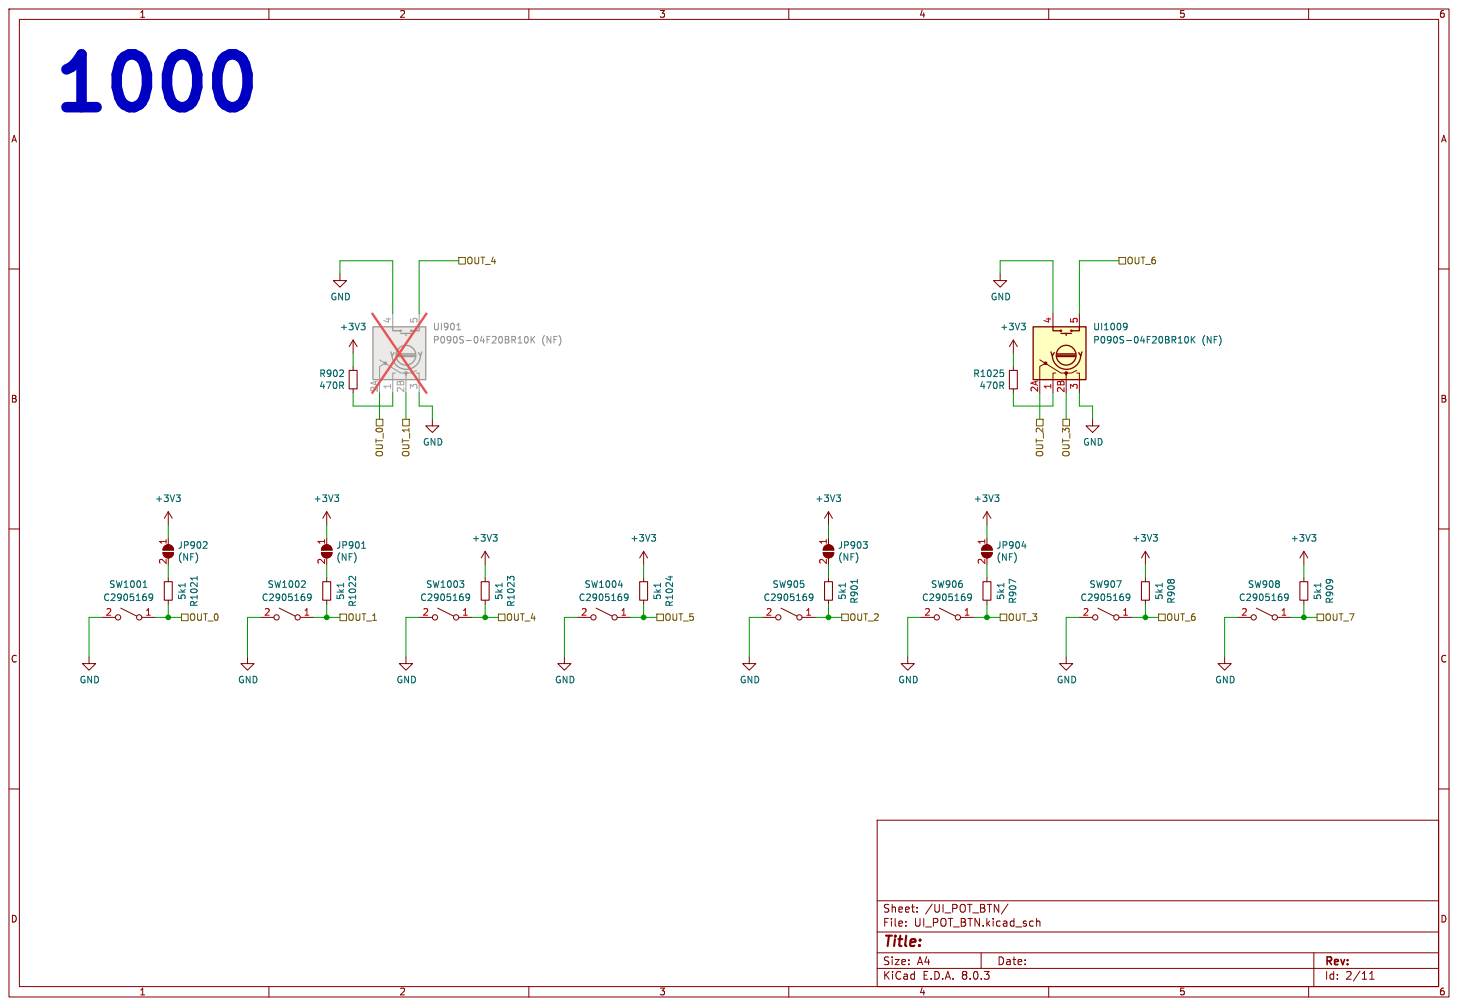
[picture p332: page 2]

Id: 2/11 Title: File: UI_POT_BTN.kicad_sch Sheet: /UI_POT_BTN/ GND

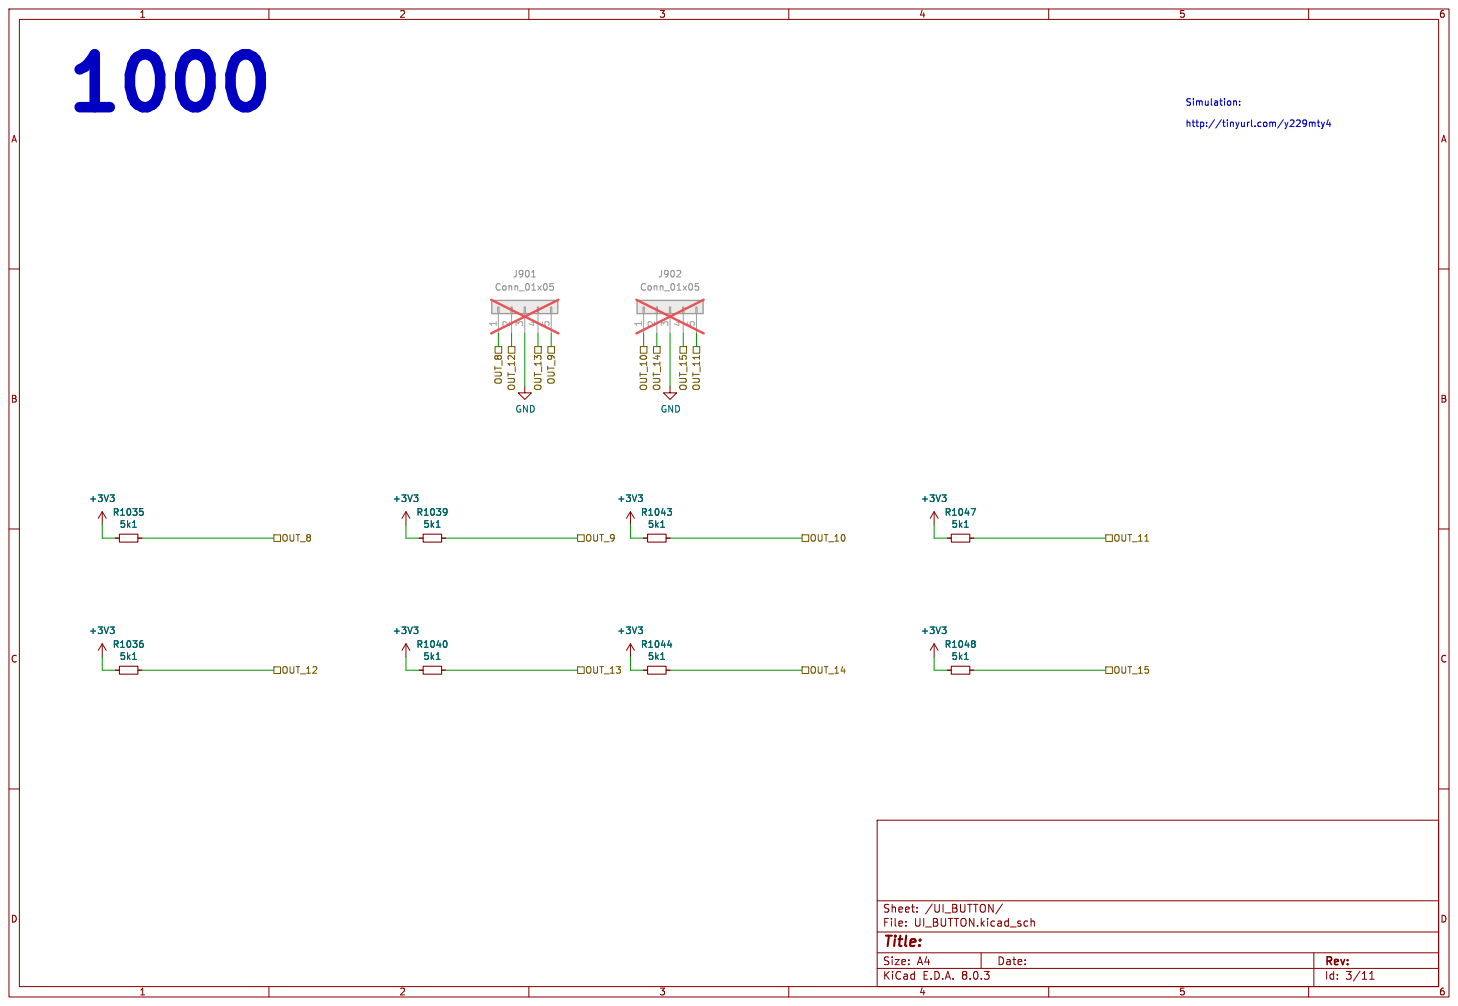
[picture p333: page 3]

1000 Simulation: http://tinyurl.com/y229mty4 +3V3 R1043

Id: 3/11 Title: File: UI_BUTTON.kicad_sch Sheet: /UI_BUTTON/ R1047

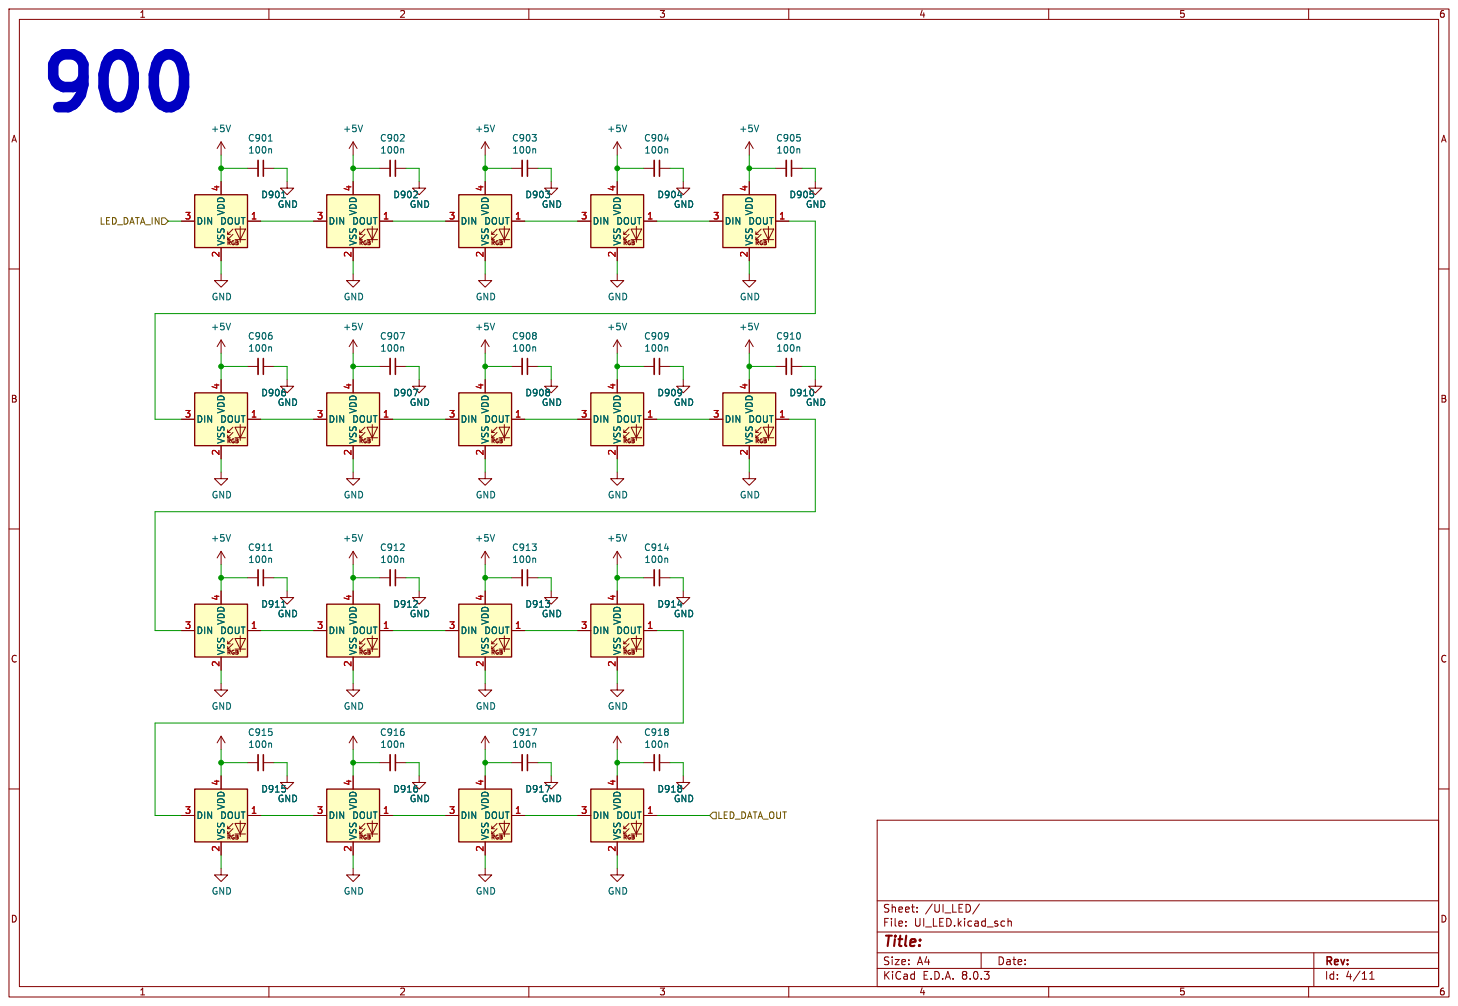
[picture p334: page 4]

Id: 4/11 Title: File: UI_LED.kicad_sch Sheet: /UI_LED/

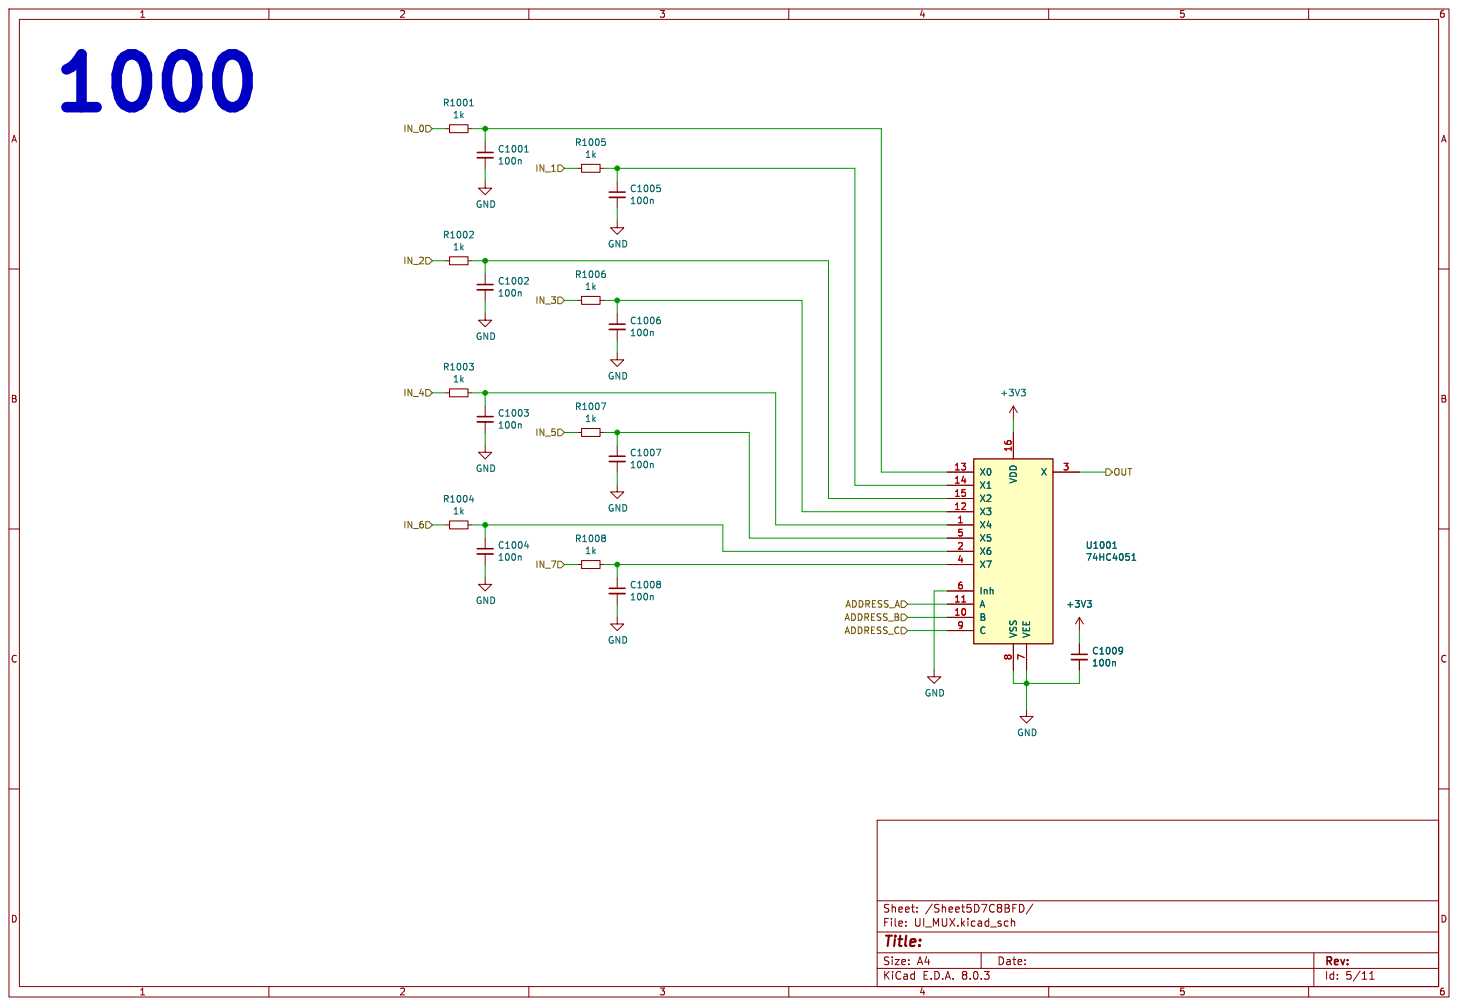
[picture p335: page 5]

Id: 5/11 Title: File: UI_MUX.kicad_sch Sheet: /Sheet5D7C8BFD/ R1004

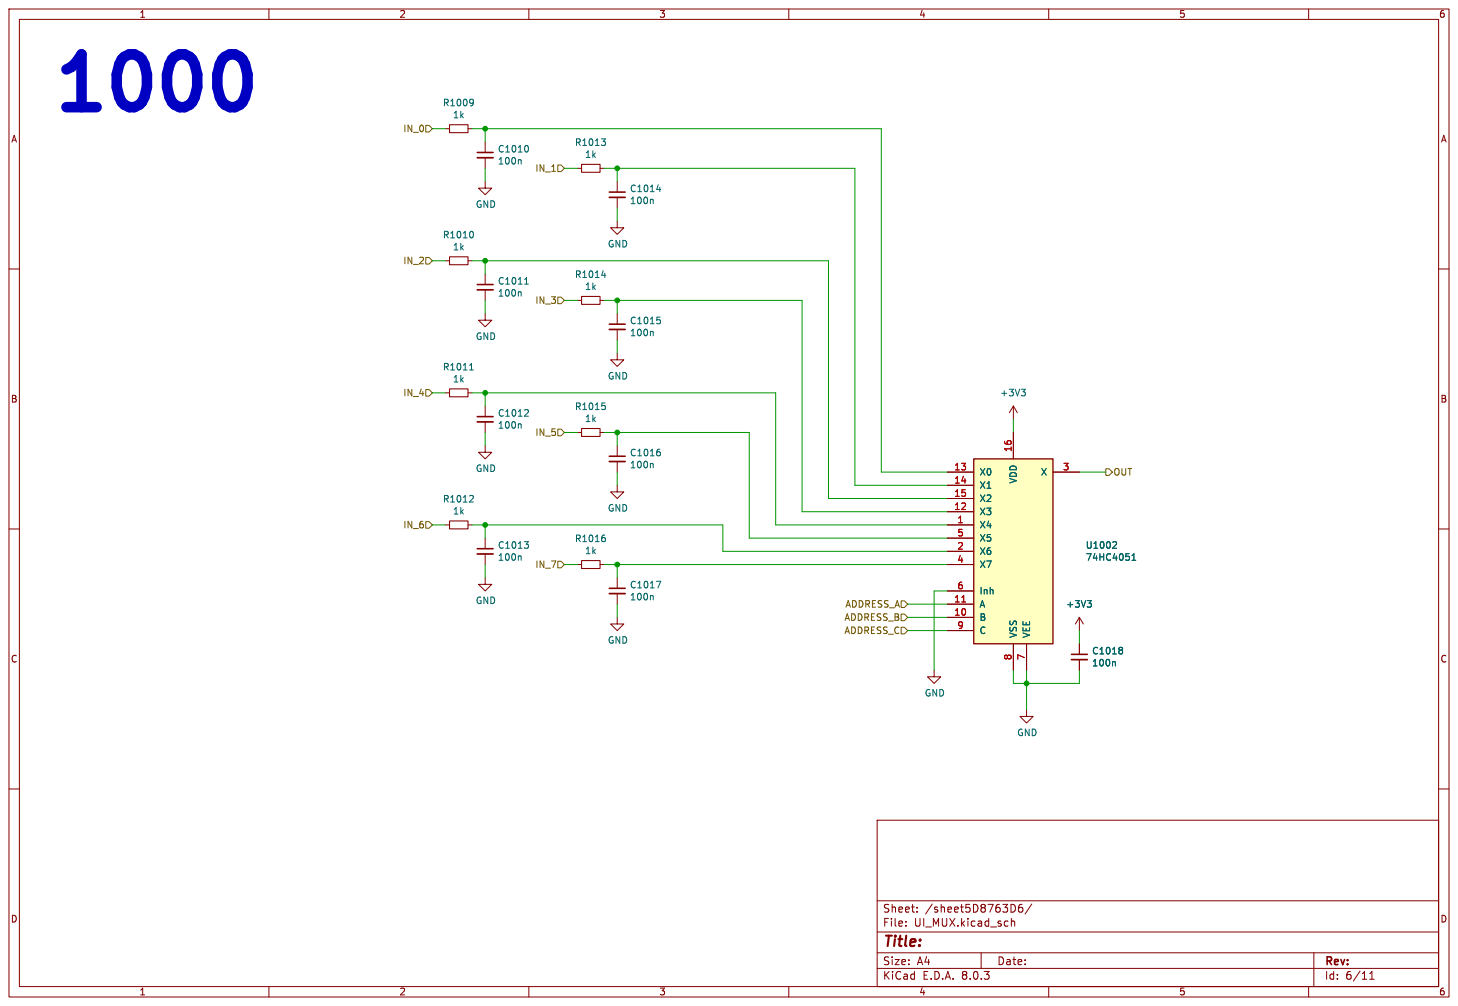
[picture p336: page 6]

Id: 6/11 Title: File: UI_MUX.kicad_sch Sheet: /sheet5D8763D6/ R1012

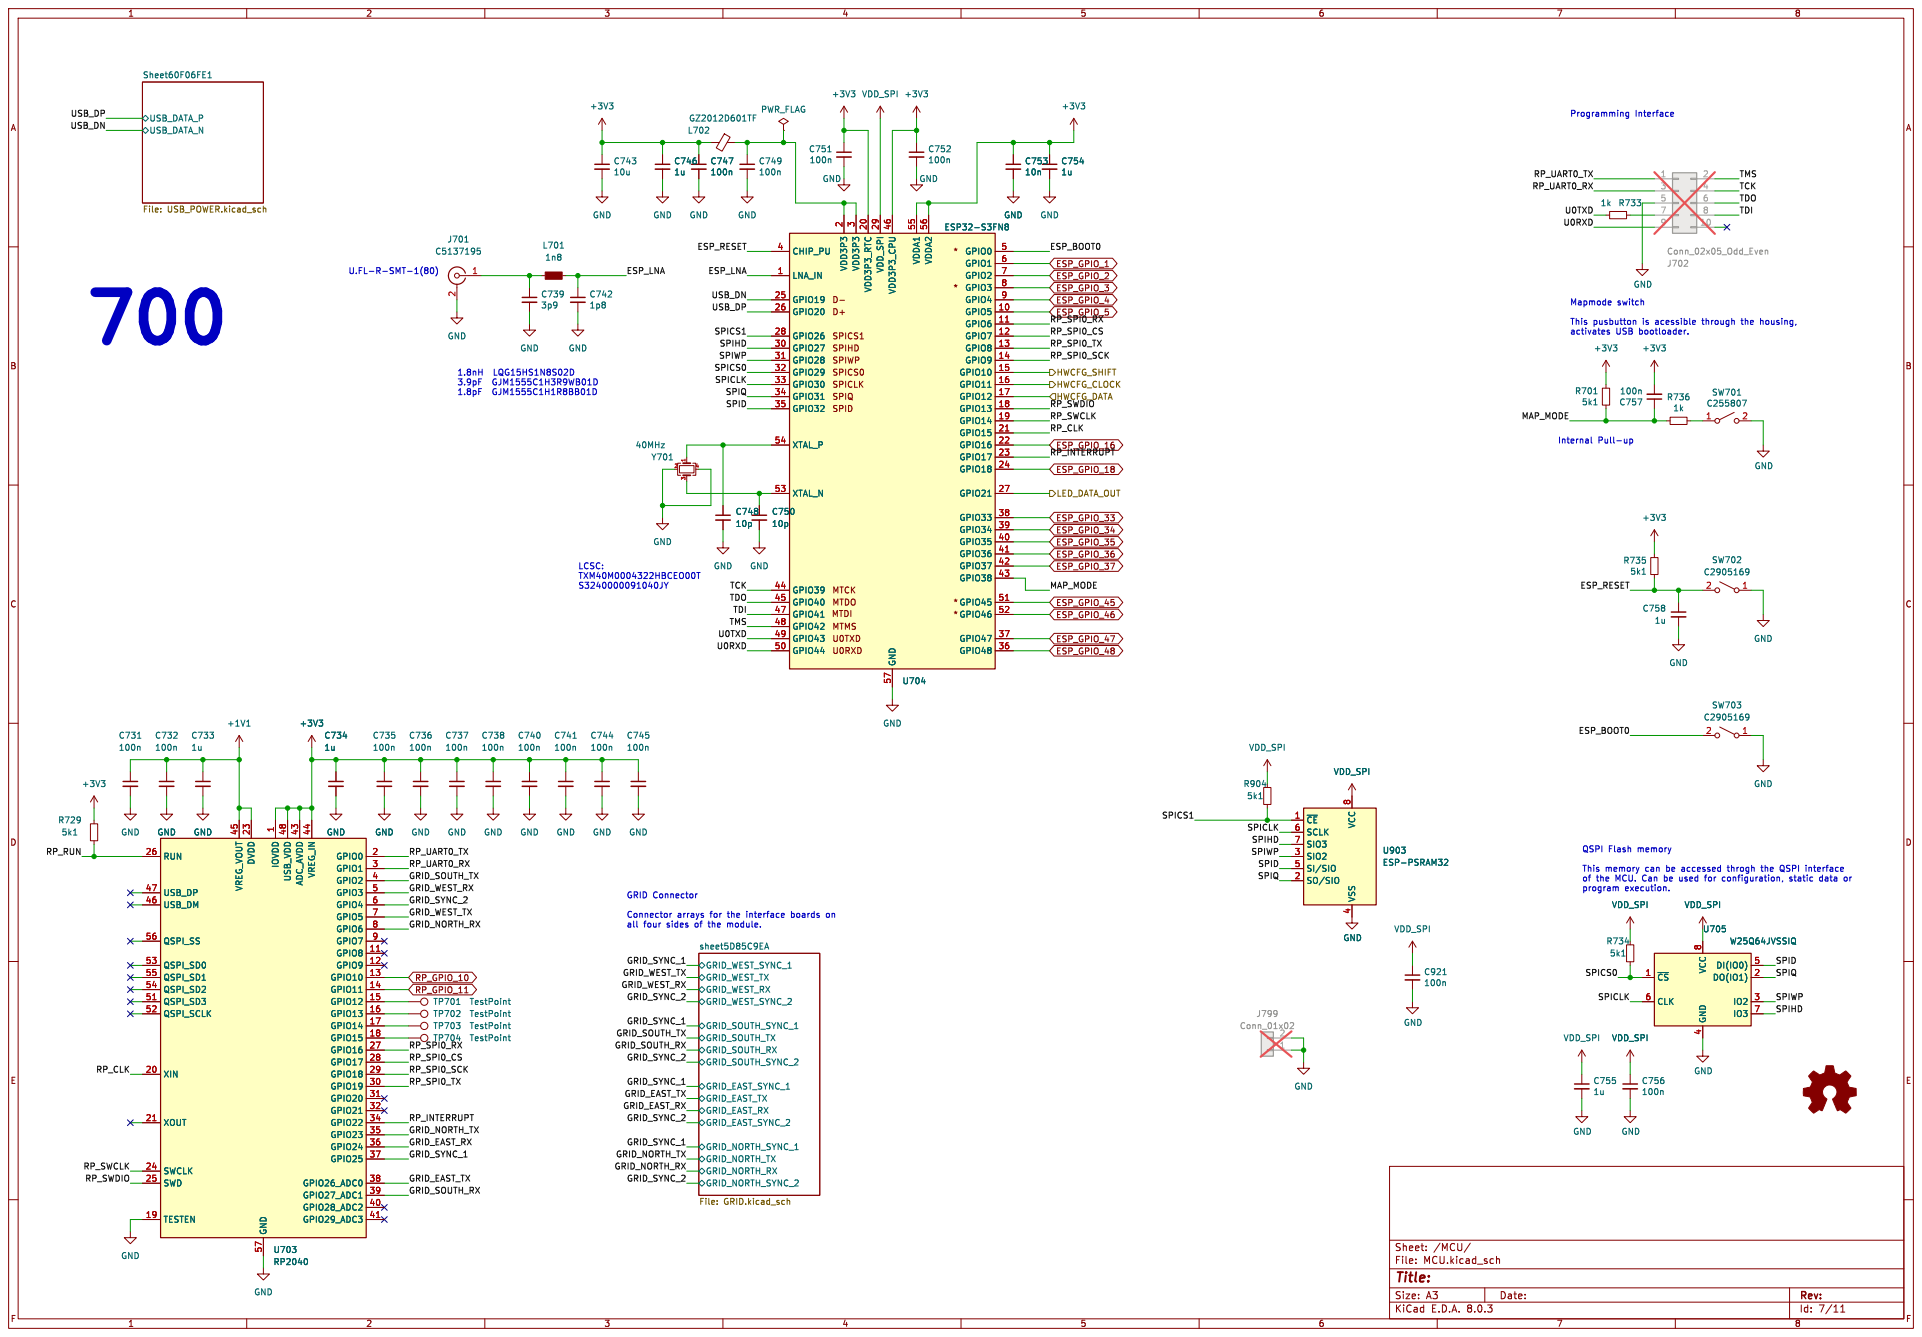
[picture p337: page 7]

4 SI/SIO 5 SCLK 6 SIO3 7 VCC

1 GPIO8 11 GPIO9 12 GPIO10 13 GPIO11 14 GPIO12 15 GPIO13 16 GPIO14 17 GPIO15 18 TESTEN 19 GPIO0 2 XIN 20 XOUT 21 DVDD 23 SWCLK 24 SWD 25 RUN 26 GPIO16 27 GPIO17 28 GPIO18 29 GPIO1 3 GPIO19 30 GPIO20 31 GPIO21 32 GPIO22 34 GPIO23 35 GPIO24 36 GPIO25 37 GPIO26_ADC0 38 GPIO27_ADC1 39 GPIO2 4 GPIO28_ADC2 40 GPIO29_ADC3 41 ADC_AVDD 43 VREG_IN 44 VREG_VOUT 45 USB_DM 46 USB_DP 47 USB_VDD 48 GPIO3 5 QSPI_SD3 51 QSPI_SCLK 52 QSPI_SD0 53 QSPI_SD2 54 QSPI_SD1 55 QSPI_SS 56 GND 57 GPIO4 6 GPIO5 7 GPIO6 8 GPIO7 9 U703 RP2040 GND

1 GPIO8 11 GPIO9 12 GPIO10 13 GPIO11 14 GPIO12 15 GPIO13 16 GPIO14 17 GPIO15 18 TESTEN 19 GPIO0 2 XIN 20 XOUT 21 DVDD 23 SWCLK 24 SWD 25 RUN 26 GPIO16 27 GPIO17 28 GPIO18 29 GPIO1 3 GPIO19 30 GPIO20 31 GPIO21 32 GPIO22 34 GPIO23 35 GPIO24 36 GPIO25 37 GPIO26_ADC0 38 GPIO27_ADC1 39 GPIO2 4 GPIO28_ADC2 40 GPIO29_ADC3 41 ADC_AVDD 43 VREG_IN 44 VREG_VOUT 45 USB_DM 46 USB_DP 47 USB_VDD 48 GPIO3 5 QSPI_SD3 51 QSPI_SCLK 52 QSPI_SD0 53 QSPI_SD2 54 QSPI_SD1 55 QSPI_SS 56 GND 57 GPIO4 6 GPIO5 7 GPIO6 8 GPIO7 9GND

all four sides of the module.

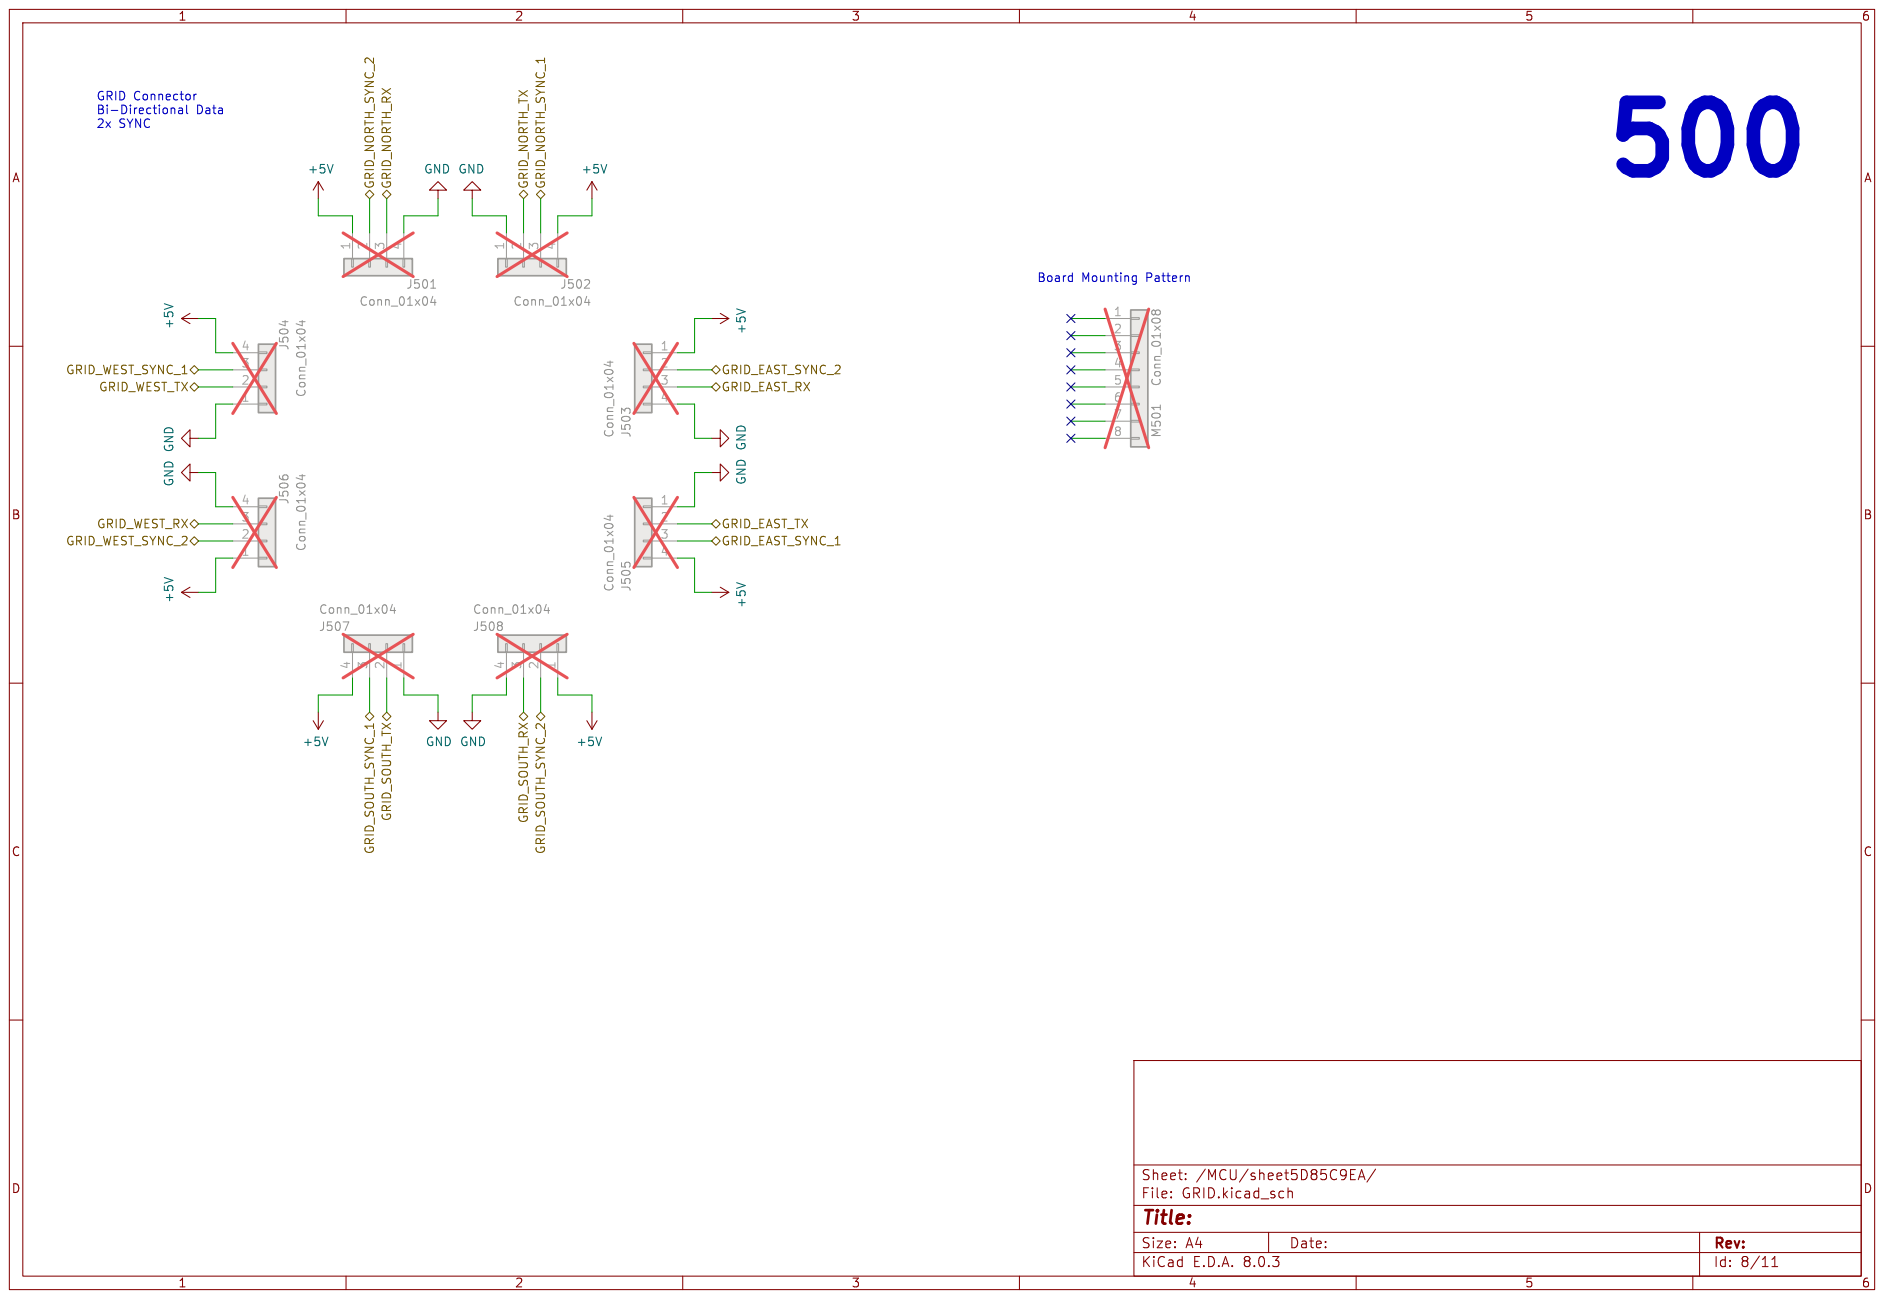
[picture p338: page 8]

4 J501 Conn_01x04 GRID_WEST_TX GRID_EAST_SYNC_1 GRID_EAST_SYNC_2 GRID_EAST_RX GRID_EAST_TX GRID_SOUTH_SYNC_1 GRID_SOUTH_SYNC_2 GRID_SOUTH_TX GRID_SOUTH_RX GRID_WEST_SYNC_1 GRID_WEST_RX GRID_WEST_SYNC_2 GRID_NORTH_SYNC_2 GRID_NORTH_RX GRID_NORTH_TX GRID_NORTH_SYNC_1 Board Mounting Pattern GRID Connector Bi-Directional Data

Id: 8/11 Title: File: GRID.kicad_sch Sheet: /MCU/sheet5D85C9EA/

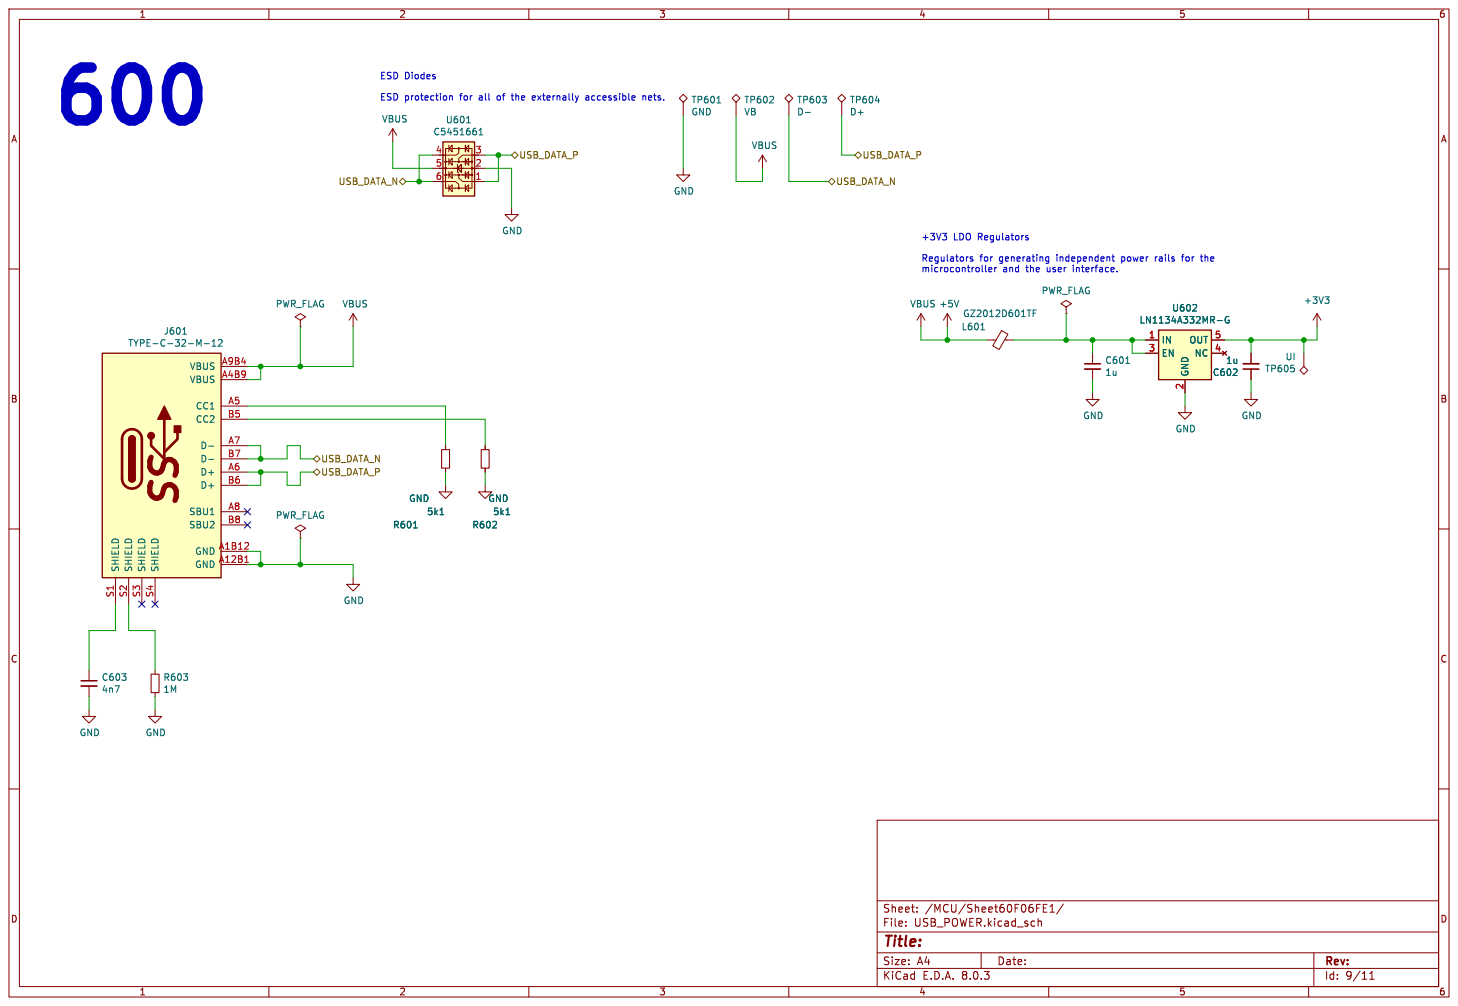
[picture p339: page 9]

Id: 9/11 Title: File: USB_POWER.kicad_sch Sheet: /MCU/Sheet60F06FE1/

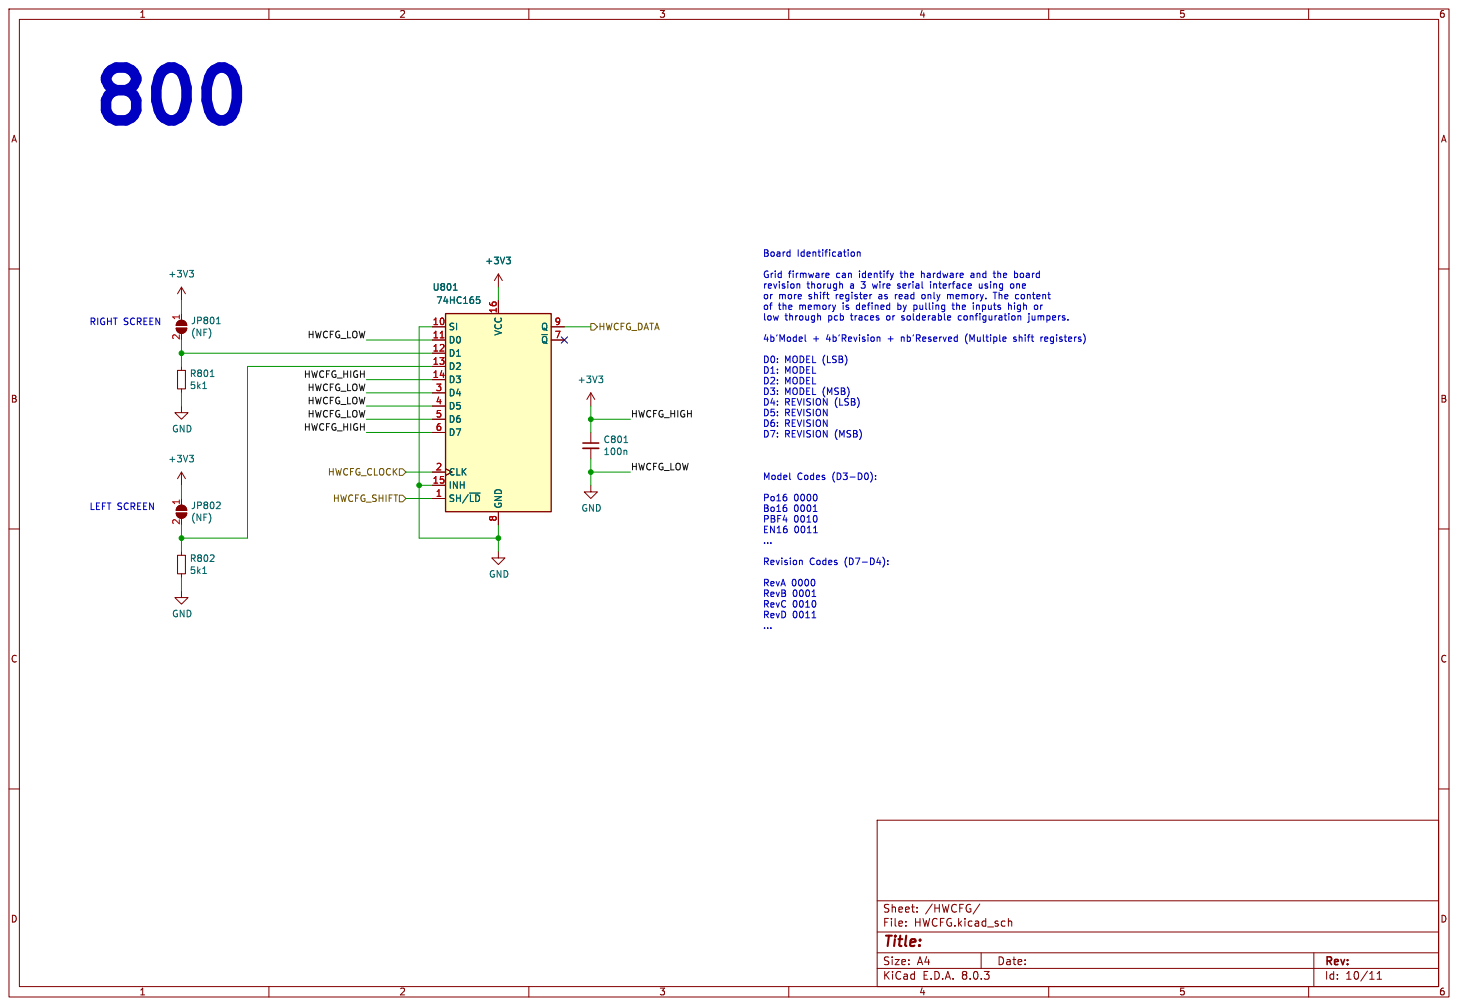
[picture p340: page 10]

D6: REVISION
D7: REVISION (MSB) Model Codes (D3-D0): Po16 0000 Bo16 0001 PBF4 0010 EN16 0011

... Revision Codes (D7-D4): RevA 0000 RevB 0001 RevC 0010 RevD 0011

Id: 10/11 Title: File: HWCFG.kicad_sch Sheet: /HWCFG/

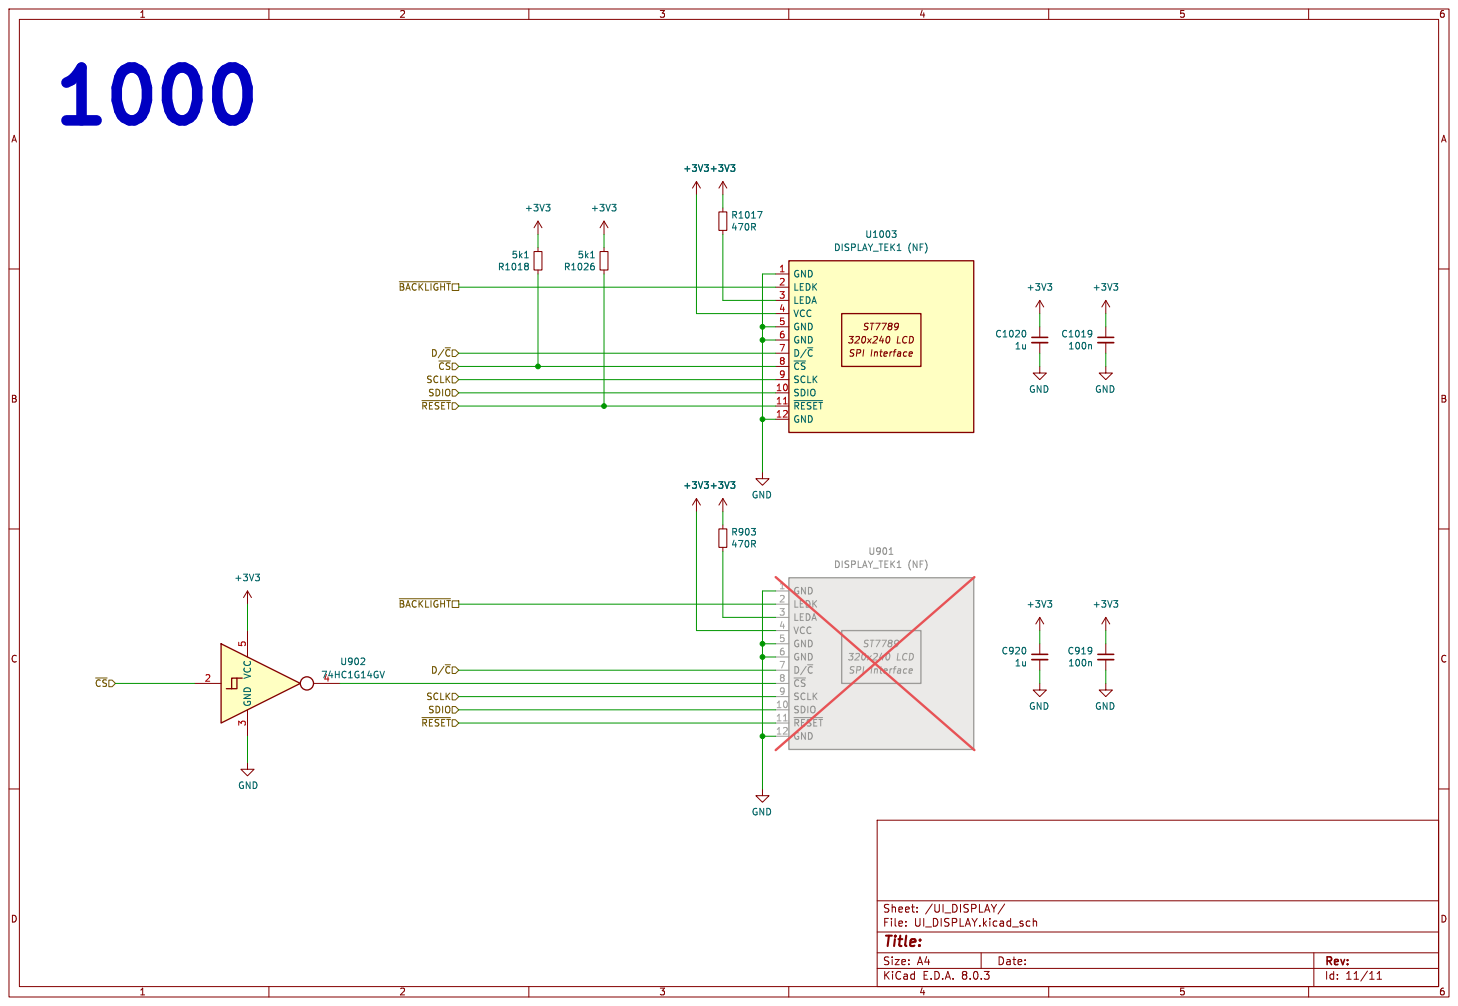
[picture p341: page 11]
