intechstudio/grid/Preview/Electrical/PCBA-INTERFACE_Schematic.pdf

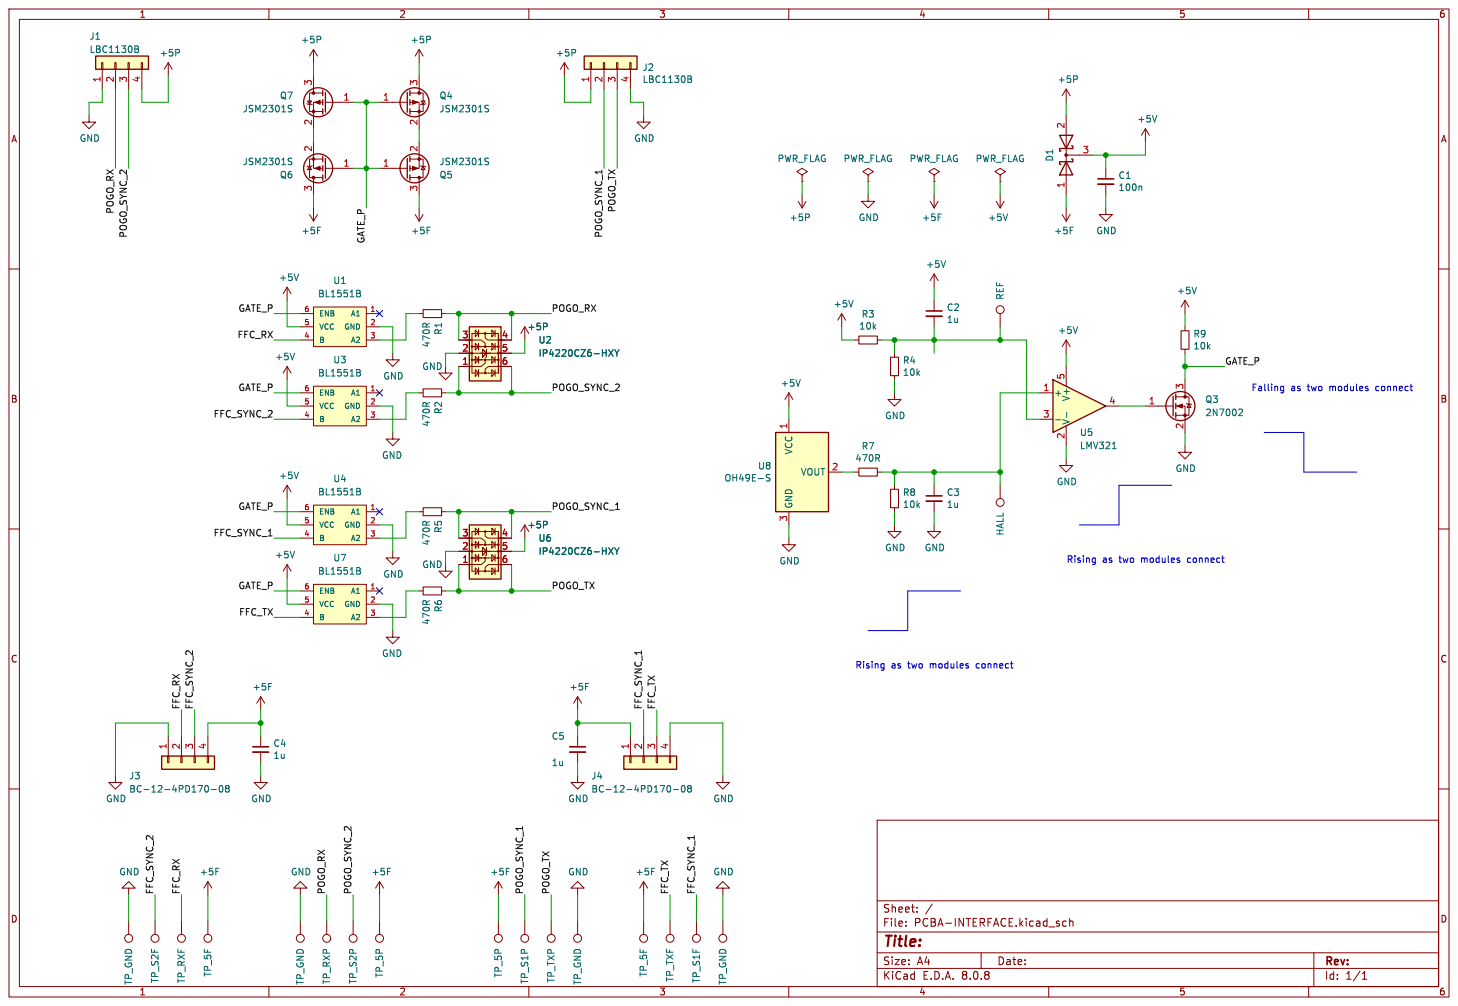
[picture p352: page 1]
