intechstudio/grid/Preview/Electrical/PCBA-PBF4-PLATE_Schematic.pdf

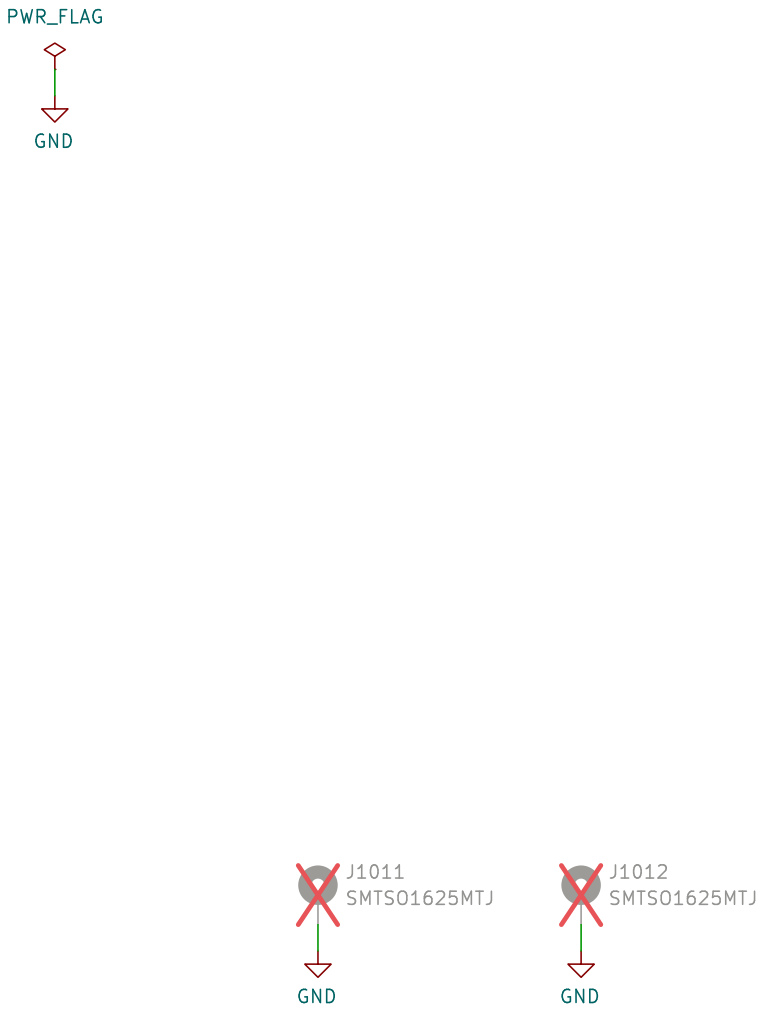
[picture p353: page 1]
