intechstudio/grid/Preview/Electrical/PCBA-PBF4-SPACER_Schematic.pdf

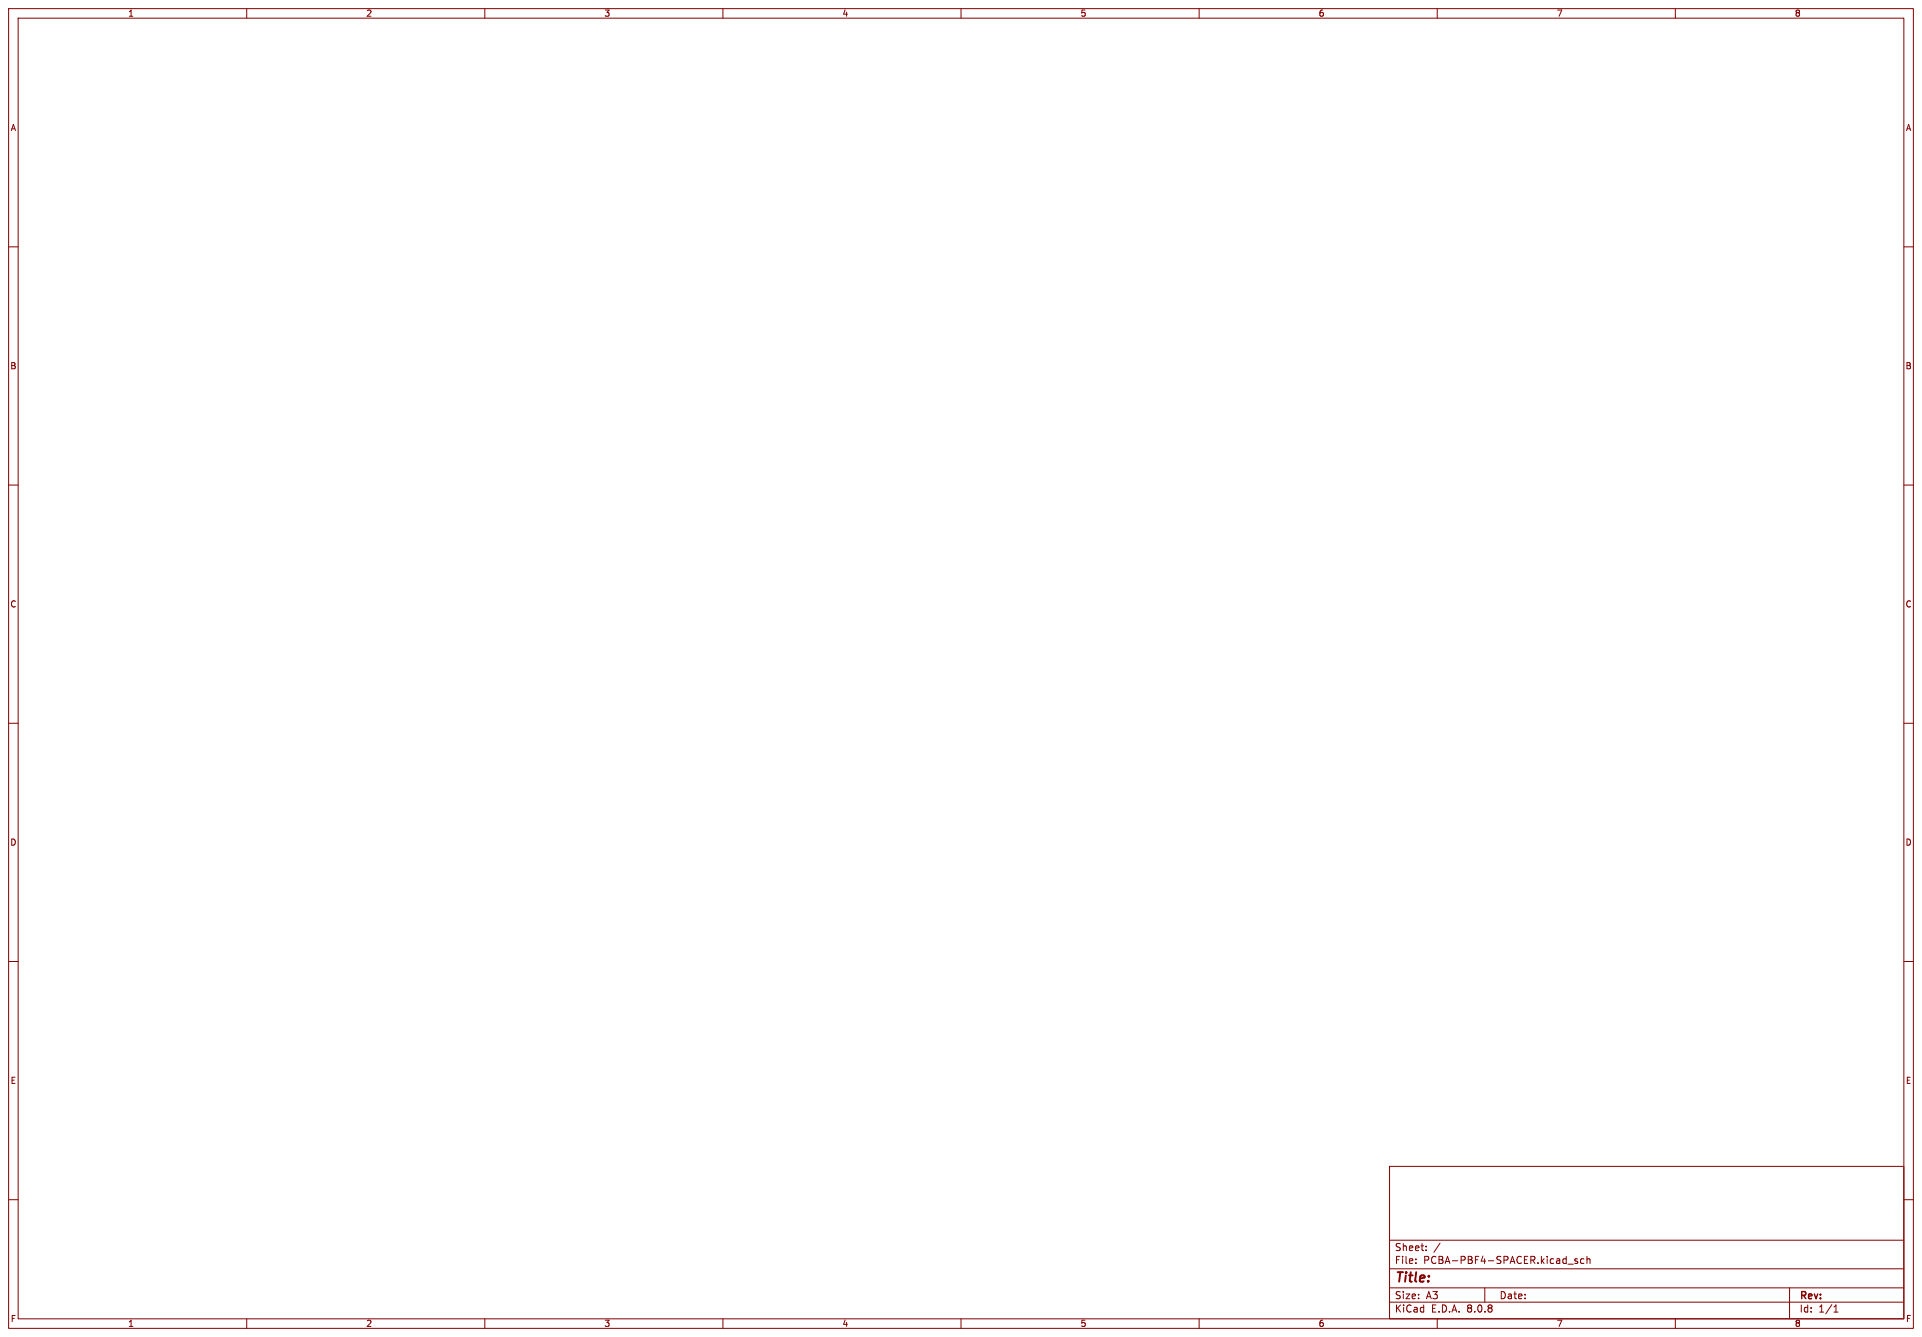
[picture p354: page 1]
