intechstudio/grid/Preview/Electrical/PCBA-VSNX-LCDMOUNT_Schematic.pdf

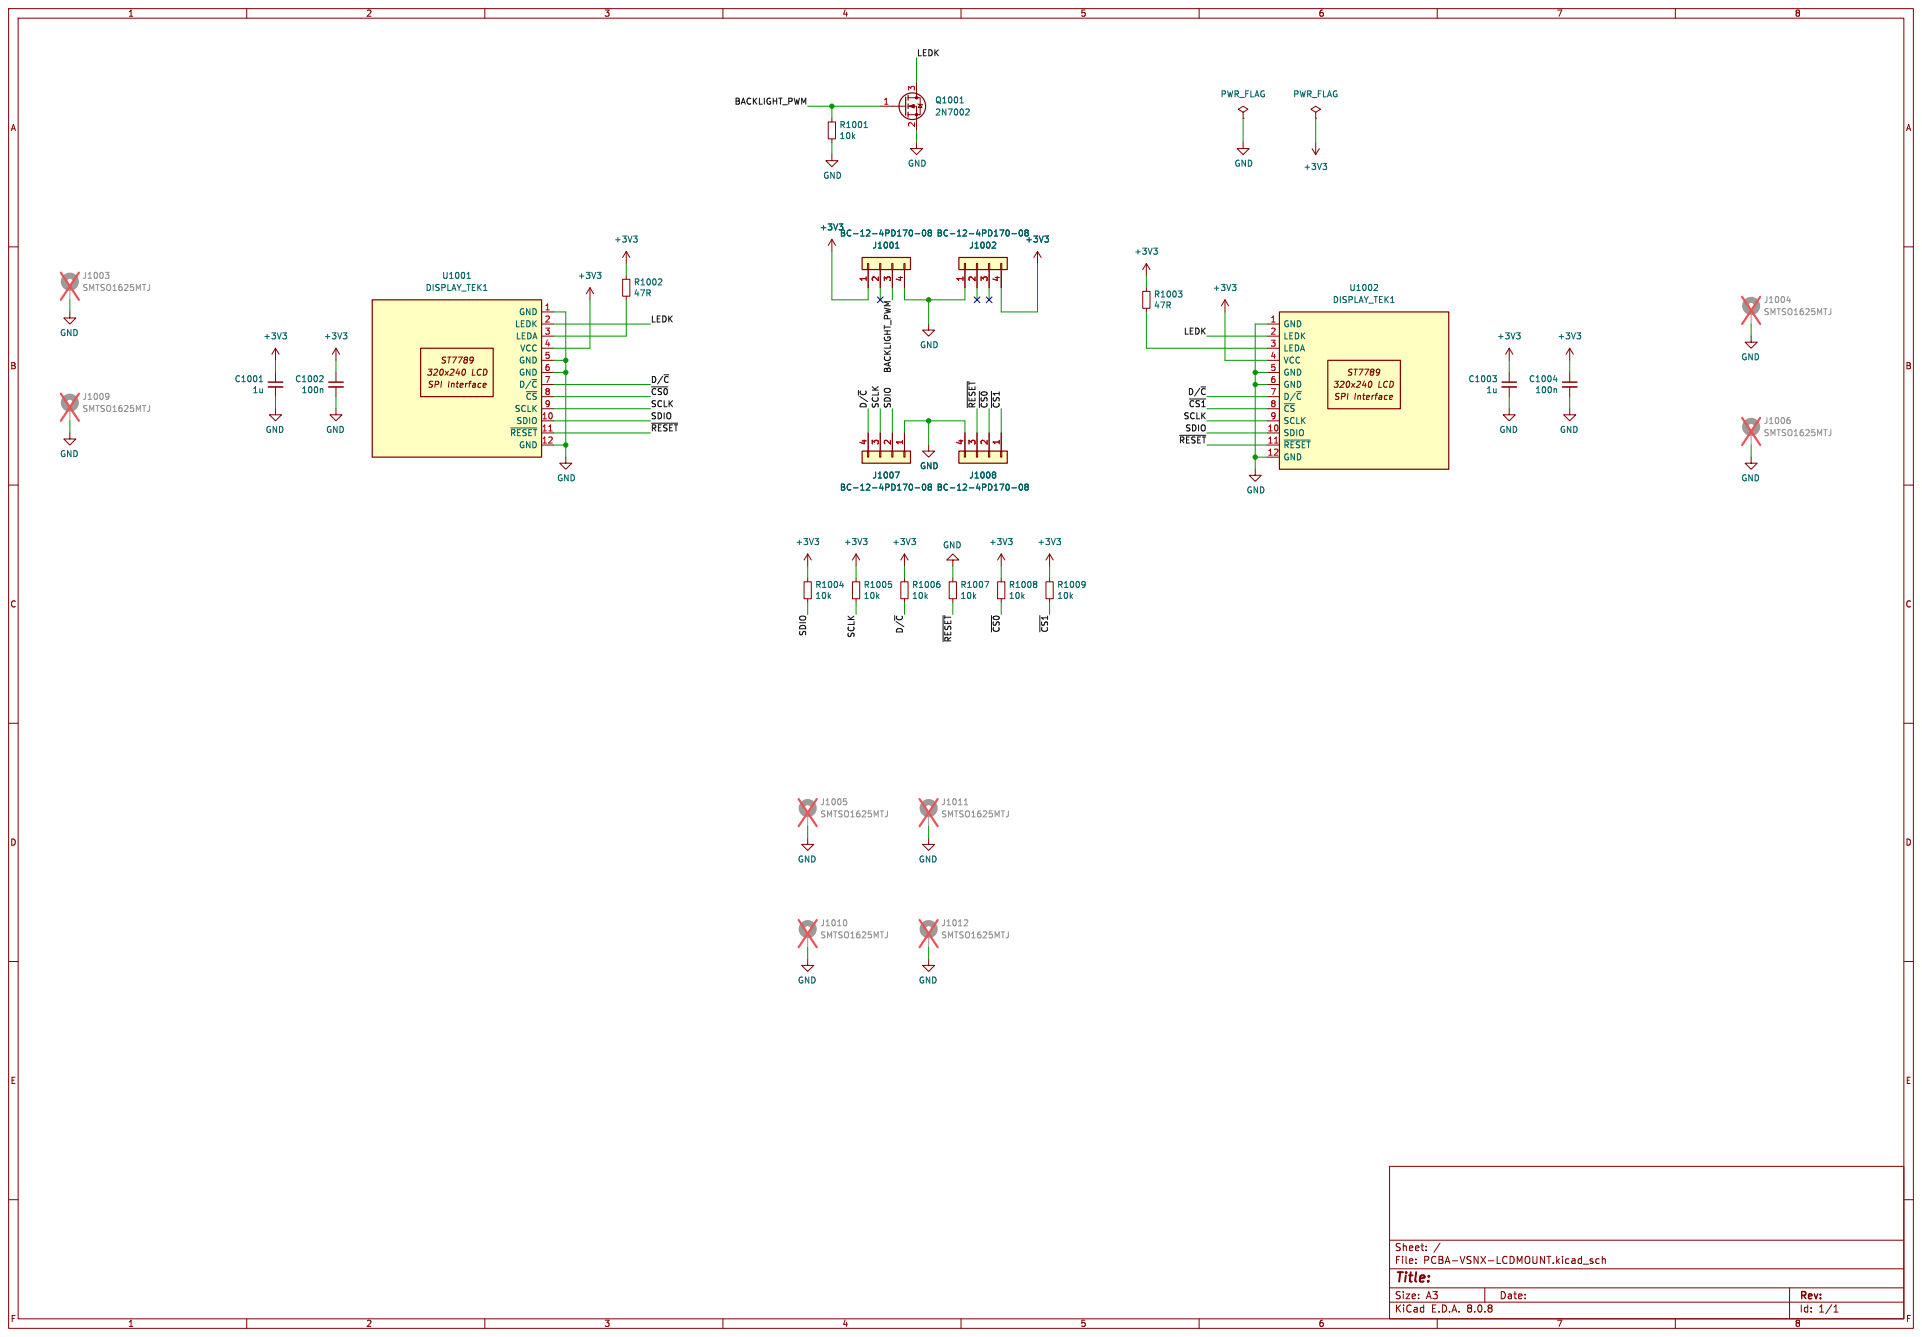
[picture p355: page 1]
