intechstudio/grid/Preview/Electrical/PCBA-VSNX-SPACER_Schematic.pdf

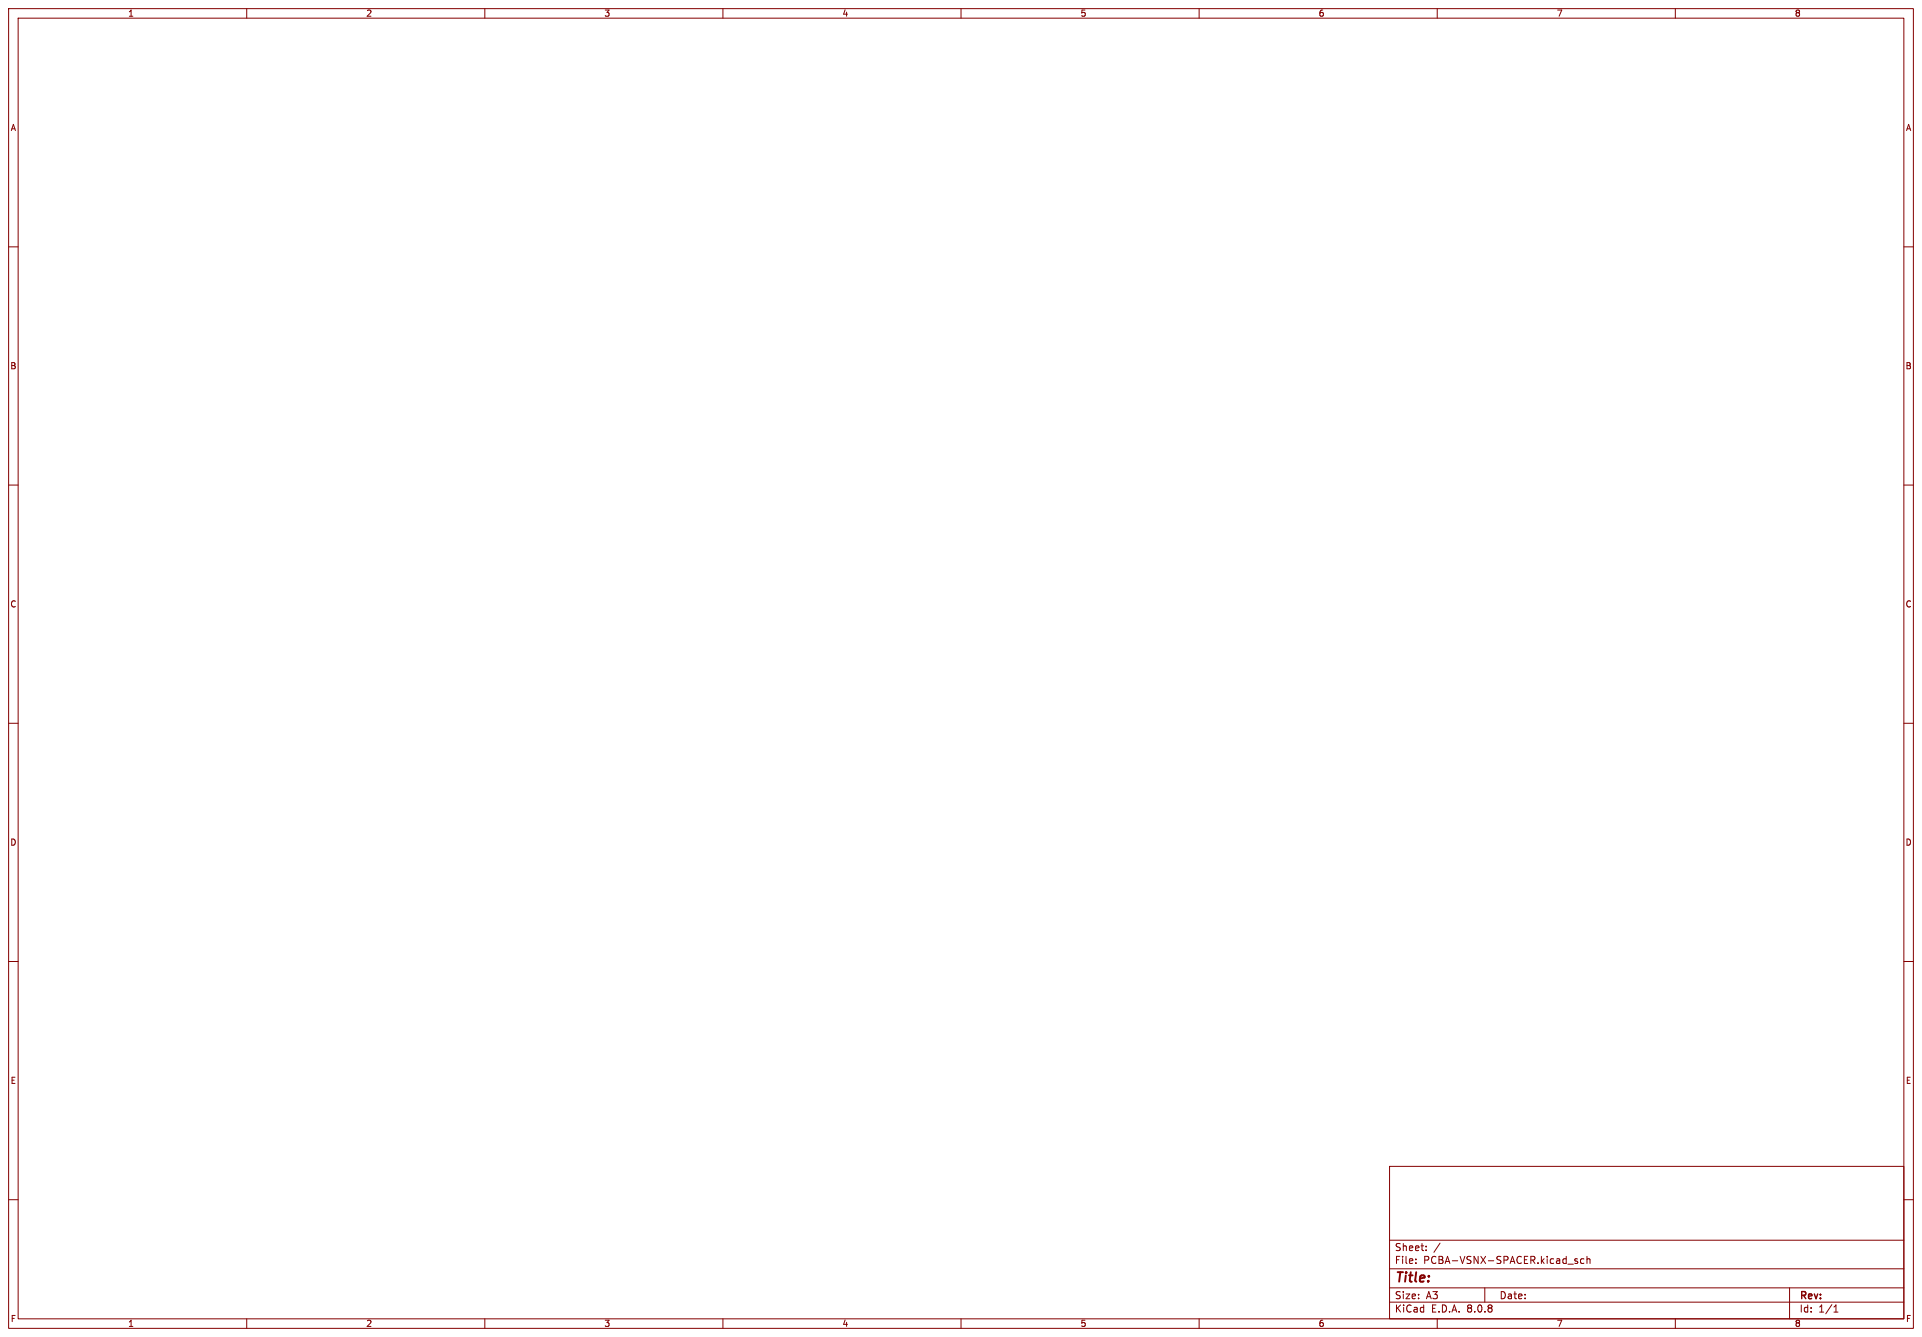
[picture p356: page 1]
