intechstudio/grid/Preview/Mechanical/ PLASTIC-SPACER_Drawing.pdf

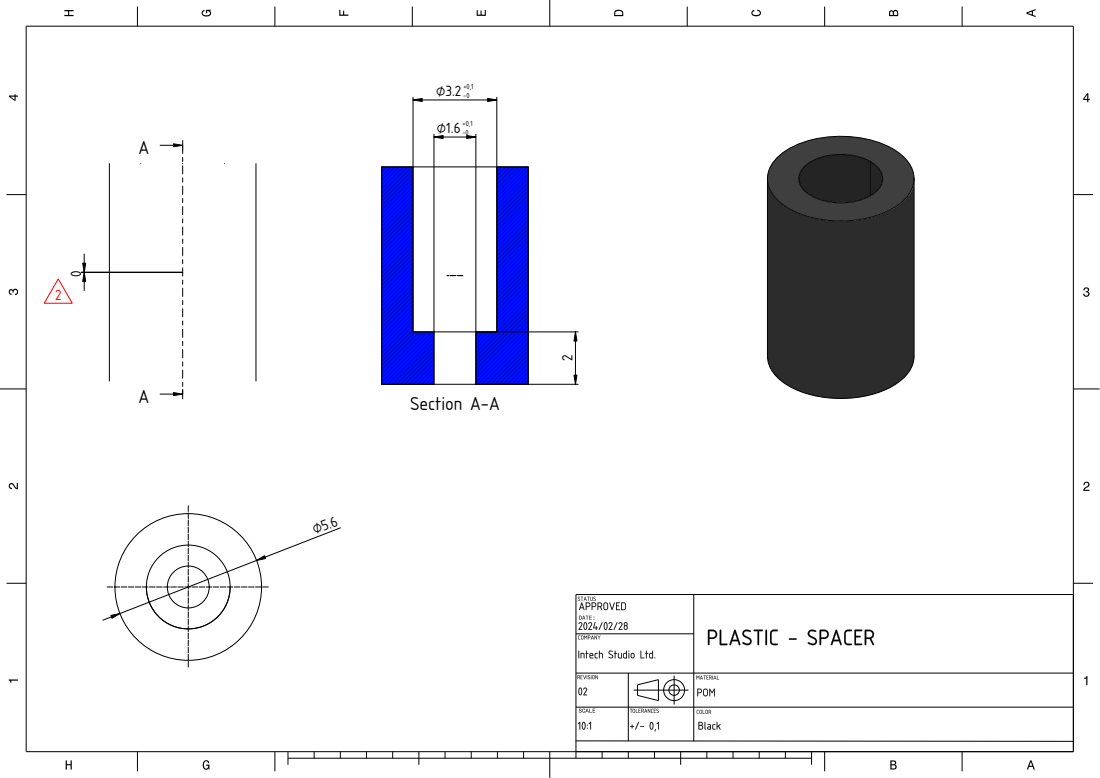
[picture p357: page 1]
Section A-A
