intechstudio/grid/Preview/Mechanical/BU16_dxf.pdf

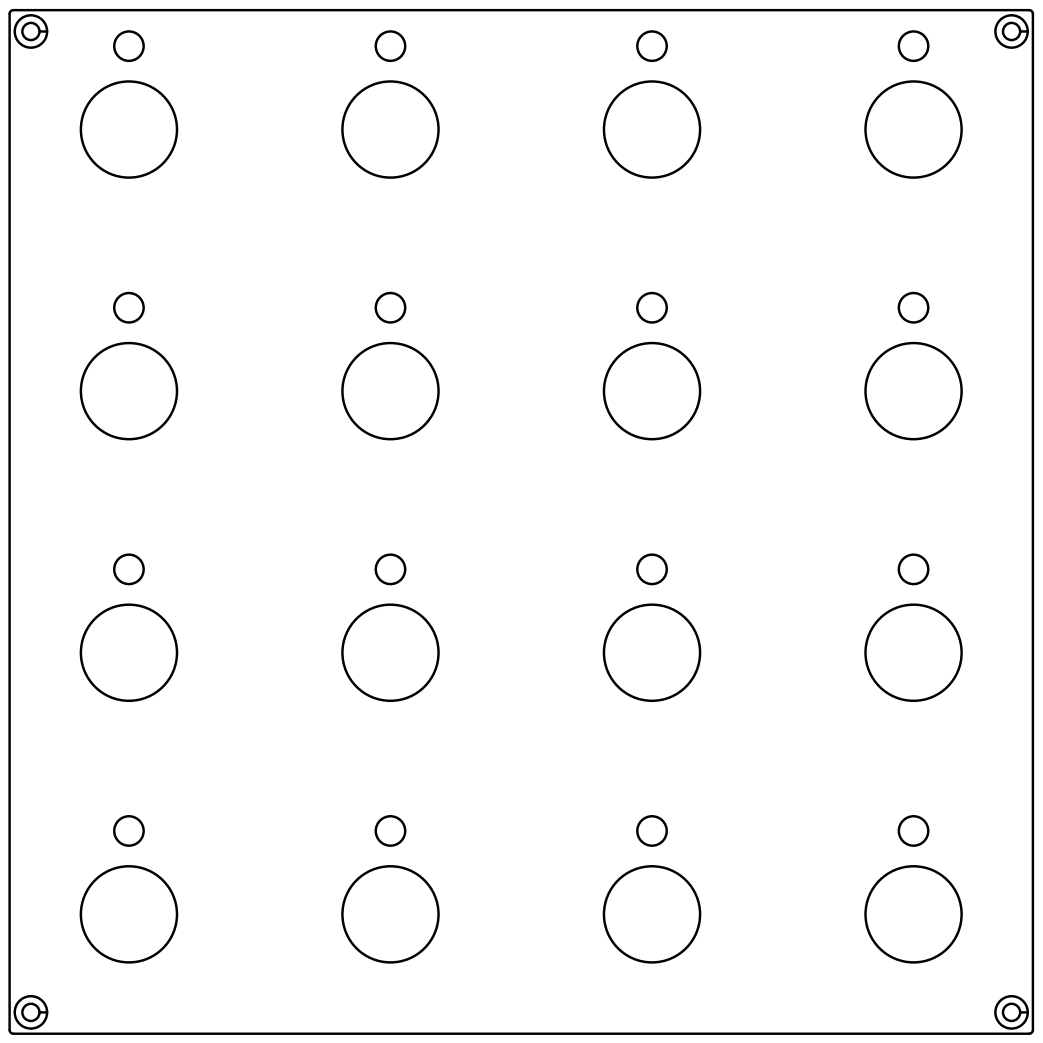
[picture p359: page 1]
