intechstudio/grid/Preview/Mechanical/EF44_dxf.pdf

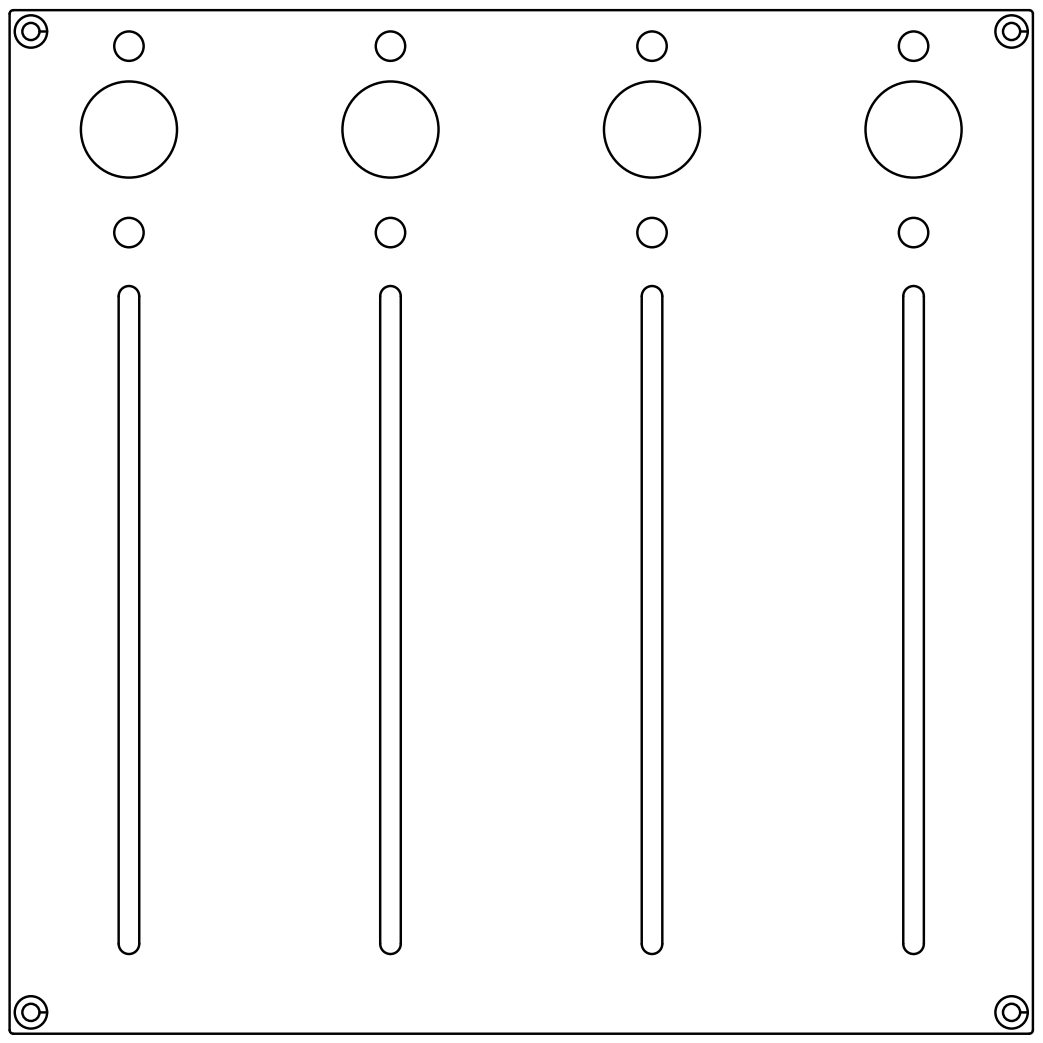
[picture p360: page 1]
