intechstudio/grid/Preview/Mechanical/FRONTPANEL-SHEET-VSN2_dxf.pdf

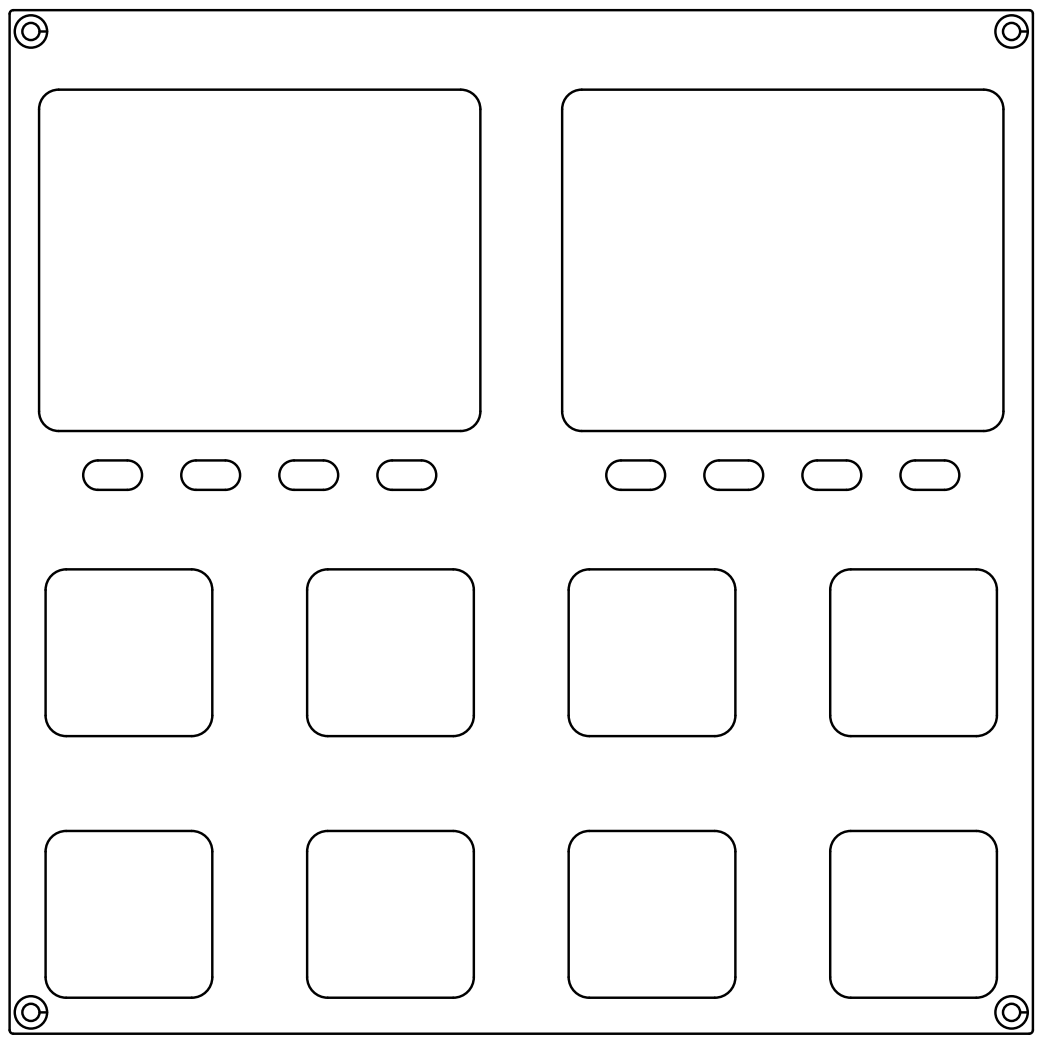
[picture p361: page 1]
