intechstudio/grid/Preview/Mechanical/KNOB-TEK2_Drawing.pdf

A

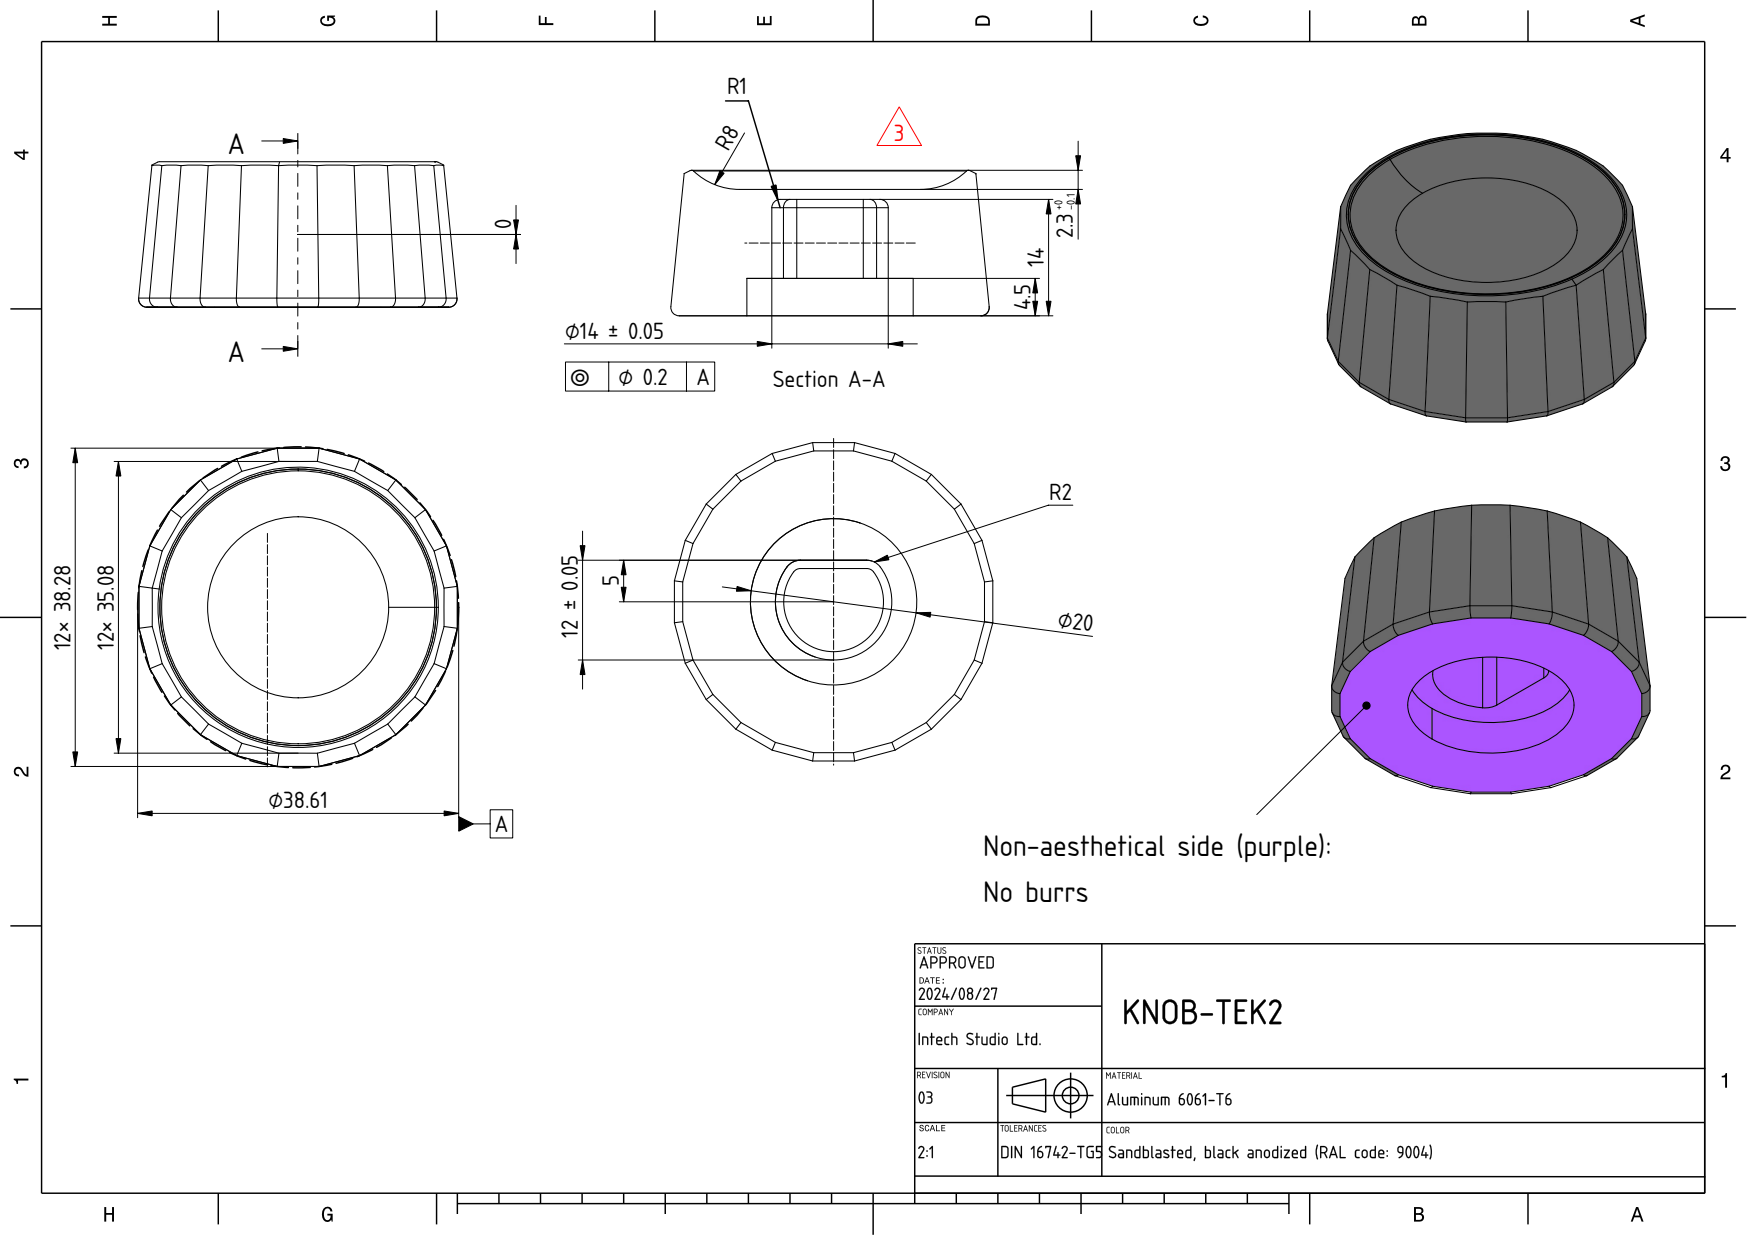
[picture p362: page 1]
Section A-A

Non-aesthetical side (purple):
No burrs
