intechstudio/grid/Preview/Mechanical/PBF4_Drawing.pdf

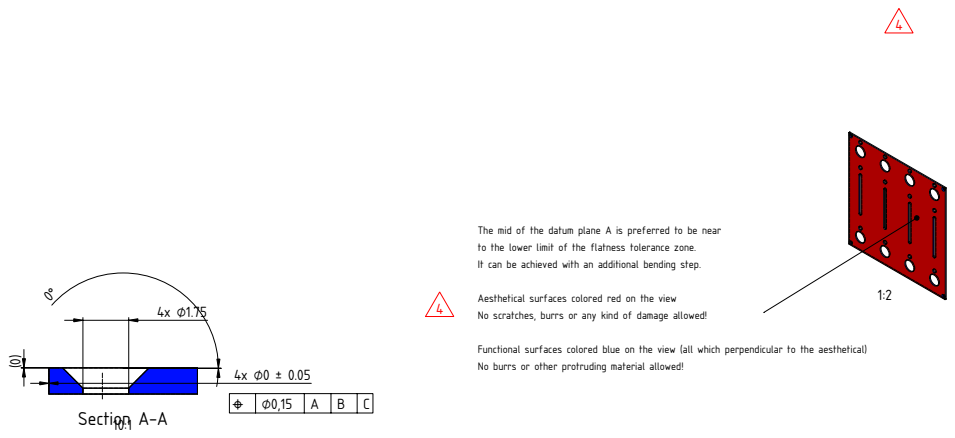
[picture p363: page 1]
Section A-A

The mid of the datum plane A is preferred to be near
to the lower limit of the flatness tolerance zone.
It can be achieved with an additional bending step.
No scratches, burrs or any kind of damage allowed!

Aesthetical surfaces colored red on the view

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
