intechstudio/grid/Preview/Mechanical/PBF4_dxf.pdf

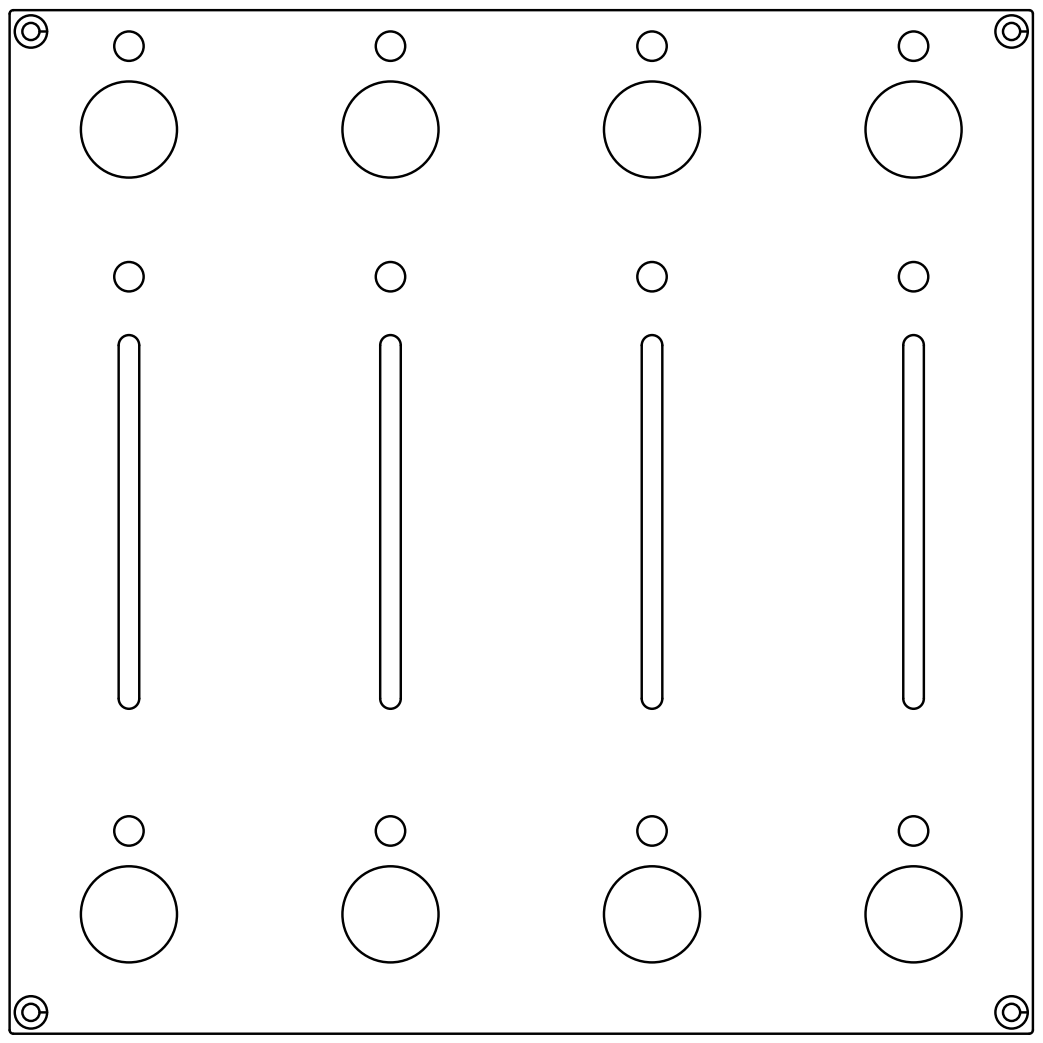
[picture p364: page 1]
