intechstudio/grid/Preview/Mechanical/PLASTIC-BUSHING-POT-TEK2_Drawing.pdf

AA

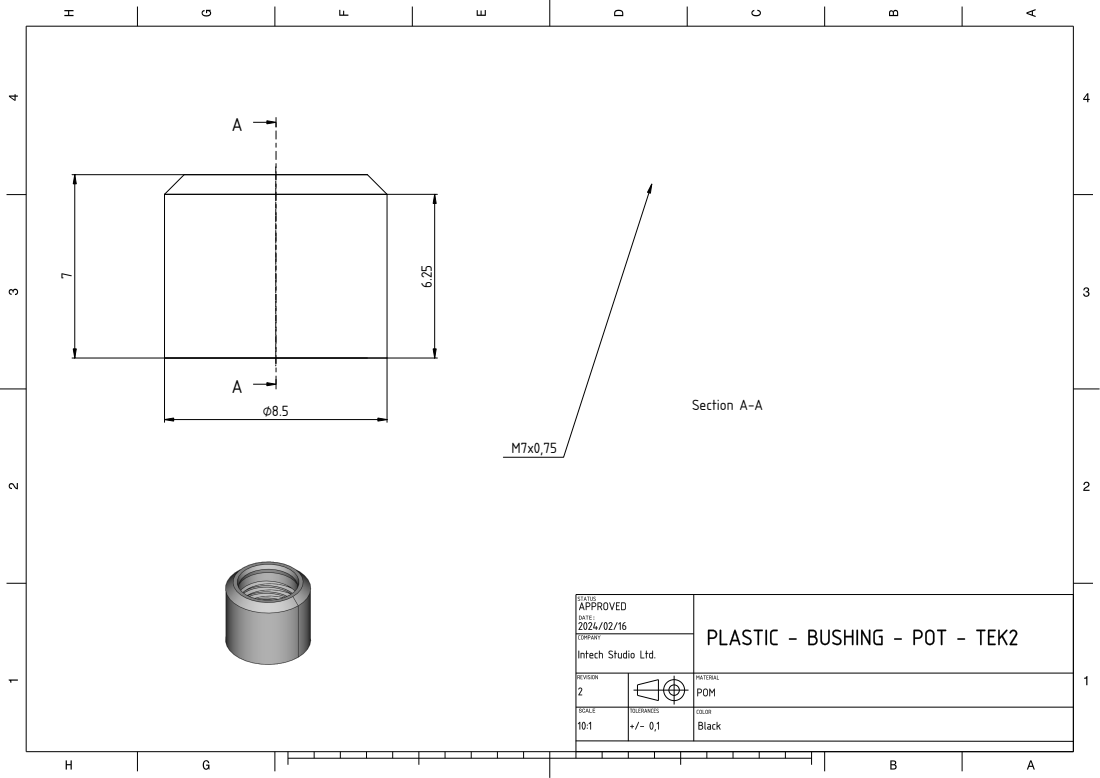
[picture p365: page 1]
ectio
