intechstudio/grid/Preview/Mechanical/PLASTIC-BUSHING-POT_Drawing.pdf

AA

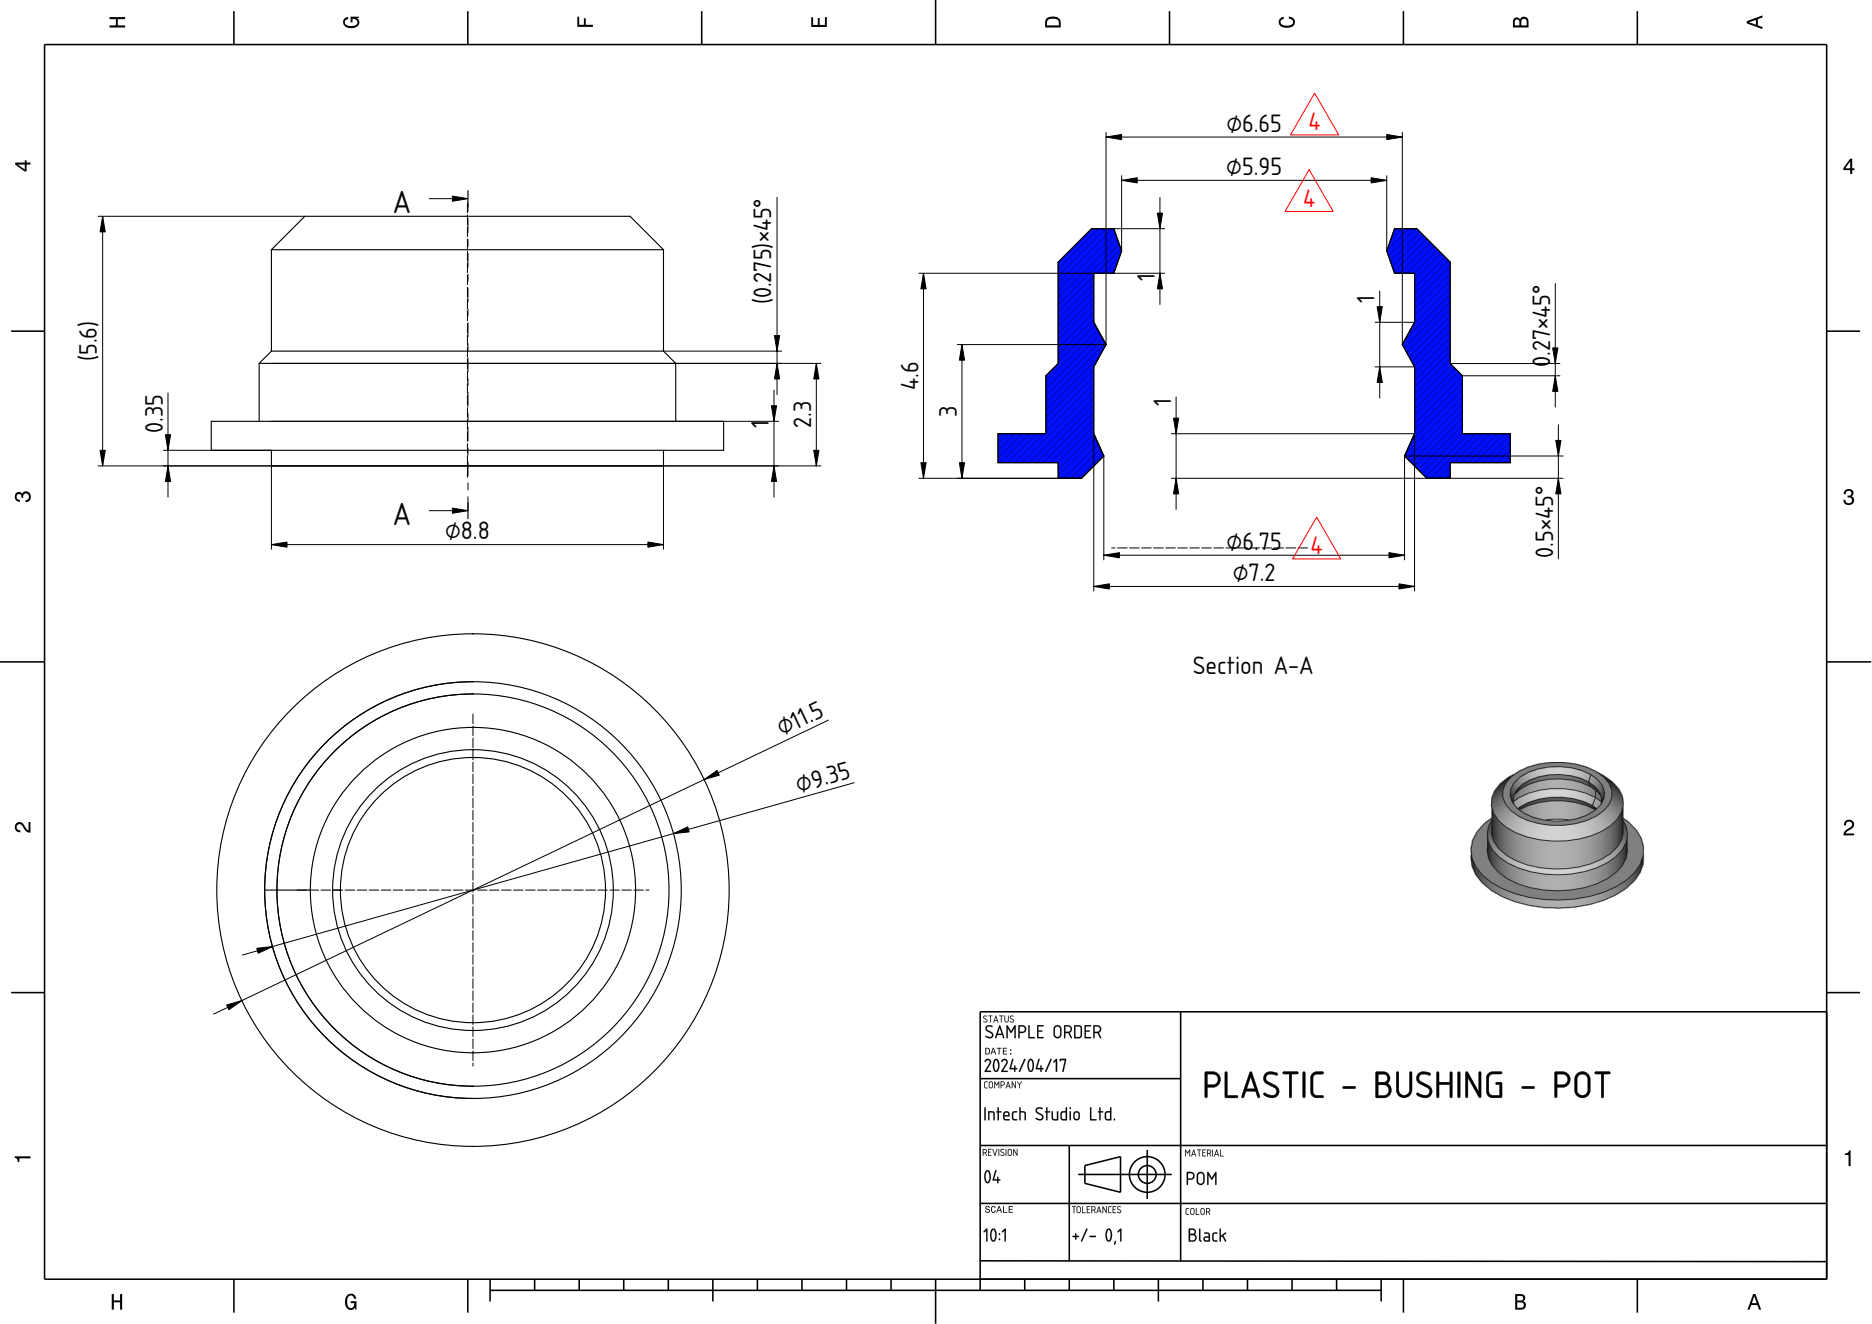
[picture p366: page 1]
ectio
