intechstudio/grid/Preview/Mechanical/PLASTIC-KNOB-ENC_Drawing.pdf

AA

⌀

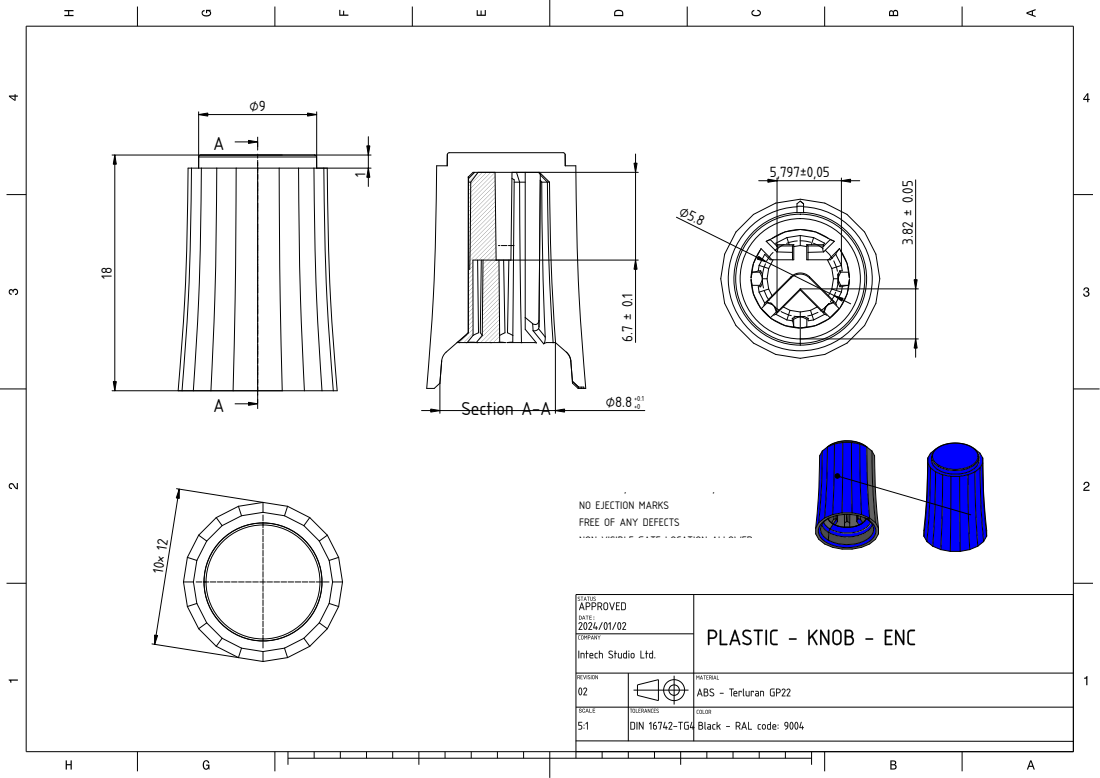
[picture p367: page 1]
ectio

NO EJECTION MARKS FREE OF ANY DEFECTS NON VISIBLE GATE LOCATION A
