intechstudio/grid/Preview/Mechanical/RUBBER-FOOT_Drawing.pdf

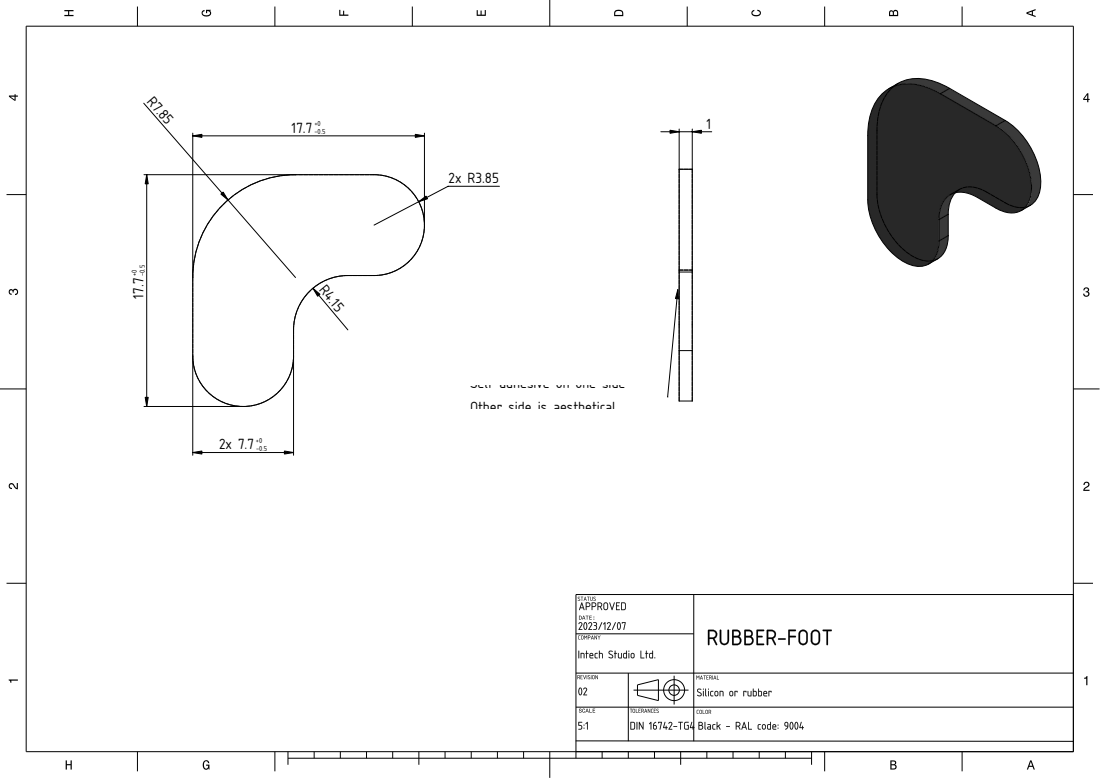
[picture p368: page 1]

Other side is aesthetical
