intechstudio/grid/Preview/Mechanical/TEK2_dxf.pdf

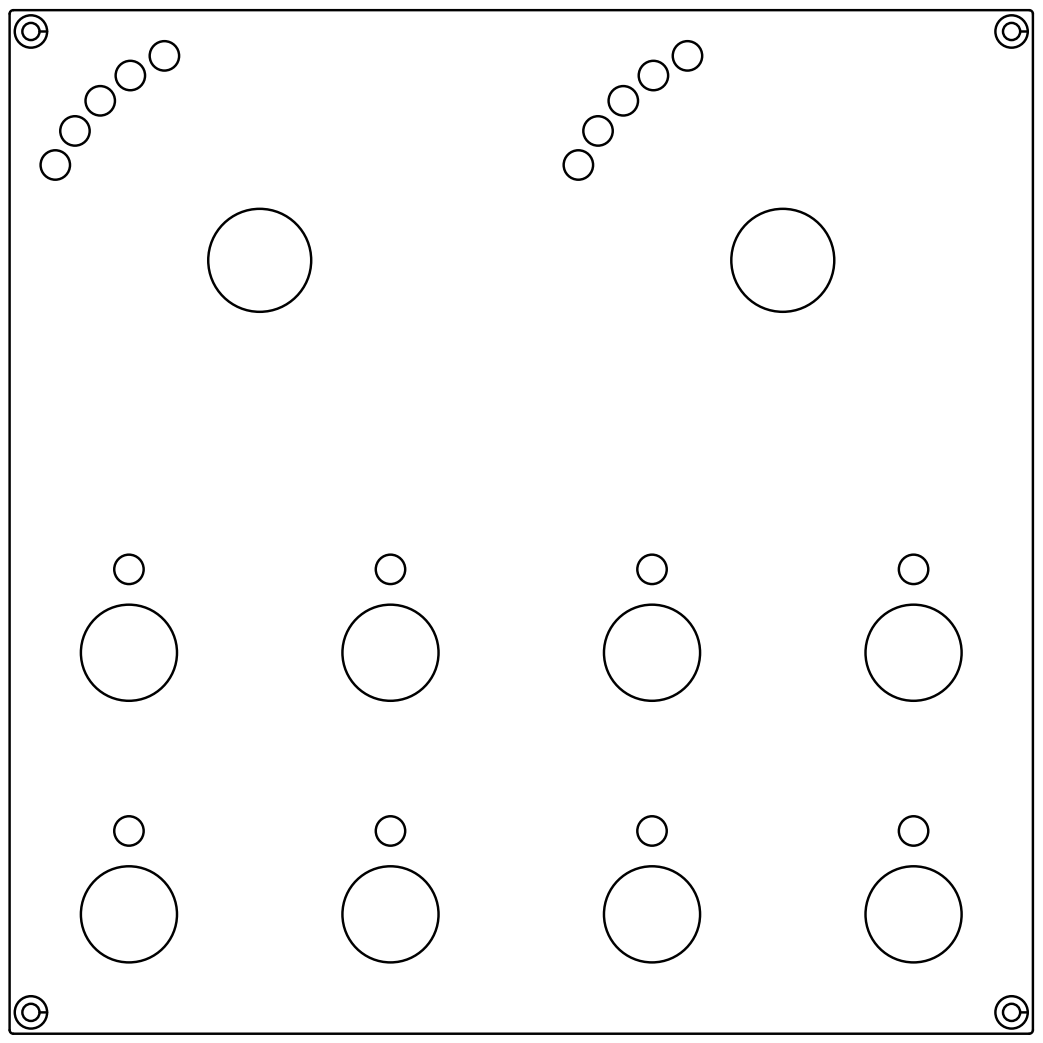
[picture p369: page 1]
