intechstudio/grid/Preview/Mechanical/VSN0_dxf.pdf

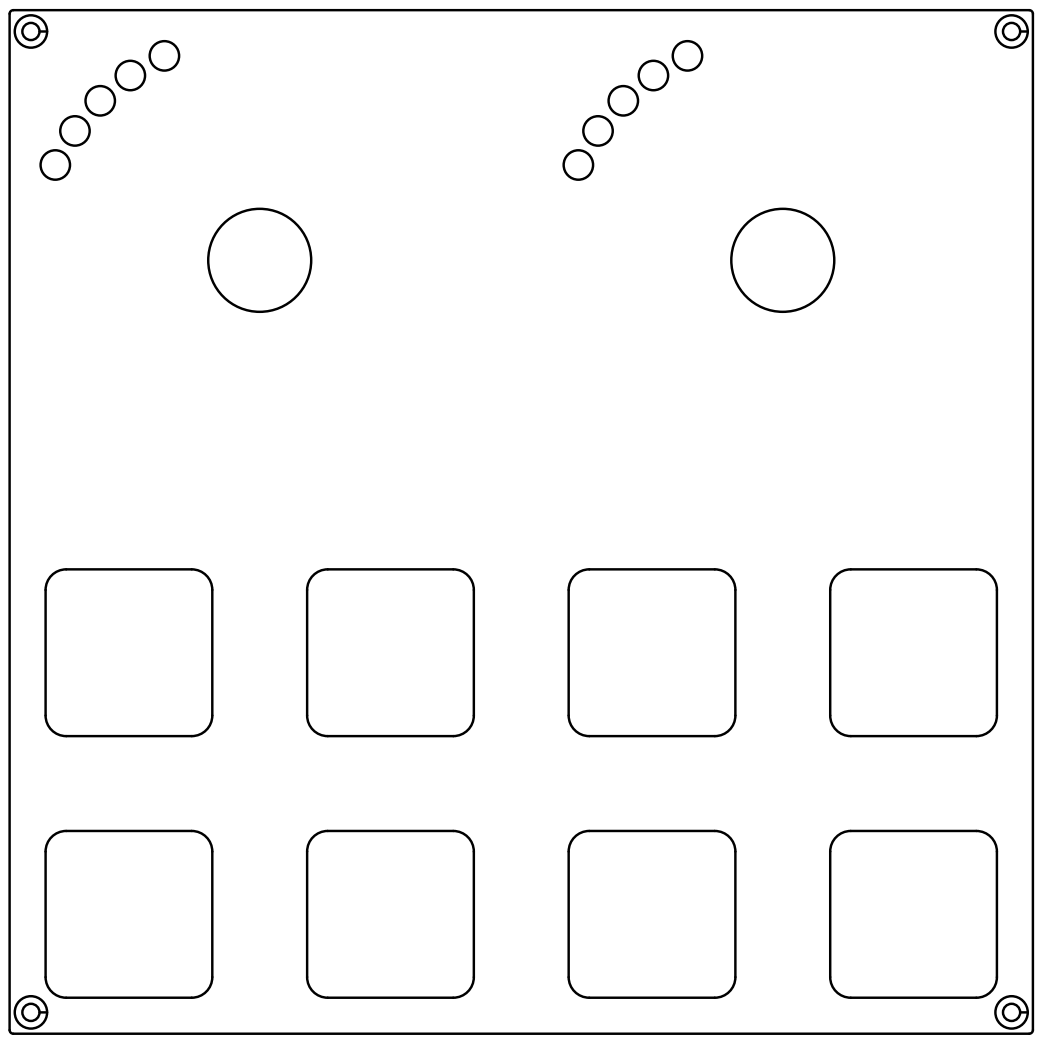
[picture p370: page 1]
