intechstudio/grid/Preview/Mechanical/VSN1-R_dxf.pdf

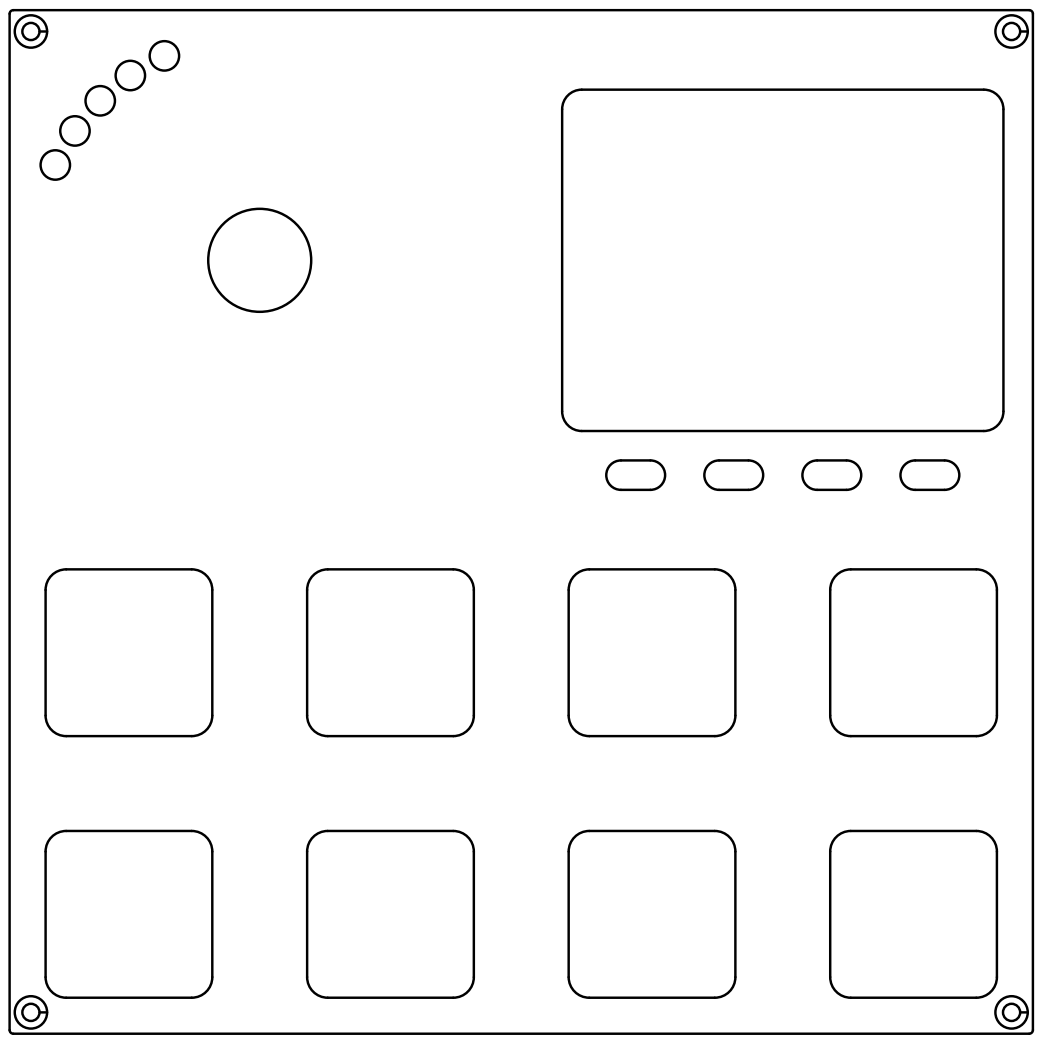
[picture p371: page 1]
