intechstudio/grid/Preview/Mechanical/VSN1_dxf.pdf

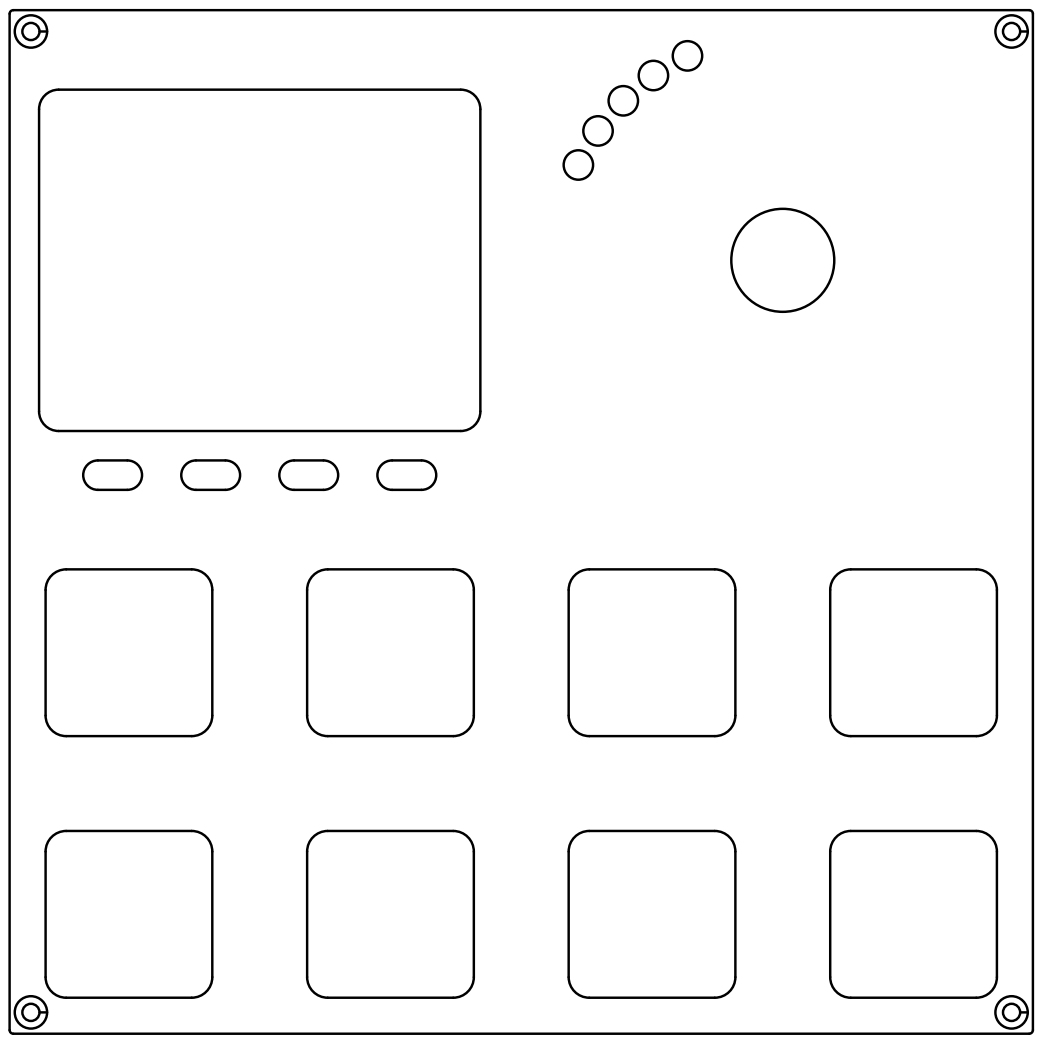
[picture p372: page 1]
