intechstudio/grid/Preview/Electrical/PCBA-VSNX-BTNGROUP_Schematic.pdf

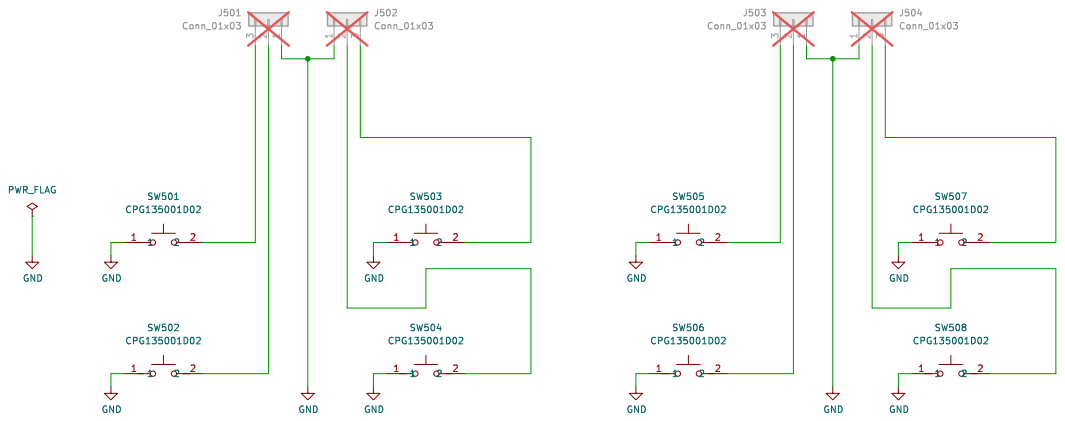
[picture p373: page 1]
