intechstudio/grid/Preview/Electrical/PCBA-BU16-FRONTPANEL_Schematic.pdf

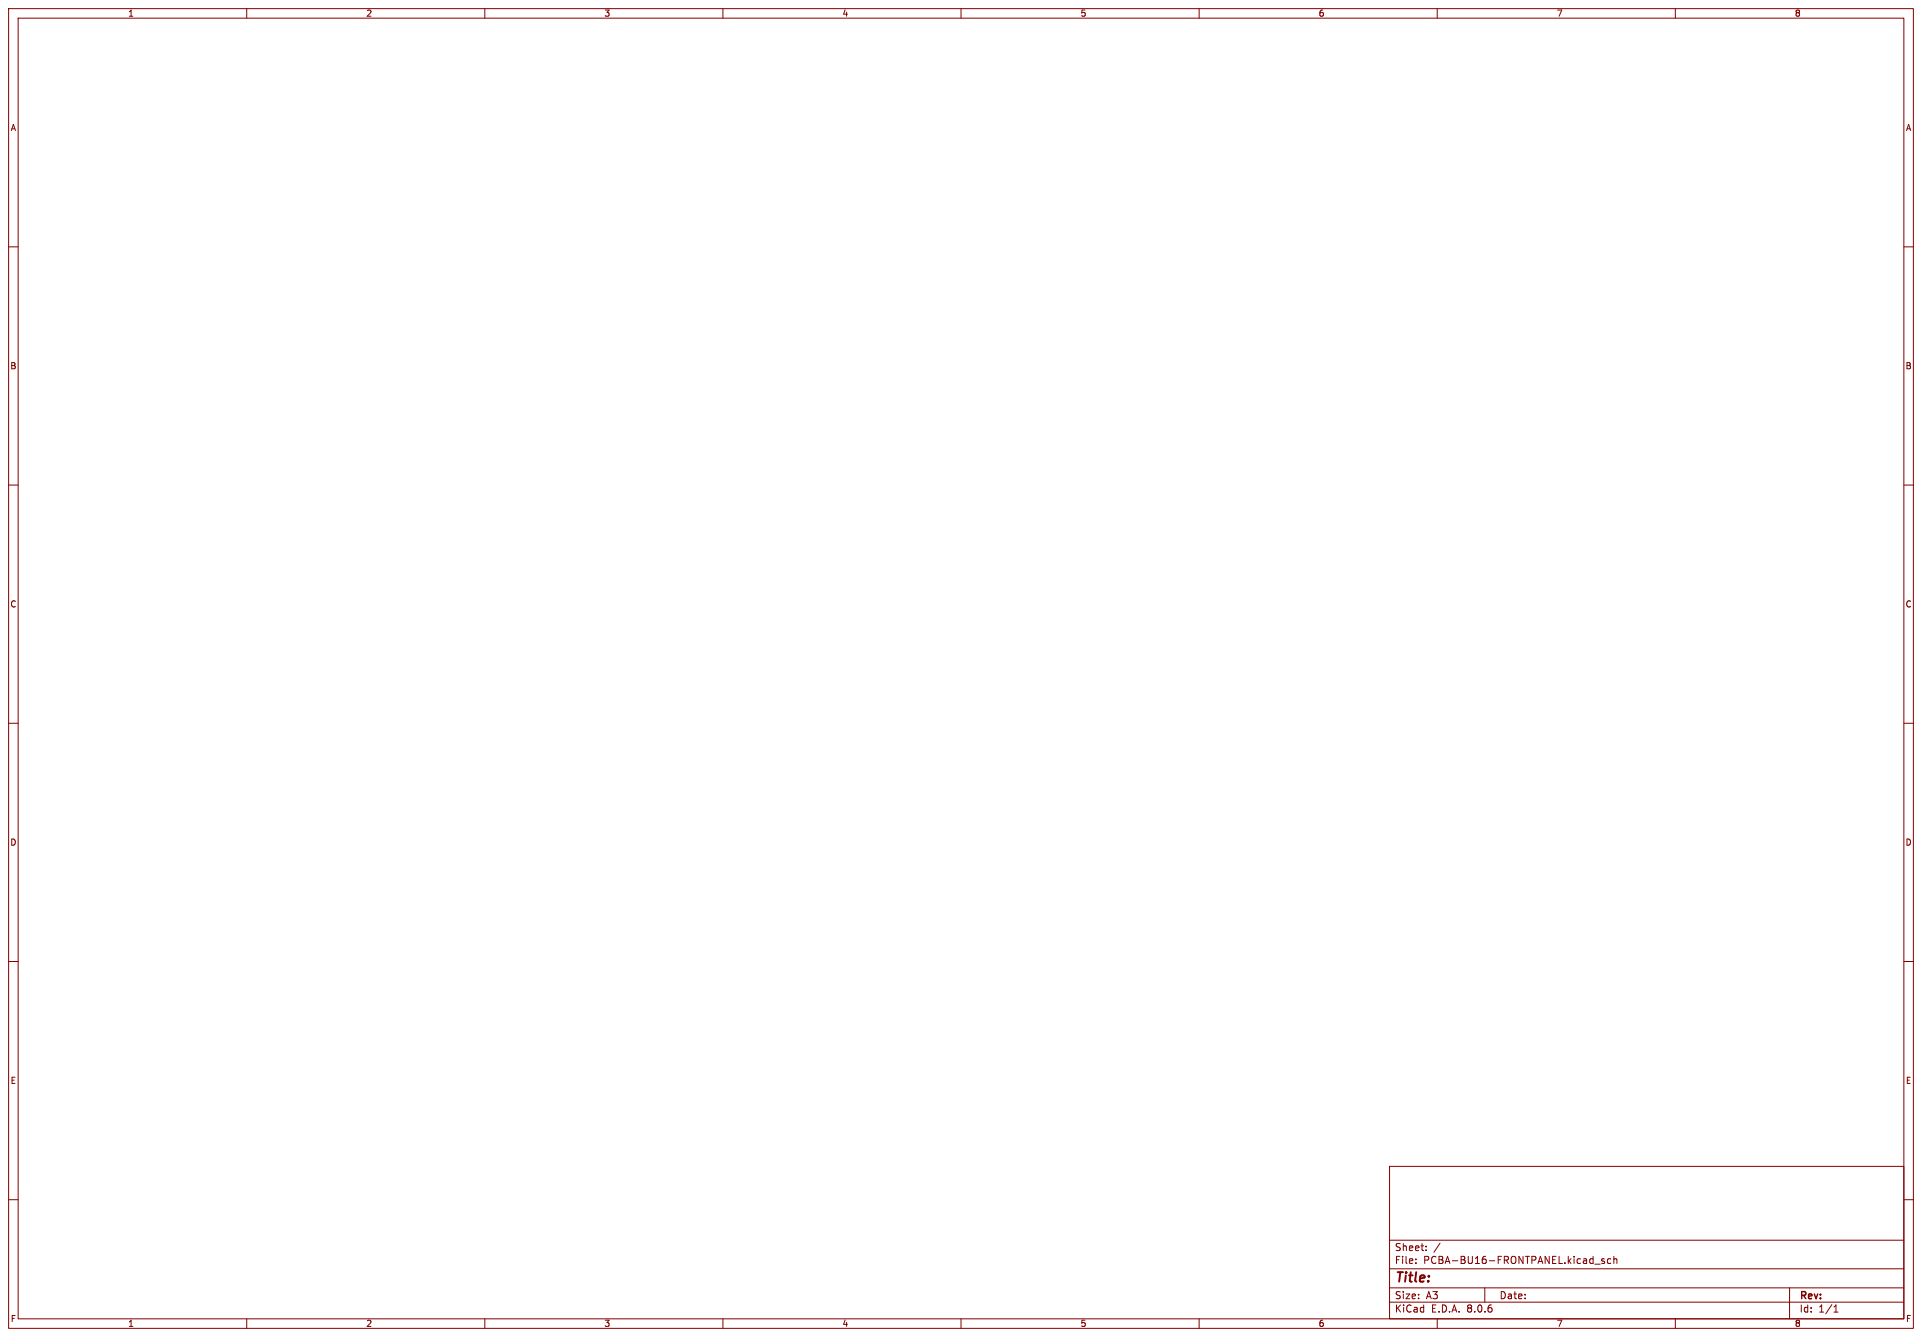
[picture p374: page 1]
