intechstudio/grid/Preview/Electrical/PCBA-EF44-FRONTPANEL_Schematic.pdf

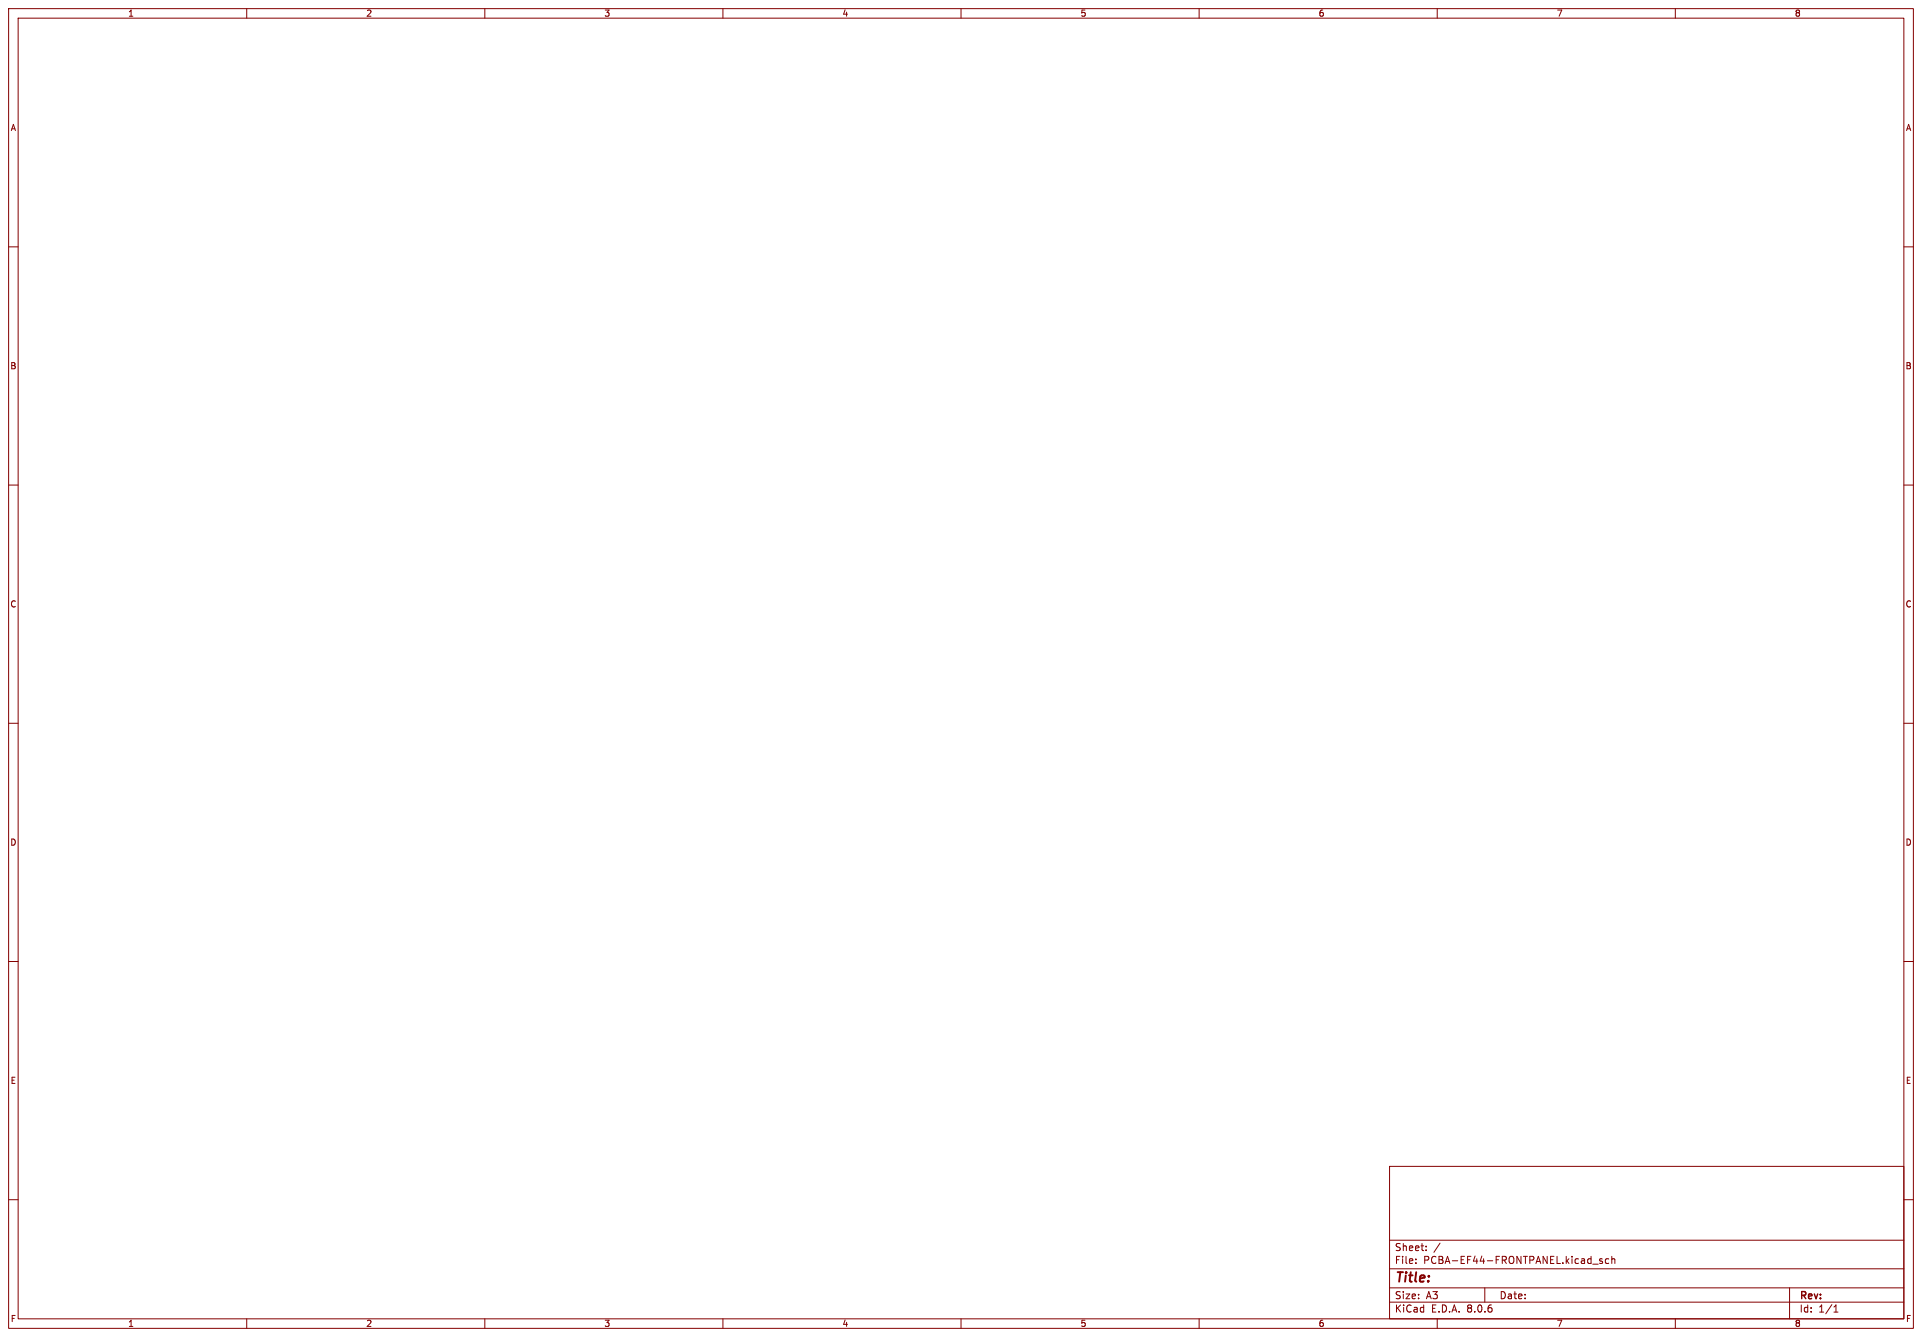
[picture p375: page 1]
