intechstudio/grid/Preview/Electrical/PCBA-PBF4-FRONTPANEL_Schematic.pdf

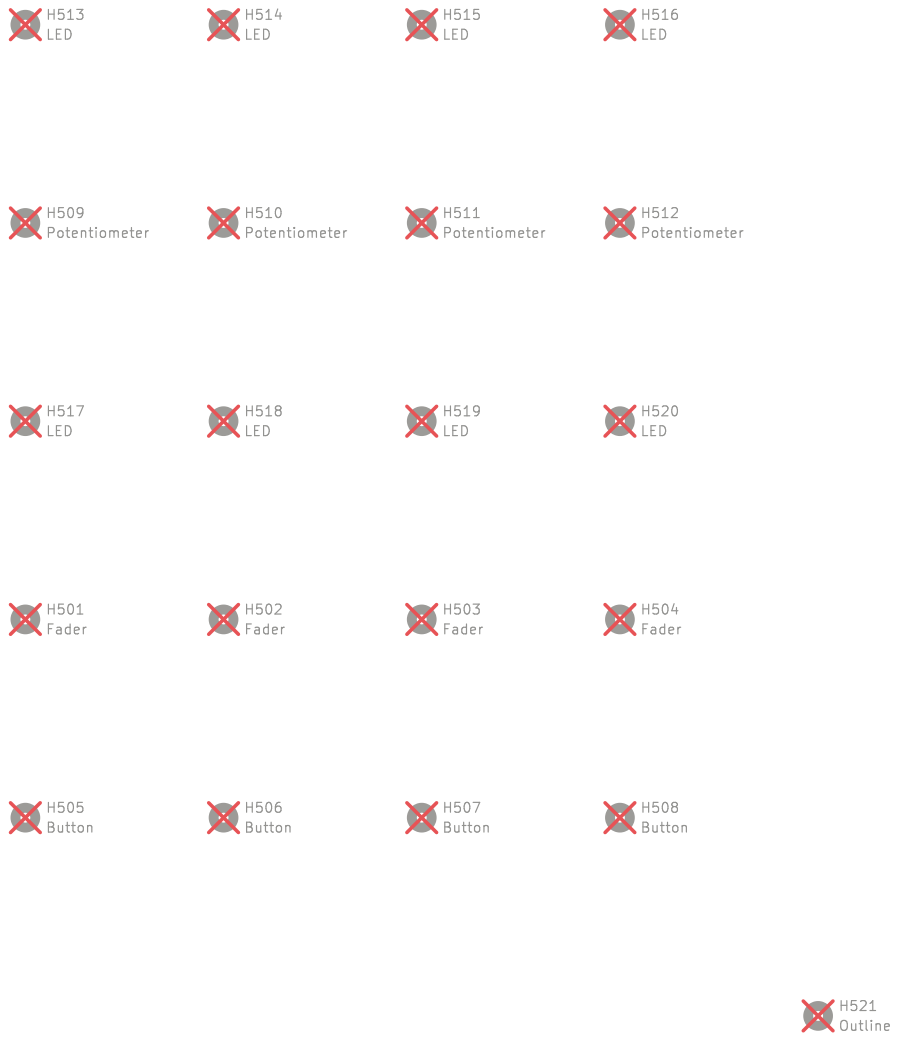
[picture p376: page 1]
