intechstudio/grid/Preview/Electrical/PCBA-VSN0-FRONTPANEL_Schematic.pdf

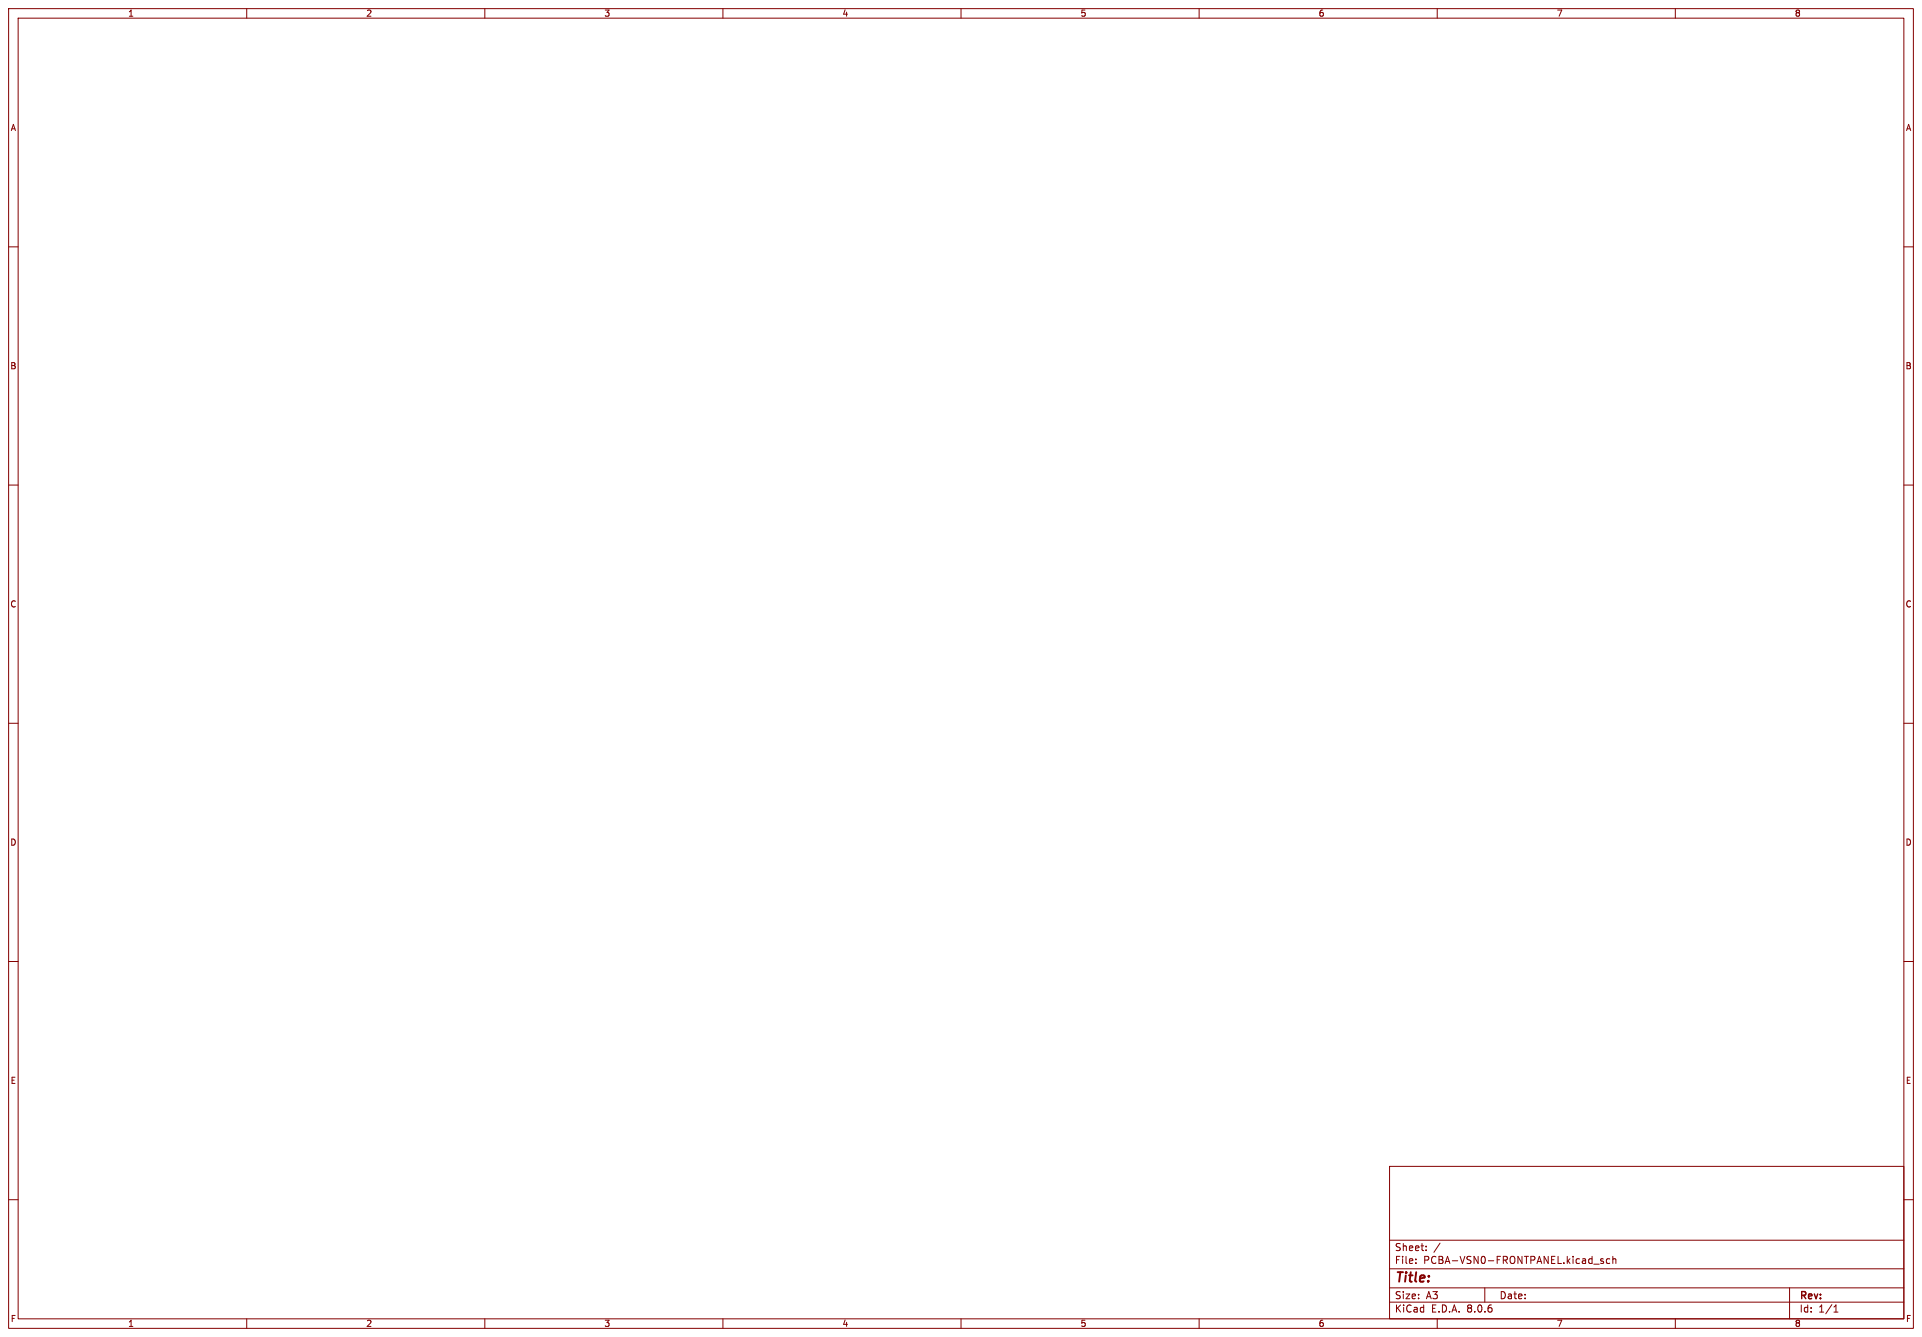
[picture p377: page 1]
