intechstudio/grid/Preview/Electrical/PCBA-VSN1-FRONTPANEL_Schematic.pdf

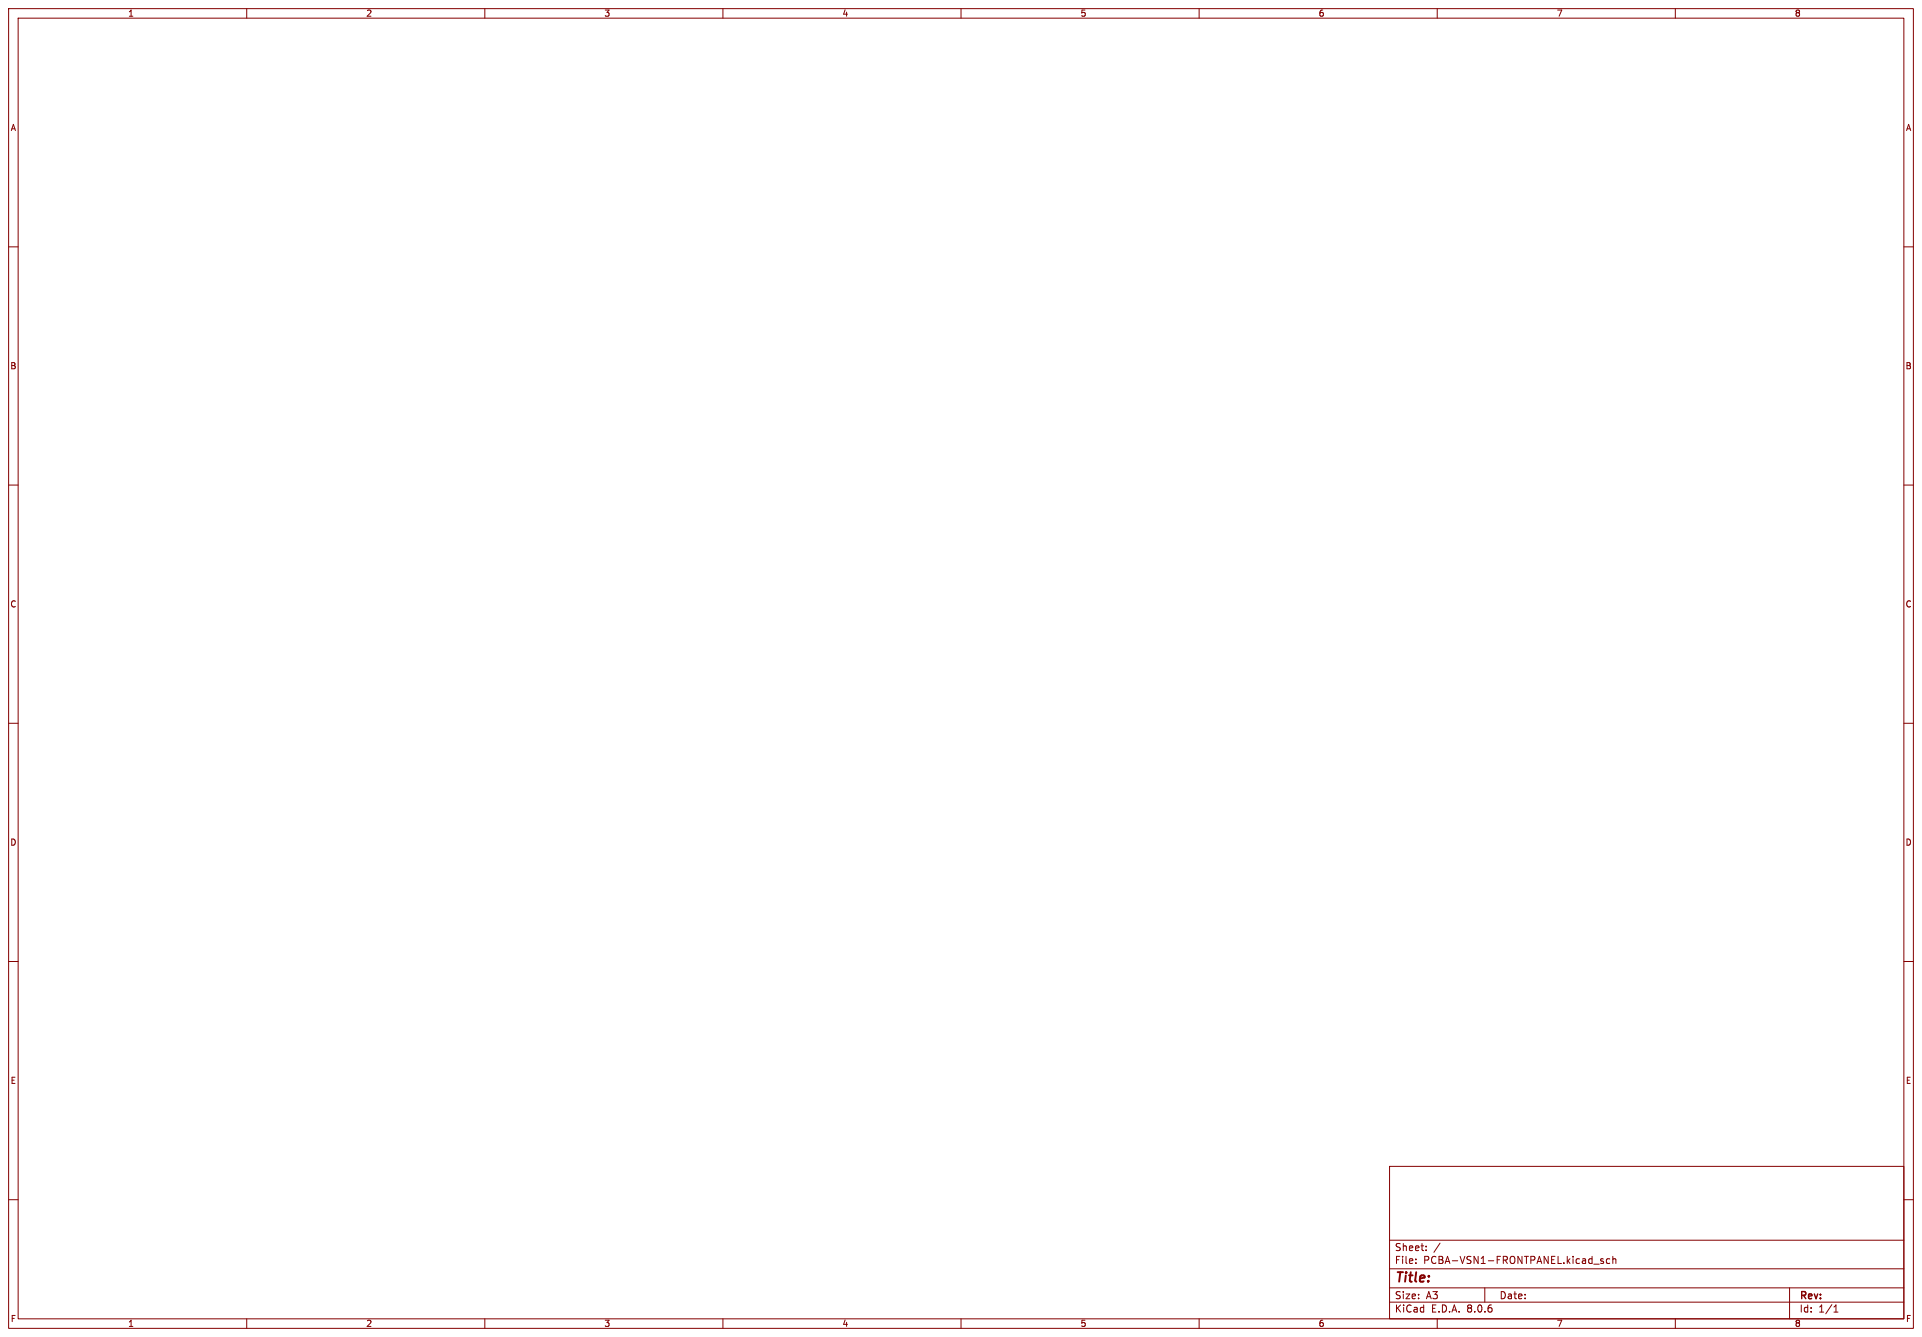
[picture p378: page 1]
