intechstudio/grid/Preview/Electrical/PCBA-VSN1R-FRONTPANEL_Schematic.pdf

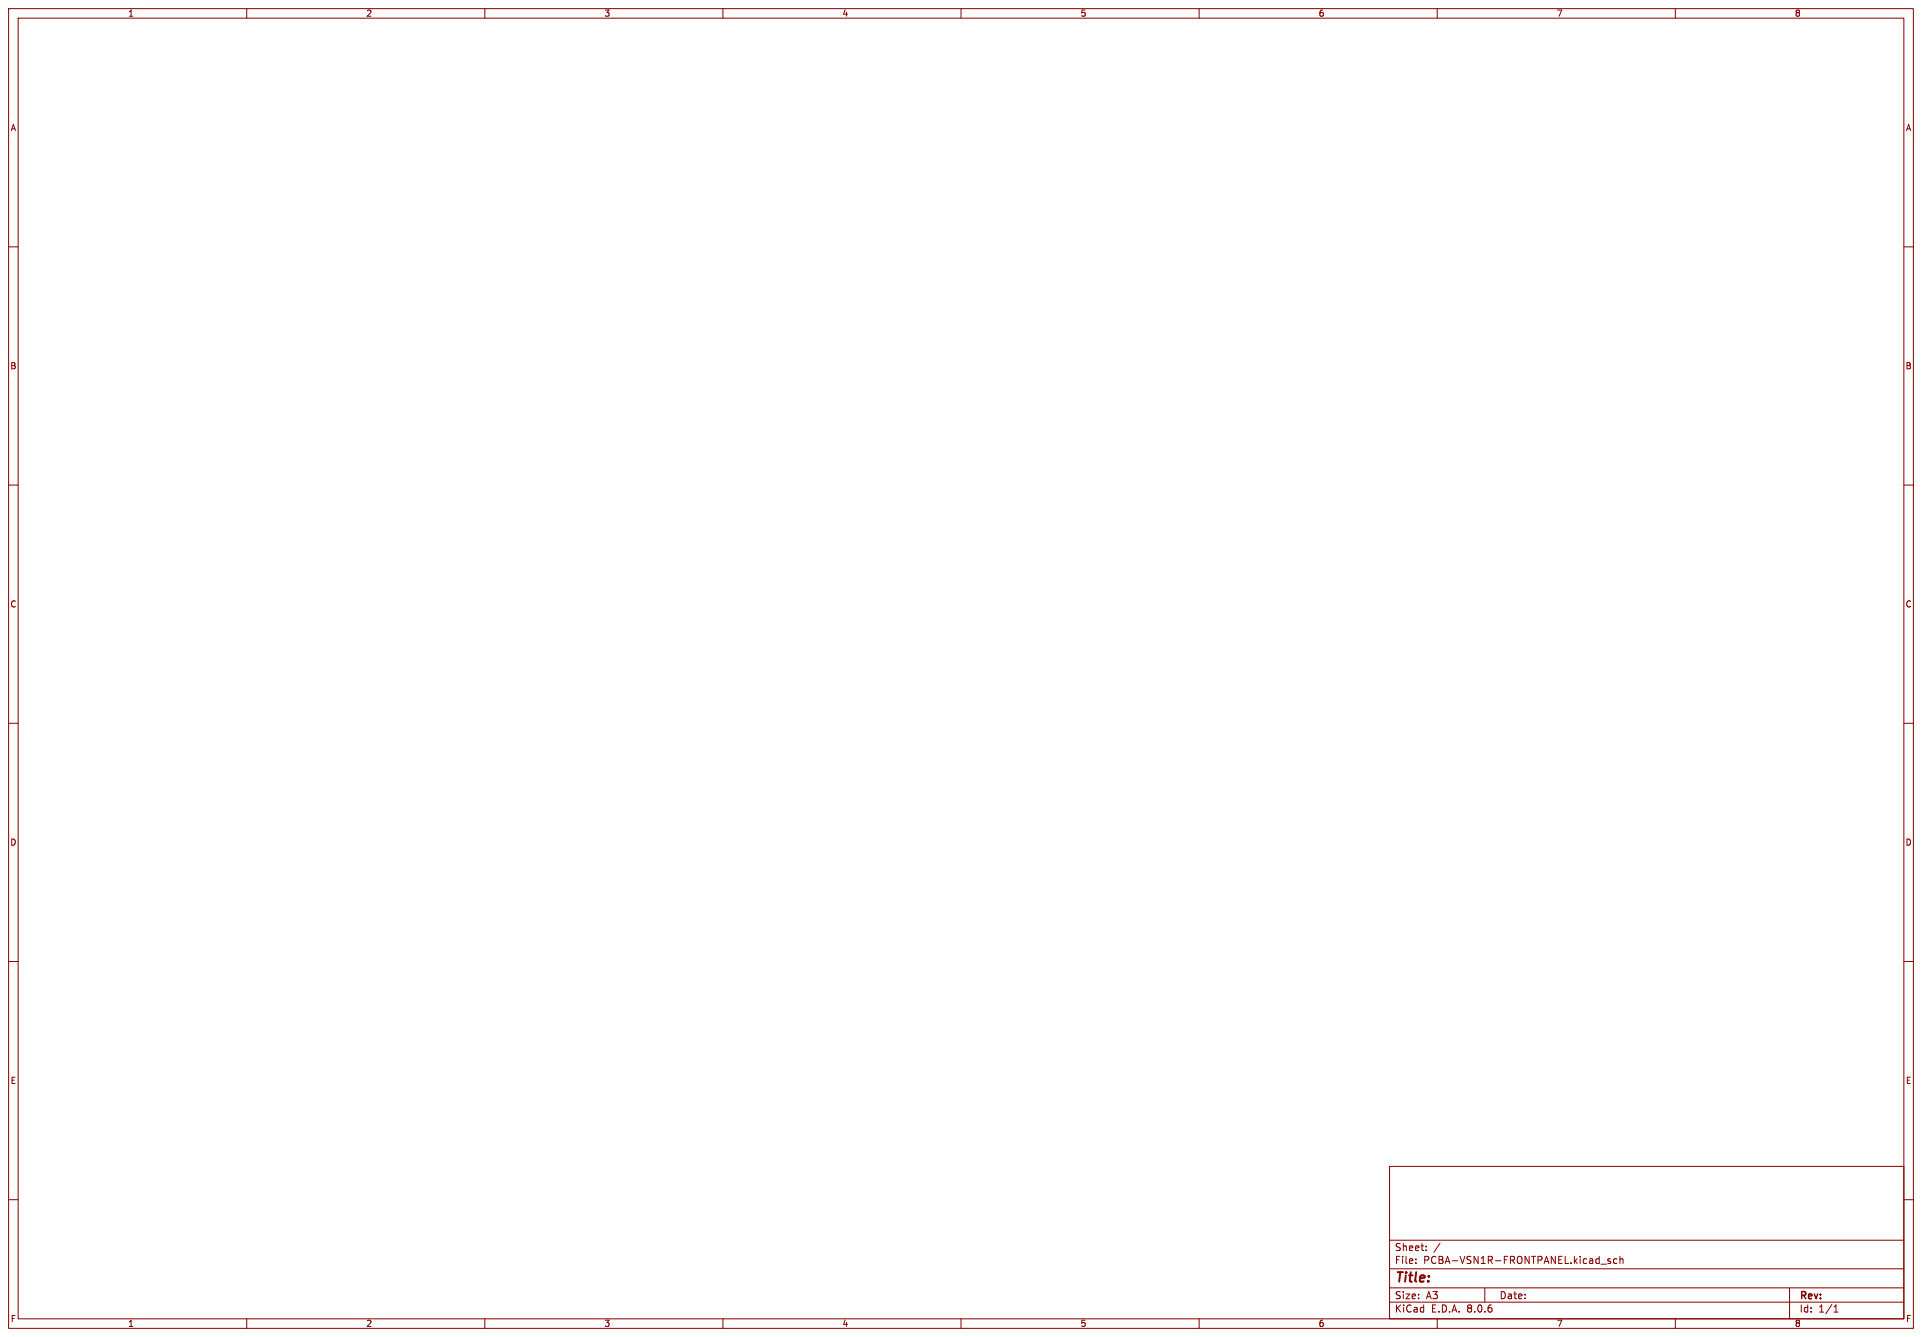
[picture p379: page 1]
