intechstudio/grid/Preview/Electrical/PCBA-VSN2-FRONTPANEL_Schematic.pdf

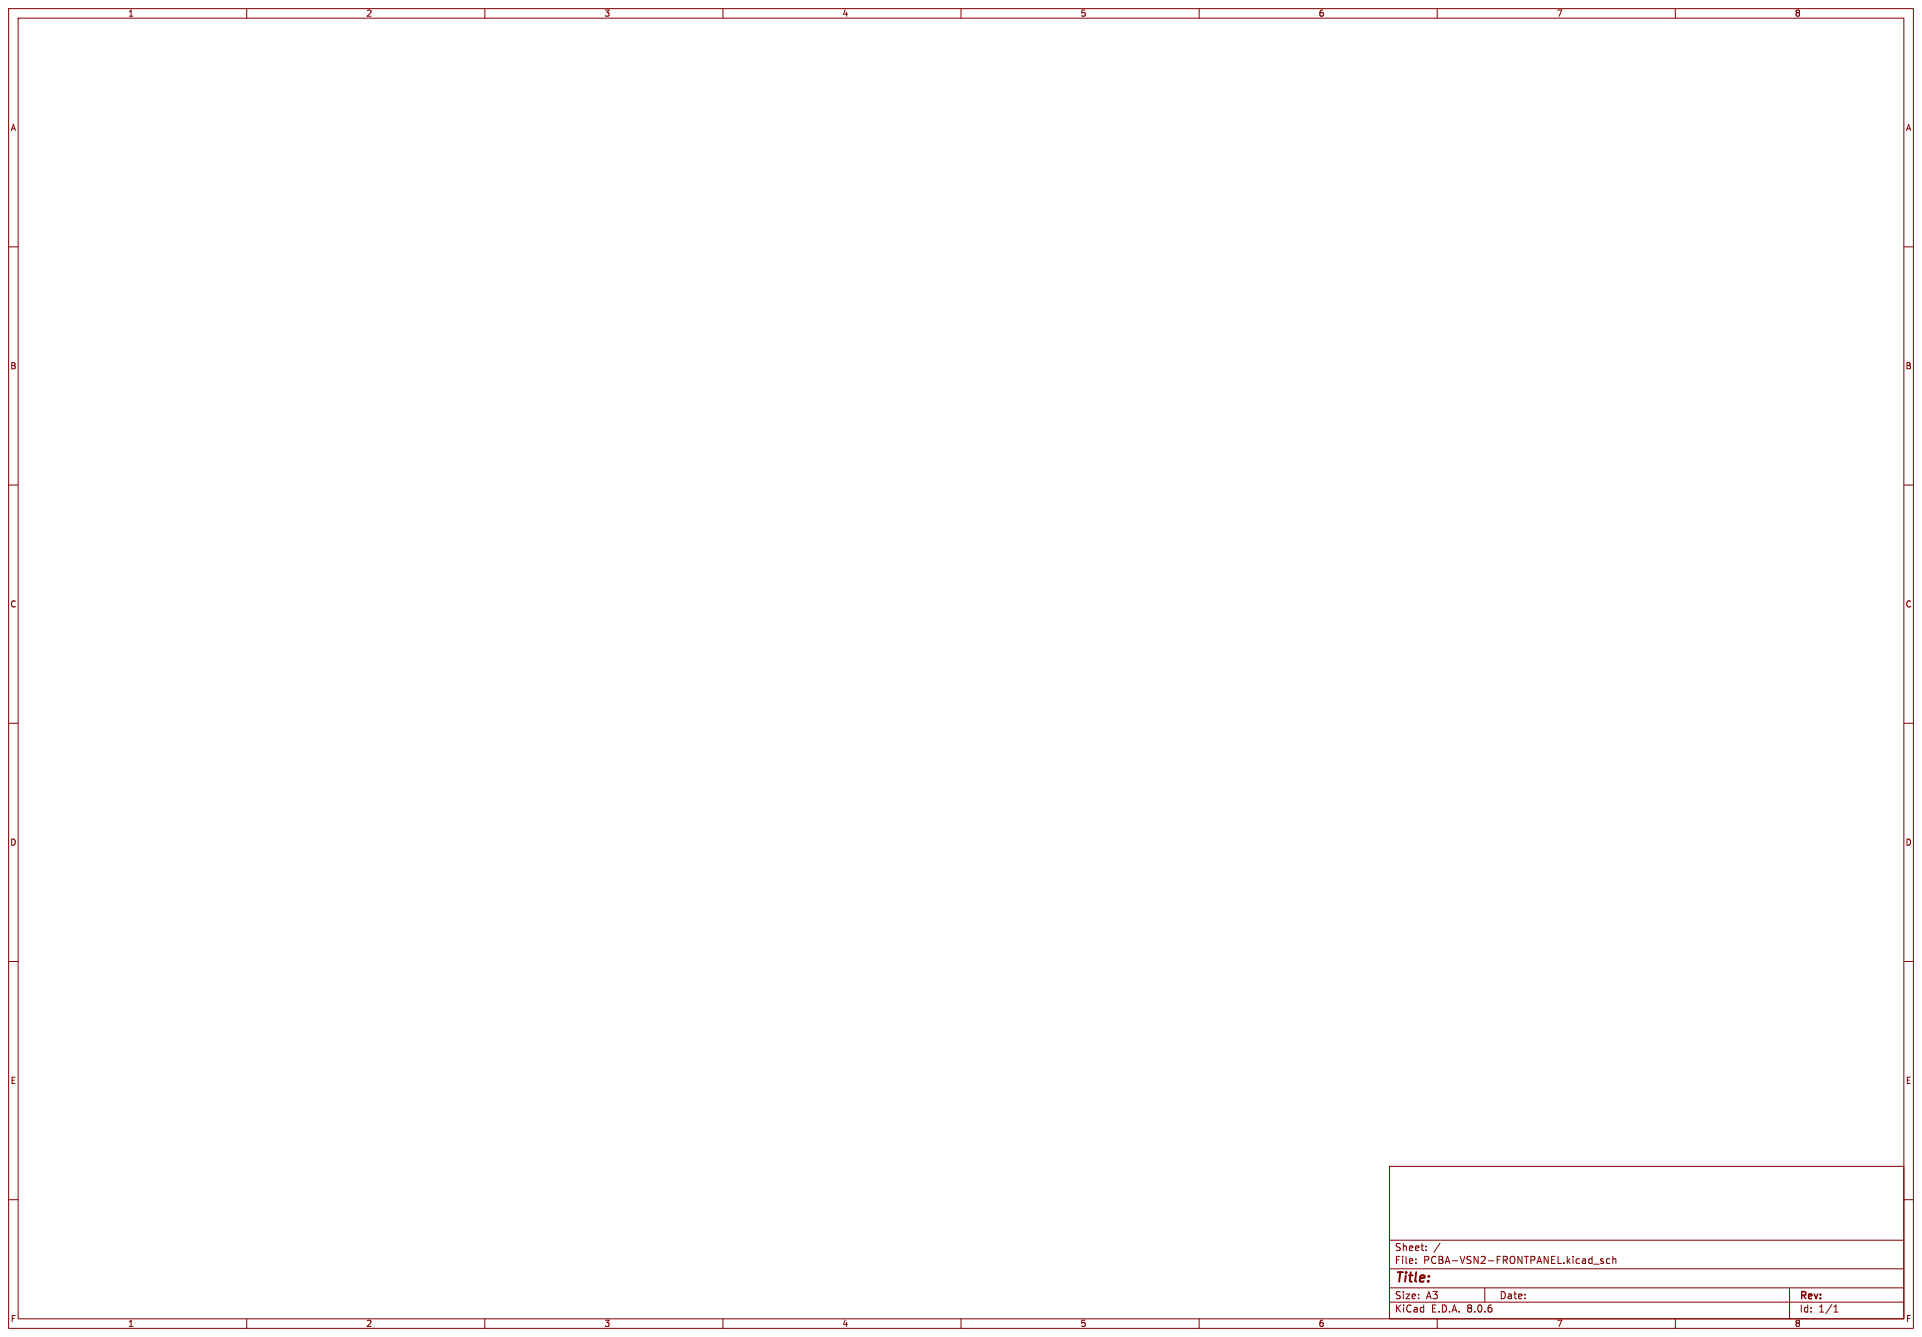
[picture p380: page 1]
