intechstudio/grid/Preview/Electrical/PCBA-XX16-FRONTPANEL_Schematic.pdf

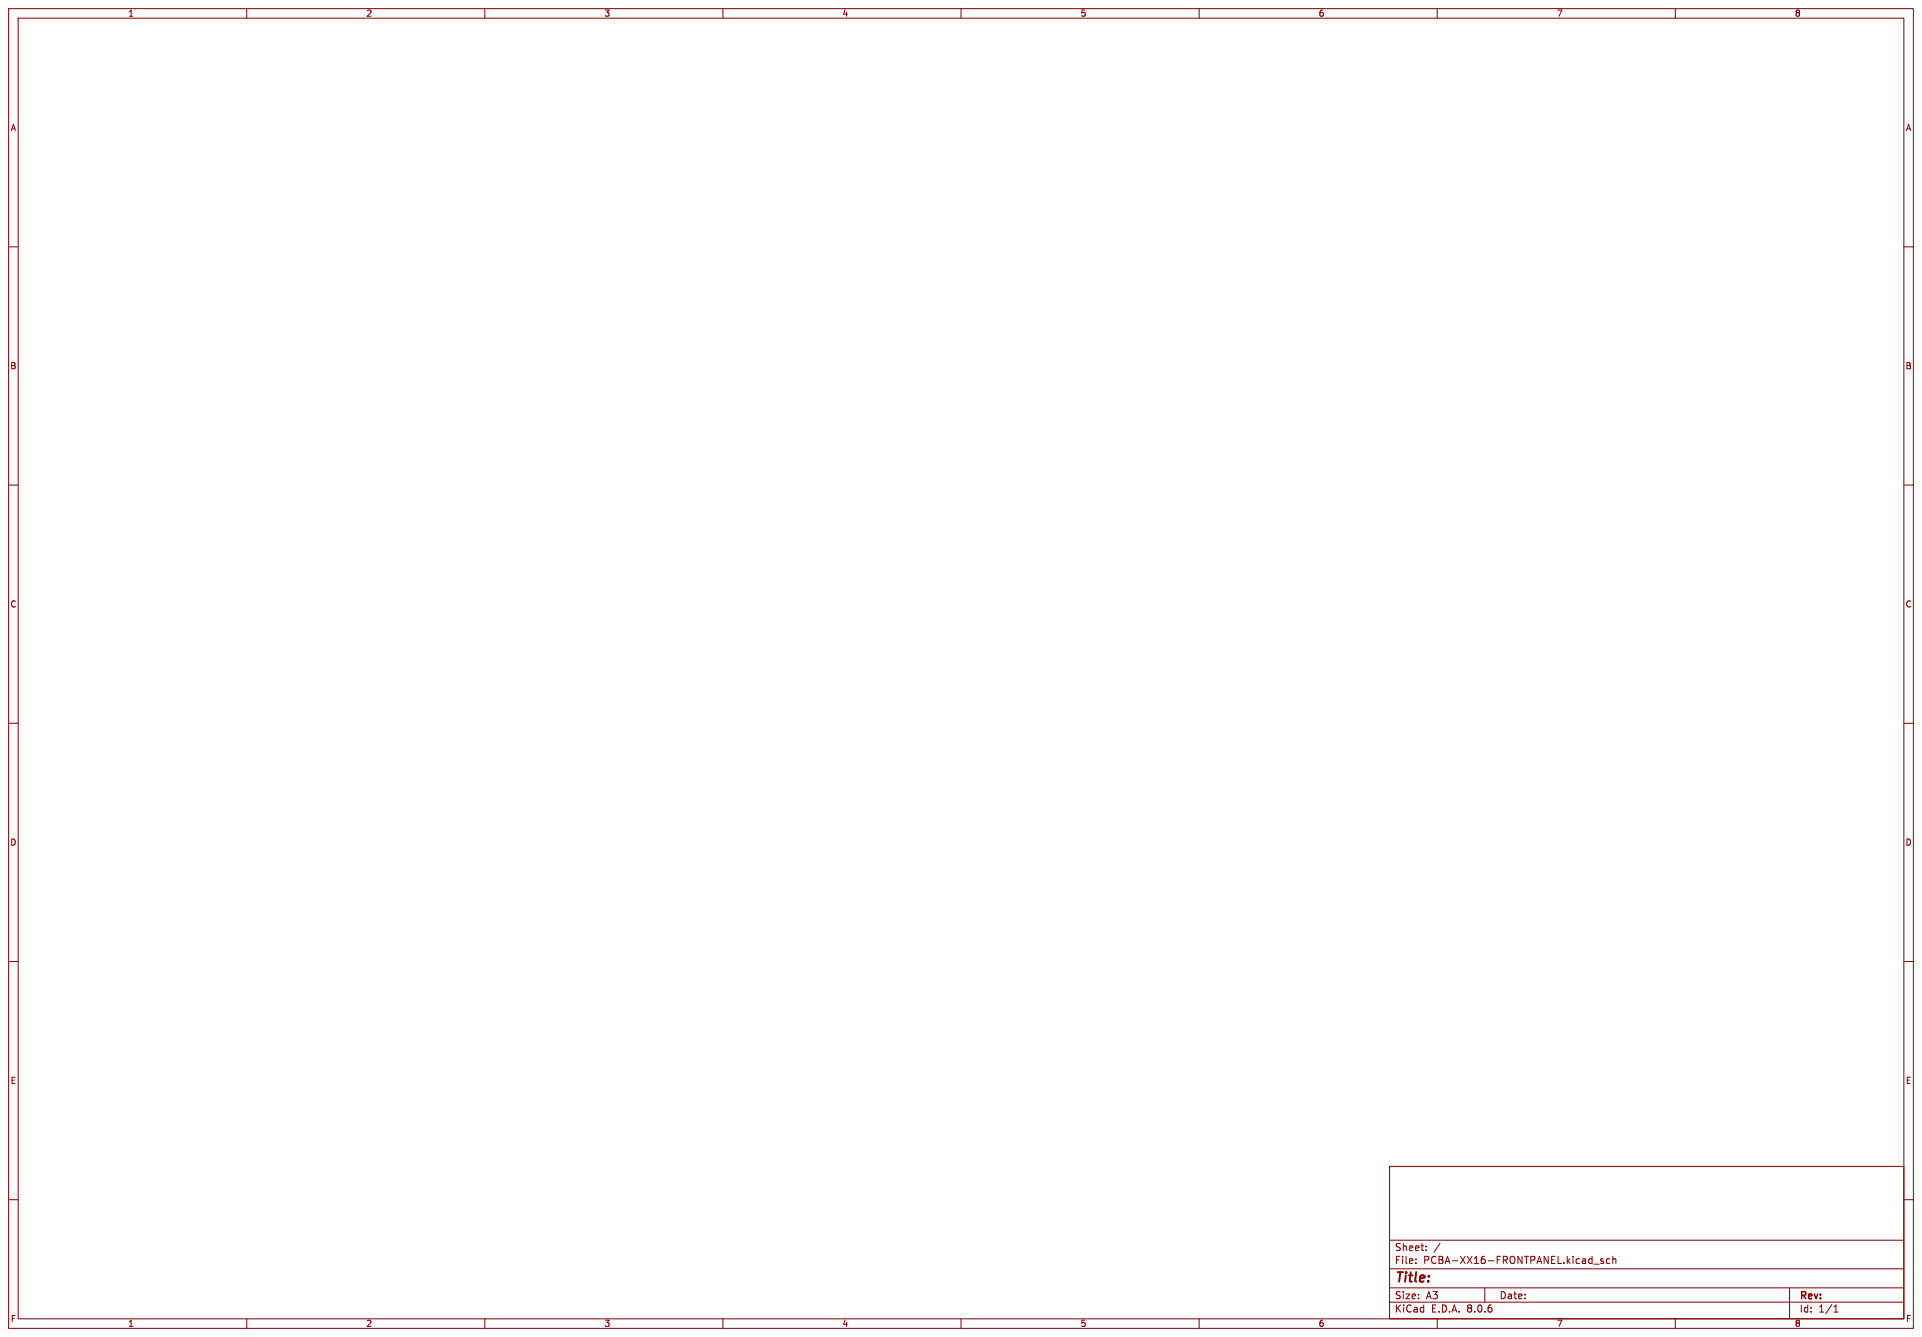
[picture p381: page 1]
