intechstudio/grid/Preview/Electrical/PCBA-TEK1-BTNGROUP_Schematic.pdf

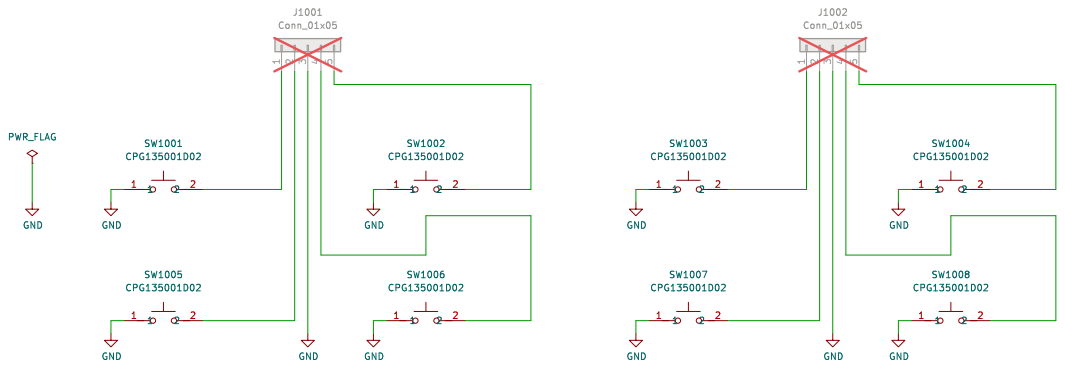
[picture p382: page 1]
