intechstudio/grid/Preview/Mechanical/FRONTPANEL-VSN1-R_dxf.pdf

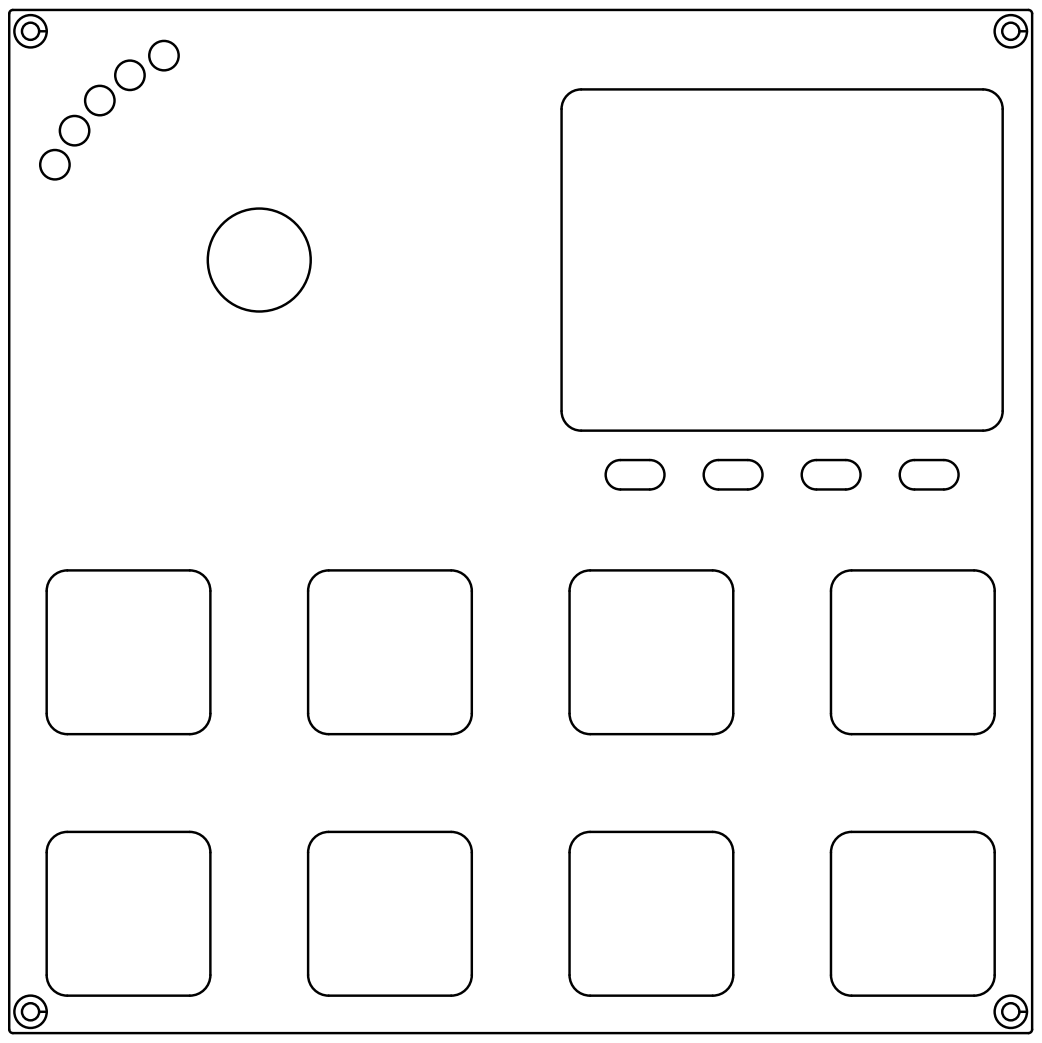
[picture p383: page 1]
