intechstudio/grid/Preview/Mechanical/FRONTPANEL-VSN1_dxf.pdf

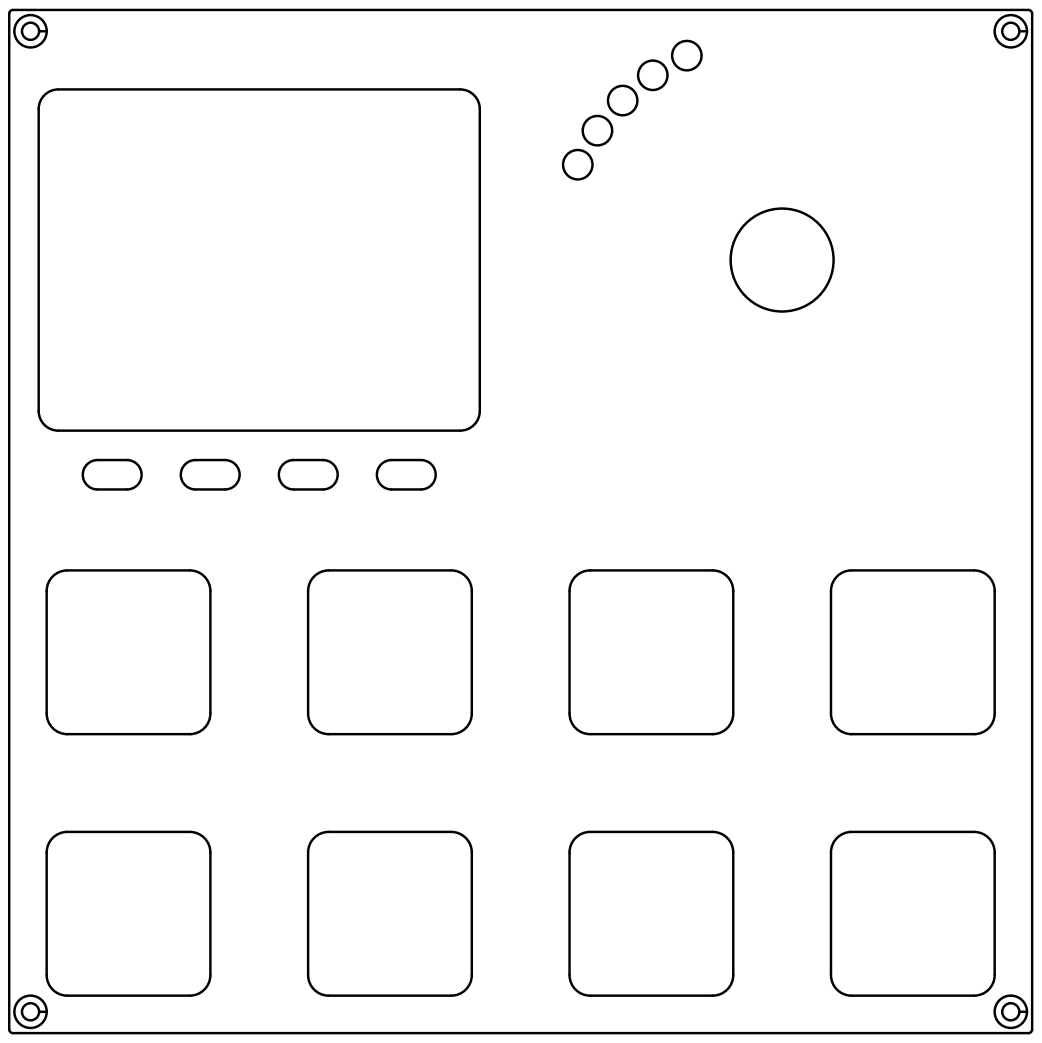
[picture p384: page 1]
