intechstudio/grid/Preview/Mechanical/KNOB_TEK2_Drawing.pdf

A

R1

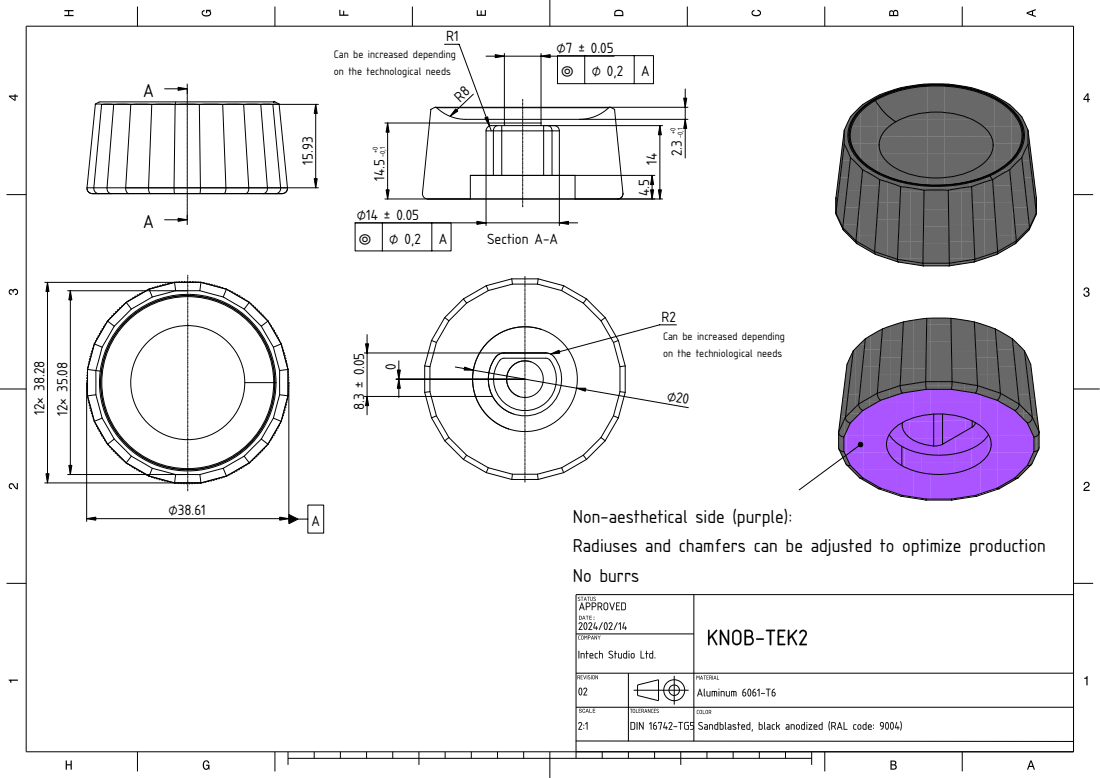
[picture p385: page 1]
Section A-A

Can be increased depending
on the technological needs

on the techniological needs

Non-aesthetical side (purple):
Radiuses and chamfers can be adjusted to optimize production
No burrs
