intechstudio/grid/Preview/Electrical/FP-BU16-MIDIGRADE_PCB_Bottom.pdf

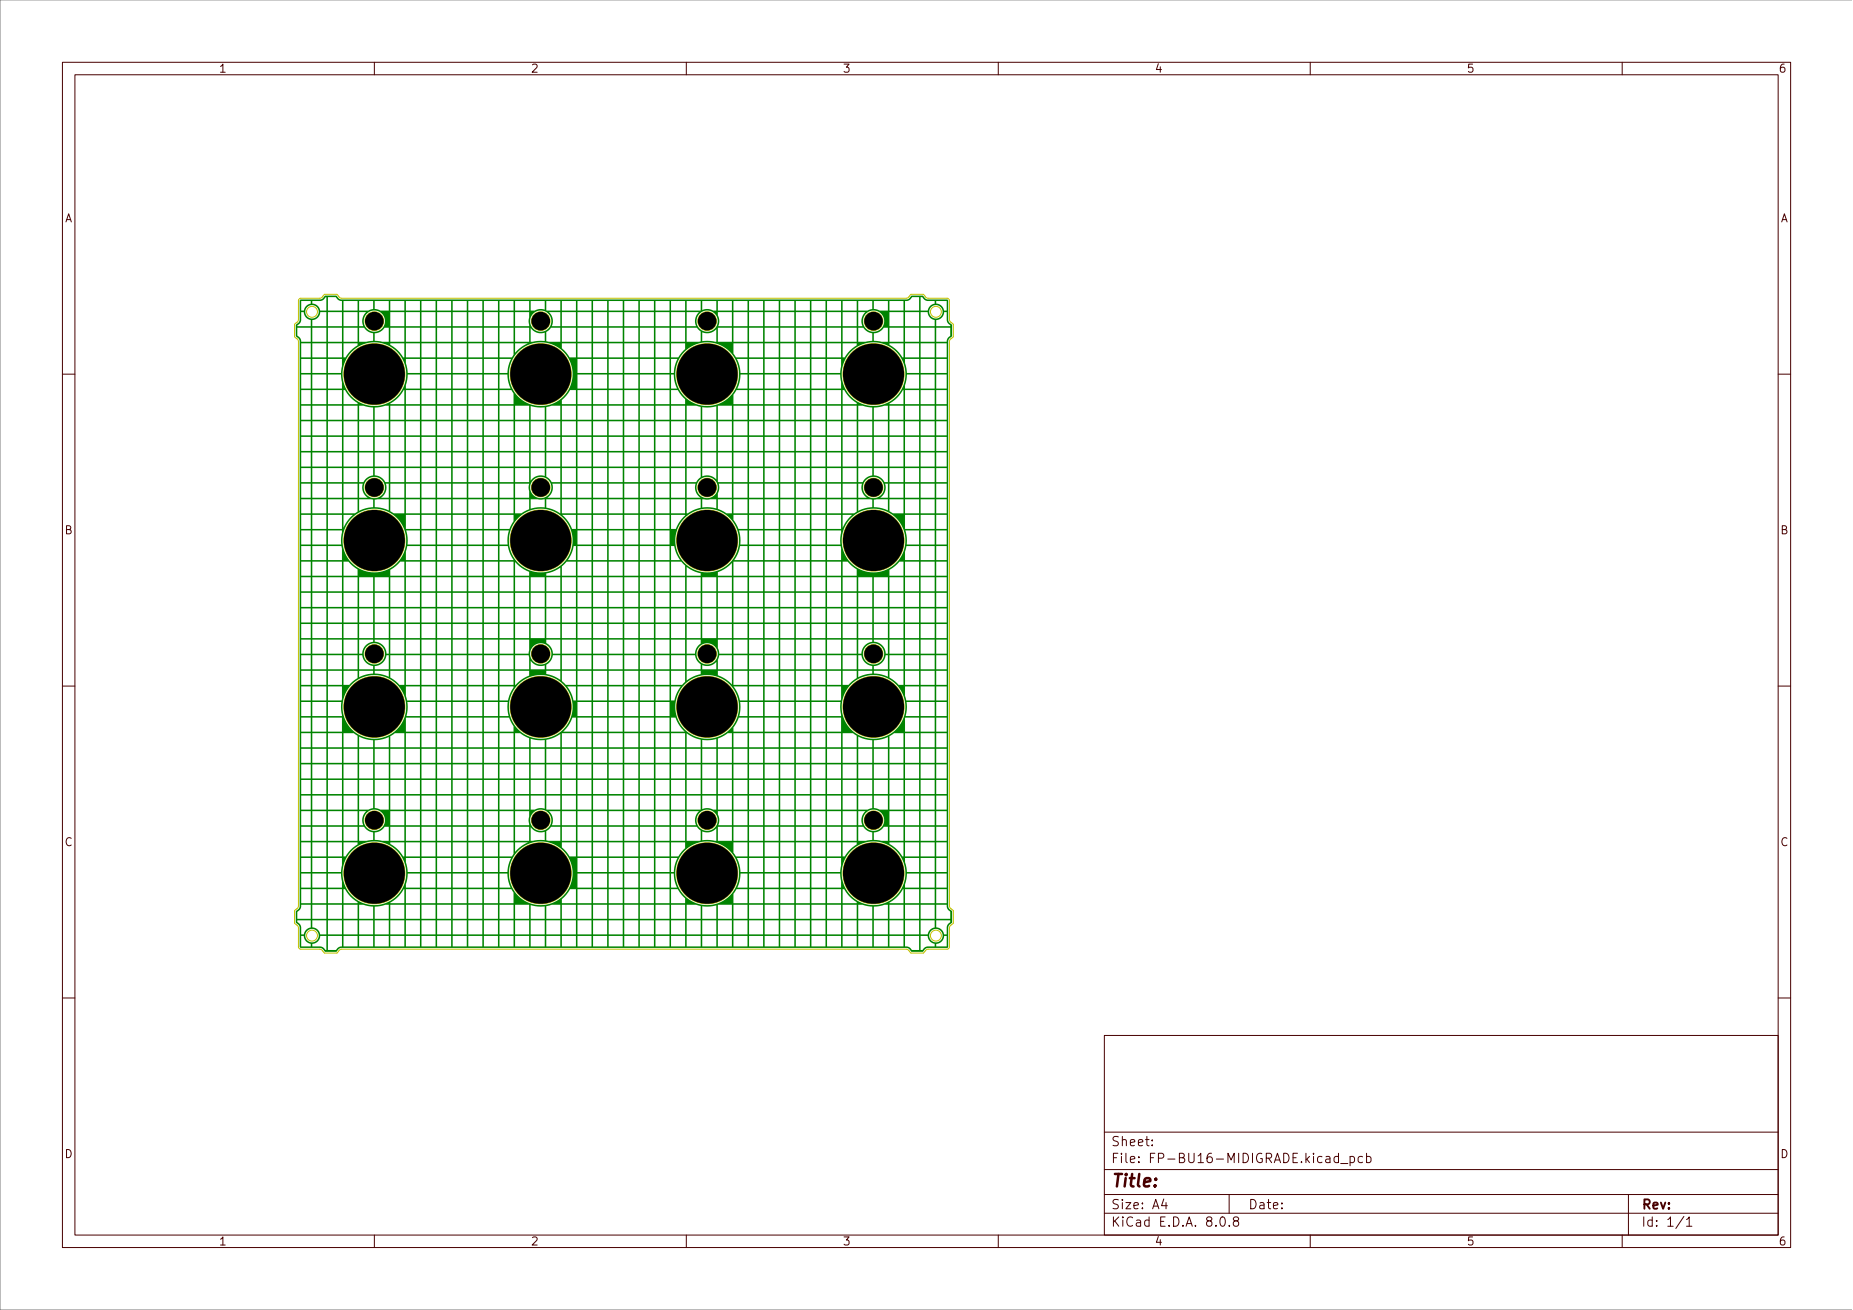
[picture p386: page 1]
