intechstudio/grid/Preview/Electrical/FP-BU16-MIDIGRADE_PCB_Top.pdf

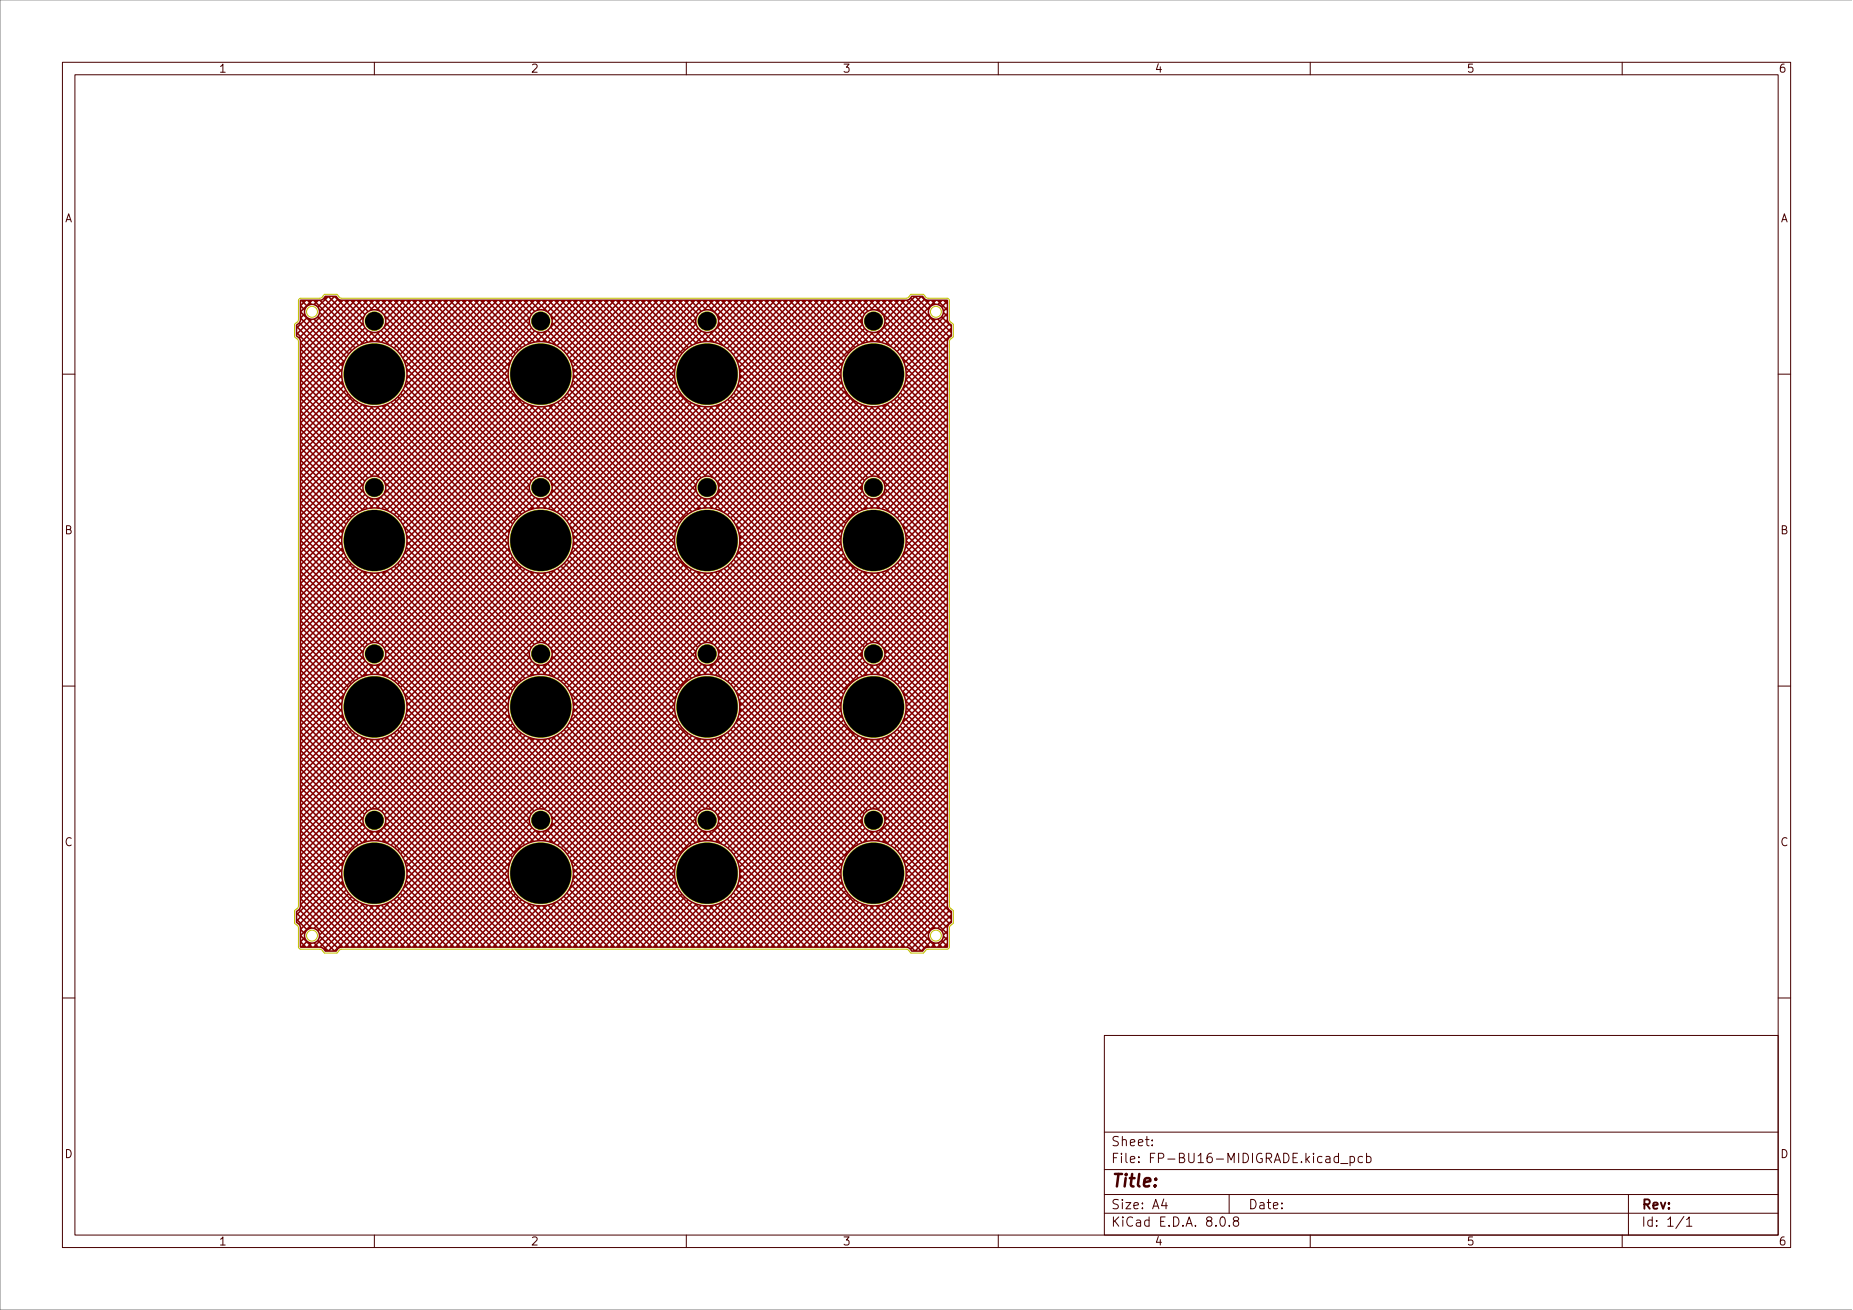
[picture p387: page 1]
