intechstudio/grid/Preview/Electrical/FP-BU16_PCB_Bottom.pdf

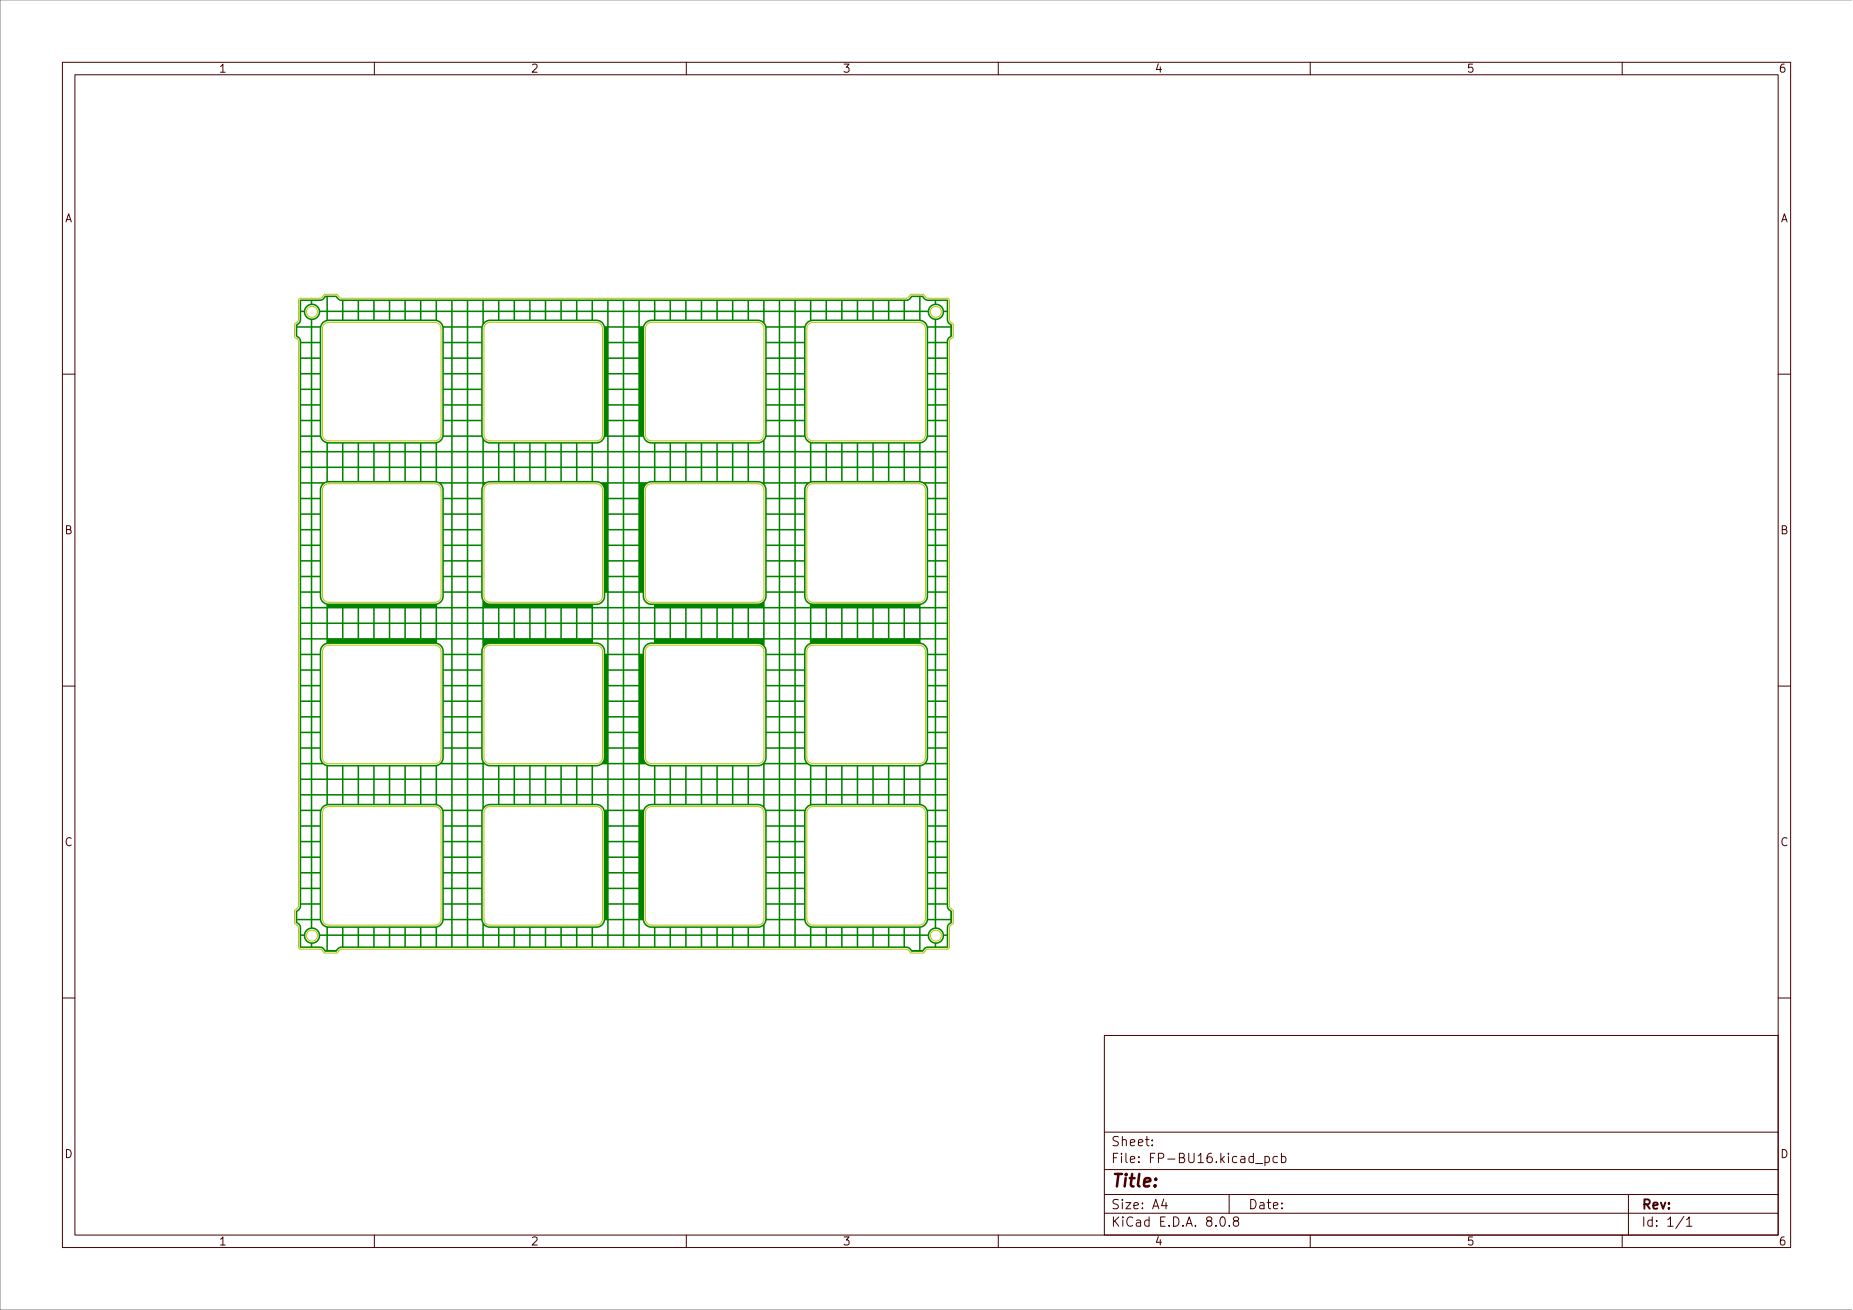
[picture p388: page 1]
