intechstudio/grid/Preview/Electrical/FP-BU16_PCB_Top.pdf

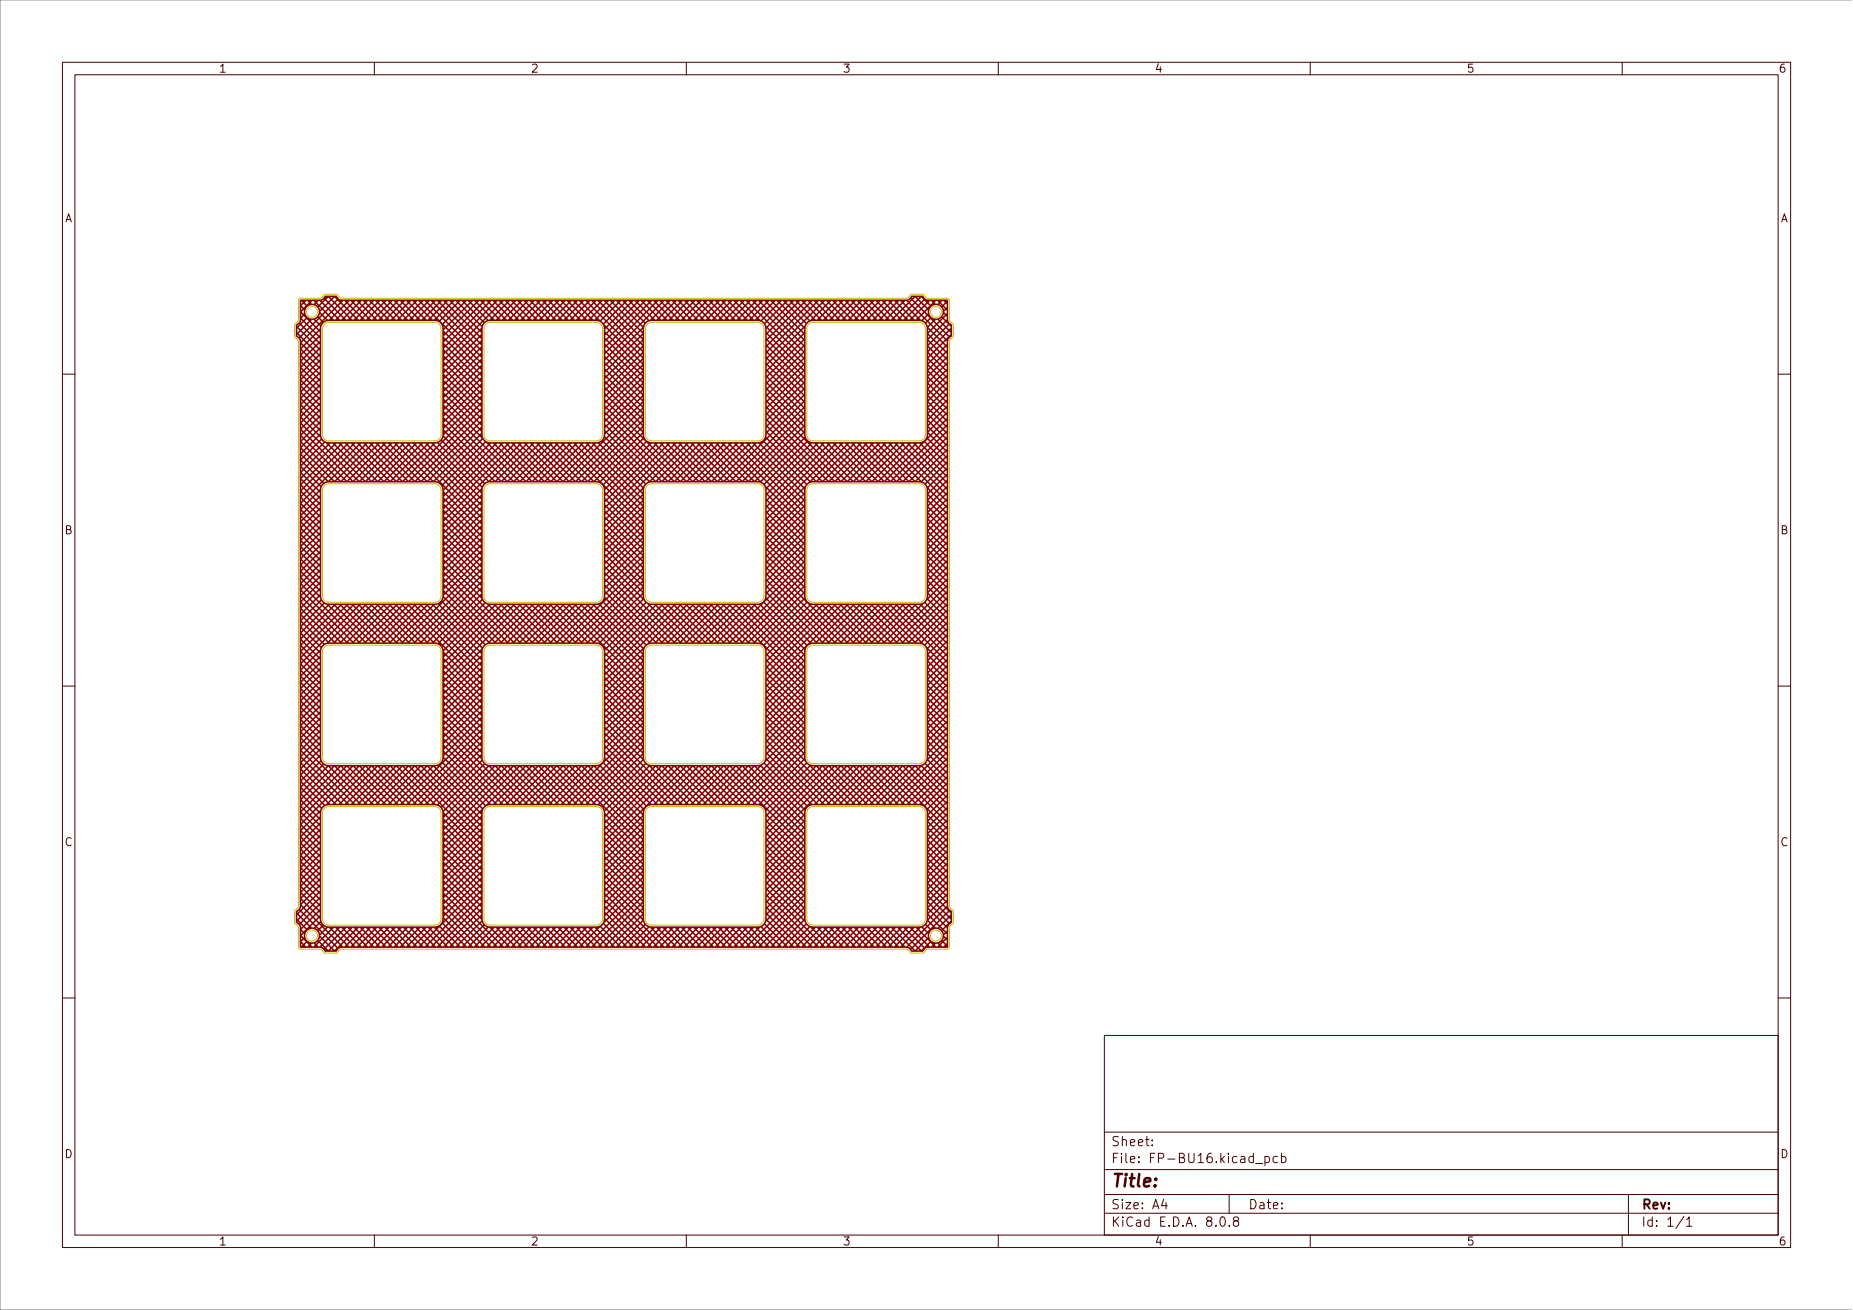
[picture p389: page 1]
