intechstudio/grid/Preview/Electrical/FP-EF44_PCB_Bottom.pdf

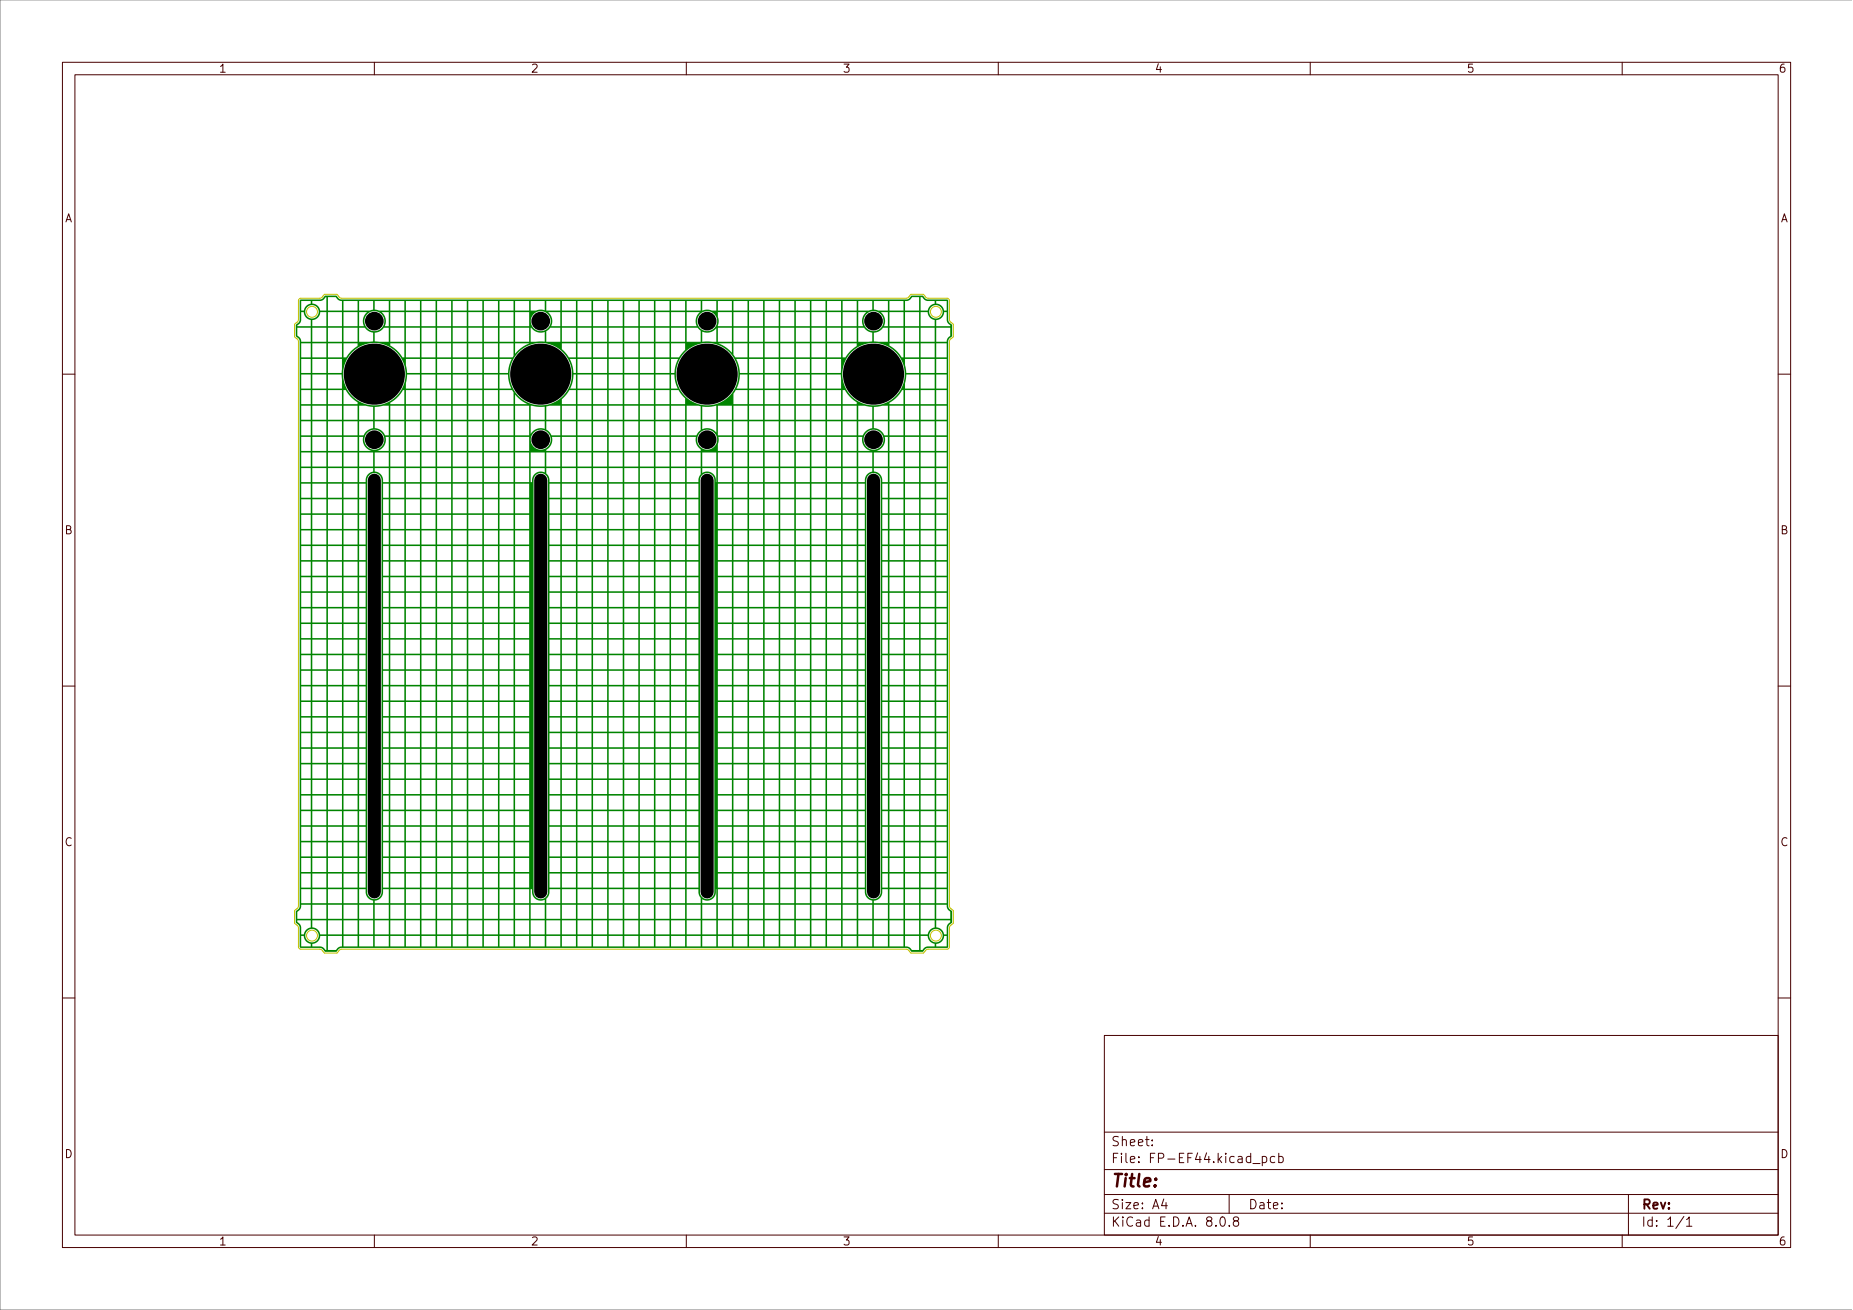
[picture p390: page 1]
