intechstudio/grid/Preview/Electrical/FP-EF44_PCB_Top.pdf

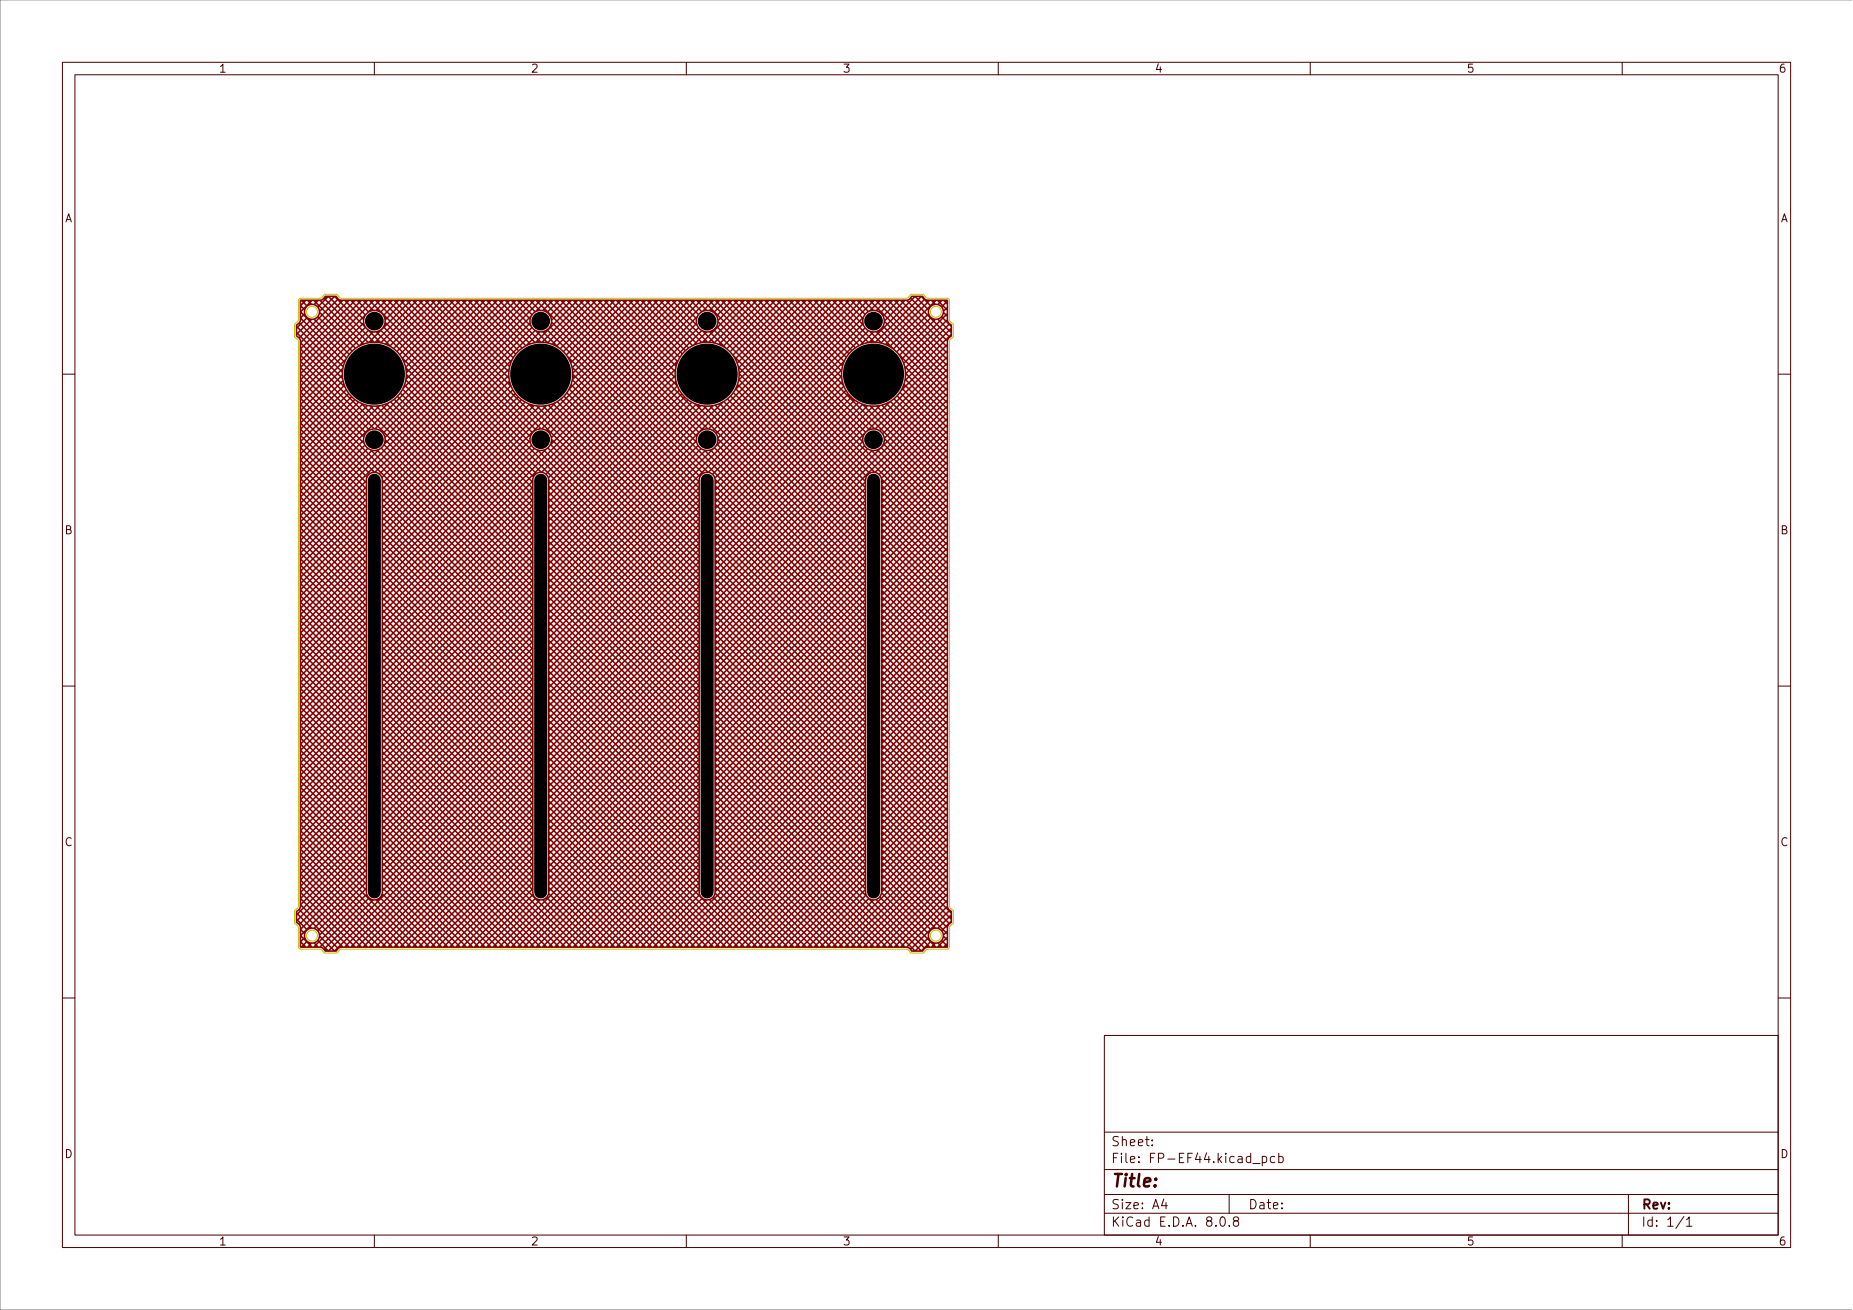
[picture p391: page 1]
