intechstudio/grid/Preview/Electrical/FP-EN16-MIDIGRADE_PCB_Bottom.pdf

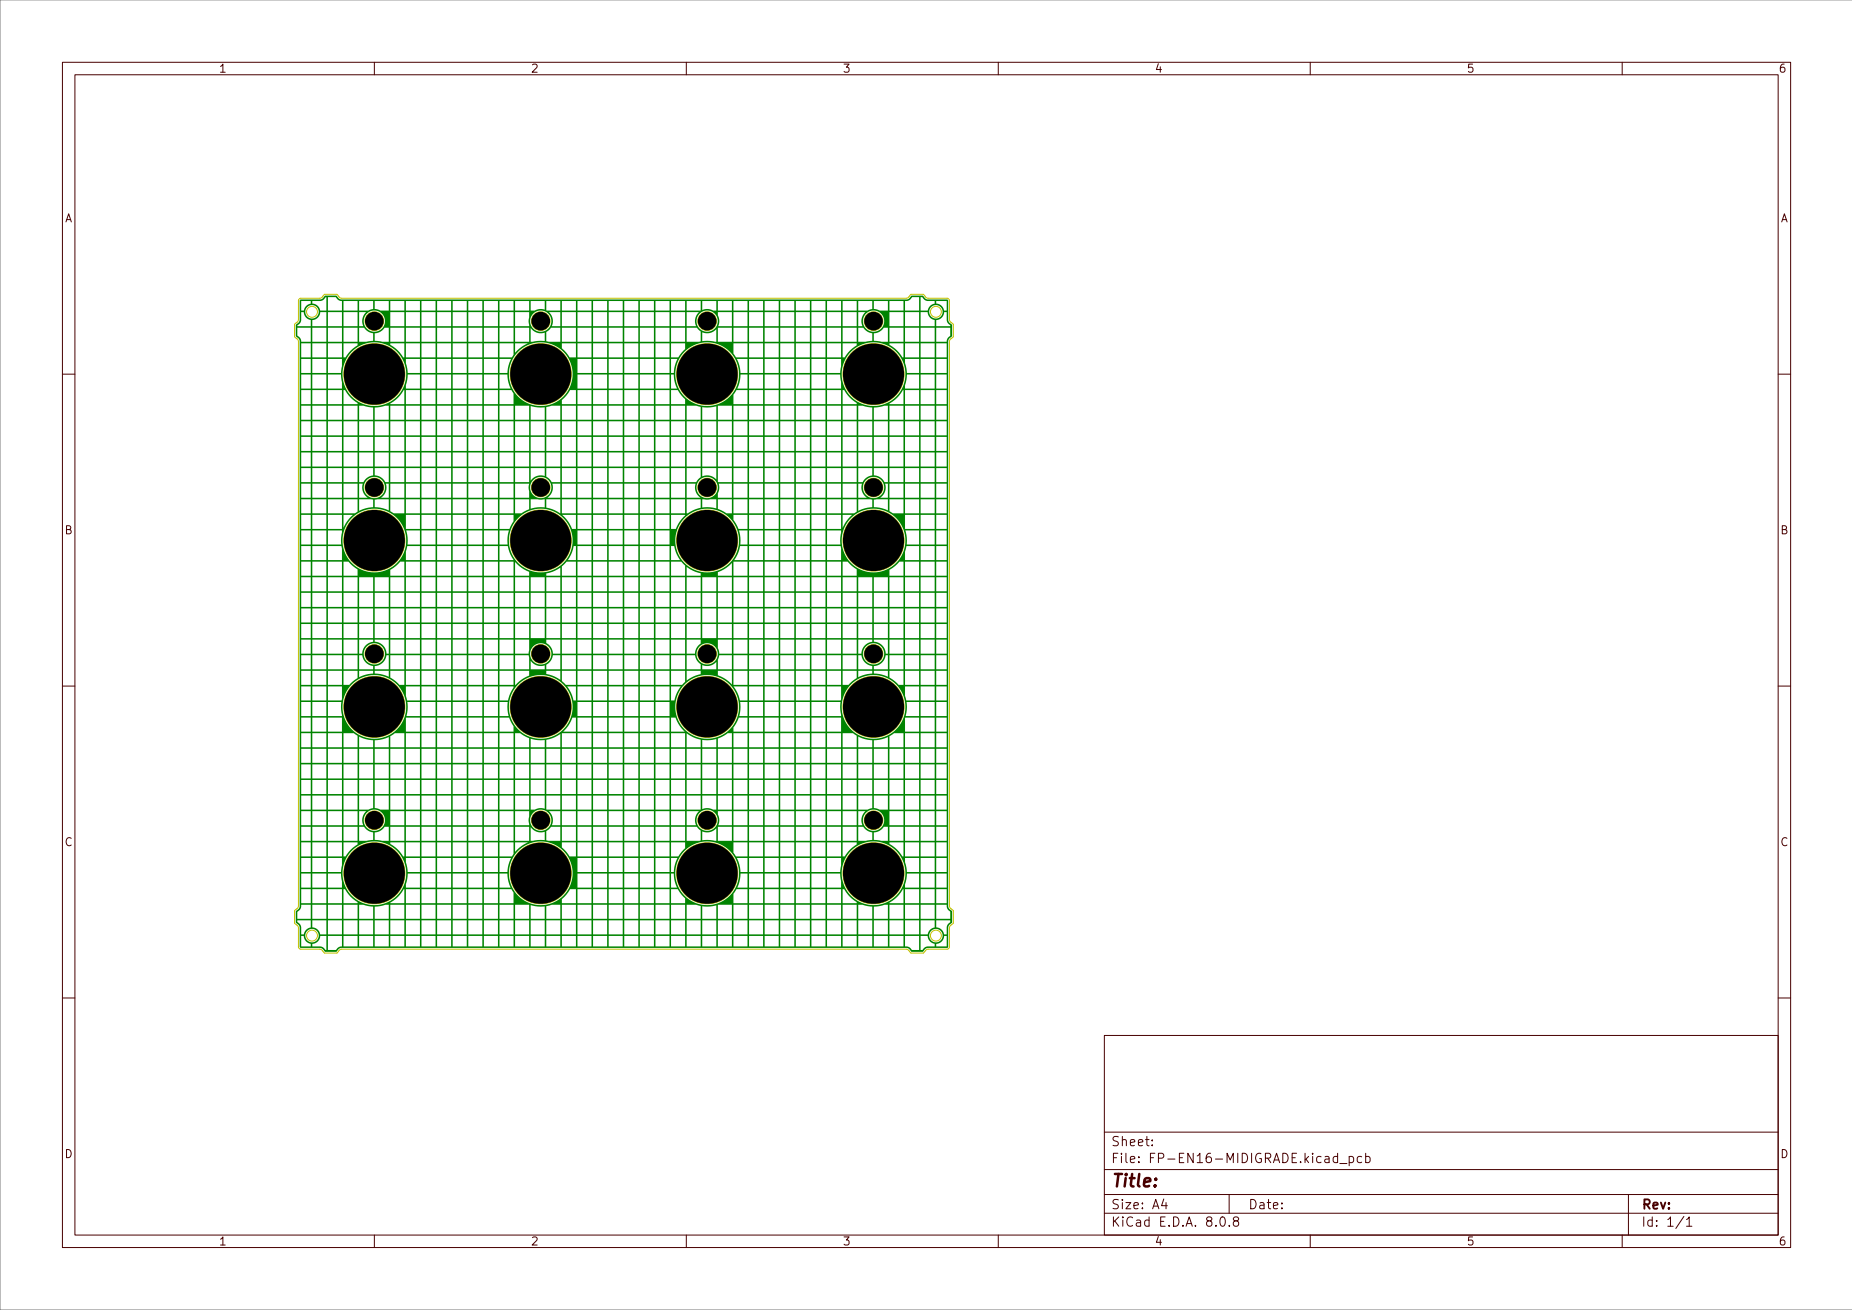
[picture p392: page 1]
